mikemag/MonkeyWiki/assets/images/Shaper_Test_1.jpg

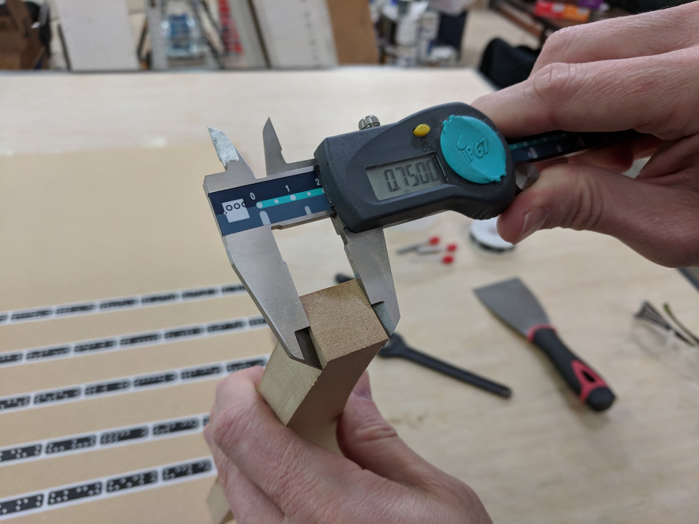
assets/images/Shaper_Test_1.jpg
