mikemag/MonkeyWiki/assets/images/Bandsaw_Setup1.JPG

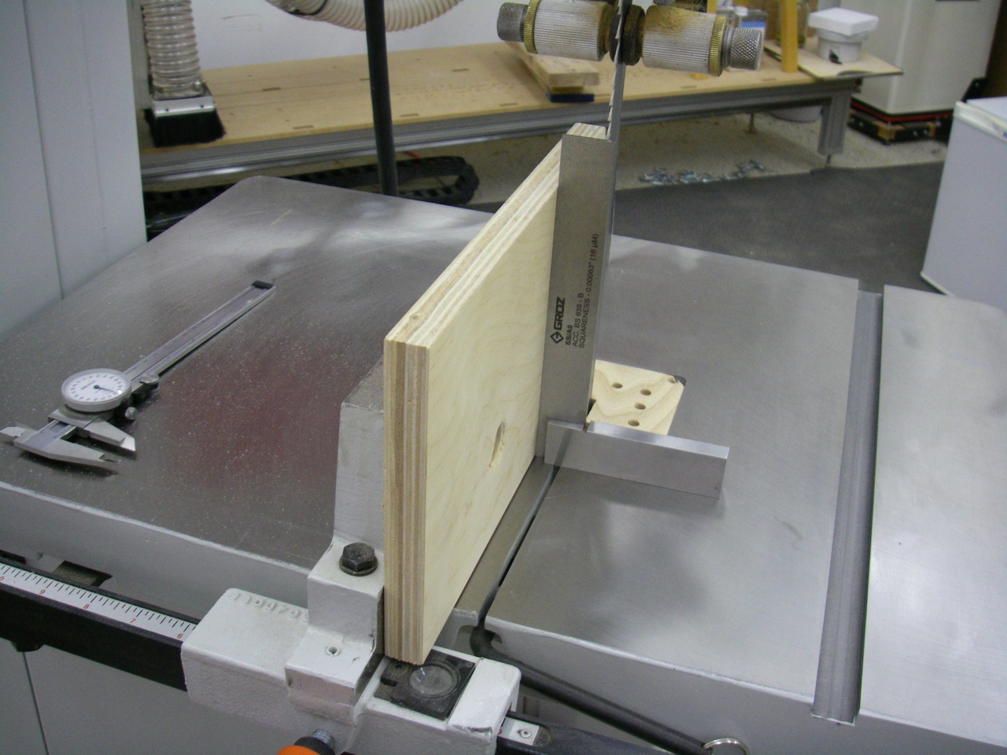
assets/images/Bandsaw_Setup1.JPG
