mikemag/MonkeyWiki/content/zh-cn/MonkeyWiki/Construction/Core_blank_construction/Core_blank_overview.md

---
dateFromWiki: "2019-05-04T15:58:57Z"
title: "芯坯概述"
aliases:
- /MonkeyWiki/Core_blank_overview/zh-cn
translatedDate: "2019-05-04T15:58:57Z"
translator: "X z"
translatorPage: "/zh-cn/MonkeyWiki/X_z"
weight: 1
---
滑雪板芯通常由垂直层压的约2cm宽的木条组成。板芯由“空白板”加工而成，它通常是矩形的，比最终板芯更长，更宽，更厚。

制作空白板是一个相当经典的木工加工，你应该这样做。如果你不熟悉木工，我已经收集了大量的[木工资源]({{< ref "MonkeyWiki/Resources/Woodworking_Resources.md" >}})来帮助你入门。 

## 概述

对于滑雪板板芯，我制造的空白板大约13.5英寸(约34cm)宽，0.4英寸(约1cm)厚，大约6-7英尺(约1.8-2.2m)长。每个空白板有18条长方向的杨木条。空白板用聚氨酯胶粘合在一起。

这个过程开始于杨木板，它长7英尺(213cm)，宽2.5英寸(6.35cm)，厚约3/4英寸(1.9cm)。这些板中的9块被粘合成7英尺长，2.5英寸宽和6.75英寸(约17cm)厚的芯坯。将该芯坯切成4个厚度为7英尺，宽6.75英寸，厚约1/2英寸(1.27cm)的切片。然后将两个切片粘接在一起，制成长7英寸，宽13.5英寸，厚0.4-0.5英寸的空白板。 

所以,9块杨木板 &rArr;1大块芯坯 &rArr; 4块横切片 &rArr; 2块空白板。我将使用术语杨木板，芯坯，切片和空白板来指代下面的各个构造阶段。

我通常尝试一次制作大约十块空白板，所以我从至少需要45块杨木板。（我通常会准备接近50块，因为有时在商店看起来像一块好的板在你的店里看起来不太好！）我发现一次制作许多空白板比一次制作一块更加容易。空白板非常稳定，可以在架子上放置很长时间而不会翘曲或开裂。

## 参阅

- [木材选择，干燥和准备]({{< ref "MonkeyWiki/Materials/Wood_selection__drying__and_prep.md" >}})
- [制作芯坯]({{< ref "MonkeyWiki/Construction/Core_blank_construction/Building_a_stack.md" >}})
- [切割芯坯]({{< ref "MonkeyWiki/Construction/Core_blank_construction/Slicing_a_stack.md" >}})
- [拼接另外一半空白板芯]({{< ref "MonkeyWiki/Construction/Core_blank_construction/Joining_the_halves_of_a_core_blank.md" >}})

## 待办事项

- 绘制从杨木板到空白板的进展。曾经在原有的HMS网站上有一个...可能重新做一下，让它看起来不那么丑。
- 每个阶段的图片，每个阶段只有一张。
