mikemag/MonkeyWiki/content/zh-cn/MonkeyWiki/Construction/Finishing/Overview_of_cleanup_and_finishing.md

---
dateFromWiki: "2019-04-11T05:45:21Z"
title: "清理和精加工概述"
gallery: true
aliases:
- /MonkeyWiki/Overview_of_cleanup_and_finishing/zh-cn
translatedDate: "2019-04-11T05:45:21Z"
translator: "X z"
translatorPage: "/zh-cn/MonkeyWiki/X_z"
weight: 1
---
{{< img src="images/Board_Trimmed.JPG" caption="_滑雪板边缘修剪和清理_" >}}在滑雪板退出压力机之后，我们仍然需要做很多清理工作才能真正看起来像滑雪板。

## 修剪边角料

第一步是修剪边角料，这是滑雪板边缘以外的多余材料。这包括额外的玻璃纤维，固化的环氧树脂，橡胶，顶片，板头/板尾垫片和边墙材料。我首先使用带锯从滑雪板的有效边刃移除边角料。这也可以通过允许带锯刀片压靠金属滑雪板边缘来轻松完成。也可以使用带锯从板头和板尾移除边角料，但我选择使用带有研磨钻头的曲线锯修剪这部分。对我来说，更容易将滑雪板稳定地放在工作台上并小心地围绕更紧密的板头和板尾半径引导曲线锯，而不是将整个滑雪板围绕带锯刀片摆动。 

@TODO: 获取我使用的刀片信息。

{{< gallery  caption="边角料清理" >}}
{{< gallery-item src="images/FlashCleanup1.JPG" caption="Remains of the nose and tail flash." >}}
{{< gallery-item src="images/FlashCleanup2.JPG" caption="Remains of the flash from along the edge of a snowboard." >}}
{{< /gallery >}}

## 清理边刃

现在层压板开始看起来更像滑雪板，但边缘仍然非常粗糙。两种工具都会留有粗糙的边缘，并且在某些地方仍然会有一层薄薄的多余材料，通常是PTEX边墙或板头/板尾垫片。沿着板的整个周边使用具有60目砂磨盘的4英寸角磨机。将多余的材料小心地磨掉，并将边缘全部暴露出来。然后我切换到120目砂磨盘并完全清理板尾和板尾。这将是滑雪板这部分的最终处理。这是一个非常微妙的过程。使用角磨机和60目或120目砂磨盘可以在极短的时间内对板边缘造成大量损坏！

使用角磨机进行打磨时，不要使边缘过热至关重要。我在这部分完成之前，不断移动到另一个区域。我像往常一样用干净的水喷洒，并用手检查边缘的温度。如果你不能把手放在边缘，那就太烫了。

{{< gallery  caption="边刃清理" >}}
{{< gallery-item src="images/EdgeCleanup1.JPG" caption="The table where I cleanup the board. Snowboard vises are used to hold the board up on edge for grinding." >}}
{{< gallery-item src="images/EdgeCleanup2.JPG" caption="Laminate trimmer and angle grinder with various flap sanding discs." >}}
{{< /gallery >}}

## 板底打磨

{{< img src="images/BaseGrinder.JPG" caption="_板底磨床_" >}}接下来，滑雪板获得了第一次打磨。我从一个粗糙的80目砂带开始，快速去除多余的环氧树脂和一层薄薄的基材，然后切换到120目砂带进行最后的打磨。虽然80目砂带仍然存在，但我清理了保持板垂直于板底打磨机的有效边缘。这确保了边缘的整个长度是平滑的，甚至是板的长度。

## 斜切边墙

接下来，将板返回到施加边墙斜面的工作台上。带有倾斜底座的修边机用于沿有效边缘的长度运行齐平修剪router刨机钻头。这使得边墙成为完美的10度斜面，并且是边墙上所需的最后一点清理。如果你没有带倾斜底座的修边机，你可以用木头制作楔子并将其连接到修边机底座上以形成正确的角度。

这里的关键是缓慢移动并确保修边机的底部保持平放在板的底部。在每个端部轻松进出切口，并将可能留下的任何尖锐过渡与砂磨块混合。

{{< gallery  caption="边墙清理" >}}
{{< gallery-item src="images/Trimmer1.jpg" caption="Laminate trimmer with a tilt base." >}}
{{< gallery-item src="images/Trimmer2.jpg" caption="Straight cutter with bearing on top." >}}
{{< gallery-item src="images/Trimmer3.jpg" caption="Example of how to apply the trimmer to cleaning up sidewalls. The edge should be completely exposed and smooth. The bearing rests on the edge, and the cutter starts about a half millimeter past the edge. The board is upside down and the trimmer rests on the base." >}}
{{< /gallery >}}

## 开孔

最后，固定器螺孔会被钻出。我通过使用两个小磁铁找到嵌件，这两个小磁铁将粘在两个3/16英寸钢球轴承上，这些轴承在准备铺设时放入导向嵌件中。导向嵌件沿着板的长度居中，距离第一组嵌件4cm。使用指南我可以快速标记嵌件位于滑雪板表面下方的位置，然后分两步钻出。第一步是使用1/8英寸钻头打开孔位，然后使用45度沉头钻露出整个螺孔并留下一个漂亮的斜面。沉头钻将在螺孔中自动居中。使钻头垂直于板，以确保圆孔均匀。使用M6螺孔清洁螺纹，并通过手动将固定器螺丝向下钻入每个螺孔进行检查。如果螺丝不能轻易地一直钻到底部，则再次使用龙头直到它完成。
 
使用一对小镊子去除在钻孔和反沉没过程中被推下的聚酯薄膜嵌件帽。在攻丝之前和拧紧螺钉之前，用压缩空气清除螺孔。
 
使用M6水龙头轻松一下。你不希望跨越它并破坏插入中的线程。你也不想把它跑得太远并推出插入物的底部，这会在滑雪板的底部留下一个凹坑。大多数水龙头都有一个点。最好将其研磨成平底，如下图所示。

{{< gallery  caption="螺孔清理" >}}
{{< gallery-item src="images/CleanupInserts1.JPG" caption="Insert finding guide, aligned with magnets." >}}
{{< gallery-item src="images/CleanupInserts2.JPG" caption="Insert finding guide, aligned with magnets." >}}
{{< gallery-item src="images/CleanupInserts3.JPG" caption="Insert finding guide, aligned with magnets." >}}
{{< gallery-item src="images/CleanupInserts4.JPG" caption="Inserts drilled with a small drill bit." >}}
{{< gallery-item src="images/CleanupInserts5.JPG" caption="Inserts exposed with the counter sink." >}}
{{< gallery-item src="images/CleanupInserts6.JPG" caption="Here you can see bits of epoxy and glass forced down into the inserts after drilling with the counter sink." >}}
{{< gallery-item src="images/CleanupInserts7.JPG" caption="Cleaning up the threads of the inserts with a M6 tap." >}}
{{< gallery-item src="images/CleanupInserts8.JPG" caption="Testing the insert threads with a binding screw." >}}
{{< /gallery >}}
