mikemag/MonkeyWiki/content/zh-cn/MonkeyWiki/Equipment/Snowboard-specific_tools/Base_grinder.md

---
dateFromWiki: "2019-04-04T08:56:10Z"
title: "板底磨床"
gallery: true
aliases:
- /MonkeyWiki/Base_grinder/zh-cn
translatedDate: "2019-04-04T08:56:10Z"
translator: "X z"
translatorPage: "/zh-cn/MonkeyWiki/X_z"
---
{{< img src="images/Grinder10.JPG" caption="_Fontaine 1404 Base Grinder._" >}}我使用Fontaine 1404板底磨床，由Wintersteiger出售，型号为SNB 55。它使用14“x 59”(35.56cm x 149.86cm)的皮带。电机是一个4马力的Leeson，它有一个带有可调式喷雾器的小型240v水泵。它就像任何普通的带式砂光机一样，带有驱动轮和从动件，以及用于调节跟踪的旋钮。驱动轮是一种坚硬的橡胶，它会变形一点，很适合用不完美的底座完成底板。在中心附近有一个压板（在这台机器上是可选的），这种压板非常平坦，可以使基座真实。在集水盆和皮带之间有一个布料过滤器，用于将金属和基材保持在泵外。

没有自动进给，虽然机器设计为添加了一个。

没有库存边缘指南，但是一个伙伴和我用一些废铝建造了一个快速贫民窟。这很难看，但它允许我在一个可调节的位置垂直于皮带保持板边缘，所以我不会在早期的皮带上磨损一条线。 

## 耗材

我在这里得到了所有的磨床用品[SVST](http://www.svst.com).甚至还有Fontaine更换零件以适合我的机器。 

我通常使用氧化铝或锆石带。我使用80目从底部去除多余的环氧树脂，并快速通过边墙。然后，我用120目完成。我保留了一些旧皮带作为最后的整理通行证，因为它们不那么尖锐，往往会留下更好的表面。

## 冷却液

我在水中使用“研磨冷却剂”，有时称为“切削液”或“乳液”。我使用的品牌是SVST的Kool Kut Ski Grinding Coolant，它不仅可以帮助皮带切割更好，还可以防止机器生锈。这就是让水看起来像防冻剂的原因，但不要搞错：它不是防冻剂。研磨冷却剂几乎无毒，这非常重要，因为无论如何，当你研磨板时，你最终都会被细雾覆盖。我使用的冷却剂似乎对我个人没有任何影响，但是...我只是用一些护目镜将它从我的眼睛中取出，然后洗掉。 它似乎对我的草坪没有影响。 它上面的MSDS是非常无害的，表明有轻微的刺激性和更多。

冷却剂被保持在一个简单的塑料箱中，盖子被切开，以便为电源和泵的供应管路留出空间。这让我可以混合一些冷却剂，并在研磨之间保持几周无尘。 

我确实发现，如果放置冷却剂，如果放置时间超过几个月就会变成霉菌，所以我尽量不在机器中留下冷却液，除非我相信我会在几周内磨一块板。 

## 清理

使用后清理板底研磨机非常重要。你不希望机器在基材绒毛和边缘锉中结块，因为它会促使机器生锈。这就是标准花园软管喷嘴的用途：你可以彻底地将内部软管从内部软管，然后使用一些商店毛巾将其中的大部分干燥。

## 电气

该机器在240V时吸收约21个起动放大器，因此我将它安装在30A断路器上。应该有一个接触器或继电器开关来打开和关闭连接到设备，但它很久以前就爆炸了。我一直把它连接起来，我用断路器作为开关。这就是为什么你在电机顶部看到一个带有磁带而不是开关的小盒子。有一天，当它真的开始烦我时，我会绕过去实际修复它。 

{{< gallery  caption="Fontaine 1404 Base Grinder" >}}
{{< gallery-item src="images/Grinder1.JPG" caption="Electrical plate on the motor of the Fontaine 1404 base grinder." >}}
{{< gallery-item src="images/Grinder2.JPG" caption="Motor on the base grinder." >}}
{{< gallery-item src="images/Grinder3.JPG" caption="Base grinder from the back side. Belts are kept in the base." >}}
{{< gallery-item src="images/Grinder4.JPG" caption="Tracking adjustment on the base grinder, back side." >}}
{{< gallery-item src="images/Grinder5.JPG" caption="Nameplate and serial number on the base grinder." >}}
{{< gallery-item src="images/Grinder6.JPG" caption="Base grinder, front view with doors open." >}}
{{< gallery-item src="images/Grinder7.JPG" caption="Base grinder, front view with doors open, closer look at the mechanism." >}}
{{< gallery-item src="images/Grinder8.JPG" caption="Spray head, inside the grinder on the lower left side (when looking from the front.) Sprays upwards to coat the belt." >}}
{{< gallery-item src="images/Grinder9.JPG" caption="Base grinder, doors open, belt on and tensioned." >}}
{{< gallery-item src="images/Grinder10.JPG" caption="Fontaine 1404 base grinder. Front view, doors closed, belt on and tensioned." >}}
{{< gallery-item src="images/Grinder11.JPG" caption="Ghetto edge guide, retracted position." >}}
{{< gallery-item src="images/Grinder12.JPG" caption="Ghetto edge guide, extended position." >}}
{{< gallery-item src="images/Grinder13.JPG" caption="Coolant tank, empty, showing pump and filter." >}}
{{< gallery-item src="images/BaseGrinder.JPG" caption="Base grinder with various belts." >}}
{{< /gallery >}}
