mikemag/MonkeyWiki/notes.md

# Random Notes

## Update the site:
```
rsync -e "/usr/bin/ssh" --bwlimit=2000 -av public/ uuu@hhh.dreamhost.com:/home/uuu/happymonkeysnowboards.com/
```

## .htaccess

* Pure gold: https://htaccess.madewithlove.com/
* Docs and flags: https://httpd.apache.org/docs/current/mod/mod_rewrite.html

## Hugo

* https://gohugo.io/documentation/
* https://github.com/alex-shpak/hugo-book
