mikemag/MonkeyWiki/content/en/MonkeyWiki/_index.md

---
gallery: true
bookCollapseSection: false
aliases:
- /MonkeyWiki/Main_Page
- /MonkeyWiki/Main_Page/en
description: "How I built snowboards at Happy Monkey Snowboards. Construction techniques, equipment, materials, etc."
title: Monkey Wiki
---
{{< img src="images/Board_2018.jpg" width=300px caption="_Completed board from Winter 2018. Wood veneer topsheet with highly figured Bubinga, English Sycamore, and Ebony. 164cm._" >}} 
This site provides information on exactly how I built snowboards so that others may learn from it. 
The information here is based on my experience building boards as owner of Happy Monkey Snowboards, Inc., from 2003-2010 as well as 
my continued personal building through 2018.

This will not be a comprehensive treatment of all the different ways to do this, but rather just the ways that I have 
personally done it which worked well for me. For alternatives see [SkiBuilders.com](http://www.skibuilders.com), where they have collected 
detailed how-to’s on how they and others build skis and snowboards, and host a great forum with even more information on alternatives.

Enjoy,

[Mike Magruder (a.k.a Head Monkey)]({{< ref "MonkeyWiki/Head_Monkey.md" >}})

## Donate

You can help offset the server costs for running MonkeyWiki with a small donation. 



## Contents 
- [Construction Overview]({{< ref "MonkeyWiki/Construction" >}})
- [Equipment Overview]({{< ref "MonkeyWiki/Equipment" >}})
- [Materials Overview]({{< ref "MonkeyWiki/Materials" >}})
- [Resources Overview]({{< ref "MonkeyWiki/Resources" >}})
- [About]({{< ref "MonkeyWiki/About.md" >}})

## What about skis? 
I've built one pair of skis, and they turned out great. You’ll find that ski and snowboard construction are *amazingly* similar. 
You can use everything here to build either, even though it all refers to snowboards. It’s okay :)

## Status 
There are a few placeholders where I've left just raw notes, but otherwise the articles that are here now are technically 
correct and up-to-date.
