mikemag/MonkeyWiki/content/en/MonkeyWiki/Equipment/_index.md

---
title: "Equipment"
aliases:
- /MonkeyWiki/Equipment_Overview
- /MonkeyWiki/Equipment_Overview/en
weight: 2
bookCollapseSection: true
---
The following articles cover the equipment needed to build a snowboard. Some of these can be bought from your average 
hardware store, and some have to be built by you. Some are absolutely required, while others (like a CNC machine) are 
pretty optional. Which ones you really need will depend on the way you chose to build boards and the raw materials you 
can get. For instance, if you buy core blanks from someone then you might not really need most of the larger woodworking 
tools. If you’re willing to bend the edges completely by hand then you won’t need a specialized edge bender, etc.

*Note: this isn't a complete list of tools, just the ones I've taken some time to write about here.*

- CNC
  - [CNC Router]({{< ref "MonkeyWiki/Equipment/CNC/CNC_Router.md" >}})
  - [Do you need a CNC machine?]({{< ref "MonkeyWiki/Equipment/CNC/Do_you_need_a_CNC_machine_.md" >}})
  - [CNC machines: build or buy?]({{< ref "MonkeyWiki/Equipment/CNC/CNC_machines__build_or_buy_.md" >}})
  - [Shaper Origin]({{< ref "MonkeyWiki/Equipment/CNC/Shaper_Origin.md" >}})
  - CAD/CAM Software
    - [Fusion 360]({{< ref "MonkeyWiki/Equipment/CNC/CAD_CAM_Software/Fusion_360.md" >}})
    - [MonkeyCAM]({{< ref "MonkeyWiki/Equipment/CNC/CAD_CAM_Software/MonkeyCAM.md" >}})
    - [snoCAD-X]({{< ref "MonkeyWiki/Equipment/CNC/CAD_CAM_Software/SnoCAD-X.md" >}})
- Snowboard press
  - [Monkey Press Construction]({{< ref "MonkeyWiki/Equipment/Snowboard_press/Monkey_Press_Construction.md" >}})
  - [Press heat control and thermocouples]({{< ref "MonkeyWiki/Equipment/Snowboard_press/Press_heat_control_and_thermocouples.md" >}})
  - [Molds and cassettes]({{< ref "MonkeyWiki/Equipment/Snowboard_press/Molds_and_cassettes.md" >}})
- Snowboard-specific tools
  - [Deflection Testing Jig]({{< ref "MonkeyWiki/Equipment/Snowboard-specific_tools/Deflection_Testing_Jig.md" >}})
  - [Edge Benders]({{< ref "MonkeyWiki/Equipment/Snowboard-specific_tools/Edge_Benders.md" >}})
  - [Base grinder]({{< ref "MonkeyWiki/Equipment/Snowboard-specific_tools/Base_grinder.md" >}})
- Small tools
  - [Air Shears]({{< ref "MonkeyWiki/Equipment/Small_tools/Air_Shears.md" >}})
  - [Feather Board]({{< ref "MonkeyWiki/Equipment/Small_tools/Feather_Board.md" >}})
  - [Four-way Clamps]({{< ref "MonkeyWiki/Equipment/Small_tools/Four-way_Clamps.md" >}})
  - [Hand Scraper]({{< ref "MonkeyWiki/Equipment/Small_tools/Hand_Scraper.md" >}})
  - [Pipe Clamps]({{< ref "MonkeyWiki/Equipment/Small_tools/Pipe_Clamps.md" >}})
  - [Routers and laminate trimmers]({{< ref "MonkeyWiki/Equipment/Small_tools/Routers_and_laminate_trimmers.md" >}})
  - [Router Bits]({{< ref "MonkeyWiki/Equipment/Small_tools/Router_Bits.md" >}})
- Larger tools
  - [HVLP Sprayer]({{< ref "MonkeyWiki/Equipment/Larger_tools/HVLP_Sprayer.md" >}})
