mikemag/MonkeyWiki/content/en/MonkeyWiki/Equipment/CNC/CNC_Router.md

---
dateFromWiki: "2019-02-03T02:37:15Z"
title: "CNC Router"
gallery: true
aliases:
- /MonkeyWiki/CNC_Router
- /MonkeyWiki/CNC_Router/en
weight: 1
---
In 2003, I built a CNC router to allow me to accurately cut snowboard cores, bases, and mold parts. The cutting area is 2′ x 7’1″, with 5″ of travel in the Z axis (you end up with less due to the length of the cutter, though.) The frame is made of structural aluminum. Each axis moves on steel linear slides, and the plates that make up the mount for the Z axis are 3/4″ aluminum. There are 3 stepper motors powered and controlled by a controller in the grey box above the machine.
 
The controller receives the program, or manual commands, from a small dedicated computer on a shelf nearby. The machine is programmed with industry standard “G-codes." These are generated from either a commercial CAD/CAM system, or from my own snowboard-specific CAM system called MonkeyCAM.
 
I had originally hoped it might be suitable for cutting aluminum as well, but it’s really only good for wood and plastics, which is just fine since I primarily use it for snowboard construction and other random woodworking projects.

{{< gallery  caption="Happy Monkey CNC Machine" >}}
{{< gallery-item src="images/CNC1.JPG" caption="Overview of the CNC machine. The cutting area is 85\" x 24\" x 5\"." >}}
{{< gallery-item src="images/CNC2.JPG" caption="Head and gantry of the CNC machine with snowboard press in the background." >}}
{{< gallery-item src="images/CNC_Head1.jpg" caption="Porter Cable router in a CNC machine." >}}
{{< gallery-item src="images/CNC3.JPG" caption="Head of the CNC machine from behind." >}}
{{< gallery-item src="images/CNC4.JPG" caption="Back of the CNC head showing Y and Z axis mechanisms." >}}
{{< gallery-item src="images/CNC5.JPG" caption="Better shot of the Y axis motor, gears, and rack." >}}
{{< gallery-item src="images/CNC6.JPG" caption="Control box for the CNC machine." >}}
{{< gallery-item src="images/CNC7.JPG" caption="Inside the control box for the CNC machine." >}}
{{< /gallery >}}

## CNC Resources 
- [Machine Tool Camp](http://machinetoolcamp.com/) – I started with plans for a 4’x8’ machine from here and modified them to build my machine.
- [CNC Zone](http://www.cnczone.com/) – The single best forum for home-built CNC machines.
