mikemag/MonkeyWiki/content/zh-cn/MonkeyWiki/Equipment/CNC/CNC_Router.md

---
dateFromWiki: "2019-04-03T13:18:43Z"
title: "CNC 雕刻机"
gallery: true
aliases:
- /MonkeyWiki/CNC_Router/zh-cn
translatedDate: "2019-04-03T13:18:43Z"
translator: "X z"
translatorPage: "/zh-cn/MonkeyWiki/X_z"
weight: 1
---
在2003年，我建造了一台CNC雕刻机，可以准确地切割滑雪板芯，底板和模具零件。切割区域为2英尺x 7英尺1英寸，在Z轴上行程为5英寸（尽管由于切割器的长度，最终会减少。）框架由结构铝制成。每个轴在钢制线性滑块上移动，构成Z轴安装的板为3/4“铝。3个步进电机是由机器上方的灰色控制箱中的控制器供电和控制。

控制器从附近架子上的小型专用计算机接收程序或手动命令。该机器采用行业标准“G-code”编程。这些是从商业CAD/CAM系统或我自己的滑雪板专用CAM系统MonkeyCAM生成的。
 
我原本希望它也适合切割铝，但它实际上只适用于木材和塑料，这很好，因为我主要用它来滑雪板制造和其他随机木工项目。

{{< gallery  caption="Happy Monkey CNC机器" >}}
{{< gallery-item src="images/CNC1.JPG" caption="Overview of the CNC machine. The cutting area is 85\" x 24\" x 5\"." >}}
{{< gallery-item src="images/CNC2.JPG" caption="Head and gantry of the CNC machine with snowboard press in the background." >}}
{{< gallery-item src="images/CNC_Head1.jpg" caption="Porter Cable router in a CNC machine." >}}
{{< gallery-item src="images/CNC3.JPG" caption="Head of the CNC machine from behind." >}}
{{< gallery-item src="images/CNC4.JPG" caption="Back of the CNC head showing Y and Z axis mechanisms." >}}
{{< gallery-item src="images/CNC5.JPG" caption="Better shot of the Y axis motor, gears, and rack." >}}
{{< gallery-item src="images/CNC6.JPG" caption="Control box for the CNC machine." >}}
{{< gallery-item src="images/CNC7.JPG" caption="Inside the control box for the CNC machine." >}}
{{< /gallery >}}

## CNC 资源

- [Machine Tool Camp](http://machinetoolcamp.com/) – 我从这里开始计划4英尺x8英尺机器并修改它们以构建我的机器。
- [CNC Zone](http://www.cnczone.com/) – 自制数控机床的最佳论坛。
