mikemag/MonkeyWiki/content/zh-cn/MonkeyWiki/Equipment/Small_tools/Feather_Board.md

---
dateFromWiki: "2019-04-04T01:54:05Z"
title: "羽毛板"
gallery: true
aliases:
- /MonkeyWiki/Feather_Board/zh-cn
translatedDate: "2019-04-04T01:54:05Z"
translator: "X z"
translatorPage: "/zh-cn/MonkeyWiki/X_z"
---
{{< img src="images/Fingers.JPG" caption="_在带锯上的羽毛板_" >}}羽毛板是一种用于帮助抵抗带锯或台锯导轨的工具。它们可以进行调整，以便在通过锯片时，板必须将挡板的两端推开，从而对挡板施加一点压力。

使用购买的硬件（旋钮和插槽插件）可以将羽毛板制作成你需要的任何尺寸或形状，或者你可以在当地的木工车间预先制作羽毛板。
