mikemag/MonkeyWiki/content/zh-cn/MonkeyWiki/Equipment/Small_tools/Four-way_Clamps.md

---
dateFromWiki: "2019-04-02T15:20:16Z"
title: "四向夹具"
gallery: true
aliases:
- /MonkeyWiki/Four-way_Clamps/zh-cn
translatedDate: "2019-04-02T15:20:16Z"
translator: "X z"
translatorPage: "/zh-cn/MonkeyWiki/X_z"
---
通过使用像这里图中所示的简单“四向”夹具，可以更容易地夹紧一半的芯坯或类似物。我使用[WoodRiver夹紧系统](http://www.woodcraft.com/Product/2000321/1858/WoodRiver-Clamping-System.aspx)，可以从亚马逊或[WoodCraft](http://www.woodcraft.com/)等地方购买。你需要六到七个来夹住一个板芯，所以寻找他们的销售。

由于你提供了夹具的木材部分，因此可以使这些夹具适合你想要粘合的任何尺寸的面板。然而，夹子不会完全闭合，并且它们通常不会闭合得足够远以接触相当薄的普通芯坯的表面。你可能需要使用垫片来弥补额外的厚度。我用几块四分之一英寸的硬纸板和打包带来防止胶水粘在它们上面。

这些最大开口宽度为27英寸，最小开口宽度为8 3/4英寸。 当然，这可以用不同长度的卡尔改变。
{{< gallery  caption="4-Way Clamps" >}}
{{< gallery-item src="images/FourWayClamp1.JPG" caption="" >}}
{{< gallery-item src="images/FourWayClamp2.JPG" caption="" >}}
{{< gallery-item src="images/FourWayClamp3.JPG" caption="" >}}
{{< gallery-item src="images/FourWayClamp4.JPG" caption="" >}}
{{< gallery-item src="images/FourWayClamp5.JPG" caption="" >}}
{{< gallery-item src="images/FourWayClamp6.JPG" caption="" >}}
{{< gallery-item src="images/FourWayClamp7.JPG" caption="" >}}
{{< gallery-item src="images/CoreBlank_SliceJoin1.JPG" caption="Halves of a core blank coming together." >}}
{{< gallery-item src="images/CoreBlank_SliceJoin2.JPG" caption="Joining halves of a core blank. You can clearly see the glue squeezeout and the spacers for the clamps." >}}
{{< gallery-item src="images/CoreBlank_Sidewall4.JPG" caption="The blank, with ash and PTEX in place, back in the clamps for the night." >}}
{{< /gallery >}}

==另见==

- [拼接另外一半空白板芯]({{< ref "MonkeyWiki/Construction/Core_blank_construction/Joining_the_halves_of_a_core_blank.md" >}})
- [白蜡木桁条和边墙]({{< ref "MonkeyWiki/Construction/Core_construction/Ash_edge_stringer_and_sidewalls.md" >}})
