mikemag/MonkeyWiki/content/zh-cn/MonkeyWiki/Equipment/Small_tools/Pipe_Clamps.md

---
dateFromWiki: "2020-04-28T09:20:45Z"
title: "水管夹"
gallery: true
aliases:
- /MonkeyWiki/Pipe_Clamps/zh-cn
translatedDate: "2020-04-28T09:20:45Z"
translator: "X z"
translatorPage: "/zh-cn/MonkeyWiki/X_z"
---
管夹可用于制造芯坯。它们在长距离上施加合理的力，并且可以通过使用不同的管道将它们制成任何长度。根据同一管道上的不同夹紧宽度，可轻松调节端部。我在夹子的两侧增加了2” x 2” x 12” 橡木套管，以便在更大的区域内分配夹紧力。

我使用的夹子来自Woodcraft，但你几乎可以在任何地方找到它们。在Home Depot或Lowes购买管夹：[Pipe Clamps](http://www.woodcraft.com/Product/2005440/16062/Jorgensen-Pony-Pipe-Clamp-34.aspx)

{{< gallery  caption="管夹" >}}
{{< gallery-item src="images/PipeClamp1.JPG" caption="Pipe clamps." >}}
{{< gallery-item src="images/PipeClamp2.JPG" caption="Pipe clamps." >}}
{{< gallery-item src="images/PipeClamp3.JPG" caption="Pipe clamps." >}}
{{< /gallery >}}
