mikemag/MonkeyWiki/content/zh-cn/MonkeyWiki/Equipment/Small_tools/Router_Bits.md

---
dateFromWiki: "2020-01-30T13:19:27Z"
title: "雕刻机刀具"
gallery: true
aliases:
- /MonkeyWiki/Router_Bits/zh-cn
translatedDate: "2020-01-30T13:19:27Z"
translator: "X z"
translatorPage: "/zh-cn/MonkeyWiki/X_z"
---
{{< img src="images/RouterBits1.JPG" caption="_雕刻机刀具._" >}}{{< img src="images/RouterBits2.JPG" >}}我非常喜欢来自[Amana Tool](http://amanatool.com/)的刀具。一个高质量的刀具确实有很大的不同。这些都很好地平衡了，使工具更安静，并产生了更平滑的切割。

对于切削中密度纤维板模具和大多数切削要求1/4英寸钻头的切削的板芯，我们使用双刃螺旋上切硬质合金钻头，**＃46102**，运行速度为23,000rpm。

对于板芯轮廓，我使用1.5英寸双刃直刀，**＃45452**，运行速度为18,000rpm。

为了放置对准标记，我使用1/4英寸V型刀，**＃45704**，运行速度为23,000rpm。

对于切割底板和板头/板尾垫片，我使用1/4英寸双刃直刀，**＃45208**，运行速度为23,000rpm。

对于边墙轮廓，我使用1/4英寸双槽直头，顶部轴承在修边机中以30,000rpm运行。这不是一个Amana刀具......它是一个质量差的Home Depot刀具，当它磨损时将被一个好的Amana刀具取代（从它的外观看，它随时都会是）
