mikemag/MonkeyWiki/content/zh-cn/MonkeyWiki/Equipment/Small_tools/Routers_and_laminate_trimmers.md

---
dateFromWiki: "2019-04-04T07:06:25Z"
title: "雕刻机主轴和修边机"
gallery: true
aliases:
- /MonkeyWiki/Routers_and_laminate_trimmers/zh-cn
translatedDate: "2019-04-04T07:06:25Z"
translator: "X z"
translatorPage: "/zh-cn/MonkeyWiki/X_z"
---
{{< img src="images/CNC_Head1.jpg" caption="_Porter Cable router as head of CNC machine._" >}}
{{< img src="images/Trimmer1.jpg" caption="_带倾斜底座的修边机_" >}}
板芯构建的大部分涉及可靠的雕刻机。我在CNC机器上使用的主轴是[Porter Cable](http://www.portercable.com/)型号890 2 1/4hp雕刻机主轴。零件号是8902.它是一个坚固的雕刻机主轴，也非常适用。

对于修剪边墙，我使用Porter Cable Model 7301修边机和7318型瓷砖修边机底座。倾斜底座非常适合修剪边墙。我更喜欢修边机用于边墙工作，或者我需要修剪某些东西以匹配模板，因为它适合手掌并且比较大的雕刻机主轴更容易控制。
