mikemag/MonkeyWiki/content/en/MonkeyWiki/Equipment/Larger_tools/HVLP_Sprayer.md

---
dateFromWiki: "2019-03-31T17:57:01Z"
title: "HVLP Sprayer"
gallery: true
aliases:
- /MonkeyWiki/HVLP_Sprayer
- /MonkeyWiki/HVLP_Sprayer/en
---
A HVLP (High Volume Low Pressure) spray system is great for spraying a variety of finishes. For snowboards, I use a Fuji Q3 Pro HVLP sprayer, shooting System Three WR-LPU Polyurethane Topcoat, in clear satin, cut 20-25% w/ water. This applies a smooth, even coat of finish to the board with minimal mess and cleanup. The gun is easy to use and get familiar with, and the spray pattern is easily adjustable. 

See [Finishing a wood veneer top sheet]({{< ref "MonkeyWiki/Construction/Finishing/Finishing_a_wood_veneer_top_sheet.md" >}}) for more details about the veneer finishing process.

{{< gallery  caption="HVLP Sprayer" >}}
{{< gallery-item src="images/Veneer_Finishing_2_5.jpg" caption="HVLP unit" >}}
{{< gallery-item src="images/Veneer_Finishing_2_6.jpg" caption="HVLP spray gun" >}}
{{< gallery-item src="images/Veneer_Finishing_2_7.jpg" caption="HVLP spray gun tip" >}}
{{< gallery-item src="images/Veneer_Finishing11.JPG" caption="The finish and spray gun." >}}
{{< /gallery >}}
