mikemag/MonkeyWiki/content/en/MonkeyWiki/Equipment/Small_tools/Air_Shears.md

---
dateFromWiki: "2019-03-31T18:50:28Z"
title: "Air Shears"
gallery: true
aliases:
- /MonkeyWiki/Air_Shears
- /MonkeyWiki/Air_Shears/en
---
Inline Air Shears are great for cutting aluminum mold skins. I use a cheap one I got from from Harbor Freight that works well enough. They're loud, and finicky, but with a little practice you can cut sheet metal easily.

{{< gallery  caption="Air Shears" >}}
{{< gallery-item src="images/Air_Shears_1.jpg" caption="" >}}
{{< gallery-item src="images/Air_Shears_2.jpg" caption="" >}}
{{< gallery-item src="images/Air_Shears_3.jpg" caption="" >}}
{{< /gallery >}}
