mikemag/MonkeyWiki/content/en/MonkeyWiki/Equipment/Small_tools/Four-way_Clamps.md

---
dateFromWiki: "2019-02-03T02:39:16Z"
title: "Four-way Clamps"
gallery: true
aliases:
- /MonkeyWiki/Four-way_Clamps
- /MonkeyWiki/Four-way_Clamps/en
---
Clamping halves of a core blank, or anything similar, is made much easier by using a simple “4-way” clamp like the ones pictured here. I use the [WoodRiver Clamping System](http://www.woodcraft.com/Product/2000321/1858/WoodRiver-Clamping-System.aspx) which can be bought from Amazon or places like [WoodCraft](http://www.woodcraft.com/). You’ll need six or seven of them to clamp up a core, so look for them to go on sale.

These clamps can be made to fit any size panel you wish to glue up since you provide the wood portion of the clamp. The clamps won’t close all the way, though, and they often wont close far enough to make contact with the face of a normal core blank, which is fairly thin. You likely need to use spacers to make up the extra thickness. I use a few pieces of one-quarter inch hardboard with packing tape to prevent the glue from sticking to them.

The maximum opening width on these is 27", and the minimum is 8 3/4". This can be changed, of course, with different length cauls.
{{< gallery  caption="4-Way Clamps" >}}
{{< gallery-item src="images/FourWayClamp1.JPG" caption="" >}}
{{< gallery-item src="images/FourWayClamp2.JPG" caption="" >}}
{{< gallery-item src="images/FourWayClamp3.JPG" caption="" >}}
{{< gallery-item src="images/FourWayClamp4.JPG" caption="" >}}
{{< gallery-item src="images/FourWayClamp5.JPG" caption="" >}}
{{< gallery-item src="images/FourWayClamp6.JPG" caption="" >}}
{{< gallery-item src="images/FourWayClamp7.JPG" caption="" >}}
{{< gallery-item src="images/CoreBlank_SliceJoin1.JPG" caption="Halves of a core blank coming together." >}}
{{< gallery-item src="images/CoreBlank_SliceJoin2.JPG" caption="Joining halves of a core blank. You can clearly see the glue squeezeout and the spacers for the clamps." >}}
{{< gallery-item src="images/CoreBlank_Sidewall4.JPG" caption="The blank, with ash and PTEX in place, back in the clamps for the night." >}}
{{< /gallery >}}

## See Also 
- [Joining the halves of a core blank]({{< ref "MonkeyWiki/Construction/Core_blank_construction/Joining_the_halves_of_a_core_blank.md" >}})
- [Ash edge stringer and sidewalls]({{< ref "MonkeyWiki/Construction/Core_construction/Ash_edge_stringer_and_sidewalls.md" >}})
