mikemag/MonkeyWiki/content/en/MonkeyWiki/Equipment/Small_tools/Hand_Scraper.md

---
dateFromWiki: "2019-02-03T02:39:24Z"
title: "Hand Scraper"
gallery: true
aliases:
- /MonkeyWiki/Hand_Scraper
- /MonkeyWiki/Hand_Scraper/en
---
A simple hand scraper is amazingly useful any time glue needs to be removed from something. I use this one during core blank construction to cleanup glue squeeze-out, cleaning up excess glue after insetting sidewalls, and even removing fuzz after certain stages of machining a core. You should be able to find one at any hardware store. It’s just a simple handle holding a hardened steel scraper. The blades can be rotated as they wear down.

{{< gallery  caption="Hand Scraper" >}}
{{< gallery-item src="images/Hand_Scraper1.JPG" caption="Hand scraper." >}}
{{< gallery-item src="images/Hand_Scraper2.JPG" caption="Hand scraper." >}}
{{< gallery-item src="images/Hand_Scraper3.JPG" caption="Hand scraper." >}}
{{< /gallery >}}
