mikemag/MonkeyWiki/content/en/MonkeyWiki/Equipment/Small_tools/Pipe_Clamps.md

---
dateFromWiki: "2019-02-03T02:40:42Z"
title: "Pipe Clamps"
gallery: true
aliases:
- /MonkeyWiki/Pipe_Clamps
- /MonkeyWiki/Pipe_Clamps/en
---
Pipe clamps are useful for building core blanks. They apply reasonable force over a wide distance, and they can be made any length you want by using different pipes. The ends are easily adjusted for different clamping widths on the same pipe. I’ve added 2” x 2” x 12” oak cauls on each side of the clamps to distribute clamping force over a wider area.

The clamps I use came from Woodcraft, but you can find them almost anywhere. Buy pipe at something like Home Depot or Lowes: [Pipe Clamps](http://www.woodcraft.com/Product/2005440/16062/Jorgensen-Pony-Pipe-Clamp-34.aspx)

{{< gallery  caption="Pipe Clamps" >}}
{{< gallery-item src="images/PipeClamp1.JPG" caption="Pipe clamps." >}}
{{< gallery-item src="images/PipeClamp2.JPG" caption="Pipe clamps." >}}
{{< gallery-item src="images/PipeClamp3.JPG" caption="Pipe clamps." >}}
{{< /gallery >}}
