mikemag/MonkeyWiki/content/en/MonkeyWiki/Equipment/CNC/CAD_CAM_Software/_index.md

---
title: "CAD/CAM Software"
weight: 10
bookCollapseSection: true
---
