mikemag/MonkeyWiki/content/zh-cn/MonkeyWiki/Equipment/CNC/CAD_CAM_Software/_index.md

---
title: "CAD/CAM软件"
weight: 10
bookCollapseSection: true
---
