mikemag/MonkeyWiki/content/en/MonkeyWiki/Equipment/CNC/CAD_CAM_Software/Fusion_360.md

---
dateFromWiki: "2019-03-24T20:14:48Z"
title: "Fusion 360"
aliases:
- /MonkeyWiki/Fusion_360
- /MonkeyWiki/Fusion_360/en
---
[Fusion 360](https://www.autodesk.com/products/fusion-360) is a very good CAD/CAM system which is free for "hobbyists and startups". I've used it a bit to make some mold designs, and it's quite good. It's currently the best recommendation for free CAD/CAM software.

It is offered free for "For startups generating <$100k/year in total revenue or wholly non-commercial users." Here's the details on getting your free license: https://knowledge.autodesk.com/support/fusion-360/troubleshooting/caas/sfdcarticles/sfdcarticles/How-to-activate-start-up-or-educational-licensing-for-Fusion-360.htm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

See [Molds and cassettes]({{< ref "MonkeyWiki/Equipment/Snowboard_press/Molds_and_cassettes.md" >}}) for some examples of Fusion 360 in action.
