mikemag/MonkeyWiki/content/zh-cn/MonkeyWiki/Equipment/CNC/CAD_CAM_Software/Fusion_360.md

---
dateFromWiki: "2019-03-25T04:46:56Z"
title: "Fusion 360"
aliases:
- /MonkeyWiki/Fusion_360/zh-cn
translatedDate: "2019-03-25T04:46:56Z"
translator: "X z"
translatorPage: "/zh-cn/MonkeyWiki/X_z"
---
[Fusion 360](https://www.autodesk.com/products/fusion-360)是一个非常好的CAD/CAM系统，对于“业余爱好者和初创公司”是免费的。我用它做了一些模具设计，而且非常好。它是目前免费CAD/CAM软件的最佳推荐。

它是免费提供的“对于初创公司每年产生<10万美元的总收入或完全非商业用户。以下是获取免费许可证的详细信息：https://knowledge.autodesk.com/support/fusion-360/troubleshooting/caas/sfdcarticles/sfdcarticles/How-to-activate-start-up-or-educational-licensing-for-Fusion-360.htm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

See [Molds and cassettes]({{< ref path="MonkeyWiki/Equipment/Snowboard_press/Molds_and_cassettes.md" lang="en" >}}) for some examples of Fusion 360 in action.
