mikemag/MonkeyWiki/content/zh-cn/MonkeyWiki/Equipment/CNC/CAD_CAM_Software/MonkeyCAM.md

---
dateFromWiki: "2020-04-28T09:18:37Z"
title: "MonkeyCAM"
aliases:
- /MonkeyWiki/MonkeyCAM/zh-cn
translatedDate: "2020-04-28T09:18:37Z"
translator: "X z"
translatorPage: "/zh-cn/MonkeyWiki/X_z"
---
MonkeyCAM v4.0是一个开源的CAD/CAM程序，用于设计滑雪板，并生成G-code程序，然后用CNC机器切割滑雪板部件。 

以下是MonkeyCAM生成的概述：https://rawgit.com/mikemag/MonkeyCAM/master/Sample-output/Sample-snowboard-overview.html

MonkeyCAM在Github上发布，网址为 
https://github.com/mikemag/MonkeyCAM ，你可以在其中找到文档，示例以及下载适用于Mac和Windows的程序。Skibuilders还有一个帖子http://www.skibuilders.com/phpBB2/viewtopic.php?t=4450

MonkeyCAM相对于通用CAD/CAM程序的价值在于它可以快速精确生成构建滑雪板所需的G-Code程序，无需人工干预。但是，这就是所有MonkeyCAM所做的。它不会为其他任何东西生成程序，所以拥有并知道如何使用通用CAD/CAM系统仍然很有用。
