mikemag/MonkeyWiki/content/zh-cn/MonkeyWiki/Resources/Woodworking_Resources.md

---
title: "木工资源"
aliases:
- /MonkeyWiki/Woodworking_Resources/zh-cn
translatedDate: "2020-04-28T09:26:47Z"
translator: "X z"
translatorPage: "/zh-cn/MonkeyWiki/X_z"
---
许多滑雪板制造涉及使用木材。如果你想建立自己的芯坯，甚至完成一个成型的板芯，那么你应该更熟悉一般的木工。有一些令人眼花缭乱的木工资源，所以这个页面收集了我最喜欢的一些，特别适用于滑雪板制造。

其中许多参考文献来自[Fine Woodworking](http://www.finewoodworking.com)的文章。这是一本优秀的杂志，虽然它专注于精美的家具制造，但有许多关于机械，基本技术和材料的文章对于滑雪板制造商来说是非常宝贵的。我强烈推荐他们的在线网站的会员资格，价格非常合理。你可以在线找到所有这些PDF格式的文章，你甚至可以下载并保存这些文章以供将来参考。或者我确信你可以在本地库中找到这些问题。

## 木材和木材科学

关于木材科学的权威性工作。没有木工应该没有这本书。它包括识别，木材强度，含水量和干燥，加工和弯曲木材，连接，弯曲，木材和木皮。 

- [Hoadley, R. B. (2000). Understanding Wood. Taunton Press, ISBN 978-1561583584](http://www.amazon.com/Understanding-Wood-Craftsmans-Guide-Technology/dp/1561583588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)

关于从真正的木材厂购买木材的优秀文章，而不是家得宝。包括测量（“4/4”表示），分级，不同类型的切割等。 

- [Scott, S. (2011, September). “The Language of the Lumberyard” Fine Woodworking, #221, 22-24.](https://www.finewoodworking.com/2011/07/28/the-language-of-the-lumberyard)

木材运动的入门书：

- [Becksvoort, C. (2006, November). “Stop Guessing at Wood Movement” Fine Woodworking, #187, 78-83.](http://www.finewoodworking.com/SkillsAndTechniques/SkillsAndTechniquesPDF.aspx?id=27129)

这是一个非常好的视频，是一个小型木材厂的参观。它将为你提供树木如何变成木材的视角：

- [Rodriguez, M. and Spacht, D., "Tour a Boutique Lumbermill", Fine Woodworking](http://www.finewoodworking.com/Materials/MaterialsArticle.aspx?id=29459)

这是关于如何干燥木材，木材干燥窑看起来像什么，适当粘木干燥等的非常好的视频：

- [Rodriguez, M. and Spacht, D., "How To Dry Lumber", Fine Woodworking](http://www.finewoodworking.com/Materials/MaterialsArticle.aspx?id=29500)

## 带锯和往复锯

在带锯上重新调整较大的库存是高效的核心坯料构造的核心。这里的文章涉及建造核心空白和切割自己的顶片木皮。这些包括有关如何为此目的设置带锯，导轨，刀片漂移，刀片选择等的信息。

- [Bird, L. (2007, January). “Resawing on the Bandsaw” Fine Woodworking, #189, 39-42.](http://www.finewoodworking.com/SkillsAndTechniques/SkillsAndTechniquesPDF.aspx?id=27779)
- [Volbrecht, R. (1997, January). “Resawing on the Bandsaw” Fine Woodworking, #122, 74-79.](https://www.finewoodworking.com/1997/02/01/resawing-on-the-bandsaw)
- [Coleman, T. (2000, July). “Bandsaw Your Own Veneer” Fine Woodworking, #143, 44-49.](http://www.finewoodworking.com/SkillsAndTechniques/SkillsAndTechniquesPDF.aspx?id=2653)

一篇关于为什么提高带锯尺寸（即大于平均14“型号）的好文章是一个好主意。

- [Johnson, R. (2011). “Step Up to a Serious Bandsaw” Fine Woodworking, #216, 37-41.](https://www.finewoodworking.com/2010/10/28/tool-test-step-up-to-a-serious-bandsaw)

Matthias Wandel在[Woodgears.ca](http://woodgears.ca/)上[胶水和夹紧 ==

关于各种胶水强度的好文章。包括他们的测试技术，这是我们经常使用滑雪板构造技术进行的其他测试的思考。

- [http://www.finewoodworking.com/Materials/MaterialsPDF.aspx?id=28897 Schofield, M. (2007, July). “How Strong Is Your Glue?” Fine Woodworking, #192, 36-40.](http://woodgears.ca/bandsaw/resaw.html带锯的物理学]的精彩插图。这是我见过的最好的示范，说明刀片在重新锯切时必须做的工作以及刀片宽度，张力和牙齿每公司的影响

==)

夹紧技术。非常适用于各种板芯构造技术。包括有关夹具类型，如何正确应用，均匀压力和关节失效的信息。 

- [Hendrik, V. (2010). “The Secret to Great Glue-Ups” Fine Woodworking, #218, 22-28.](http://www.finewoodworking.com/SkillsAndTechniques/SkillsAndTechniquesPDF.aspx?id=33887)
- [Rabiej, R. (2007, November). “Get Serious About Clamping” Fine Woodworking, #194, 37-41.](http://www.finewoodworking.com/SkillsAndTechniques/SkillsAndTechniquesPDF.aspx?id=29561)

## 压刨和平刨

使用压刨和平刨。包括使用压刨作为平刨使用刨床，这与许多用于将厚度轮廓应用于板芯的刨床非常相似。

- [Rust, K. (2005, January). “Flatten Boards Without a Jointer” Fine Woodworking, #175, 58-61.](http://www.finewoodworking.com/SkillsAndTechniques/SkillsAndTechniquesPDF.aspx?id=24118)
- [Rogowski, G. (2002). “The Jointer and Planer Are a Team” Fine Woodworking, #160, 64-67.](http://www.finewoodworking.com/ToolGuide/ToolGuideArticle.aspx?id=29511)

## 待办事项

需要为以下主题添加链接： 

- 小工作室收集灰尘
- More on the planer and jointer, including how to setup, avoiding snipe in both, forming square stock from rough lumber, etc.
- Tablesaw, in particular safety.
- Finishes, stains, HVLP sprayers for finishing, rubbing on standard finishes instead of spraying, etc.
- Vacuum bagging as it applies to applying veneer only.
