mikemag/MonkeyWiki/content/zh-cn/MonkeyWiki/Equipment/Snowboard-specific_tools/_index.md

---
title: "滑雪板专用工具"
weight: 3
bookCollapseSection: true
---
