mikemag/MonkeyWiki/content/zh-cn/MonkeyWiki/Equipment/Snowboard-specific_tools/Edge_Benders.md

---
dateFromWiki: "2019-04-03T13:42:01Z"
title: "弯边机"
gallery: true
aliases:
- /MonkeyWiki/Edge_Benders/zh-cn
translatedDate: "2019-04-03T13:42:01Z"
translator: "X z"
translatorPage: "/zh-cn/MonkeyWiki/X_z"
---
边刃完全可以用手进行弯曲，但一些简单的工具可以帮助你保护手指。 

## 改装环辊

我使用[Harbor Freight](http://harborfreight.com)（部件号36790）的改进环辊在边刃进行初始弯曲，然后用手完成。在车床上对中心辊进行了改进，使边缘的大部分形成了一个微小的凹口，并在外侧添加了一个额外的圆盘以支撑叉齿。通过几个薄垫圈将盘保持远离主缸。 

当调整滚子以实现紧密弯曲时，在滚轮中开始边缘是很困难的。我在调节旋钮上放置一个标记，这样我可以将它转回一定数量的转动以使边缘刚刚开始，然后将其重置为更紧的半径以开始弯曲。 

[Skibuilders.com](http://skibuilders.com)上有很多人建造了这样的弯边机，但是滚轮是垂直而不是水平的。这使得边刃在弯曲时可以保持在桌子上，而在我弯曲时，我必须将边刃保持在相当远的距离，因为我将其从弯边机中滚出。垂直滚轮看起来好多了，有一天我会脱下我的配件并建造一个。  

{{< gallery  caption="改良环辊" >}}
{{< gallery-item src="images/RingRoller5.JPG" caption="" >}}
{{< gallery-item src="images/RingRoller1.JPG" caption="" >}}
{{< gallery-item src="images/RingRoller2.JPG" caption="" >}}
{{< gallery-item src="images/RingRoller3.JPG" caption="" >}}
{{< gallery-item src="images/RingRoller4.JPG" caption="" >}}
{{< /gallery >}}

==修改后的钳 ==

当需要非常紧的弯曲时，一些改装过的钳子提供的杠杆是完美的。通过一些练习，你将能够在你需要的地方添加平滑弯曲，或轻松撤消意外扭结。使用台式砂轮机和/或Dremel工具非常容易制作。“钳子”被称为不同的东西; 你可能会看到“concreter's nippers”，“wire nippers”等。我改装过的那对来自Lowes，售价不到20美元。修改钳子花了大约15分钟。  

研磨一侧，在中心留下一个狭窄的“手指”，并在另一侧研磨一个凹口，使手指适应充足的空间。钳子的原始边缘是锋利和硬化的，这很好，因为它有助于抓住边刃而不会滑动，因此尽可能地保留原始边缘。练习一些备用边缘，你会很快学会非常准确地进行非常精细的调整。  

{{< gallery  caption="改装过的钳子" >}}
{{< gallery-item src="images/Nippers1.JPG" caption="" >}}
{{< gallery-item src="images/Nippers2.JPG" caption="" >}}
{{< gallery-item src="images/Nippers3.JPG" caption="" >}}
{{< gallery-item src="images/Nippers4.JPG" caption="" >}}
{{< gallery-item src="images/Nippers5.JPG" caption="" >}}
{{< gallery-item src="images/Nippers6.JPG" caption="" >}}
{{< gallery-item src="images/Nippers7.JPG" caption="" >}}
{{< gallery-item src="images/Nippers8.JPG" caption="" >}}
{{< gallery-item src="images/Nippers9.JPG" caption="" >}}
{{< gallery-item src="images/Nippers10.JPG" caption="" >}}
{{< /gallery >}}

## See Also

- [板底, 边刃, 板头和板尾垫片]({{< ref "MonkeyWiki/Construction/Laminate_preparation/Bases__edges__and_nose_tail_spacers.md" >}})
