mikemag/MonkeyWiki/content/en/MonkeyWiki/Equipment/Snowboard-specific_tools/Edge_Benders.md

---
dateFromWiki: "2019-02-03T02:38:25Z"
title: "Edge Benders"
gallery: true
aliases:
- /MonkeyWiki/Edge_Benders
- /MonkeyWiki/Edge_Benders/en
---
Edges can be bent completely by hand, but a few simple tools help save your fingers. For snowboards I just use the modified ring roller below to get started and do the rest by hand, but for skis I find that the hand tool is required to get such tight bends done well. 

## Modified Ring Roller 
I use a modified ring roller from [Harbor Freight](http://harborfreight.com) (part #36790) to put an initial bend in edges and then finish them up by hand. The center roller was modified on a lathe to make a slight notch for the bulk of the edge, and an extra disc is added on the outside to support the tines. The disc is held away from the main cylinder by a few thin washers. 

Getting the edge started in the roller is hard when the rollers are adjusted for a tight bend. I place a marker on the adjustment knob so I can turn it back some number of turns to get the edge just started, and then reset it to the tighter radius to start bending. 

There are a bunch of guys on [Skibuilders.com](http://skibuilders.com) who have built benders like this but with the rollers oriented vertically instead of horizontally. This allows the edge to stay flat on a table while you’re bending it, whereas with mine I have to hold the edge up quite far as I roll it back out of the bender. The vertical roller way looks much better, and one day I’ll get off my butt and build one.  

{{< gallery  caption="Modified Ring Roller" >}}
{{< gallery-item src="images/RingRoller5.JPG" caption="" >}}
{{< gallery-item src="images/RingRoller1.JPG" caption="" >}}
{{< gallery-item src="images/RingRoller2.JPG" caption="" >}}
{{< gallery-item src="images/RingRoller3.JPG" caption="" >}}
{{< gallery-item src="images/RingRoller4.JPG" caption="" >}}
{{< /gallery >}}

## Modified Nippers 
When a really tight bend is required the leverage provided by some modified nippers is perfect. With a little practice you’ll be able to add a smooth bend exactly where you need it, or undo an accidental kink with ease. These are very easy to make with a bench grinder and/or a Dremel tool. The “nippers” are called different things; you might see “concreter’s nippers”, “wire nippers”, etc. The pair I modified were from Lowes and cost less than $20. It took about 15min to modify the nippers.  

Grind one side to leave a narrow “finger” in the center, and grind a notch in the other side for the finger to fit into with plenty of room to spare. The original edge of the nippers is sharp and hardened, which is good because it will help grip the steel edge without slipping, so leave the original edge as much as possible. Practice on some spare pieces of edge and you’ll quickly learn to make very fine adjustments very accurately.  

{{< gallery  caption="Modified Nippers" >}}
{{< gallery-item src="images/Nippers1.JPG" caption="" >}}
{{< gallery-item src="images/Nippers2.JPG" caption="" >}}
{{< gallery-item src="images/Nippers3.JPG" caption="" >}}
{{< gallery-item src="images/Nippers4.JPG" caption="" >}}
{{< gallery-item src="images/Nippers5.JPG" caption="" >}}
{{< gallery-item src="images/Nippers6.JPG" caption="" >}}
{{< gallery-item src="images/Nippers7.JPG" caption="" >}}
{{< gallery-item src="images/Nippers8.JPG" caption="" >}}
{{< gallery-item src="images/Nippers9.JPG" caption="" >}}
{{< gallery-item src="images/Nippers10.JPG" caption="" >}}
{{< /gallery >}}

## See Also 
- [Bases, edges, and nose/tail spacers]({{< ref "MonkeyWiki/Construction/Laminate_preparation/Bases__edges__and_nose_tail_spacers.md" >}})
