mikemag/MonkeyWiki/content/zh-cn/MonkeyWiki/_index.md

---
title: "首页"
gallery: true
aliases:
- /MonkeyWiki/Main_Page/zh-cn
translatedDate: "2019-04-08T14:17:26Z"
translator: "X z"
translatorPage: "/zh-cn/MonkeyWiki/X_z"
---
{{< img src="images/Board_2018.jpg" width=300px caption="_2018年冬季完成的滑雪板。木饰面板采用华丽的古夷苏木，英国梧桐和乌木。长164厘米_" >}}

这不是对完成这些任务的所有不同方式的综合处理，而是我亲自完成的对我有用的方法。有关替代品请参考[SkiBuilders.com](http://www.skibuilders.com),在那里，他们收集了关于他们和其他人如何制造滑雪板的详细说明，并创办了一个很棒的论坛，以提供有关替代品的更多信息。

享受它吧

[迈克 · 马格鲁德 (又叫做 Head Monkey)]({{< ref "MonkeyWiki/Head_Monkey.md" >}})

## 捐

您可以通过少量捐款来帮助抵消运行 MonkeyWiki 的服务器成本。



## 目录

- [建造概况]({{< ref "MonkeyWiki/Construction" >}})
- [设备概述]({{< ref "MonkeyWiki/Equipment" >}})
- [材料概述]({{< ref "MonkeyWiki/Materials" >}})
- [参考资料概述]({{< ref "MonkeyWiki/Resources" >}})
- [关于]({{< ref "MonkeyWiki/About.md" >}})

## 适合制造滑雪双板吗?

我已经制作了一对滑雪双板，结果很棒。你会发现滑雪双板和滑雪单板结构惊人地相似。你可以使用此处的所有信息进行制造，即使它们都指向滑雪单板。这也没关系。

## 状态

有一些占位符我将尝试使用Real Soon Now，但是现在这里的文章在技术上是正确的并且是最新的。
