mikemag/MonkeyWiki/content/en/MonkeyWiki/X_z.md

---
dateFromWiki: "2019-03-28T06:14:12Z"
title: "X z"
bookHidden: true
aliases:
- /MonkeyWiki/User:X_z
- /MonkeyWiki/User:X_z/en
- /MonkeyWiki/User:X_z/zh-cn
---
我是该网站中文译者，你在阅读过程遇到任何问题或者有什么好的建议，可以与我的QQ:168726413取得联系
