mikemag/MonkeyWiki/content/zh-cn/MonkeyWiki/Head_Monkey.md

---
title: "Head Monkey"
bookHidden: true
translatedDate: "2019-11-19T03:54:49Z"
translator: "X z"
translatorPage: "/zh-cn/MonkeyWiki/X_z"
---
我是Happy Monkey Snowboards，Inc。的创始人迈克 · 马格鲁德，它从2003年到2010年是一个非常小的企业，我手工制作定制滑雪板。
虽然我已经关闭了Happy Monkey，但我继续为自己和我的亲密朋友制作滑雪板。
我一般都沉迷于滑雪板的构造，我总是在努力学习改进流程，设备和最终结果的新方法。 

你可以通过电子邮件直接联系我们'''monkeywiki1 at this domain'''，或者通过私人信息联系Head Monkey在[Skibuilders.com](http://www.skibuilders.com)论坛。
我也可以在[Facebook](https://www.facebook.com/mike.magruder)和[LinkedIn](https://www.linkedin.com/in/mikemag/)上找到。

## 背景

我没有任何有助于制造滑雪板或运营滑雪板业务的正式背景。
我所知道的关于滑雪板结构，木工，CNC或机加工的一切，是我通过反复试验，与其他制造商交谈，以及在当地技术学院加工的技术课程所获得。 

我的正规教育是计算机科学。
是我在乔治梅森大学获得了CS的硕士学位。
我自1989年以来[在各种不同的软件公司工作过。](https://www.linkedin.com/in/mikemag/)
