mikemag/MonkeyWiki/content/zh-cn/MonkeyWiki/术语表.md

---
dateFromWiki: "2019-04-17T08:48:50Z"
title: "术语表"
aliases:
- /MonkeyWiki/术语表
- /MonkeyWiki/术语表/en
translatedDate: "2019-04-17T08:48:50Z"
translator: "X z"
translatorPage: "/zh-cn/MonkeyWiki/X_z"
weight: 5
---
- ash:  白蜡木
- fence: 靠山 导轨
- topsheet: 顶片 顶层 板顶
- layout 铺层
- sidewall:  侧壁 边墙
- 无序列表项
