mikemag/MonkeyWiki/content/zh-cn/MonkeyWiki/Equipment/_index.md

---
title: "设备概述"
aliases:
- /MonkeyWiki/Equipment_Overview/zh-cn
translatedDate: "2019-04-08T14:55:01Z"
translator: "X z"
translatorPage: "/zh-cn/MonkeyWiki/X_z"
weight: 2
bookCollapseSection: true
---
以下文章涵盖了制造滑雪板所需的设备。其中一些可以从普通五金店购买，有些必须由你建造。有些是绝对必需的，而其他（如CNC机器）是可选的。你真正需要哪些将取决于你选择制造滑雪板的方式以及你可以获得的原材料。例如，如果你从某人那里购买板芯，那么你可能并不需要大多数较大的木工工具。如果你愿意用手完全弯曲边刃，那么你就不需要专门的弯边机等。

*Note: this isn't a complete list of tools, just the ones I've taken some time to write about here.*

- 数控设备
  - [CNC 雕刻机]({{< ref "MonkeyWiki/Equipment/CNC/CNC_Router.md" >}})
  - [你需要一台数控机器吗？]({{< ref "MonkeyWiki/Equipment/CNC/Do_you_need_a_CNC_machine_.md" >}})
  - [数控雕刻机: 自己造还是买?]({{< ref "MonkeyWiki/Equipment/CNC/CNC_machines__build_or_buy_.md" >}})
  - [Shaper Origin]({{< ref "MonkeyWiki/Equipment/CNC/Shaper_Origin.md" >}})
  - CAD/CAM软件
    - [Fusion 360]({{< ref "MonkeyWiki/Equipment/CNC/CAD_CAM_Software/Fusion_360.md" >}})
    - [MonkeyCAM]({{< ref "MonkeyWiki/Equipment/CNC/CAD_CAM_Software/MonkeyCAM.md" >}})
    - [snoCAD-X]({{< ref "MonkeyWiki/Equipment/CNC/CAD_CAM_Software/SnoCAD-X.md" >}})
- 滑雪板压制
  - [Monkey 压力机制造]({{< ref "MonkeyWiki/Equipment/Snowboard_press/Monkey_Press_Construction.md" >}})
  - [压机温控箱和加热设备]({{< ref "MonkeyWiki/Equipment/Snowboard_press/Press_heat_control_and_thermocouples.md" >}})
  - [模具和cassettes]({{< ref path="MonkeyWiki/Equipment/Snowboard_press/Molds_and_cassettes.md" lang="en" >}})
- 滑雪板专用工具
  - [挠度测试夹具]({{< ref "MonkeyWiki/Equipment/Snowboard-specific_tools/Deflection_Testing_Jig.md" >}})
  - [弯边机]({{< ref "MonkeyWiki/Equipment/Snowboard-specific_tools/Edge_Benders.md" >}})
  - [板底磨床]({{< ref "MonkeyWiki/Equipment/Snowboard-specific_tools/Base_grinder.md" >}})
- 小工具
  - [气动剪刀]({{< ref "MonkeyWiki/Equipment/Small_tools/Air_Shears.md" >}})
  - [羽毛板]({{< ref "MonkeyWiki/Equipment/Small_tools/Feather_Board.md" >}})
  - [四向夹具]({{< ref "MonkeyWiki/Equipment/Small_tools/Four-way_Clamps.md" >}})
  - [手刮板]({{< ref "MonkeyWiki/Equipment/Small_tools/Hand_Scraper.md" >}})
  - [水管夹]({{< ref "MonkeyWiki/Equipment/Small_tools/Pipe_Clamps.md" >}})
  - [雕刻机主轴和修边机]({{< ref "MonkeyWiki/Equipment/Small_tools/Routers_and_laminate_trimmers.md" >}})
  - [雕刻机刀具]({{< ref "MonkeyWiki/Equipment/Small_tools/Router_Bits.md" >}})
- 大型工具
  - [HVLP喷雾器]({{< ref "MonkeyWiki/Equipment/Larger_tools/HVLP_Sprayer.md" >}})
