mikemag/MonkeyWiki/content/en/MonkeyWiki/leftovers/术语表.md

---
dateFromWiki: "2019-04-17T08:48:50Z"
title: "术语表"
aliases:
- /MonkeyWiki/术语表
- /MonkeyWiki/术语表/en
---
- ash:  白蜡木
- fence: 靠山 导轨
- topsheet: 顶片 顶层 板顶
- layout 铺层
- sidewall:  侧壁 边墙
- 无序列表项
