mikemag/MonkeyWiki/content/zh-cn/MonkeyWiki/Equipment/CNC/Shaper_Origin.md

---
dateFromWiki: "2020-04-28T09:14:51Z"
title: "Shaper Origin"
gallery: true
aliases:
- /MonkeyWiki/Shaper_Origin/zh-cn
translatedDate: "2020-04-28T09:14:51Z"
translator: "X z"
translatorPage: "/zh-cn/MonkeyWiki/X_z"
weight: 4
---
[Shaper Origin](https://www.shapertools.com/)是一款手持式CNC雕刻机，可用于切割各种2D形状。对于CNC模具和模板而言，它是一个可靠的选择，具有最小的空间要求和非常好的精度。 

我简单地使用其中一个来测试模块的一部分，并且它工作得非常好。我的一个好朋友有一个，并用它做了一些令人印象深刻的事情。我在Fusion 360中创建了一个我的板头模块的模型，你可以在这里找到它：https://a360.co/2pCwsLA 我与他分享了它并使用了Shaper Origin的Fusion 360插件来生成文件 该工具将它们扔在USB存储棒上。

这基本上是一个带有CNC控制的层压修剪器，手持设备比普通的全尺寸路由器略大。刀具在X/Y轴上的移动大约为+/- 1"。你可以沿刀具路径引导刀具，将路径保持在屏幕上的圆圈中，然后机器进行调整以使刀具与刀具保持一致。通过计算机视觉和工作台上的“多米诺骨牌”磁带保持其位置。这很容易做到，虽然需要一些练习才能比机器不能更快地移动，并且更多 稳定你的结果越好。

这对于与滑雪板和滑雪板相关的2D工作的大型龙门路由器来说是一个完美的替代品：模具，底座和核心模板，甚至直接切割基础材料和直接/尾部填充。 唯一缺乏的是你不能用它来描述，虽然你当然可以为刨床/砂光机设置配置文件。

{{< gallery  caption="测试Shaper Origin，切割模具零件" >}}
{{< gallery-item src="images/Shaper_Test_1.jpg" caption="Test of Shaper Origin accuracy." >}}
{{< gallery-item src="images/Shaper_Test_2.jpg" caption="Test of Shaper Origin accuracy." >}}
{{< gallery-item src="images/Shaper_Test_3.jpg" caption="Shaper Origin test cutting part of an end block for a mold." >}}
{{< gallery-item src="images/Shaper_Test_4.jpg" caption="Testing accuracy of a Shaper Origin." >}}
{{< /gallery >}}
