mikemag/MonkeyWiki/content/zh-cn/MonkeyWiki/Equipment/Larger_tools/_index.md

---
title: "大型工具"
weight: 5
bookCollapseSection: true
---
