mikemag/MonkeyWiki/content/zh-cn/MonkeyWiki/Equipment/Small_tools/_index.md

---
title: "小工具"
weight: 4
bookCollapseSection: true
---
