mikemag/MonkeyWiki/content/zh-cn/MonkeyWiki/Equipment/Snowboard_press/_index.md

---
title: "滑雪板压制"
weight: 2
bookCollapseSection: true
---
