mikemag/MonkeyWiki/content/zh-cn/MonkeyWiki/Equipment/Larger_tools/HVLP_Sprayer.md

---
dateFromWiki: "2019-04-23T03:03:34Z"
title: "HVLP喷雾器"
gallery: true
aliases:
- /MonkeyWiki/HVLP_Sprayer/zh-cn
translatedDate: "2019-04-23T03:03:34Z"
translator: "X z"
translatorPage: "/zh-cn/MonkeyWiki/X_z"
---
HVLP（高容量低压）喷涂系统非常适合喷涂各种表面处理。对于滑雪板，我使用Fuji Q3 Pro HVLP喷雾器，拍摄系统三WR-LPU聚氨酯面漆，在透明缎面，切割20-25％w /水。这样可以在板上涂上光滑，均匀的涂层，最大限度地减少混乱和清理。该喷枪易于使用且熟悉，喷涂模式易于调节。 

查看[精加工木饰面板]({{< ref "MonkeyWiki/Construction/Finishing/Finishing_a_wood_veneer_top_sheet.md" >}})有关胶合板整理过程的更多详细信息。

{{< gallery  caption="HVLP喷雾器" >}}
{{< gallery-item src="images/Veneer_Finishing_2_5.jpg" caption="HVLP unit" >}}
{{< gallery-item src="images/Veneer_Finishing_2_6.jpg" caption="HVLP spray gun" >}}
{{< gallery-item src="images/Veneer_Finishing_2_7.jpg" caption="HVLP spray gun tip" >}}
{{< gallery-item src="images/Veneer_Finishing11.JPG" caption="The finish and spray gun." >}}
{{< /gallery >}}
