mikemag/MonkeyWiki/content/zh-cn/MonkeyWiki/Equipment/Small_tools/Air_Shears.md

---
dateFromWiki: "2019-04-01T05:45:30Z"
title: "气动剪刀"
gallery: true
aliases:
- /MonkeyWiki/Air_Shears/zh-cn
translatedDate: "2019-04-01T05:45:30Z"
translator: "X z"
translatorPage: "/zh-cn/MonkeyWiki/X_z"
---
内联气动剪刀非常适合切割铝模皮。我使用的是从Harbor Freight那里得到的便宜货。它们很响，很挑剔，但通过一些练习，你可以轻松地切割金属板。

{{< gallery  caption="气动剪刀" >}}
{{< gallery-item src="images/Air_Shears_1.jpg" caption="" >}}
{{< gallery-item src="images/Air_Shears_2.jpg" caption="" >}}
{{< gallery-item src="images/Air_Shears_3.jpg" caption="" >}}
{{< /gallery >}}
