mikemag/MonkeyWiki/content/zh-cn/MonkeyWiki/Equipment/Small_tools/Hand_Scraper.md

---
dateFromWiki: "2019-04-02T15:12:53Z"
title: "手刮板"
gallery: true
aliases:
- /MonkeyWiki/Hand_Scraper/zh-cn
translatedDate: "2019-04-02T15:12:53Z"
translator: "X z"
translatorPage: "/zh-cn/MonkeyWiki/X_z"
---
只要需要从某些东西中移除胶水，简单的手动刮刀就非常有用。我在空白板结构中使用这个来清理胶水挤出，在嵌入边墙后清理多余的胶水，甚至在加工板芯的某些阶段后去除绒毛。你应该能够在任何五金店找到。它只是一个握有硬化钢刮刀的简单手柄。刀片磨损时可以旋转。

{{< gallery  caption="Hand Scraper" >}}
{{< gallery-item src="images/Hand_Scraper1.JPG" caption="Hand scraper." >}}
{{< gallery-item src="images/Hand_Scraper2.JPG" caption="Hand scraper." >}}
{{< gallery-item src="images/Hand_Scraper3.JPG" caption="Hand scraper." >}}
{{< /gallery >}}
