mikemag/MonkeyWiki/content/zh-cn/MonkeyWiki/Equipment/CNC/CAD_CAM_Software/SnoCAD-X.md

---
dateFromWiki: "2019-04-10T02:38:57Z"
title: "SnoCAD-X"
aliases:
- /MonkeyWiki/SnoCAD-X/zh-cn
translatedDate: "2019-04-10T02:38:57Z"
translator: "X z"
translatorPage: "/zh-cn/MonkeyWiki/X_z"
---
snoCAD-X是一个用于设计滑雪板的开源CAD程序。它由格拉夫滑雪板的Dan Graf于2007年编写，并从那时起被广泛使用。2014年，它在GitHub上开源，以便让更大的滑雪板制造社区继续前进。

snoCAD-X发布于Github，网址为https://github.com/mikemag/snoCAD-X。有关如何使用和配置snoCAD-X的概述，请参见“snoCAD-X用户指南”。

请参阅当前版本的[Releases](https://github.com/mikemag/snoCAD-X/releases)页面，其中包括发行说明和下载二进制文件的链接。只需下载zip并双击snoCAD-x.jar即可在安装了Java的任何平台上启动应用程序。有关详细信息，请参阅发行说明。

snoCAD-X没有CAM(计算机辅助加工)功能，因此你需要将设计导出为DXF并将其导入CAM包中以使用CNC切割零件。你还可以全面打印你的设计，并使用它们手工切割，这是一个很好的入门方式。
