mikemag/MonkeyWiki/content/zh-cn/MonkeyWiki/Resources/_index.md

---
title: "参考资料概述"
aliases:
- /MonkeyWiki/Resources_Overview/zh-cn
translatedDate: "2019-02-13T07:11:19Z"
translator: "X z"
translatorPage: "/zh-cn/MonkeyWiki/X_z"
weight: 4
bookCollapseSection: true
---
以下文章提供了与滑雪板制造相关的许多基本技能，工具和技术的链接和参考。这些资源我已经发现非常有用，因为我已经了解了木工，复合材料，金属加工等。 

- [木工资源]({{< ref "MonkeyWiki/Resources/Woodworking_Resources.md" >}})
- [金属加工和机械加工资源]({{< ref "MonkeyWiki/Resources/Metalworking_and_Machining_Resources.md" >}})
