mikemag/MonkeyWiki/content/zh-cn/MonkeyWiki/Resources/Metalworking_and_Machining_Resources.md

---
dateFromWiki: "2019-04-17T09:21:31Z"
title: "金属加工和机械加工资源"
aliases:
- /MonkeyWiki/Metalworking_and_Machining_Resources/zh-cn
translatedDate: "2019-04-17T09:21:31Z"
translator: "X z"
translatorPage: "/zh-cn/MonkeyWiki/X_z"
---
滑雪板制造所需的大多数专用工具和设备必须由你自己制造。这往往涉及一些金属加工和机械加工。 

此页面将随着时间的推移而扩展，以包含更多金属加工资源，特别适用于压力机制造等。

## 使用铜管

我发现如何焊接铜管的最佳指南是[焊接和钎焊铜管和配件](http://www.copper.org/publications/pub_list/pdf/soldering_brazing_ads.pdf)，直接来自the Copper Development Association, Inc. 

## 待办事项

需要为以下主题添加链接： 

- 钻孔和攻丝，包括磁力钻
- 切割模具外皮铝板
- 去毛刺
- 挤压铝梁
- 精密加工的基础知识
- 切割边刃材料
