mikemag/MonkeyWiki/assets/images/Air_Shears_1.jpg

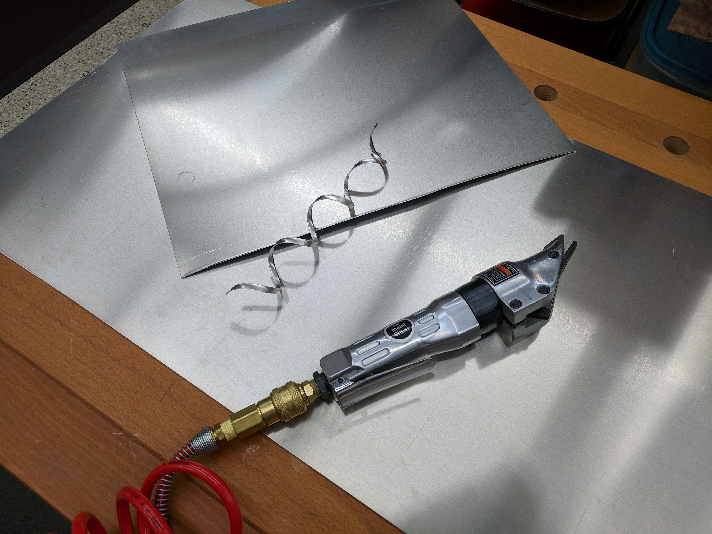
assets/images/Air_Shears_1.jpg
