mikemag/MonkeyWiki/assets/images/Air_Shears_2.jpg

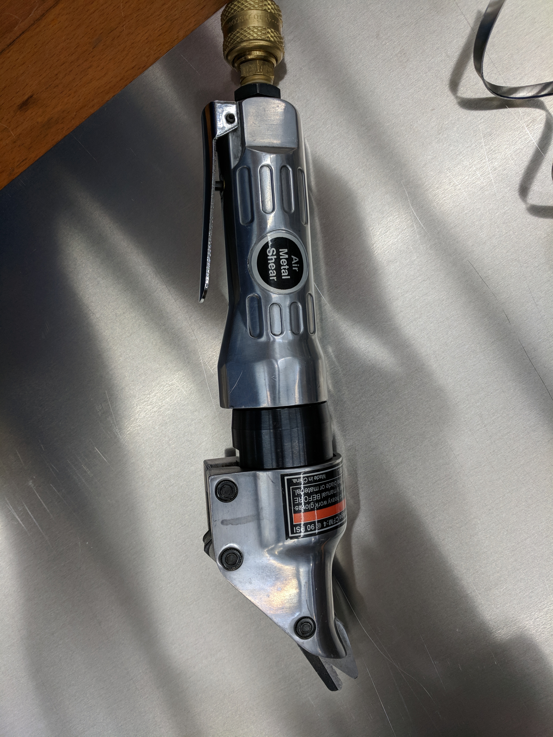
assets/images/Air_Shears_2.jpg
