mikemag/MonkeyWiki/assets/images/Air_Shears_3.jpg

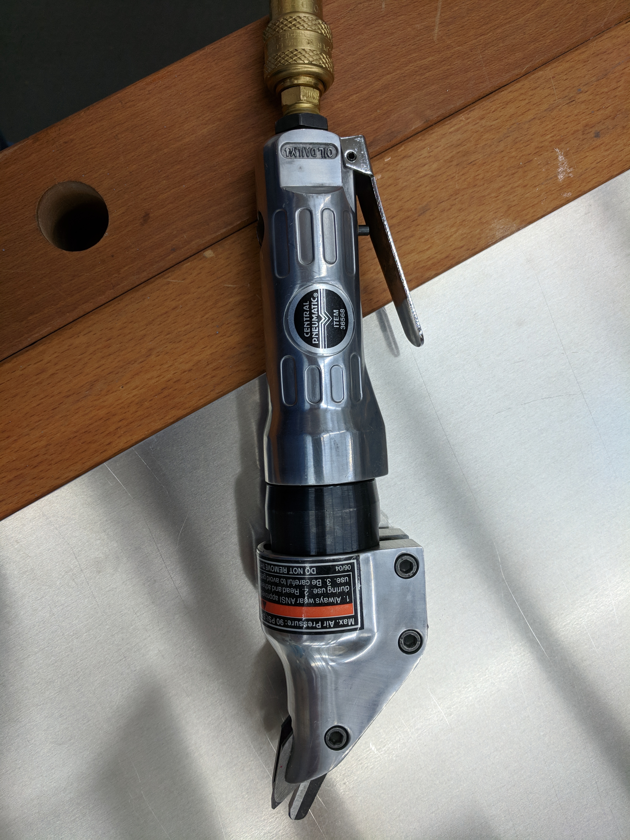
assets/images/Air_Shears_3.jpg
