mikemag/MonkeyWiki/assets/images/BaseGrinder.JPG

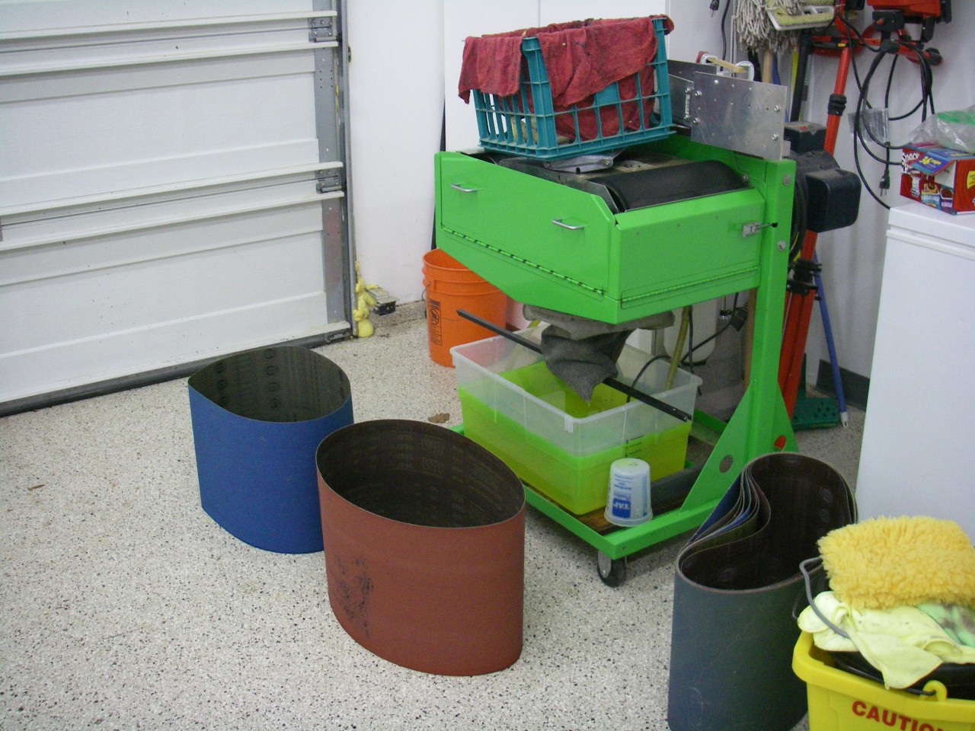
assets/images/BaseGrinder.JPG
