mikemag/MonkeyWiki/assets/images/Board_2018.jpg

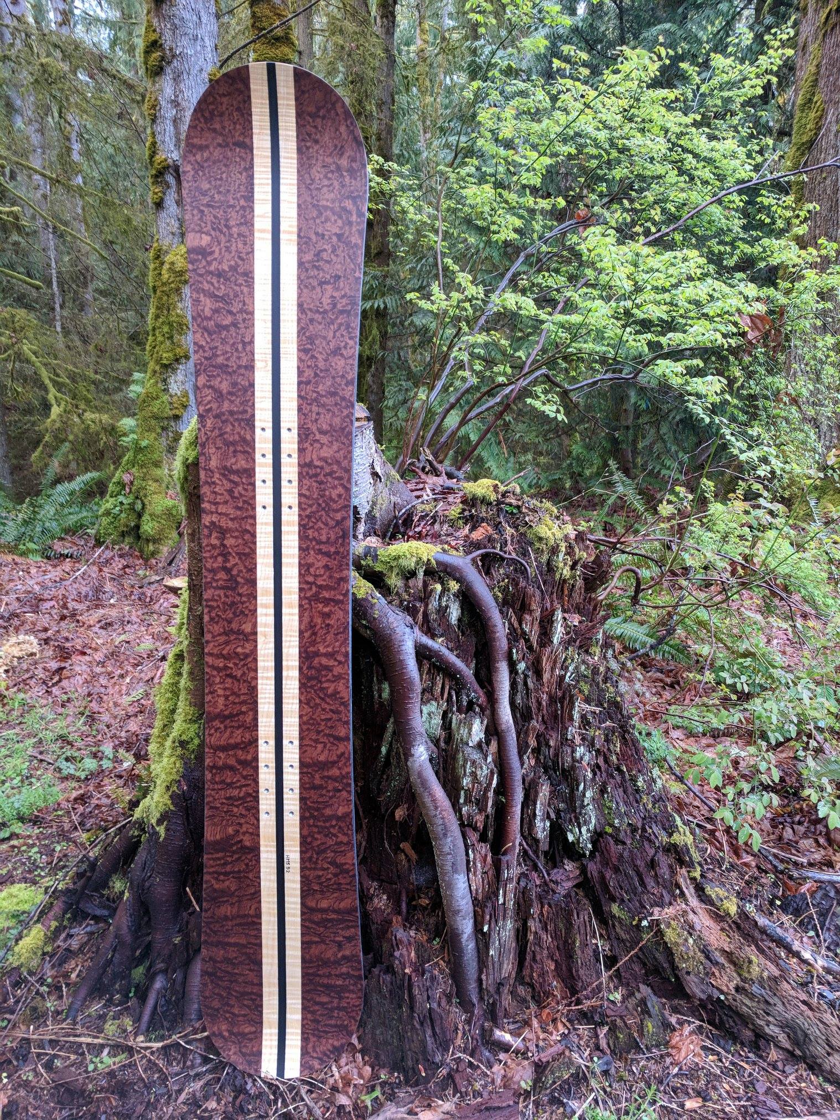
assets/images/Board_2018.jpg
