mikemag/MonkeyWiki/assets/images/Board_Trimmed.JPG

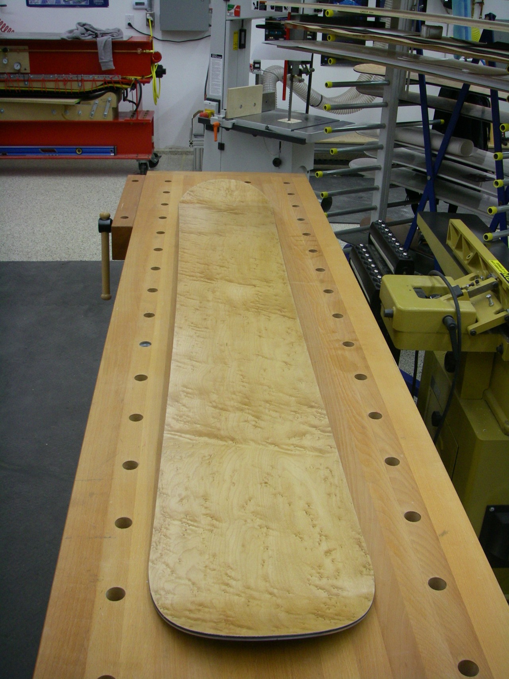
assets/images/Board_Trimmed.JPG
