mikemag/MonkeyWiki/assets/images/Checklist.jpg

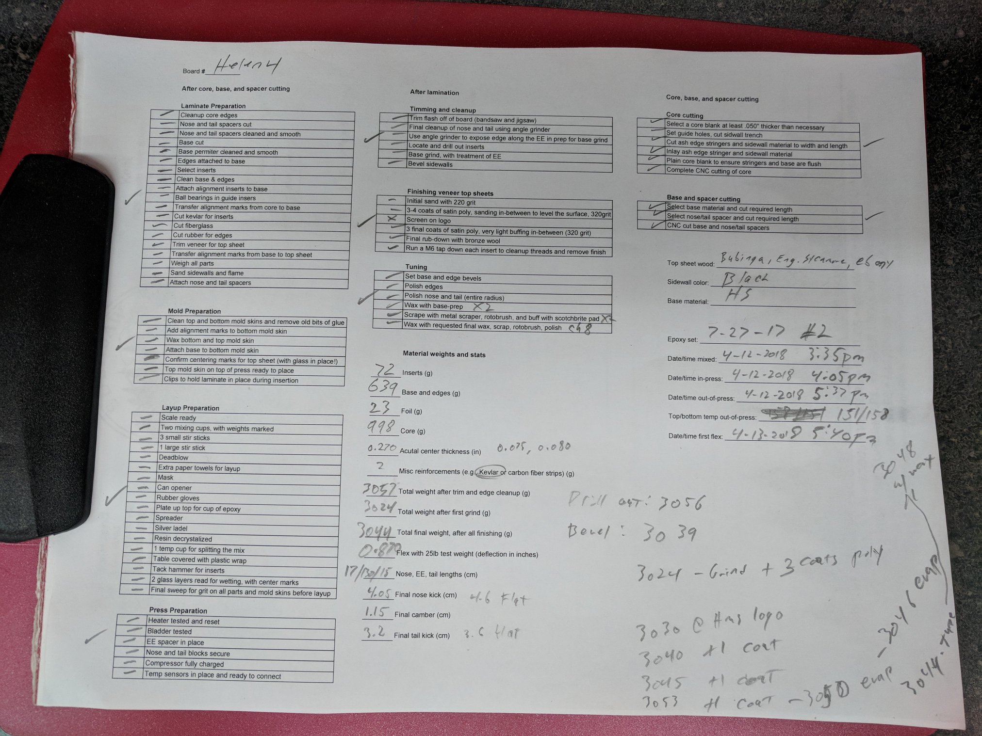
assets/images/Checklist.jpg
