mikemag/MonkeyWiki/assets/images/CleanupInserts1.JPG

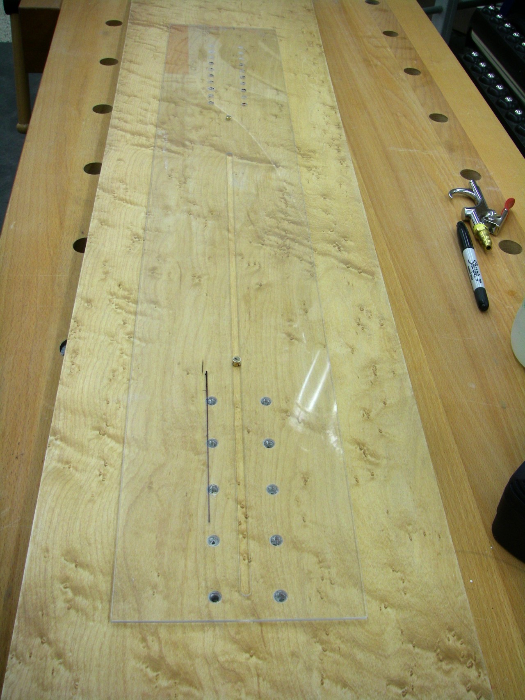
assets/images/CleanupInserts1.JPG
