mikemag/MonkeyWiki/assets/images/CleanupInserts2.JPG

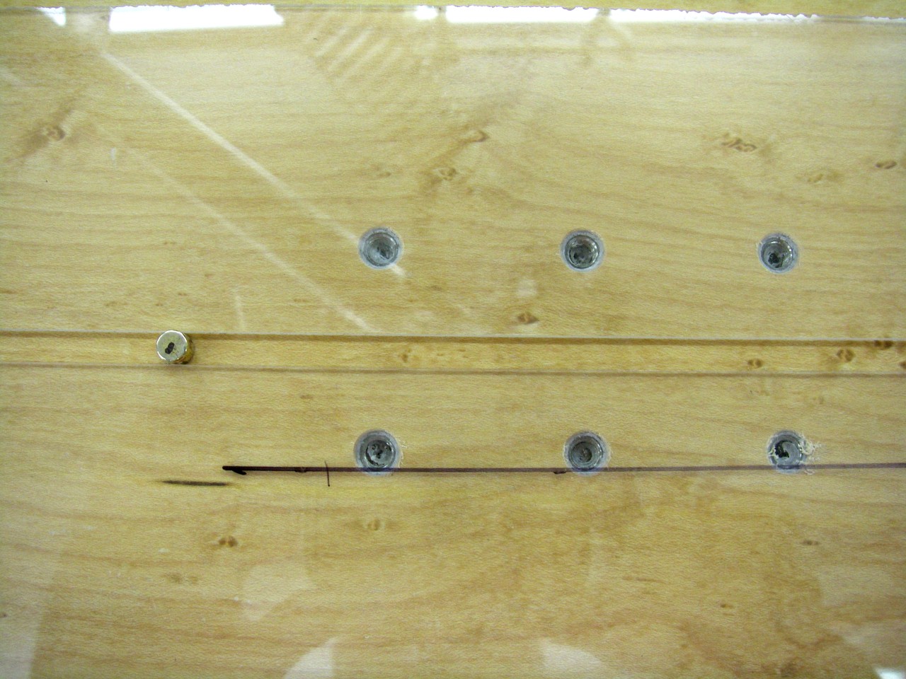
assets/images/CleanupInserts2.JPG
