mikemag/MonkeyWiki/assets/images/CleanupInserts3.JPG

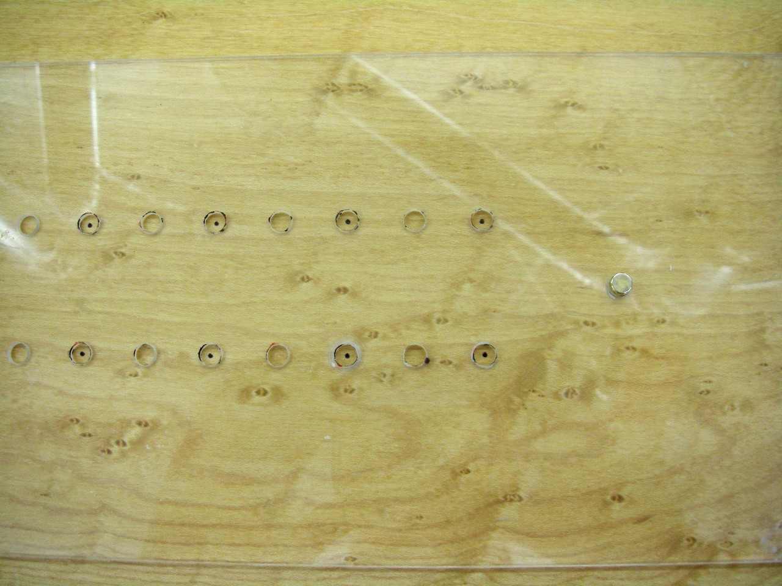
assets/images/CleanupInserts3.JPG
