mikemag/MonkeyWiki/assets/images/CleanupInserts4.JPG

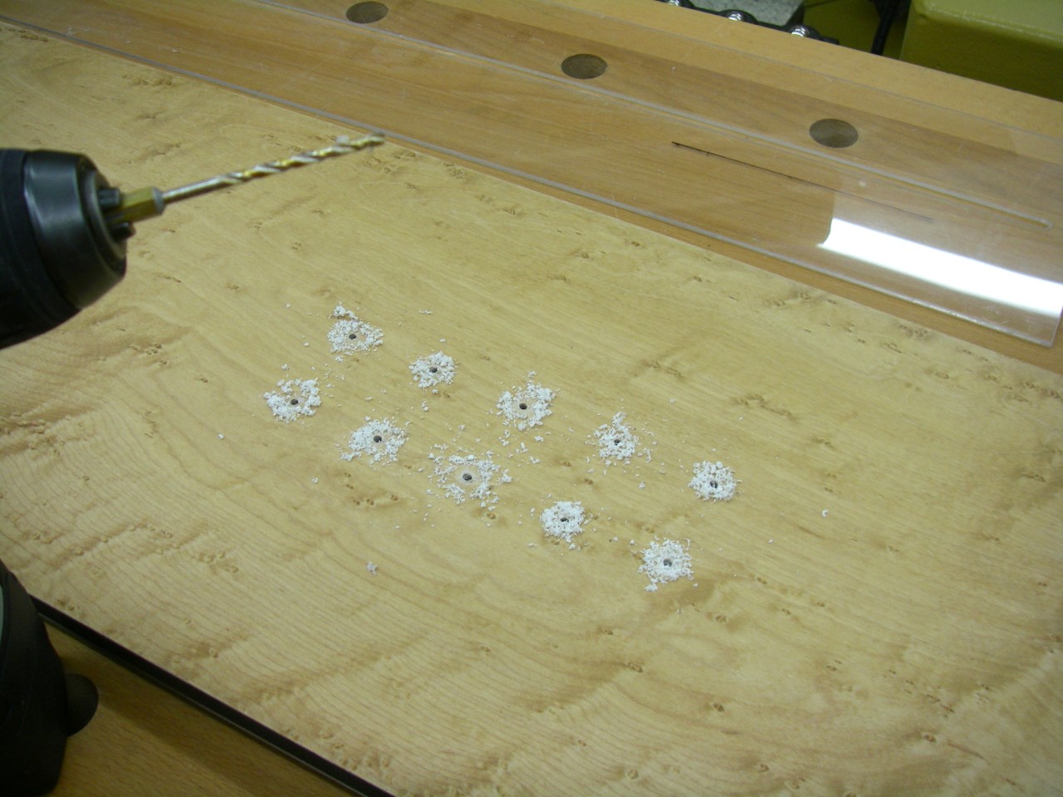
assets/images/CleanupInserts4.JPG
