mikemag/MonkeyWiki/assets/images/CleanupInserts5.JPG

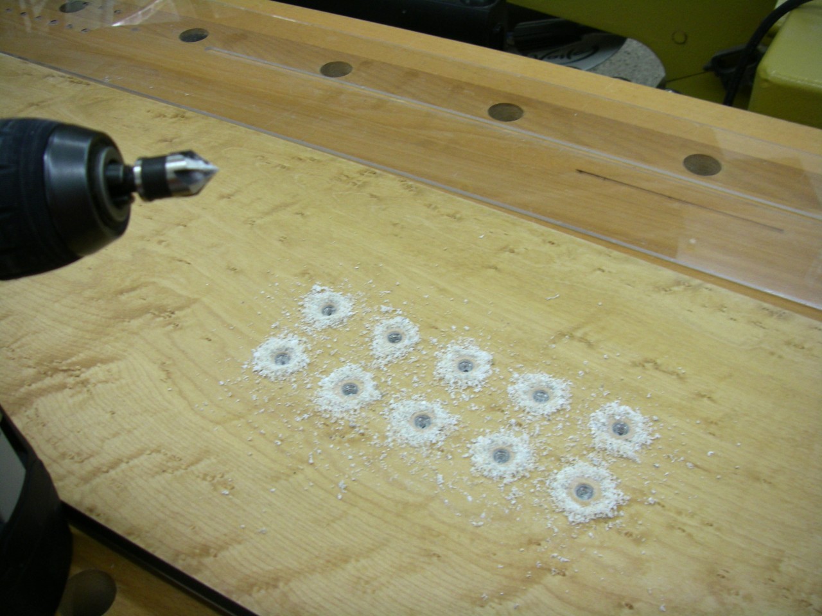
assets/images/CleanupInserts5.JPG
