mikemag/MonkeyWiki/assets/images/CleanupInserts6.JPG

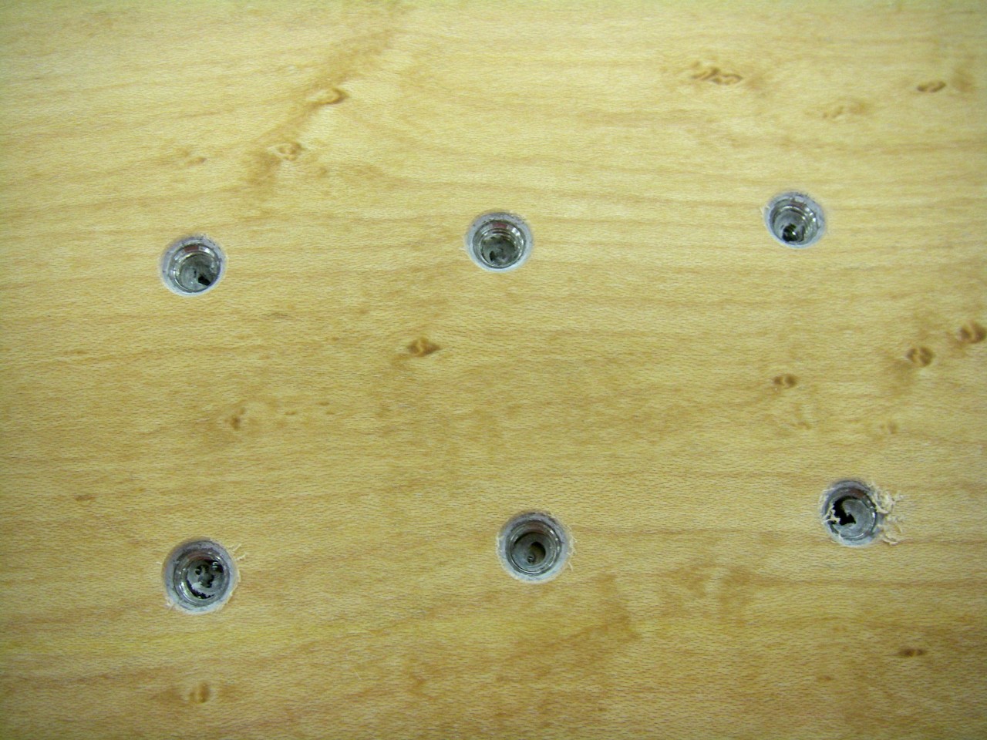
assets/images/CleanupInserts6.JPG
