mikemag/MonkeyWiki/assets/images/CleanupInserts7.JPG

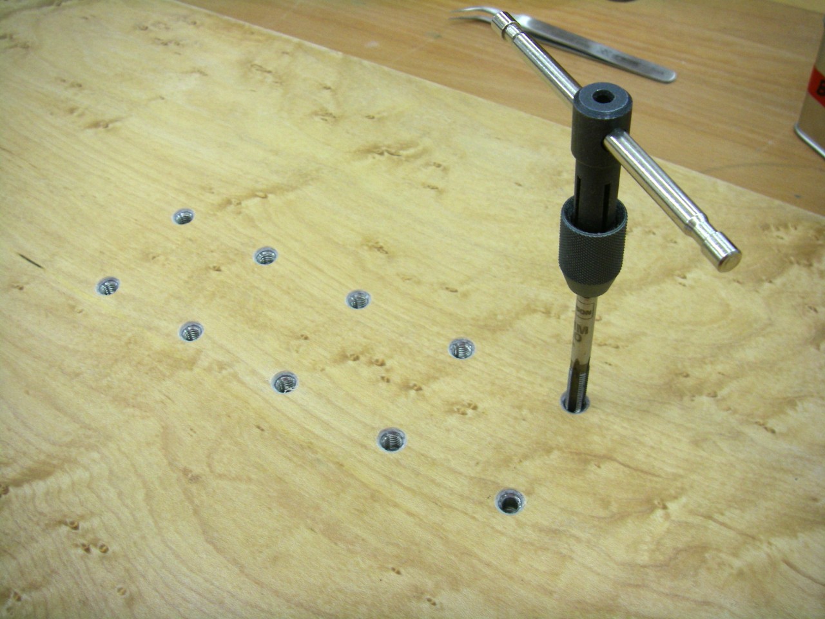
assets/images/CleanupInserts7.JPG
