mikemag/MonkeyWiki/assets/images/CleanupInserts8.JPG

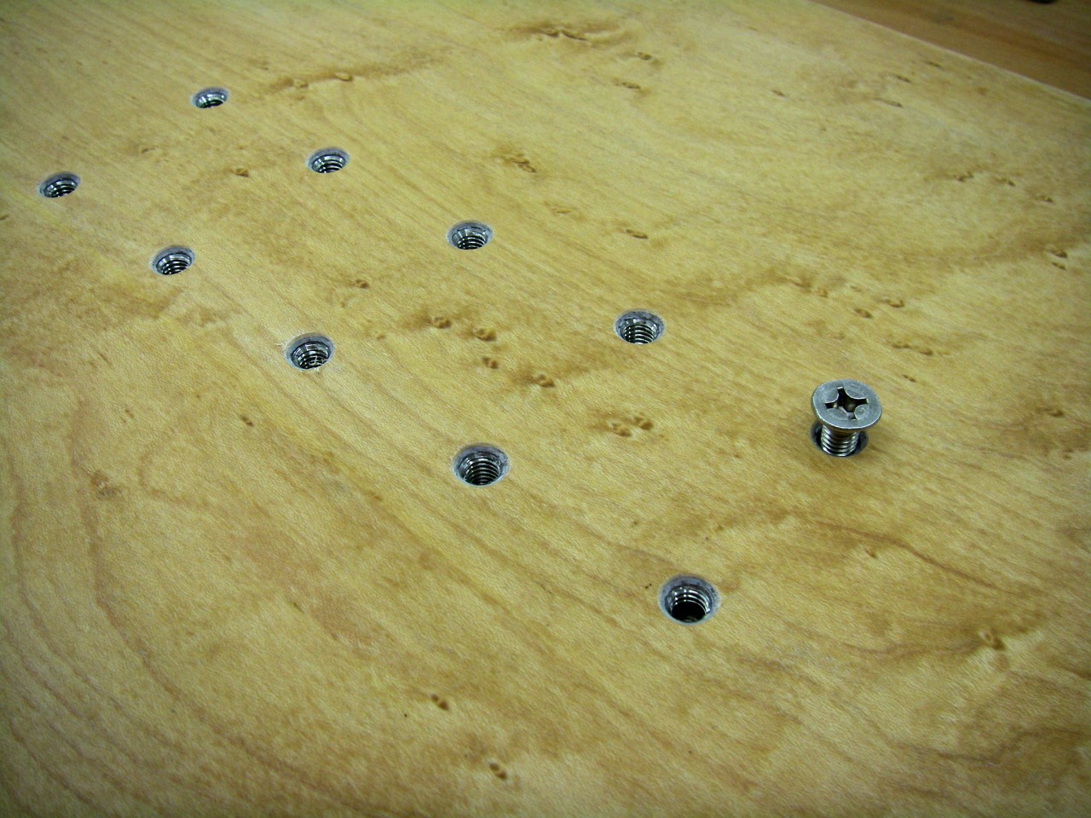
assets/images/CleanupInserts8.JPG
