mikemag/MonkeyWiki/assets/images/CNC1.JPG

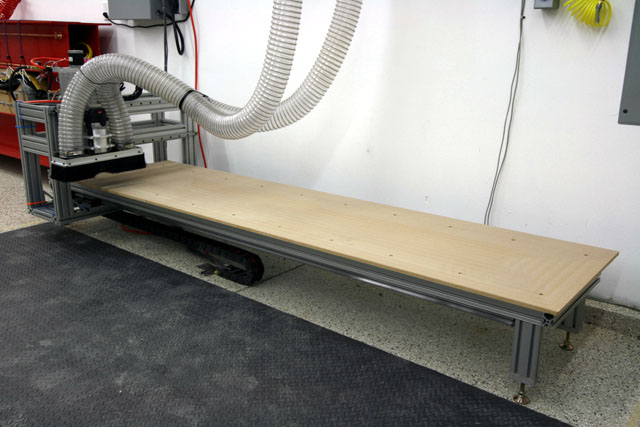
assets/images/CNC1.JPG
