mikemag/MonkeyWiki/assets/images/CNC2.JPG

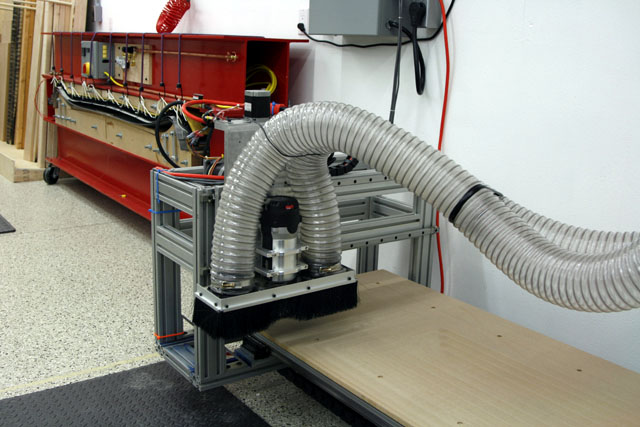
assets/images/CNC2.JPG
