mikemag/MonkeyWiki/assets/images/CNC3.JPG

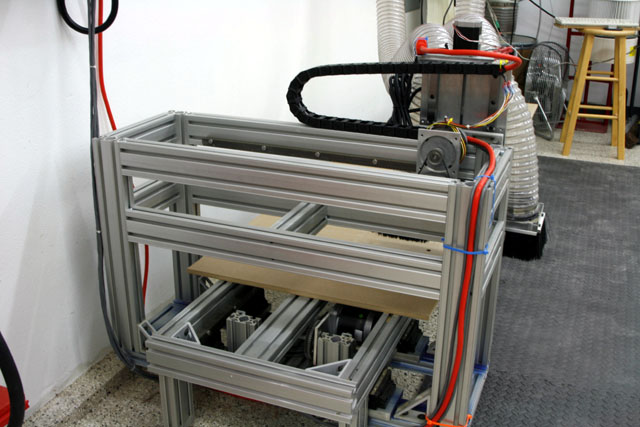
assets/images/CNC3.JPG
