mikemag/MonkeyWiki/assets/images/CNC4.JPG

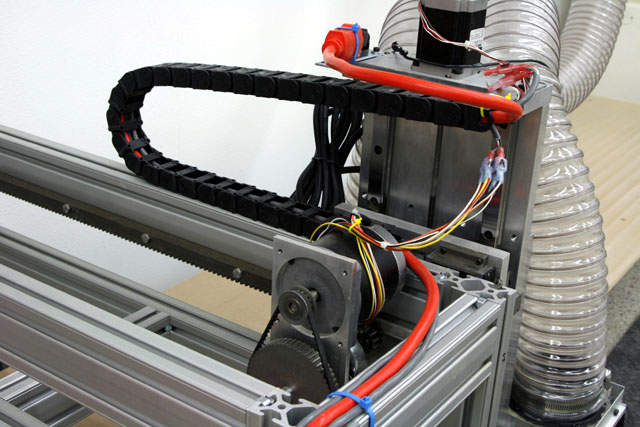
assets/images/CNC4.JPG
