mikemag/MonkeyWiki/assets/images/CNC5.JPG

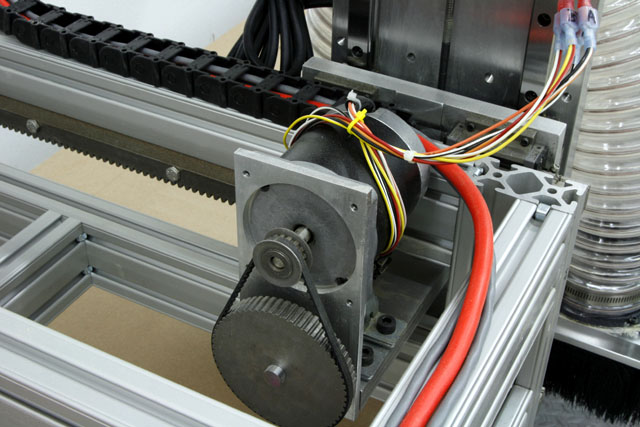
assets/images/CNC5.JPG
