mikemag/MonkeyWiki/assets/images/CNC6.JPG

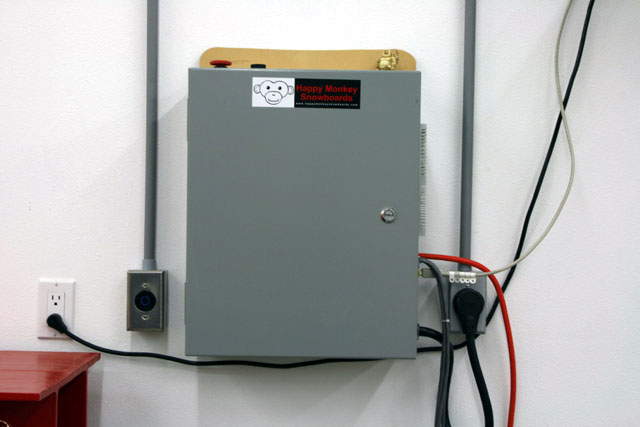
assets/images/CNC6.JPG
