mikemag/MonkeyWiki/assets/images/CNC7.JPG

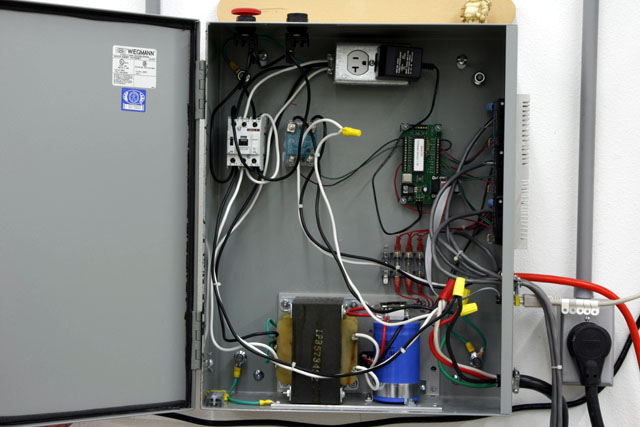
assets/images/CNC7.JPG
