mikemag/MonkeyWiki/assets/images/CNC_Head1.jpg

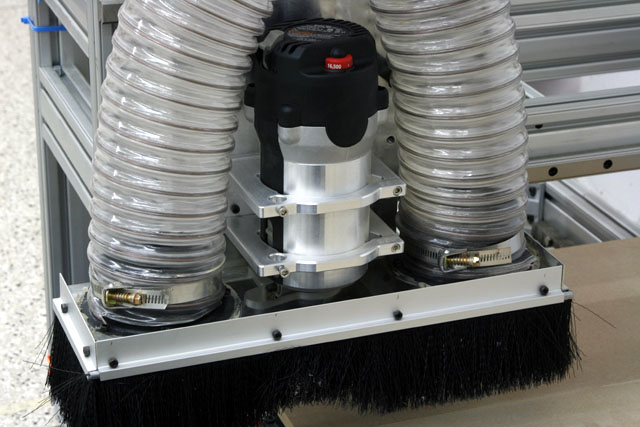
assets/images/CNC_Head1.jpg
