mikemag/MonkeyWiki/assets/images/Core_Wood.JPG

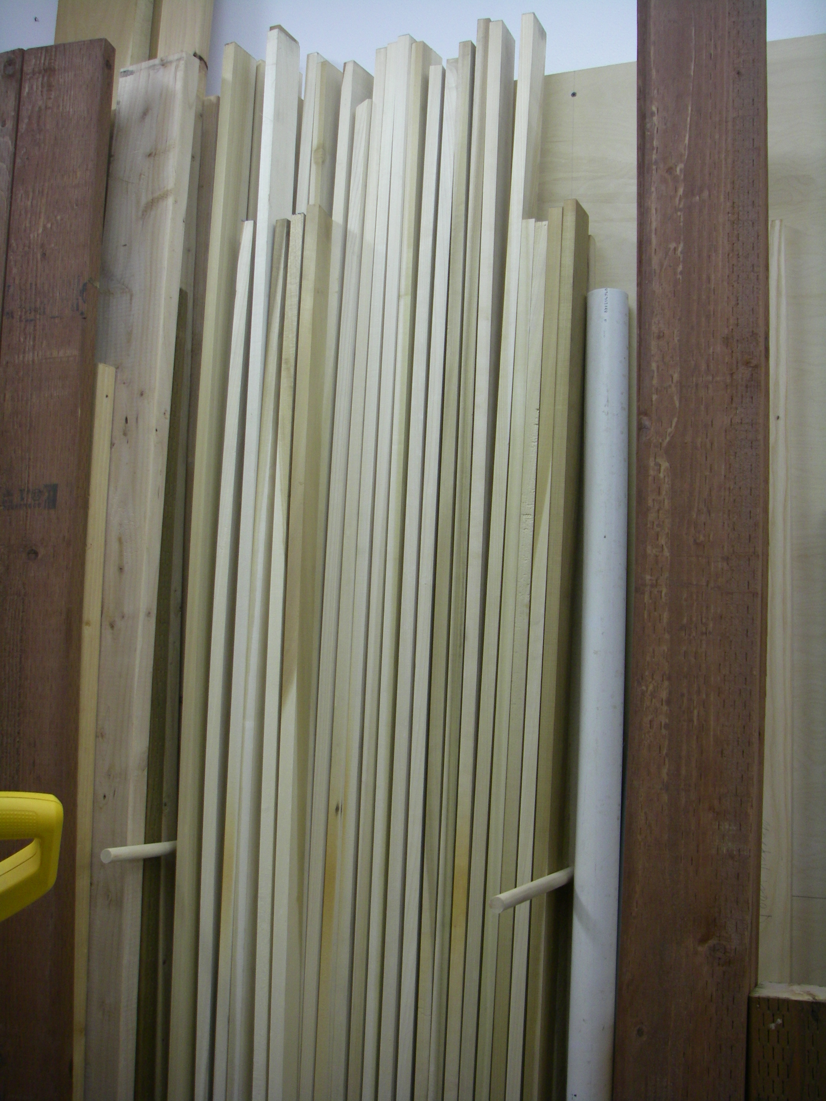
assets/images/Core_Wood.JPG
