mikemag/MonkeyWiki/assets/images/Core_Wood_Blemish1.JPG

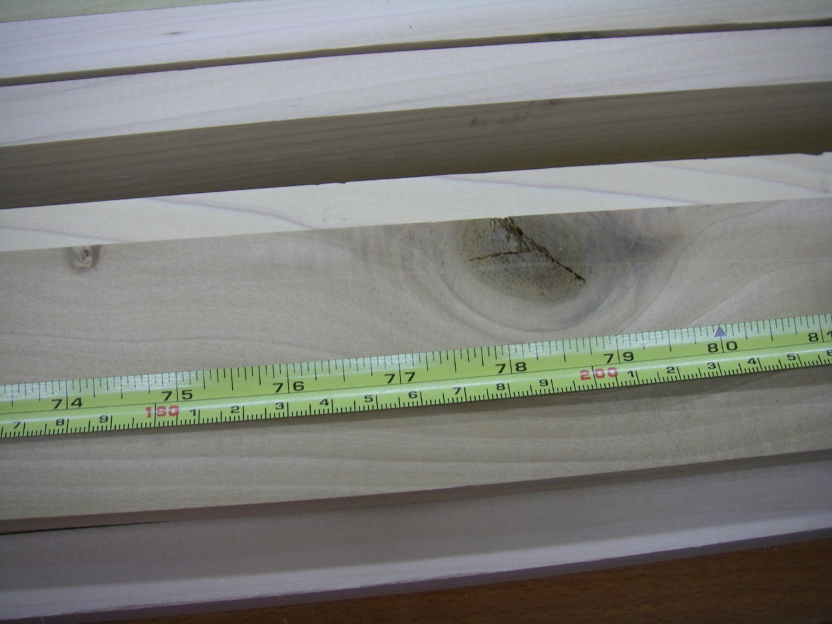
assets/images/Core_Wood_Blemish1.JPG
