mikemag/MonkeyWiki/assets/images/Core_Wood_Clear.JPG

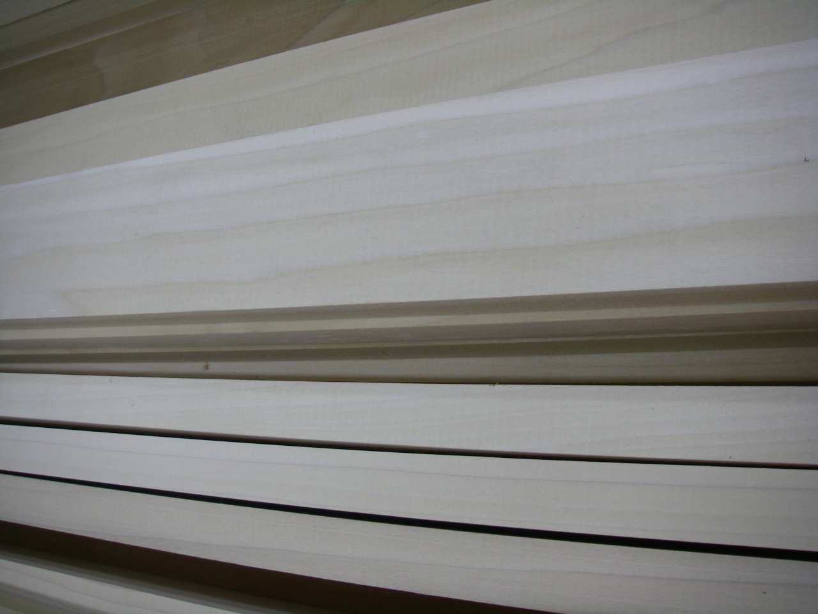
assets/images/Core_Wood_Clear.JPG
