mikemag/MonkeyWiki/assets/images/Core_Wood_Drying1.JPG

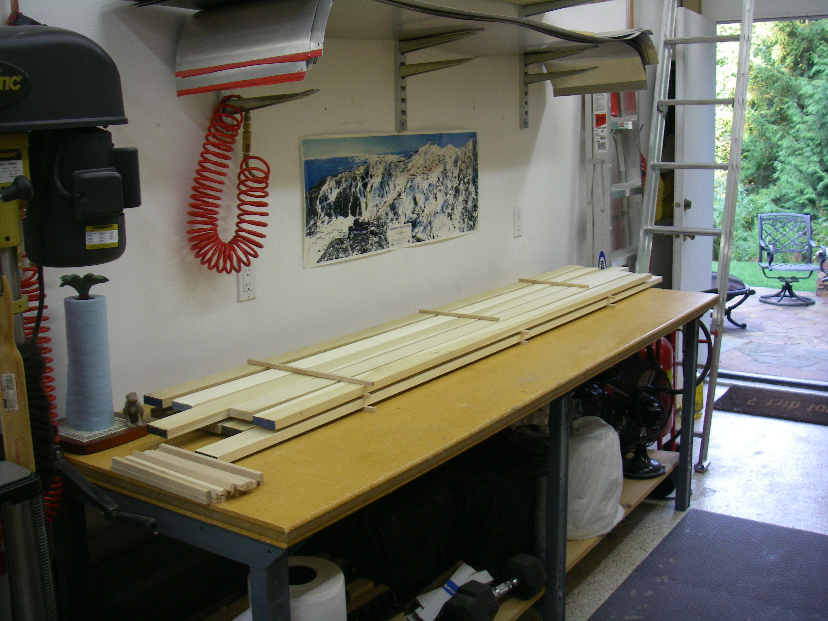
assets/images/Core_Wood_Drying1.JPG
