mikemag/MonkeyWiki/assets/images/Core_Wood_Drying2.JPG

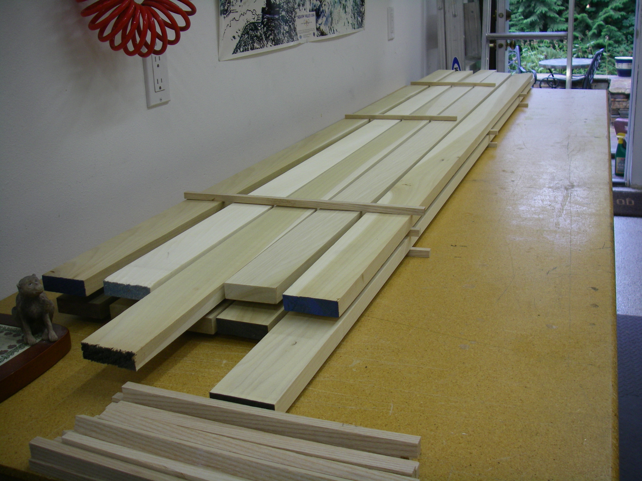
assets/images/Core_Wood_Drying2.JPG
