mikemag/MonkeyWiki/assets/images/Core_Wood_Drying3.JPG

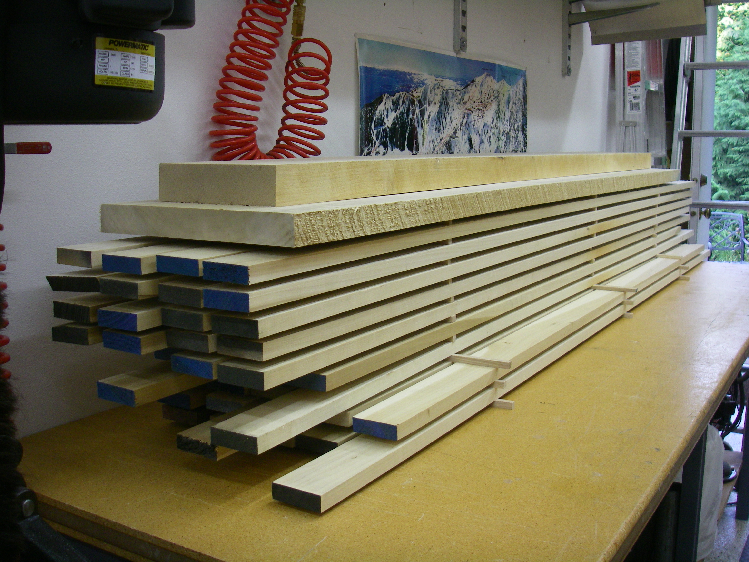
assets/images/Core_Wood_Drying3.JPG
