mikemag/MonkeyWiki/assets/images/CoreBlank_InlayCleanup1.JPG

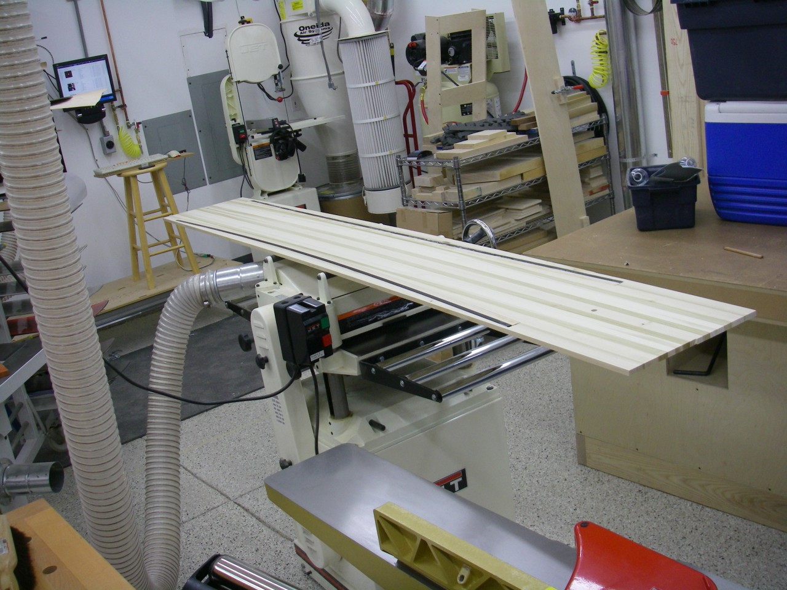
assets/images/CoreBlank_InlayCleanup1.JPG
