mikemag/MonkeyWiki/assets/images/CoreBlank_InlayCleanup2.JPG

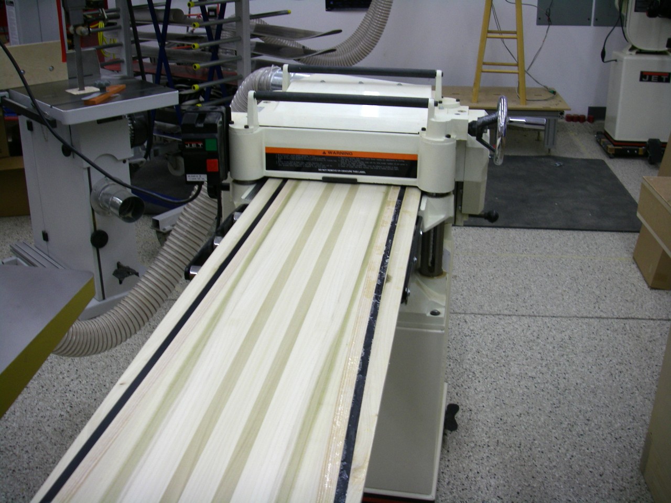
assets/images/CoreBlank_InlayCleanup2.JPG
