mikemag/MonkeyWiki/assets/images/CoreBlank_InlayCleanup3.JPG

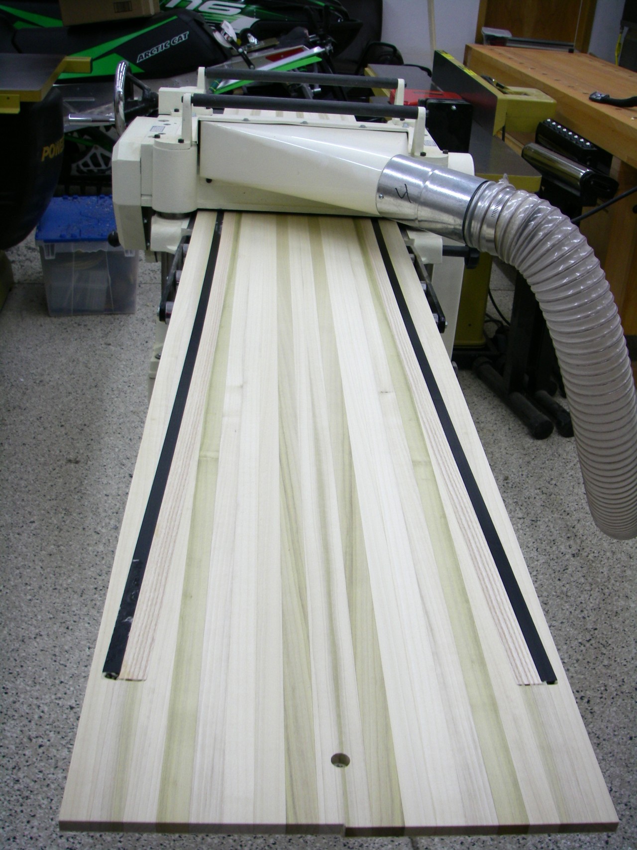
assets/images/CoreBlank_InlayCleanup3.JPG
