mikemag/MonkeyWiki/assets/images/CoreBlank_InlayCleanup4.JPG

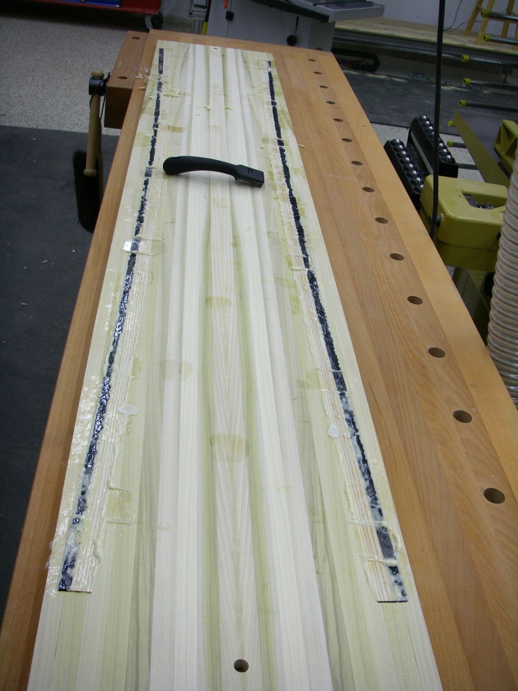
assets/images/CoreBlank_InlayCleanup4.JPG
