mikemag/MonkeyWiki/assets/images/CoreBlank_InlayCleanup5.JPG

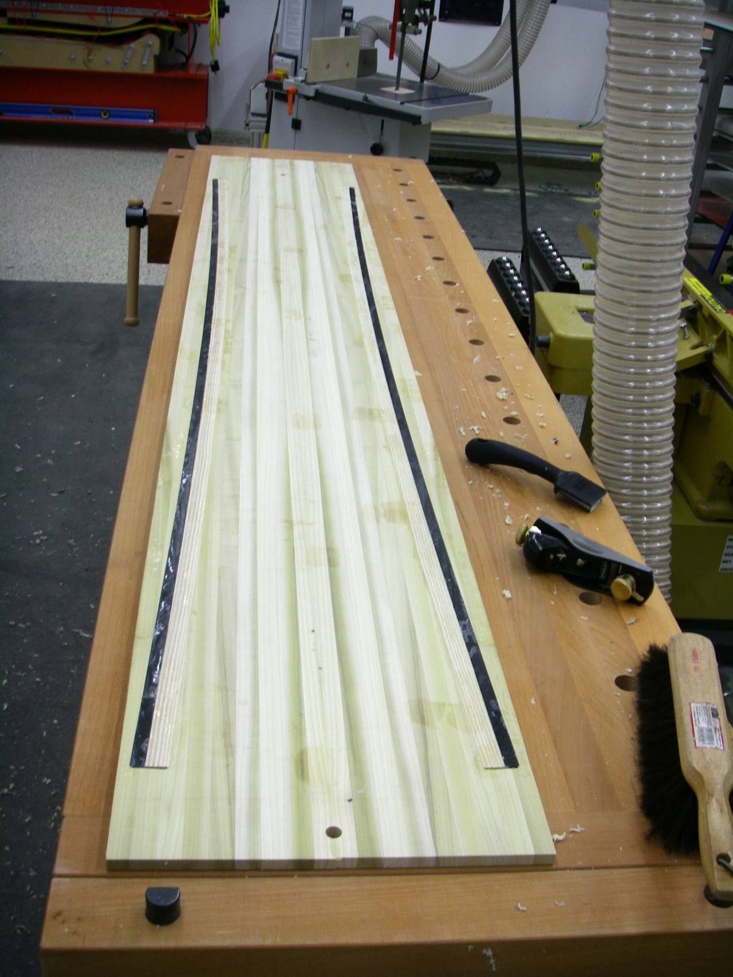
assets/images/CoreBlank_InlayCleanup5.JPG
