mikemag/MonkeyWiki/assets/images/CoreBlank_InlayCleanup6.JPG

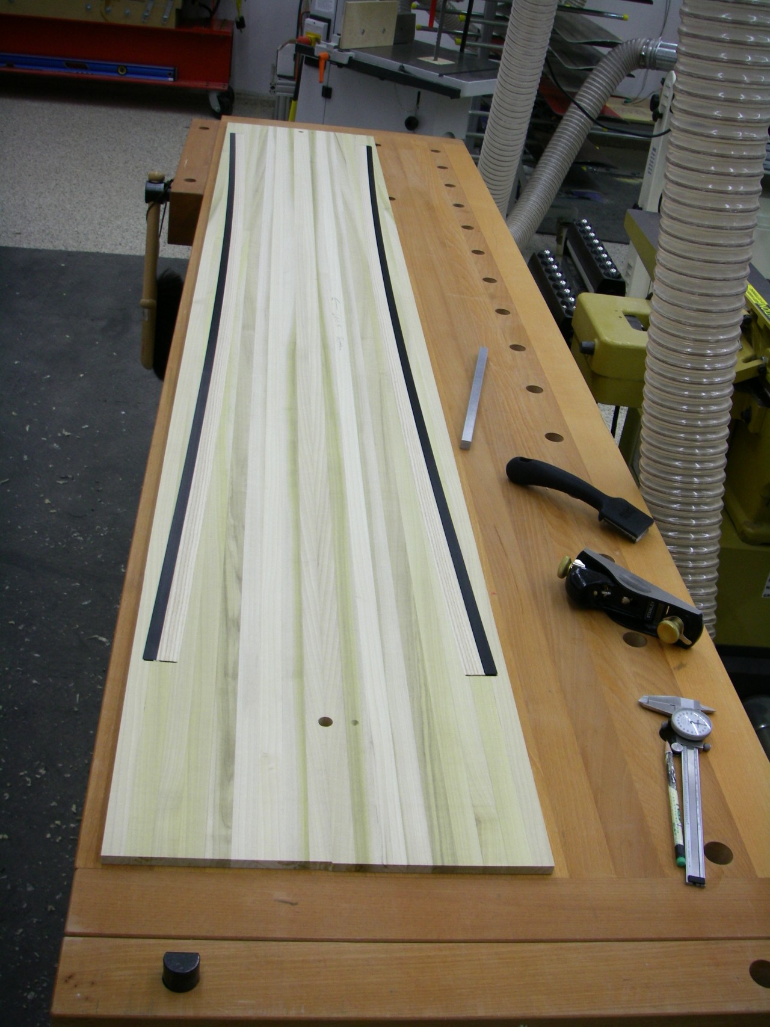
assets/images/CoreBlank_InlayCleanup6.JPG
