mikemag/MonkeyWiki/assets/images/CoreBlank_InlayCleanup7.JPG

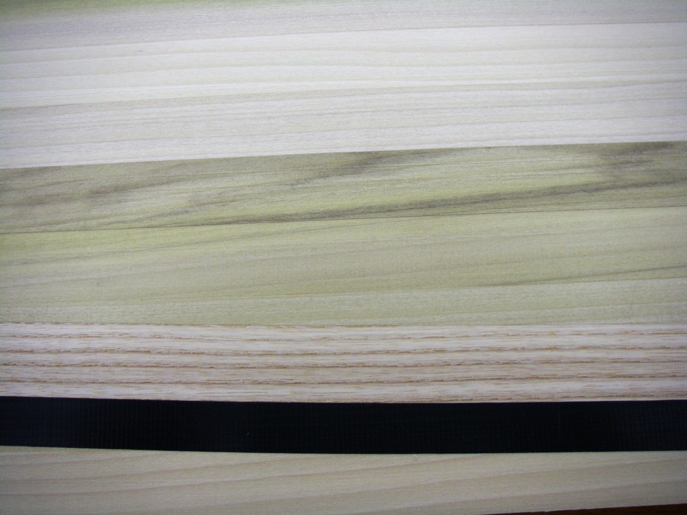
assets/images/CoreBlank_InlayCleanup7.JPG
