mikemag/MonkeyWiki/assets/images/CoreBlank_InlayCleanup8.JPG

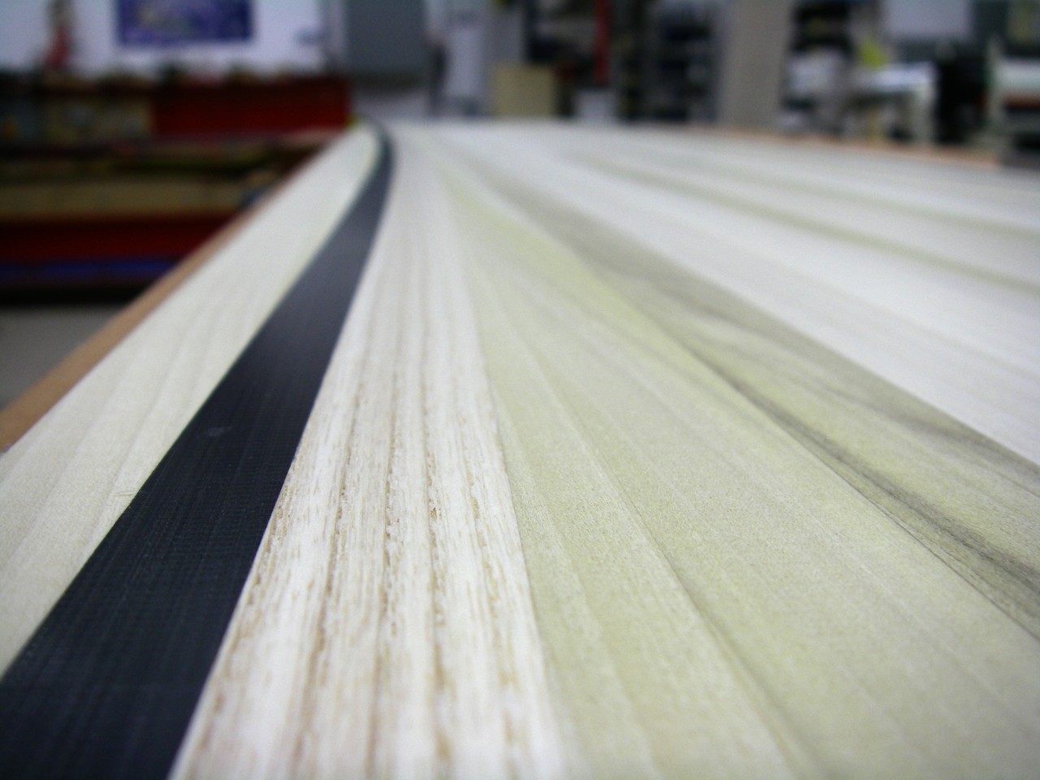
assets/images/CoreBlank_InlayCleanup8.JPG
