mikemag/MonkeyWiki/assets/images/CoreBlank_Sidewall1.JPG

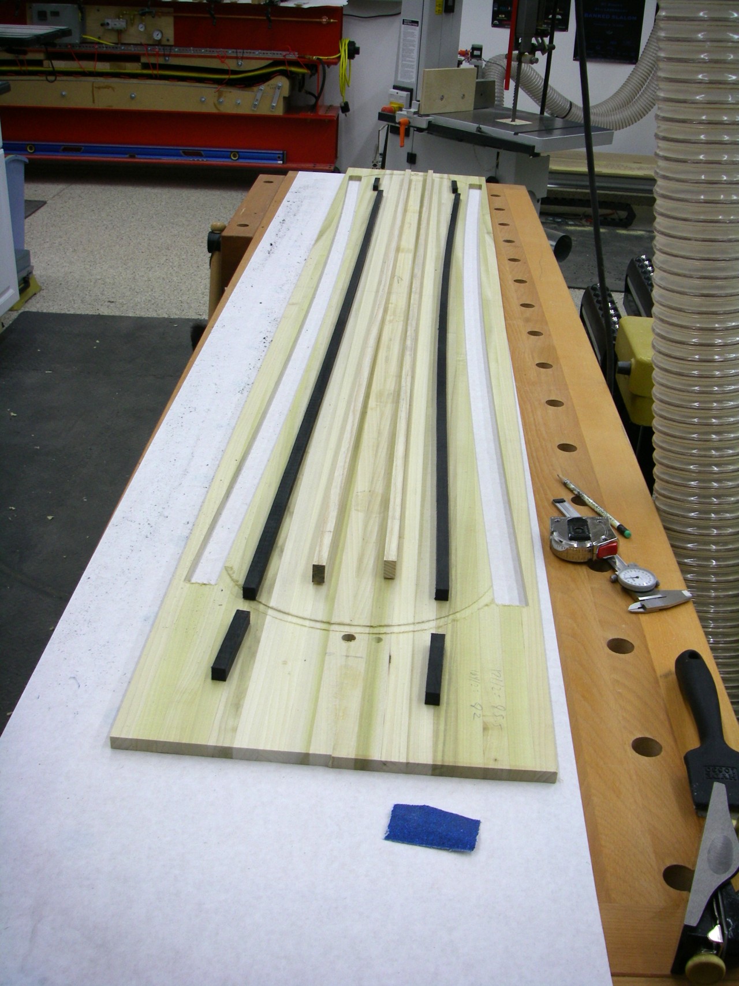
assets/images/CoreBlank_Sidewall1.JPG
