mikemag/MonkeyWiki/assets/images/CoreBlank_Sidewall2.JPG

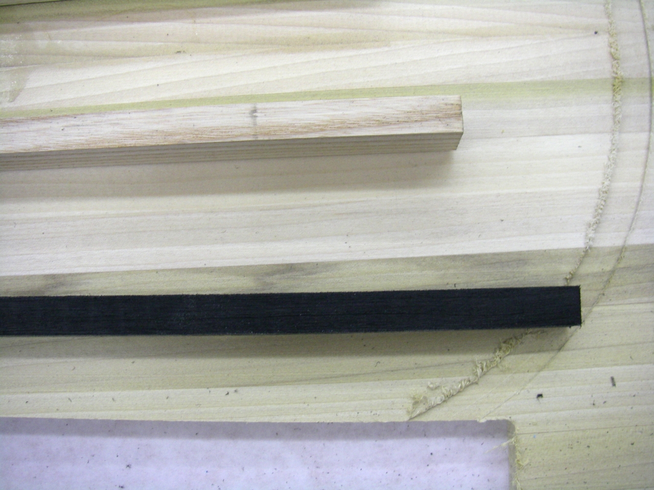
assets/images/CoreBlank_Sidewall2.JPG
