mikemag/MonkeyWiki/assets/images/CoreBlank_Sidewall3.JPG

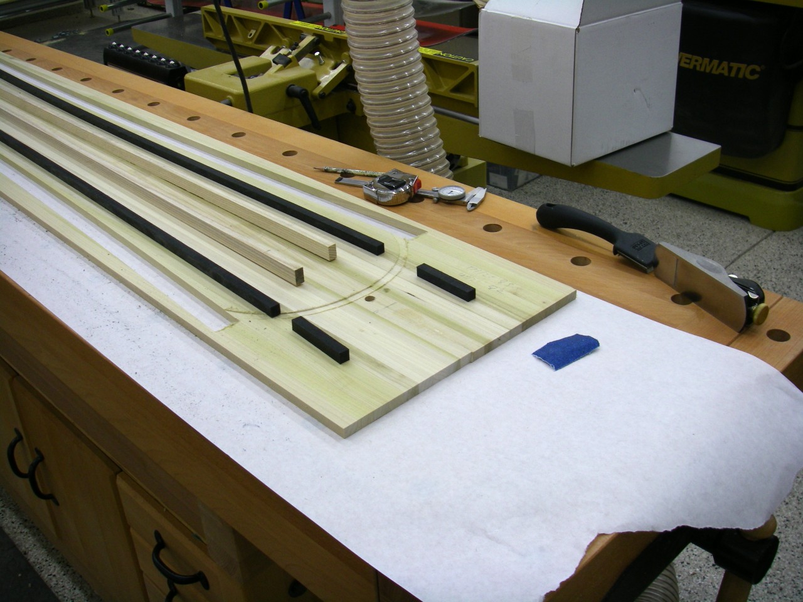
assets/images/CoreBlank_Sidewall3.JPG
