mikemag/MonkeyWiki/assets/images/CoreBlank_Sidewall4.JPG

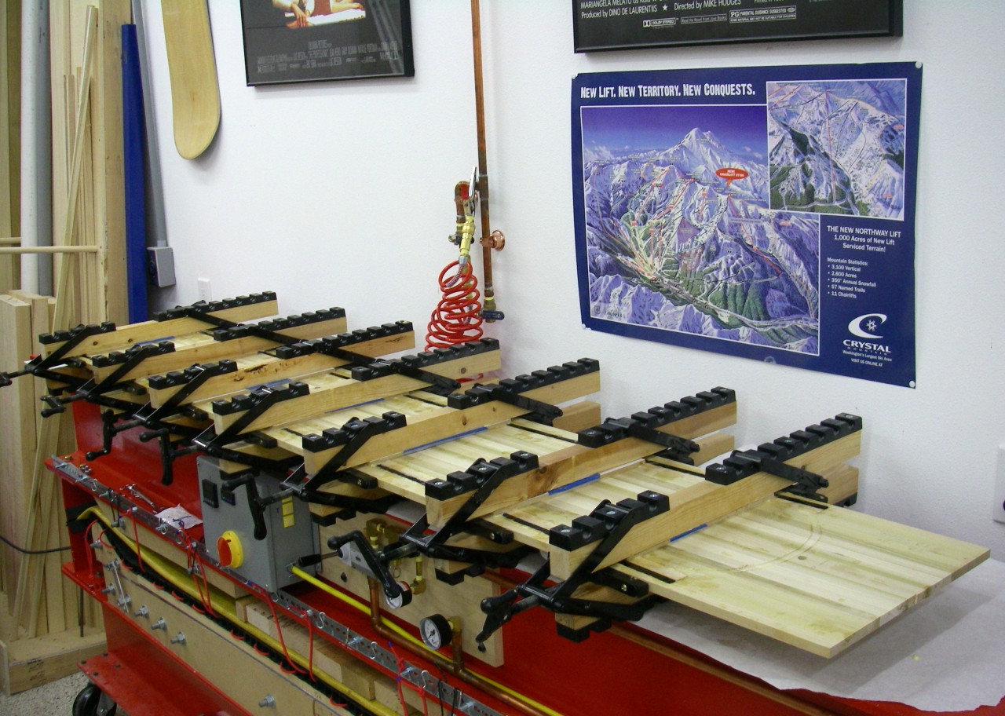
assets/images/CoreBlank_Sidewall4.JPG
