mikemag/MonkeyWiki/assets/images/CoreBlank_Sidewall5.JPG

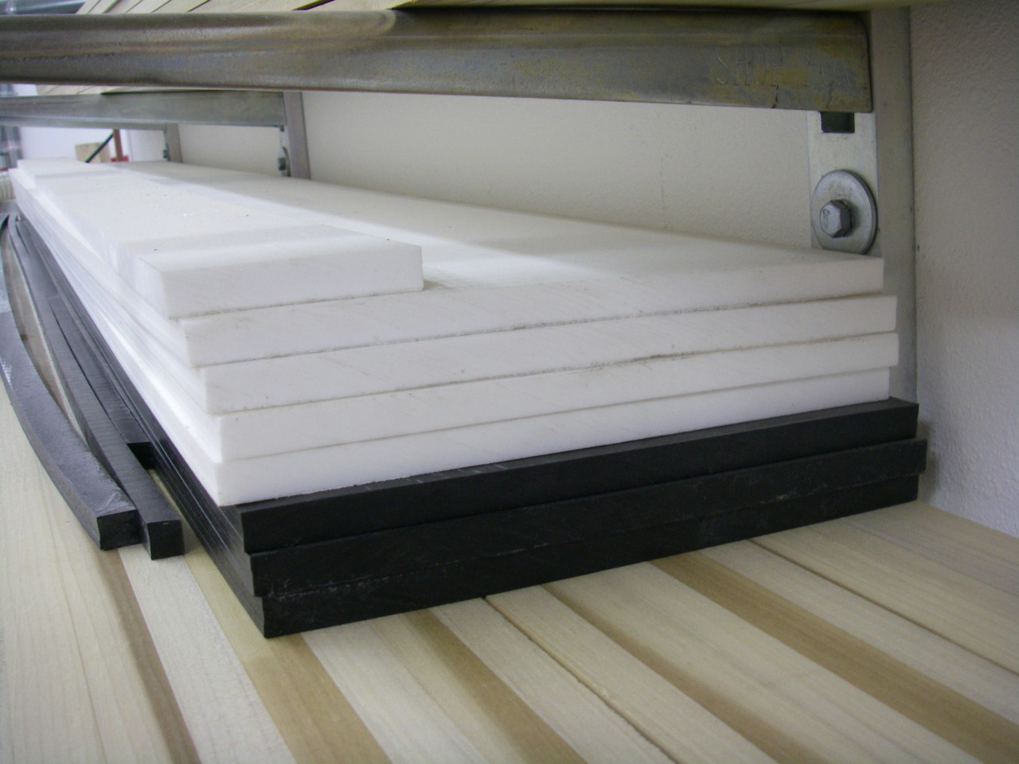
assets/images/CoreBlank_Sidewall5.JPG
