mikemag/MonkeyWiki/assets/images/CoreBlank_SliceJoin2.JPG

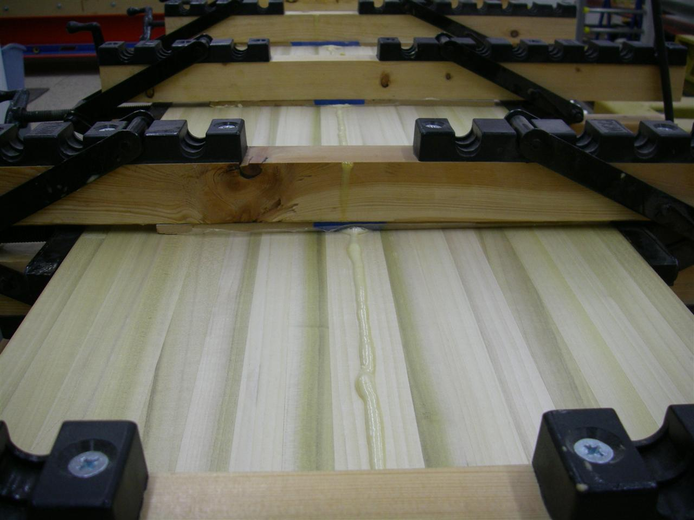
assets/images/CoreBlank_SliceJoin2.JPG
