mikemag/MonkeyWiki/assets/images/CoreBlank_SliceJoin3.JPG

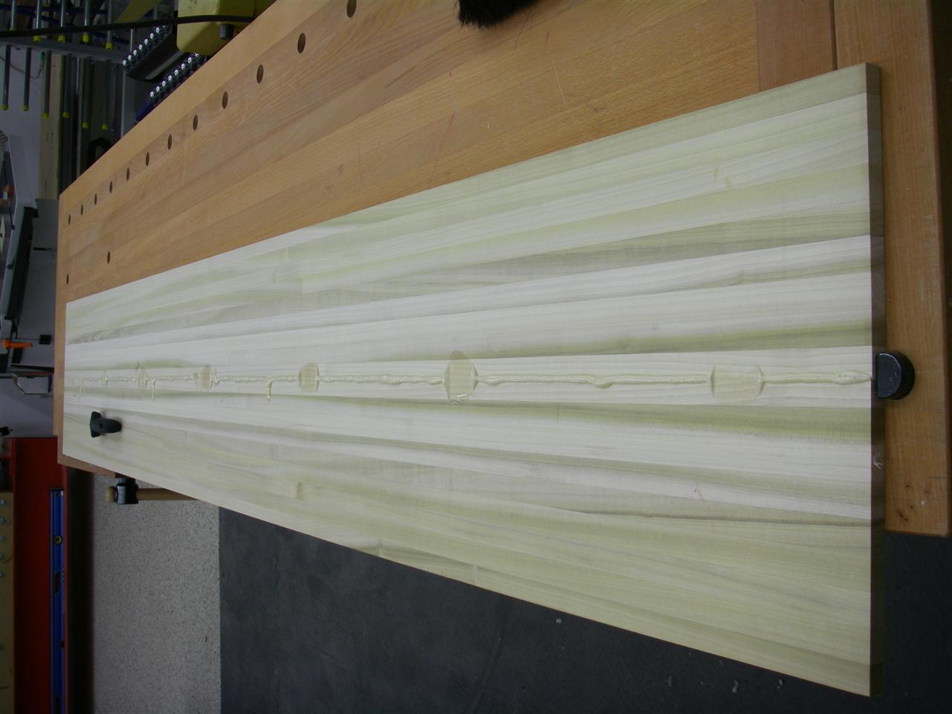
assets/images/CoreBlank_SliceJoin3.JPG
