mikemag/MonkeyWiki/assets/images/CoreShaping_BaseCleanup1.JPG

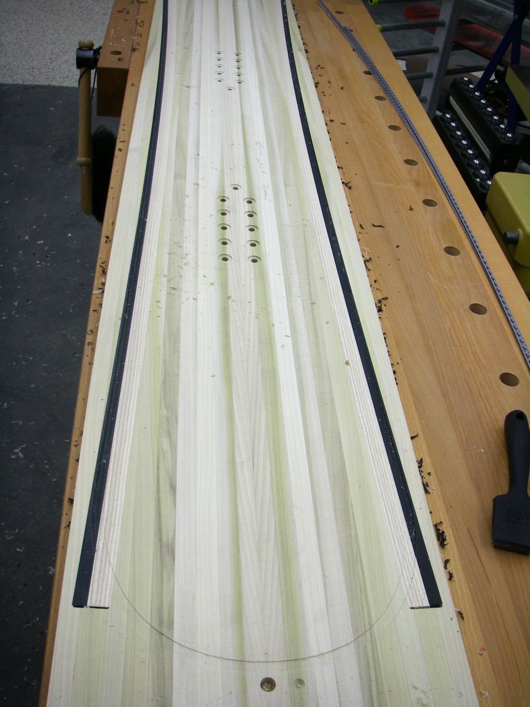
assets/images/CoreShaping_BaseCleanup1.JPG
