mikemag/MonkeyWiki/assets/images/CoreShaping_BaseCleanup2.JPG

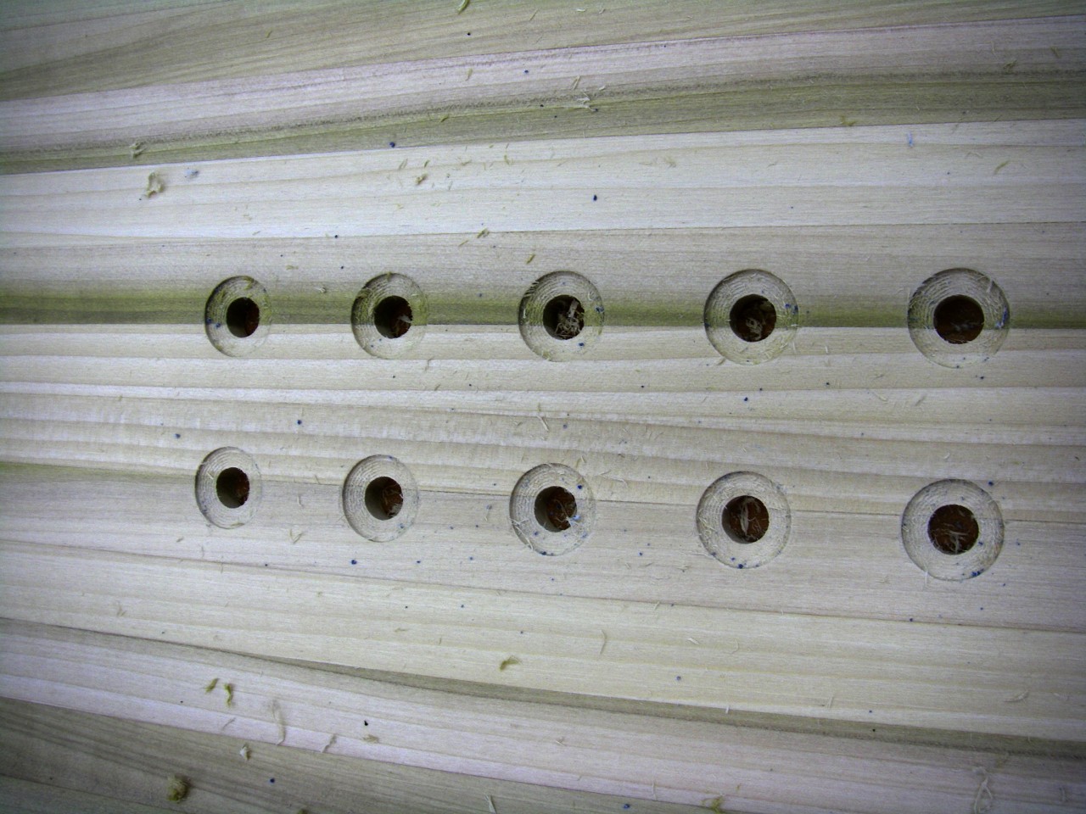
assets/images/CoreShaping_BaseCleanup2.JPG
