mikemag/MonkeyWiki/assets/images/CoreShaping_BaseCleanup3.JPG

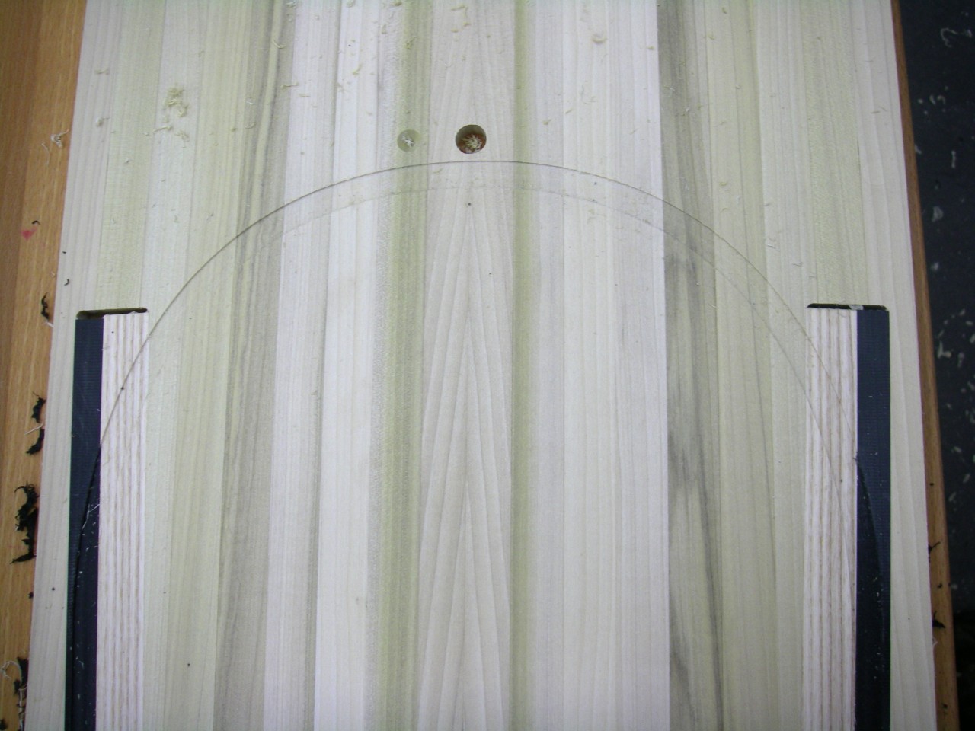
assets/images/CoreShaping_BaseCleanup3.JPG
