mikemag/MonkeyWiki/assets/images/CoreShaping_Cutout1.JPG

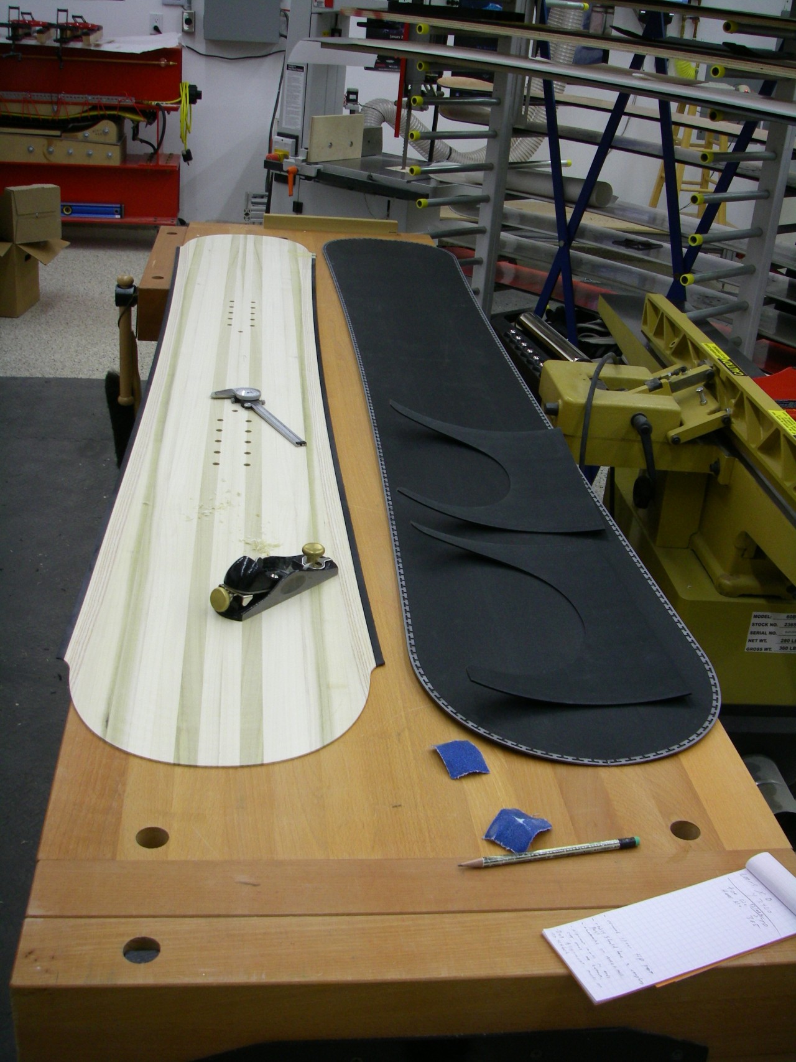
assets/images/CoreShaping_Cutout1.JPG
