mikemag/MonkeyWiki/assets/images/CoreShaping_Cutout2.JPG

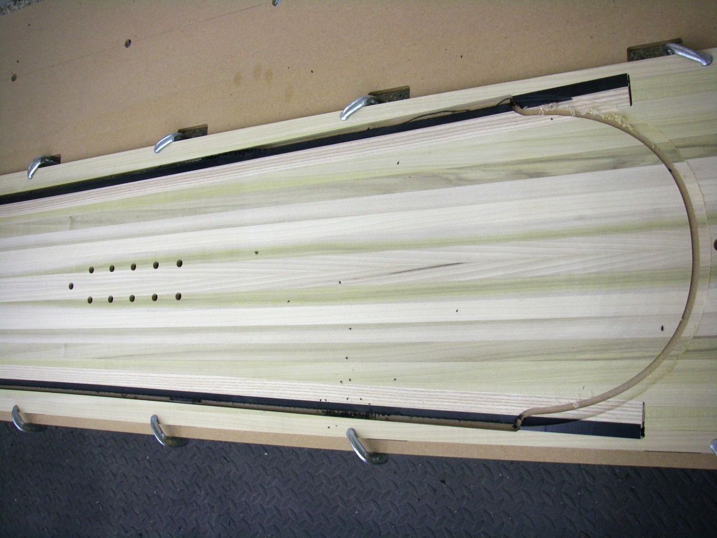
assets/images/CoreShaping_Cutout2.JPG
