mikemag/MonkeyWiki/assets/images/CoreShaping_Cutout3.JPG

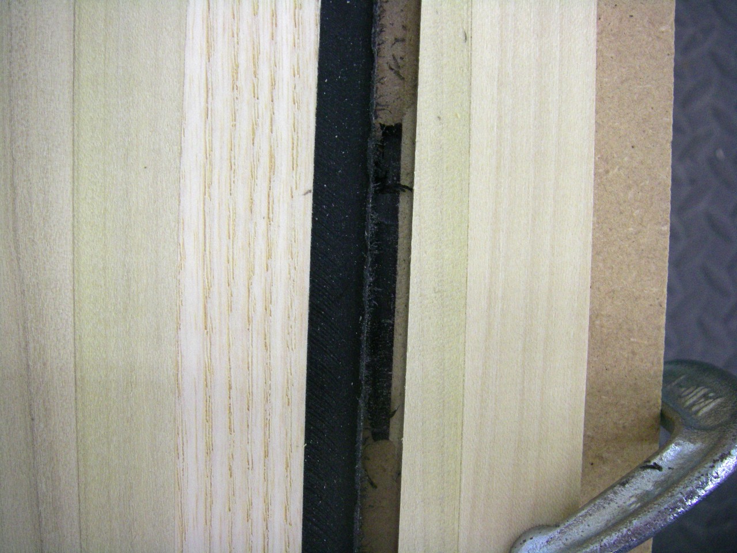
assets/images/CoreShaping_Cutout3.JPG
