mikemag/MonkeyWiki/assets/images/CoreShaping_Cutout4.JPG

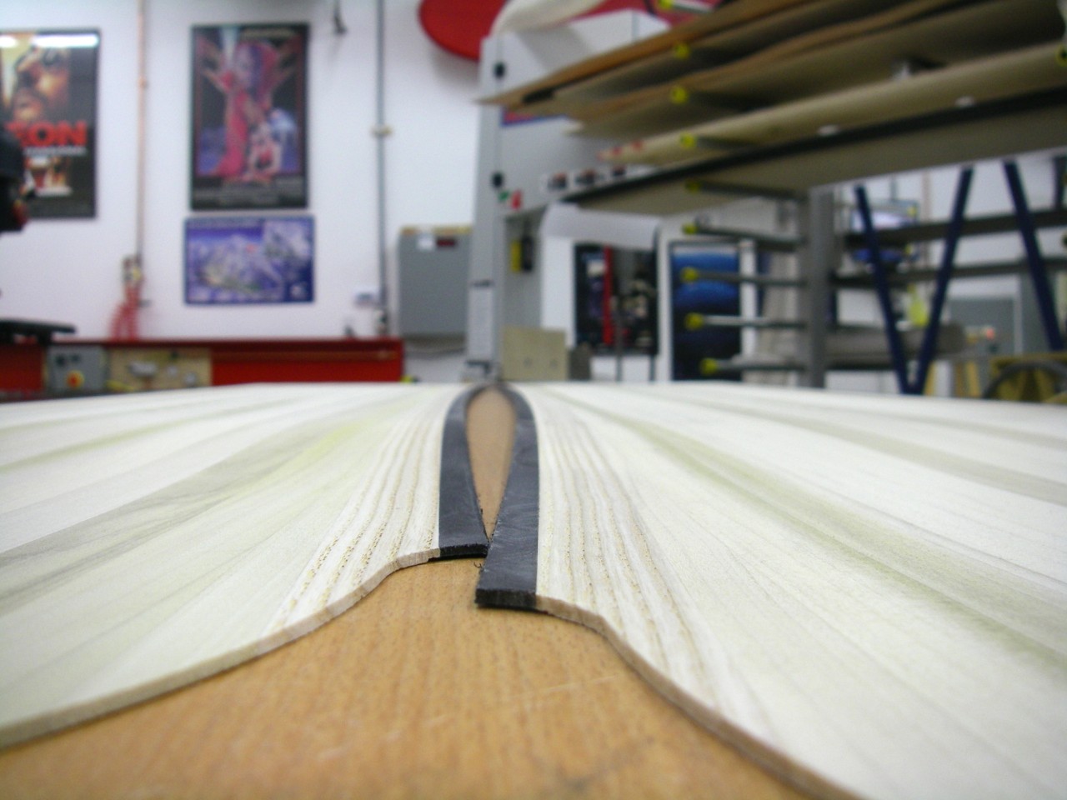
assets/images/CoreShaping_Cutout4.JPG
