mikemag/MonkeyWiki/assets/images/CoreShaping_Edge1.JPG

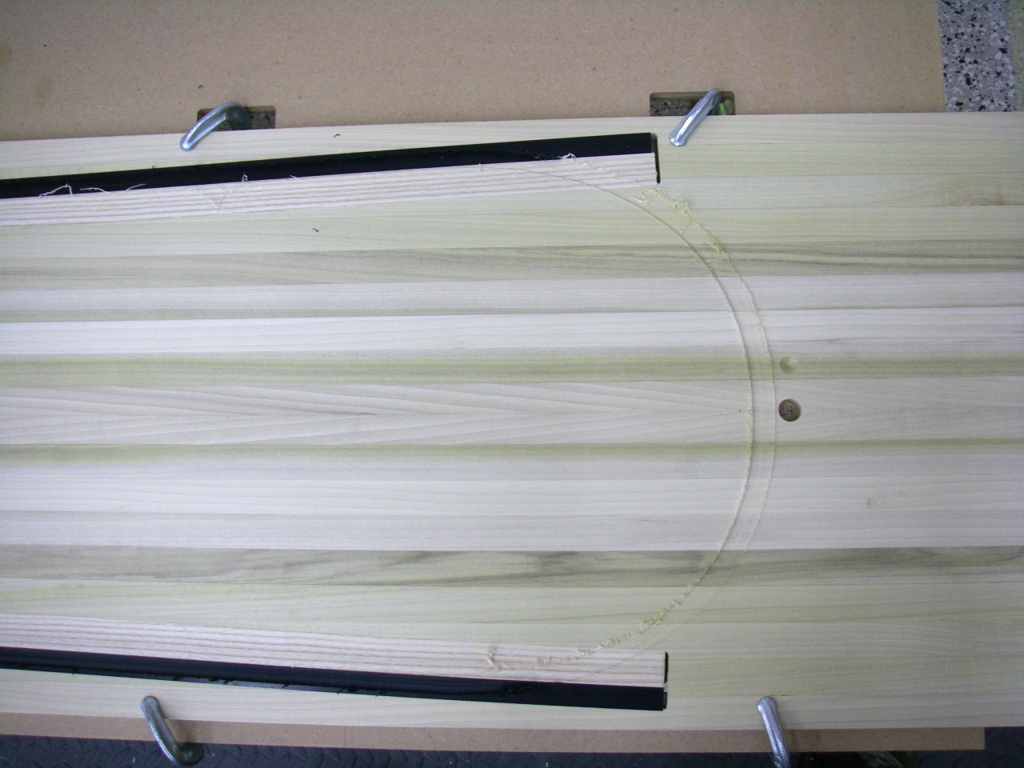
assets/images/CoreShaping_Edge1.JPG
