mikemag/MonkeyWiki/assets/images/CoreShaping_Edge2.JPG

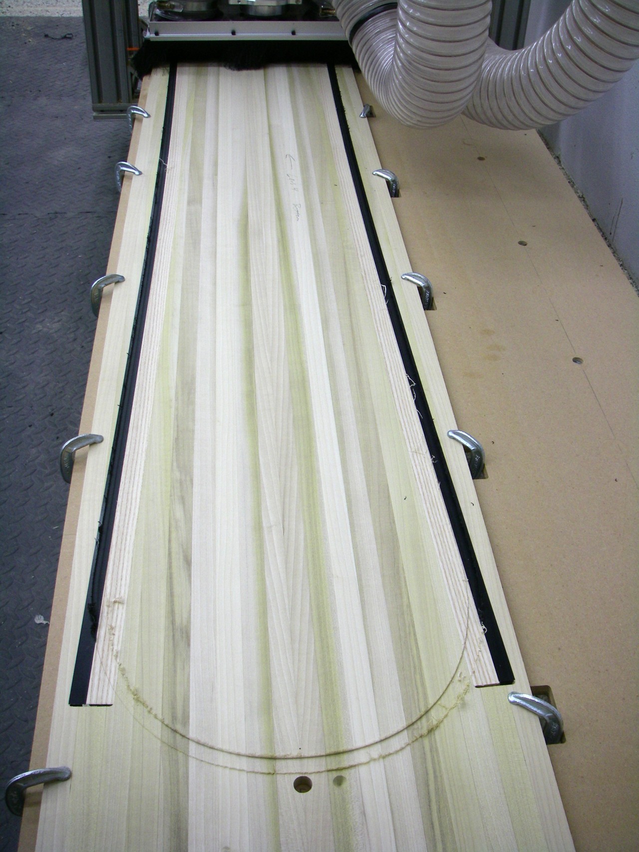
assets/images/CoreShaping_Edge2.JPG
