mikemag/MonkeyWiki/assets/images/CoreShaping_Edge3.JPG

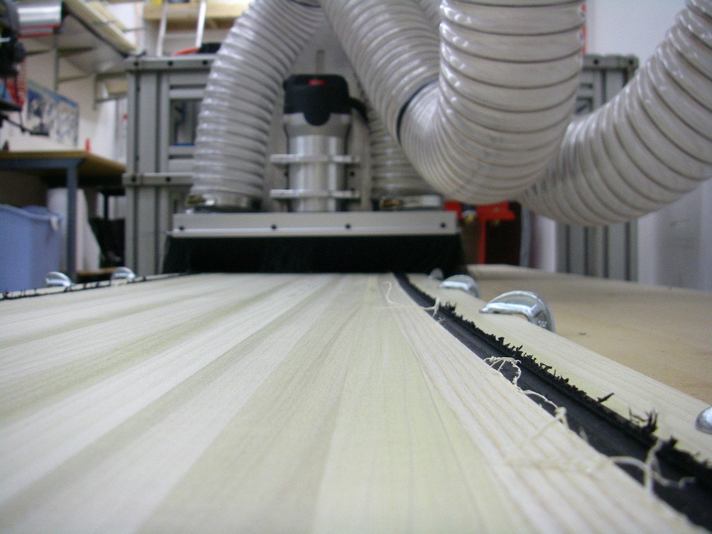
assets/images/CoreShaping_Edge3.JPG
