mikemag/MonkeyWiki/assets/images/CoreShaping_Inserts1.JPG

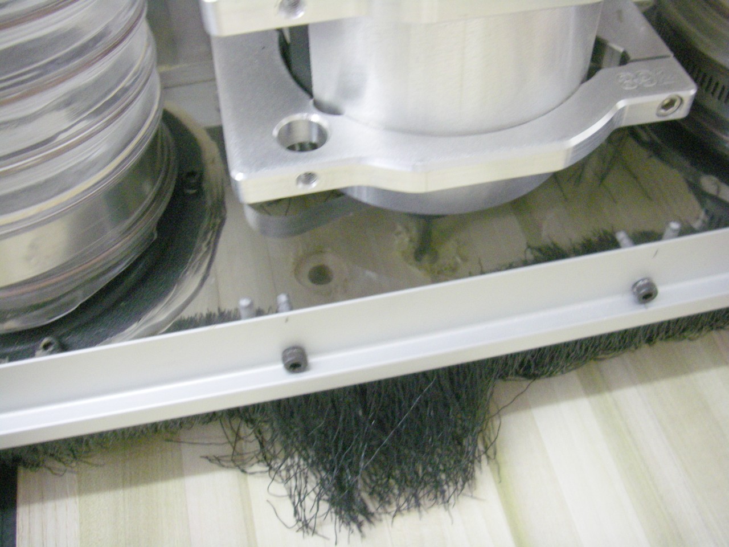
assets/images/CoreShaping_Inserts1.JPG
