mikemag/MonkeyWiki/assets/images/CoreShaping_Inserts2.JPG

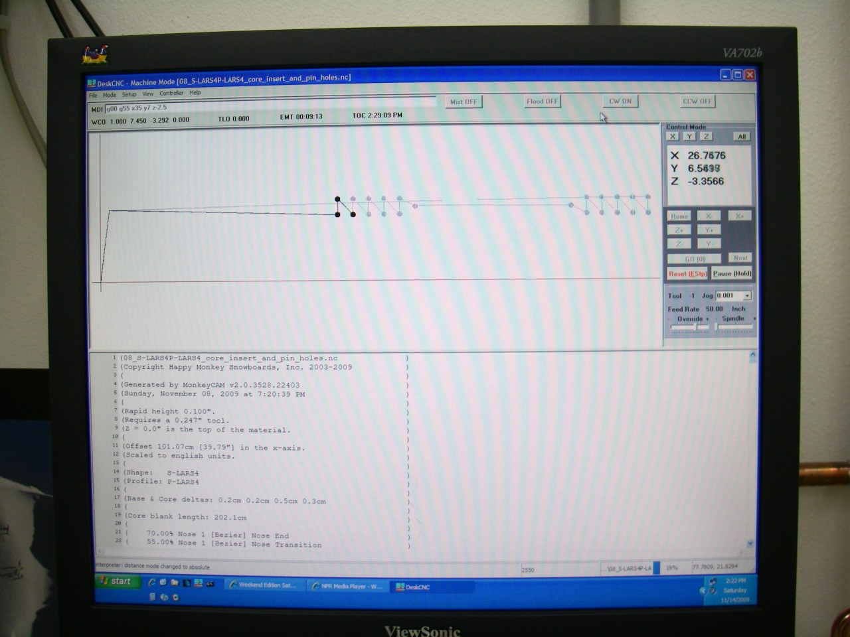
assets/images/CoreShaping_Inserts2.JPG
