mikemag/MonkeyWiki/assets/images/CoreShaping_Inserts3.JPG

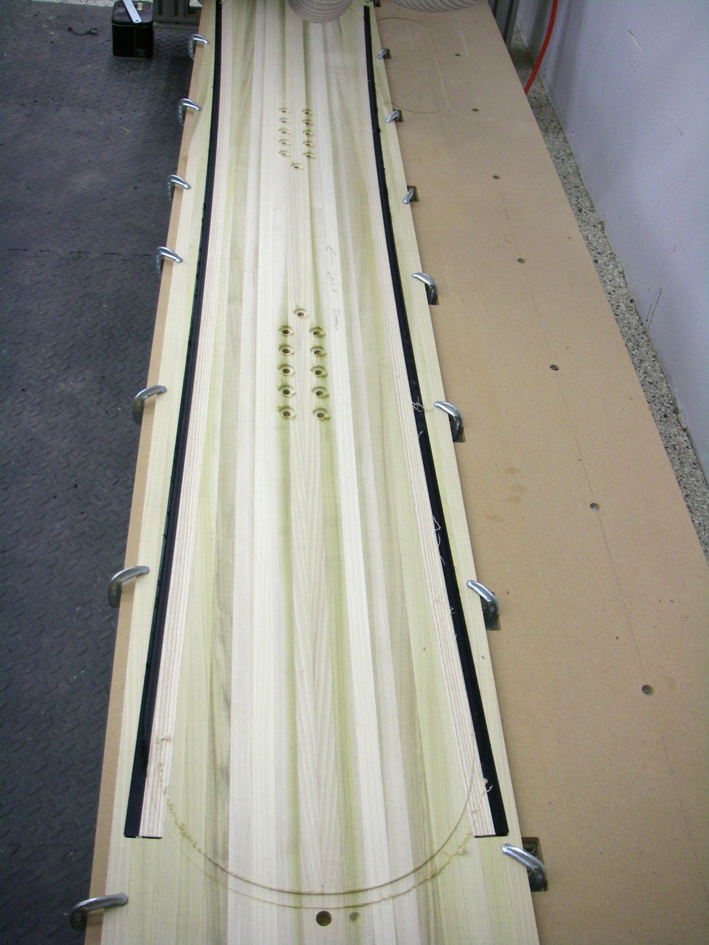
assets/images/CoreShaping_Inserts3.JPG
