mikemag/MonkeyWiki/assets/images/CoreShaping_Inserts4.JPG

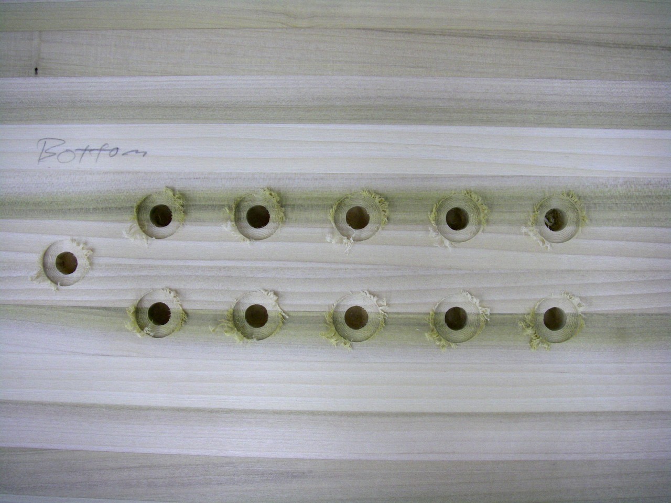
assets/images/CoreShaping_Inserts4.JPG
