mikemag/MonkeyWiki/assets/images/CoreShaping_Inserts5.JPG

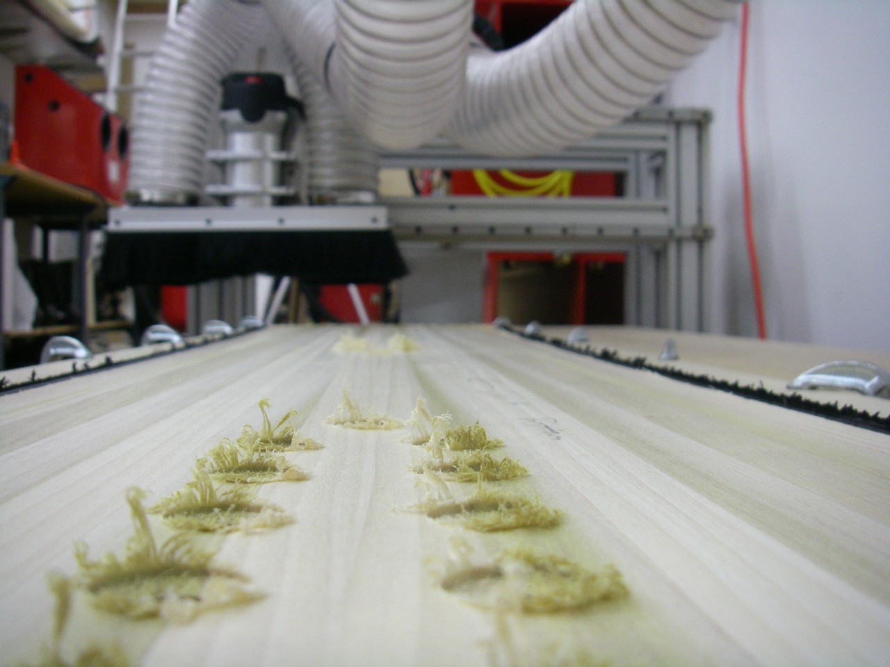
assets/images/CoreShaping_Inserts5.JPG
