mikemag/MonkeyWiki/assets/images/CoreShaping_ThicknessProfile1.JPG

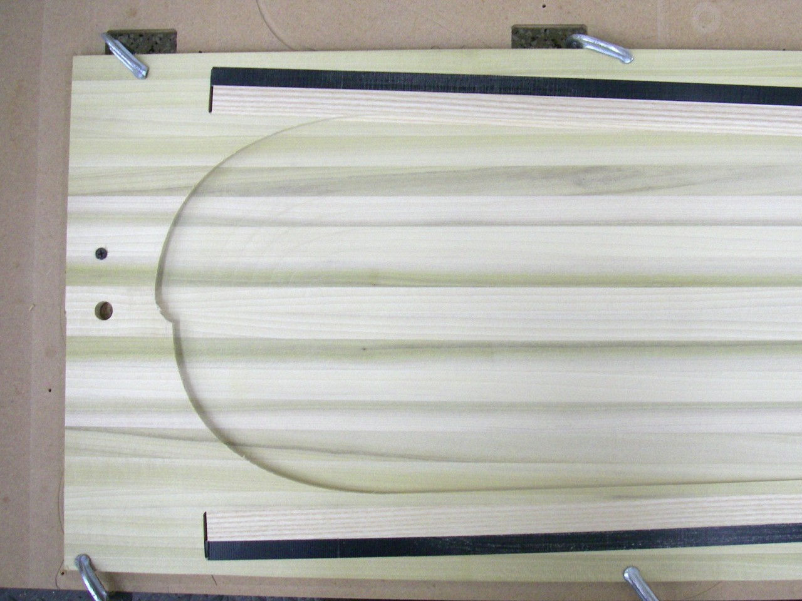
assets/images/CoreShaping_ThicknessProfile1.JPG
