mikemag/MonkeyWiki/assets/images/CoreShaping_ThicknessProfile2.JPG

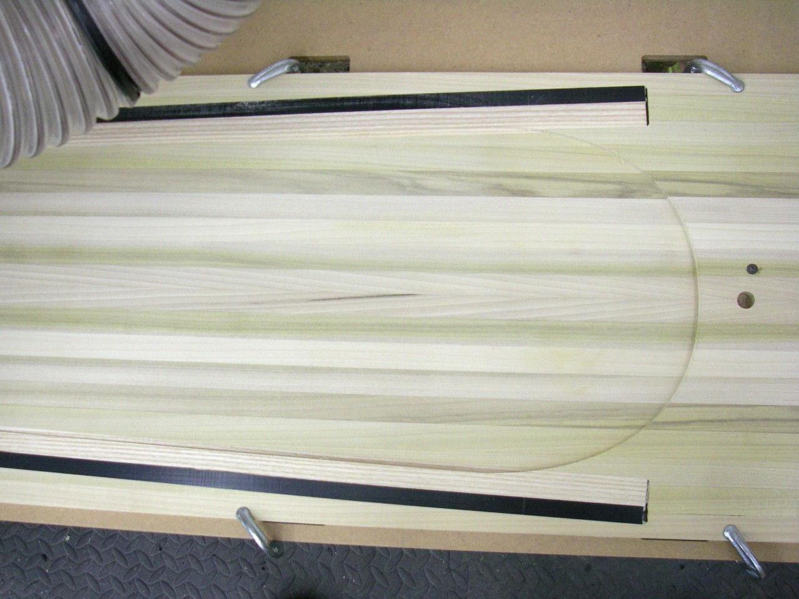
assets/images/CoreShaping_ThicknessProfile2.JPG
