mikemag/MonkeyWiki/assets/images/CoreShaping_ThicknessProfile3.JPG

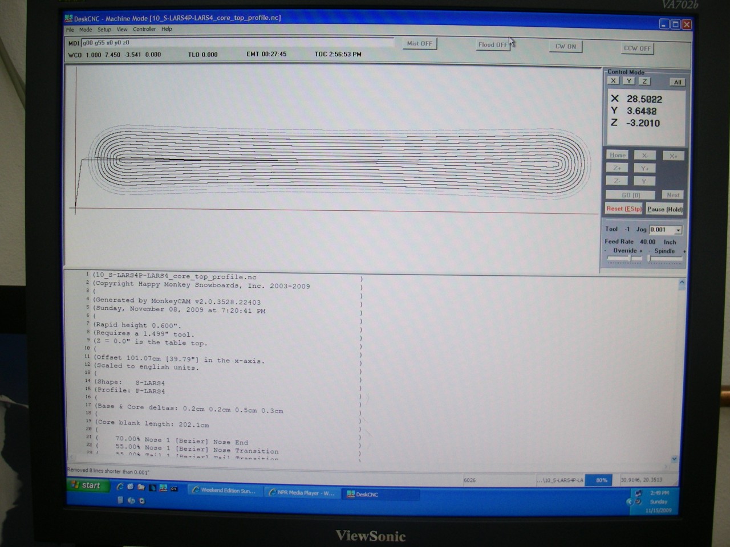
assets/images/CoreShaping_ThicknessProfile3.JPG
