mikemag/MonkeyWiki/assets/images/Deflection_Jig_1.jpg

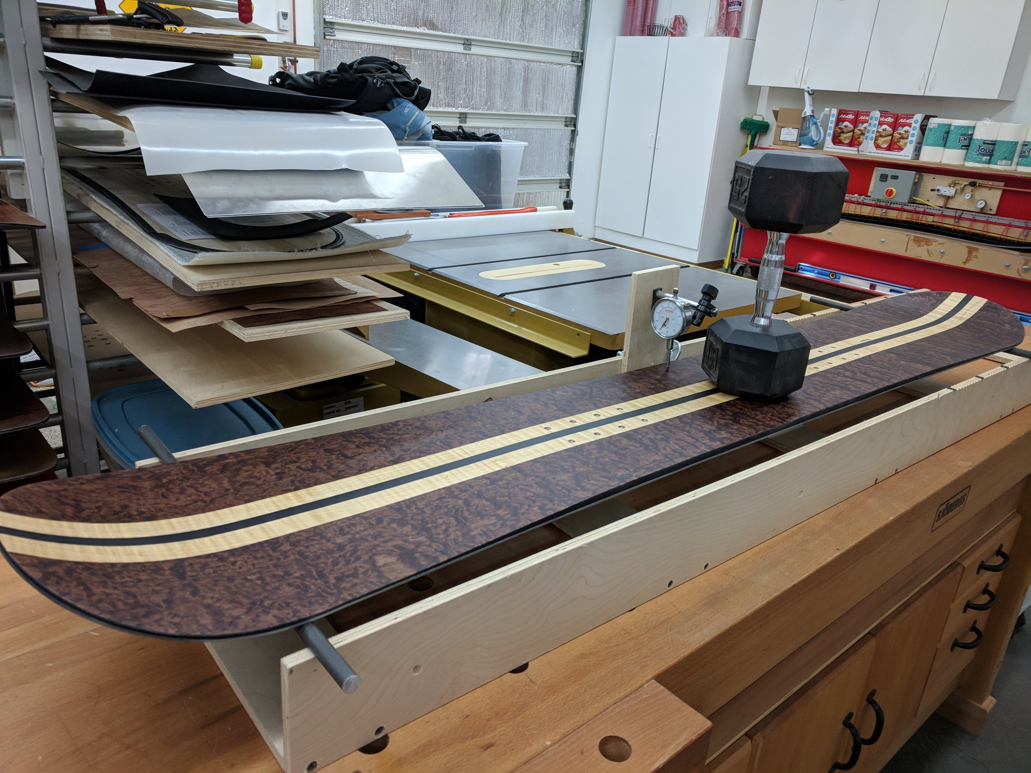
assets/images/Deflection_Jig_1.jpg
