mikemag/MonkeyWiki/assets/images/Deflection_Jig_2.jpg

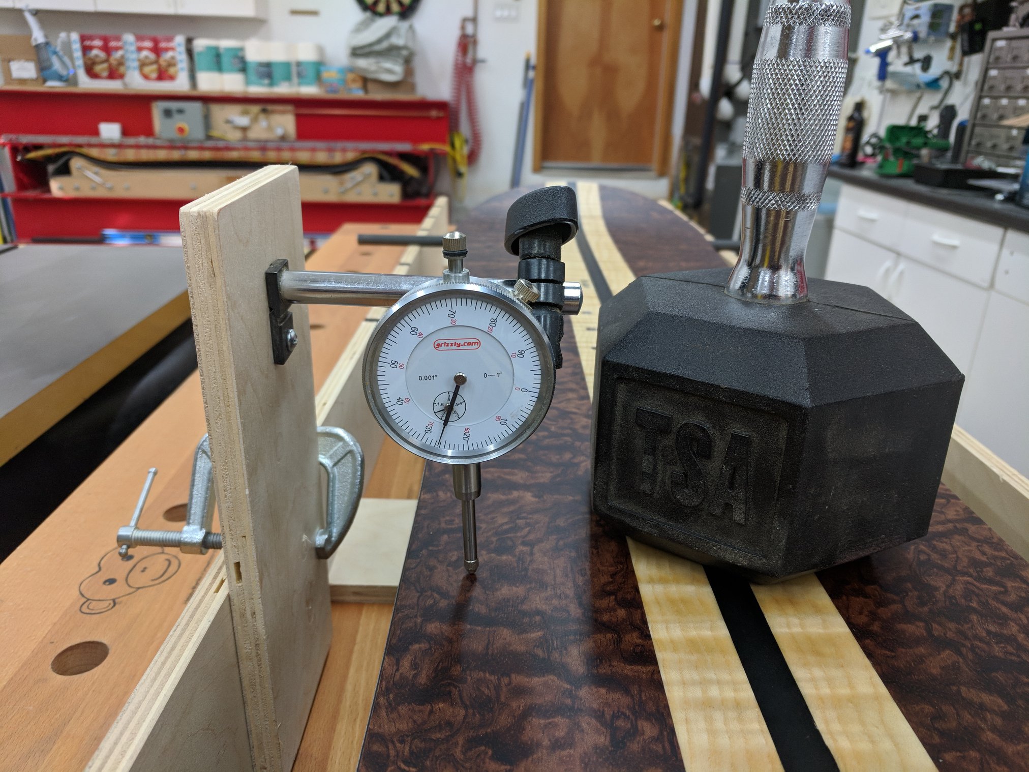
assets/images/Deflection_Jig_2.jpg
