mikemag/MonkeyWiki/assets/images/Deflection_Jig_3.jpg

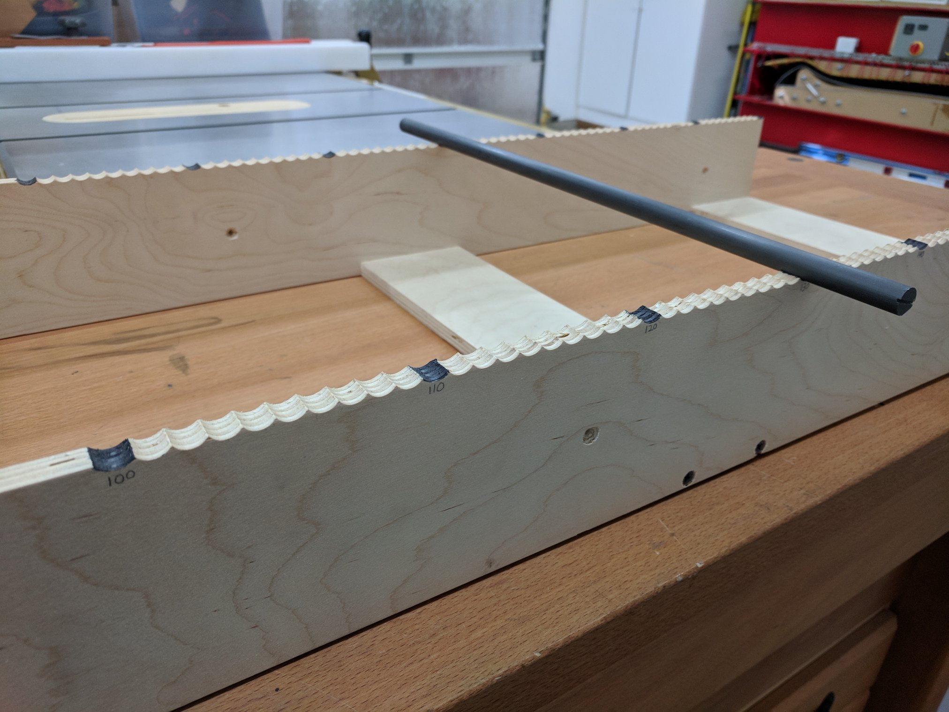
assets/images/Deflection_Jig_3.jpg
