mikemag/MonkeyWiki/assets/images/Deflection_Jig_4.jpg

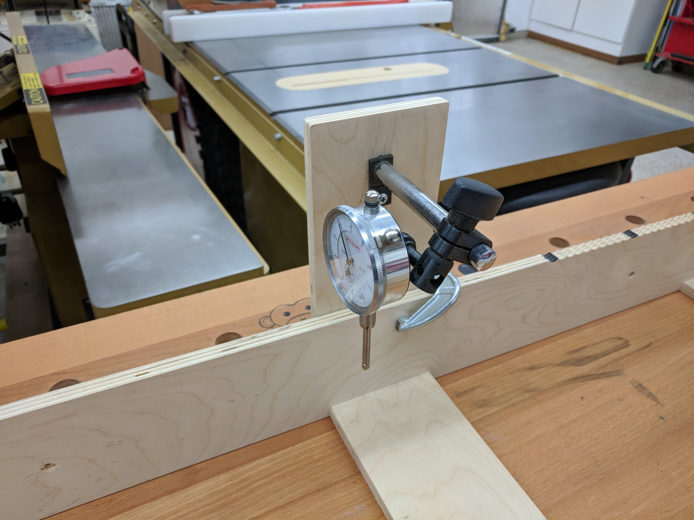
assets/images/Deflection_Jig_4.jpg
