mikemag/MonkeyWiki/assets/images/Deflection_Jig_5.jpg

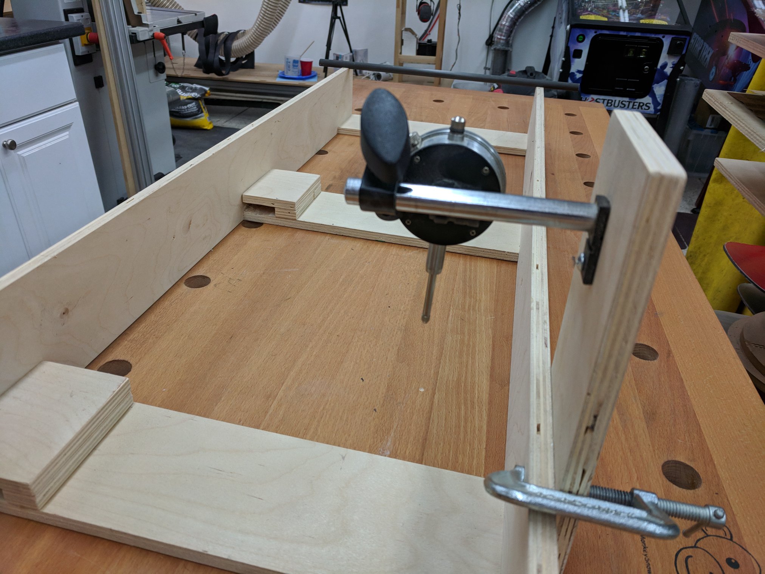
assets/images/Deflection_Jig_5.jpg
