mikemag/MonkeyWiki/assets/images/Deflection_Jig_6.jpg

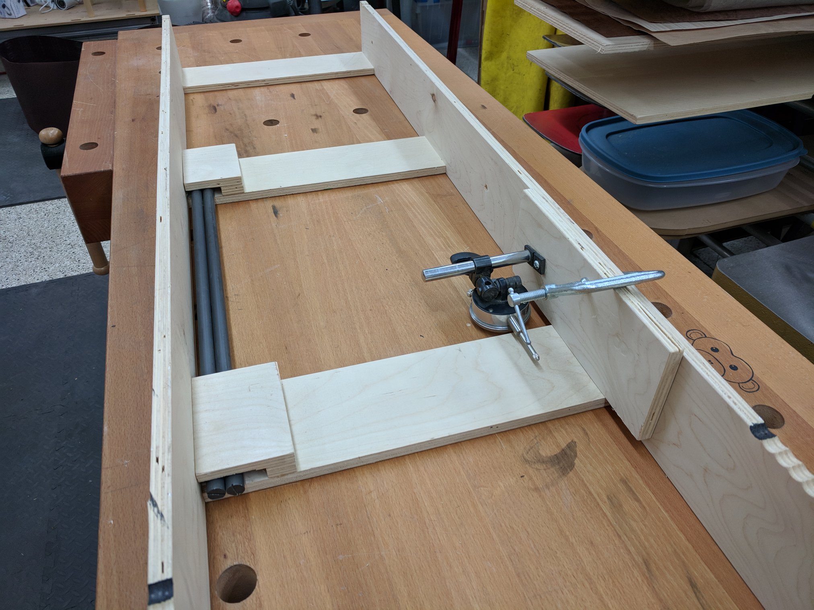
assets/images/Deflection_Jig_6.jpg
