mikemag/MonkeyWiki/assets/images/EdgeCleanup1.JPG

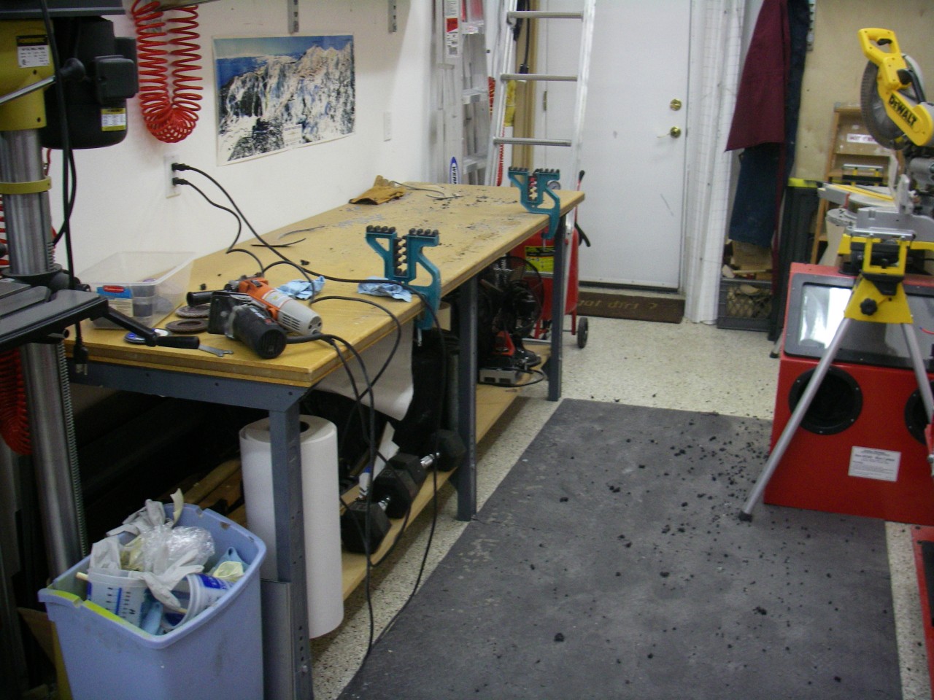
assets/images/EdgeCleanup1.JPG
