mikemag/MonkeyWiki/assets/images/EdgeCleanup2.JPG

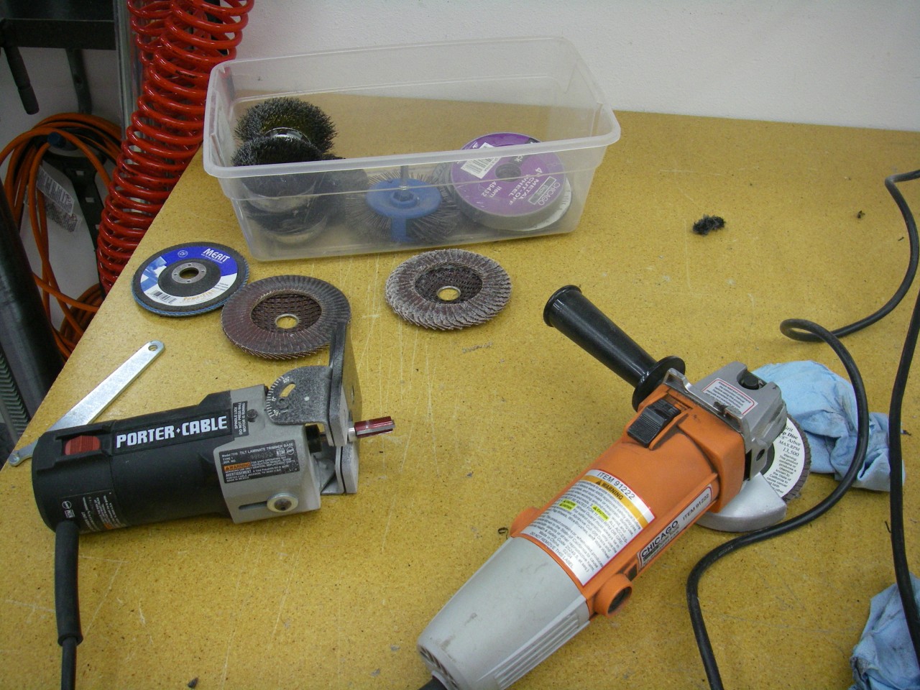
assets/images/EdgeCleanup2.JPG
