mikemag/MonkeyWiki/assets/images/Edges_Bending1.JPG

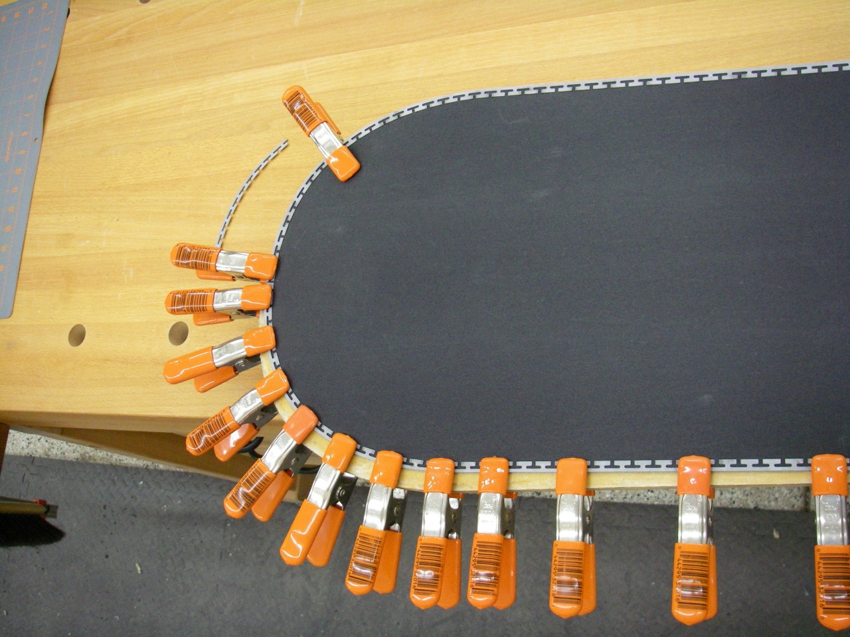
assets/images/Edges_Bending1.JPG
