mikemag/MonkeyWiki/assets/images/Edges_Bending2.JPG

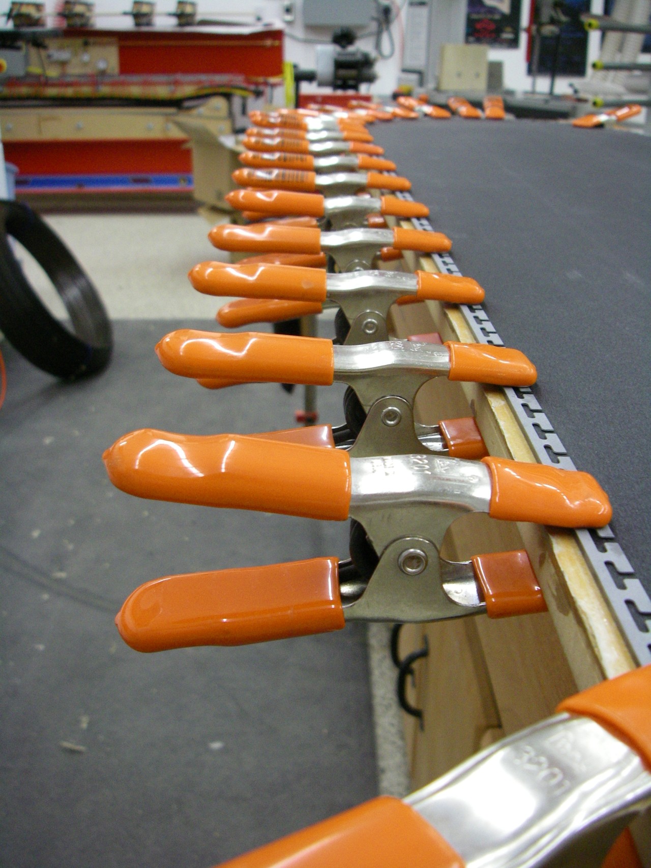
assets/images/Edges_Bending2.JPG
