mikemag/MonkeyWiki/assets/images/Edges_Bending3.JPG

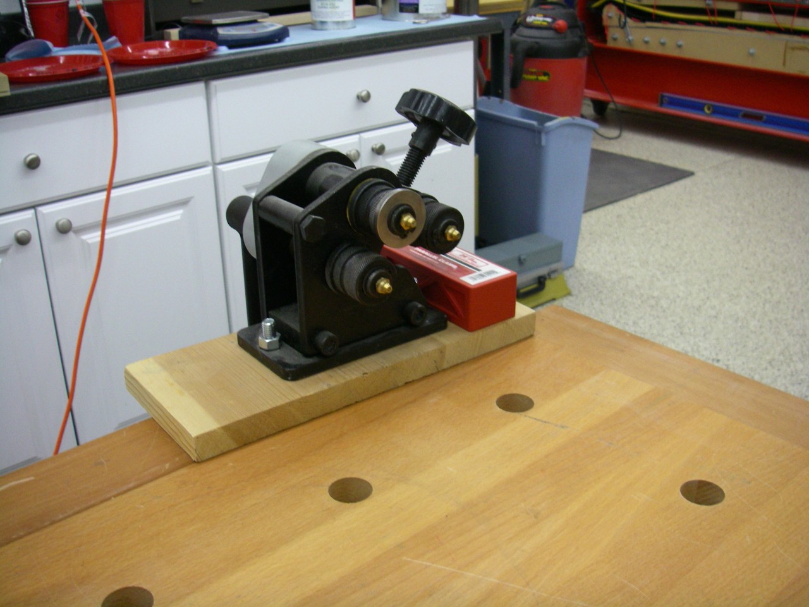
assets/images/Edges_Bending3.JPG
