mikemag/MonkeyWiki/assets/images/Edges_Bending4.JPG

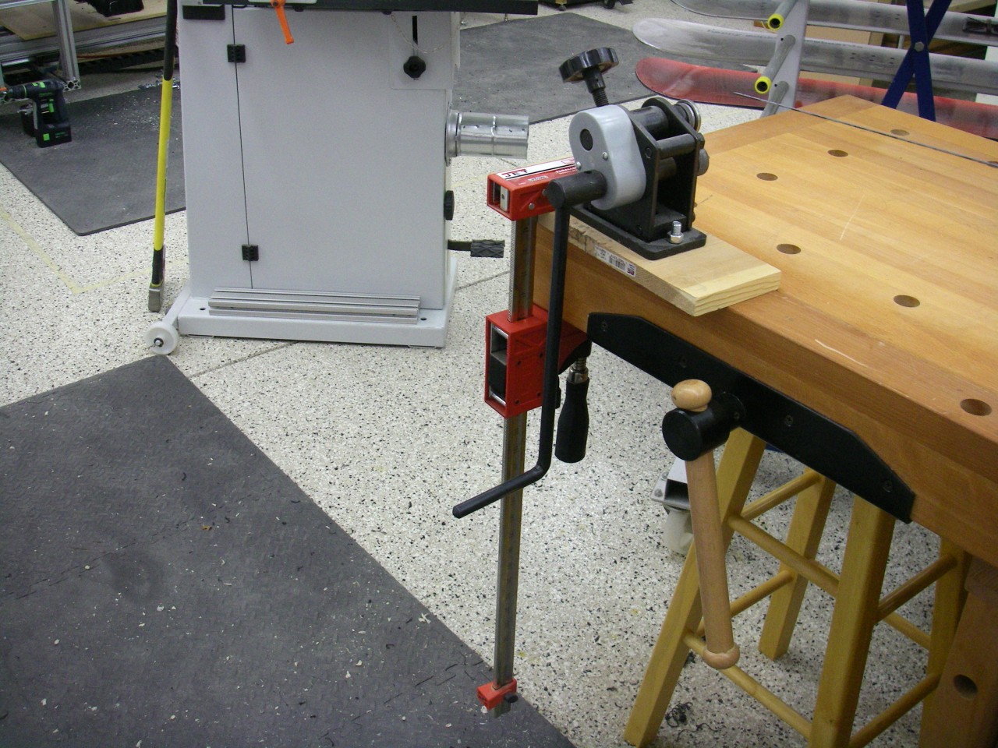
assets/images/Edges_Bending4.JPG
