mikemag/MonkeyWiki/assets/images/Edges_Bending5.JPG

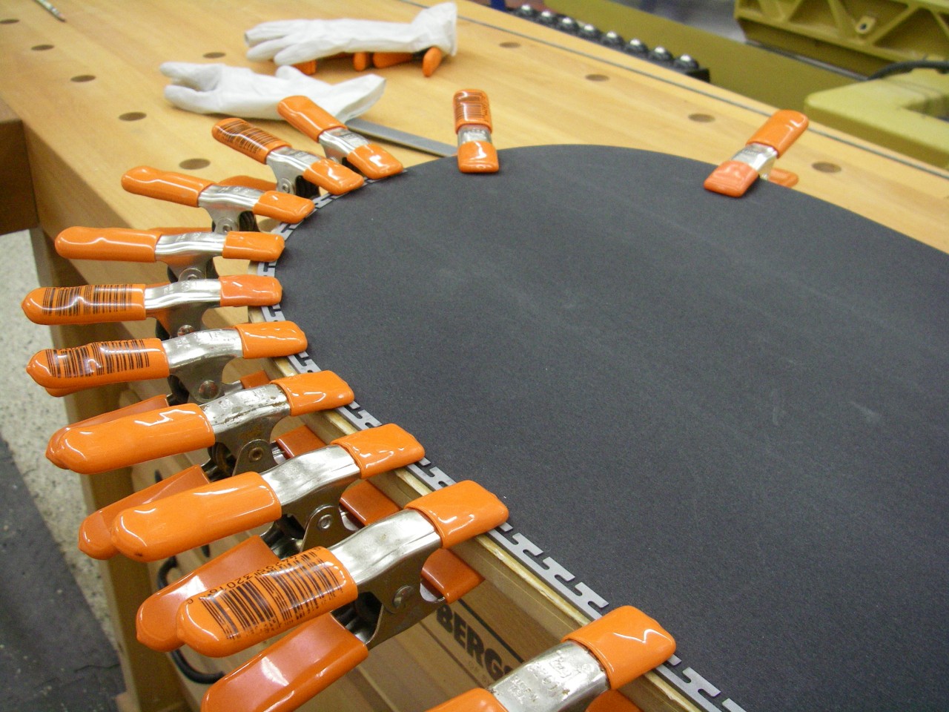
assets/images/Edges_Bending5.JPG
