mikemag/MonkeyWiki/assets/images/Edges_Blasting1.JPG

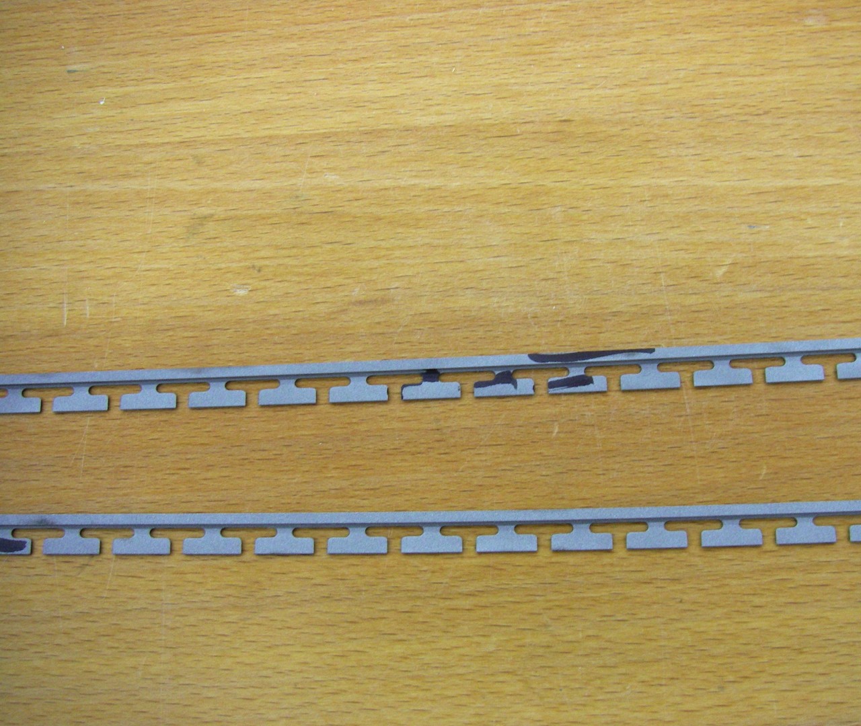
assets/images/Edges_Blasting1.JPG
