mikemag/MonkeyWiki/assets/images/Edges_Blasting2.JPG

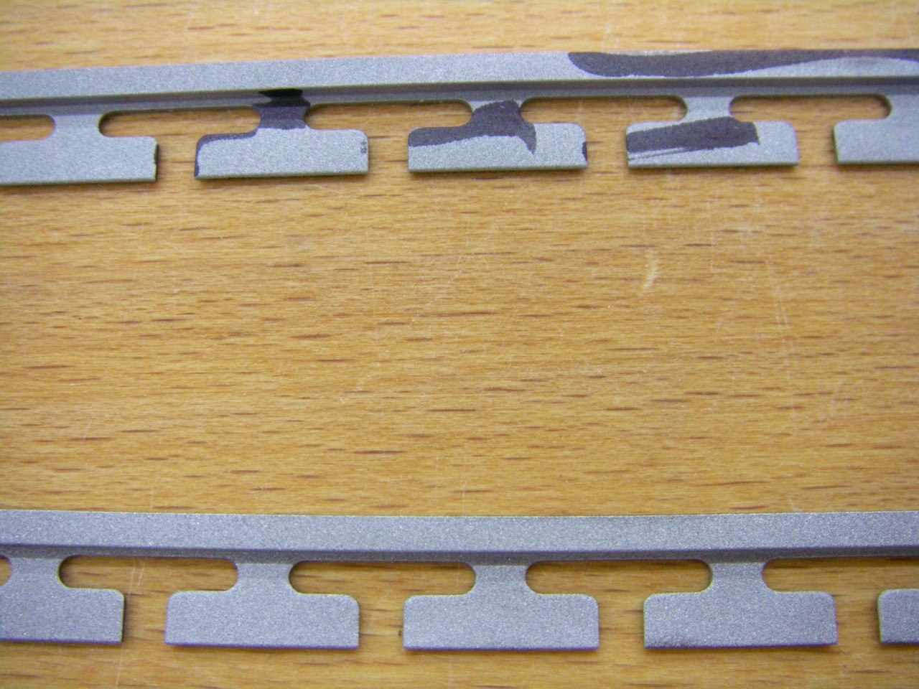
assets/images/Edges_Blasting2.JPG
