mikemag/MonkeyWiki/assets/images/Edges_Blasting3.JPG

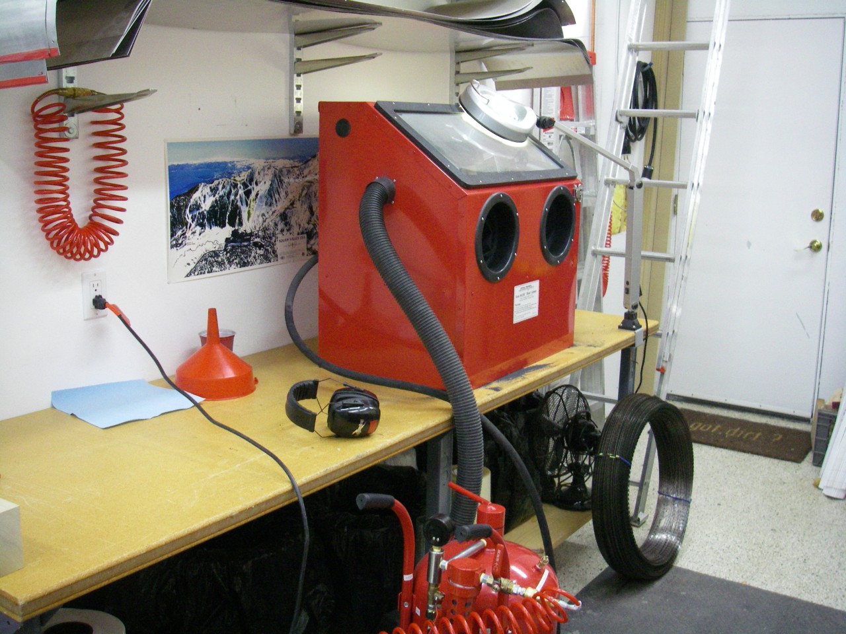
assets/images/Edges_Blasting3.JPG
