mikemag/MonkeyWiki/assets/images/Edges_Blasting4.JPG

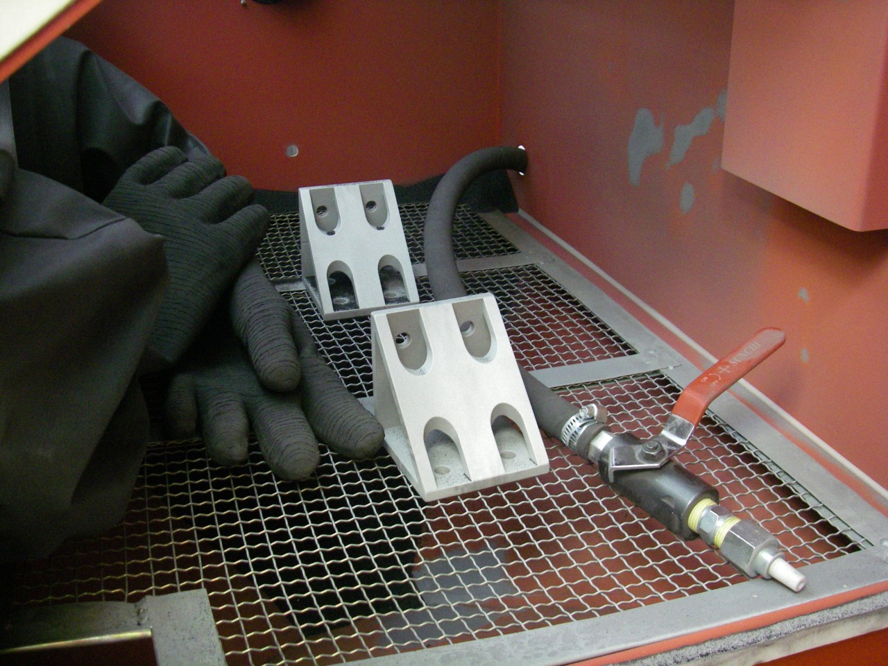
assets/images/Edges_Blasting4.JPG
