mikemag/MonkeyWiki/assets/images/Edges_Blasting5.JPG

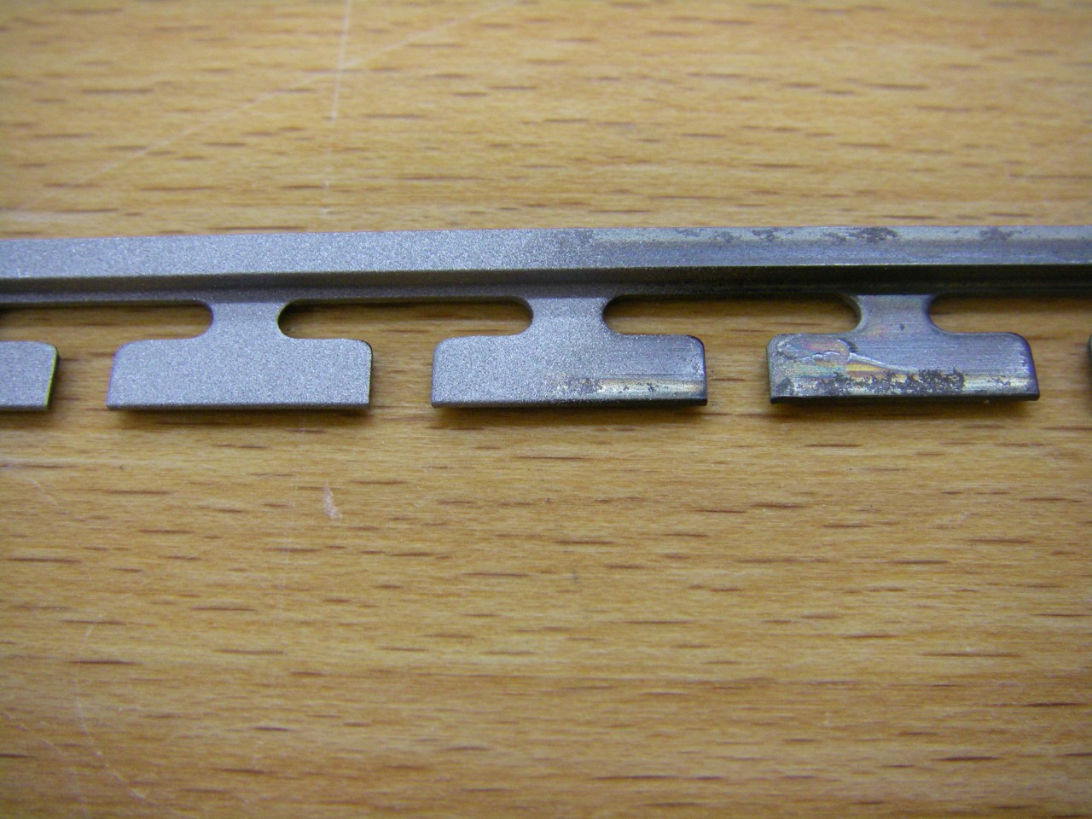
assets/images/Edges_Blasting5.JPG
