mikemag/MonkeyWiki/assets/images/Epoxy1.JPG

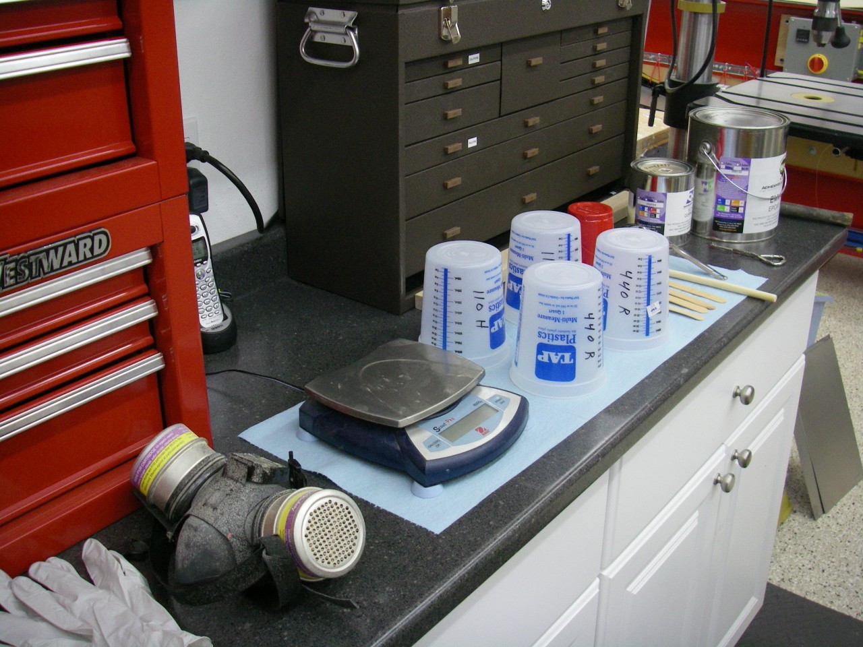
assets/images/Epoxy1.JPG
