mikemag/MonkeyWiki/assets/images/Epoxy2.JPG

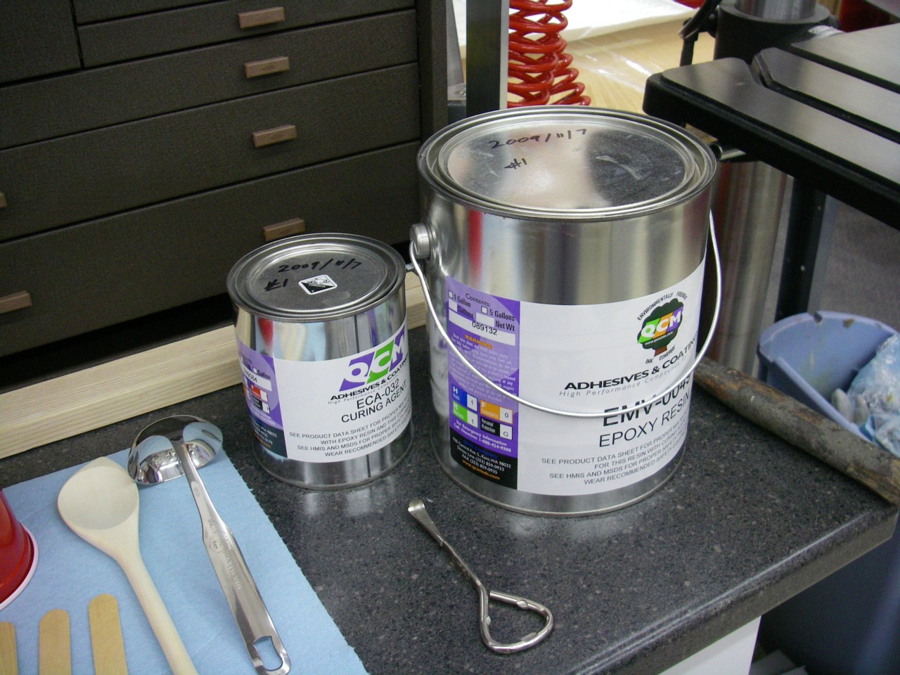
assets/images/Epoxy2.JPG
