mikemag/MonkeyWiki/assets/images/Fibers1.JPG

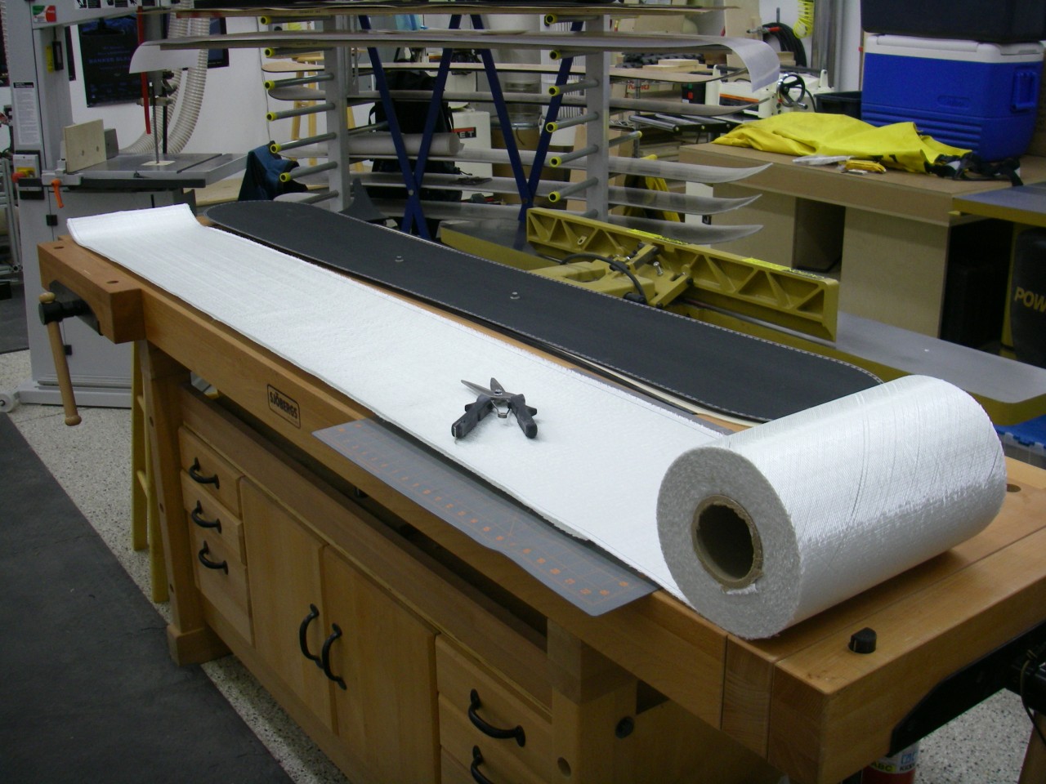
assets/images/Fibers1.JPG
