mikemag/MonkeyWiki/assets/images/Fibers2.JPG

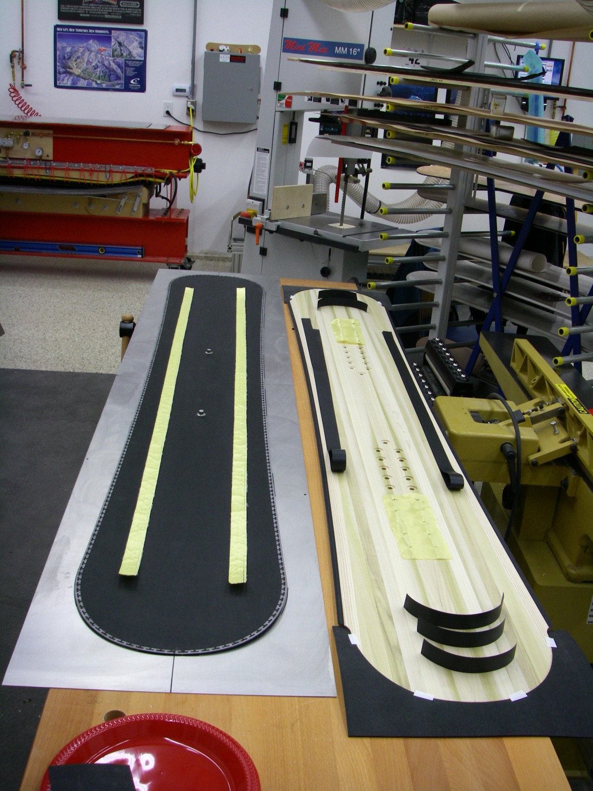
assets/images/Fibers2.JPG
