mikemag/MonkeyWiki/assets/images/Fibers3.JPG

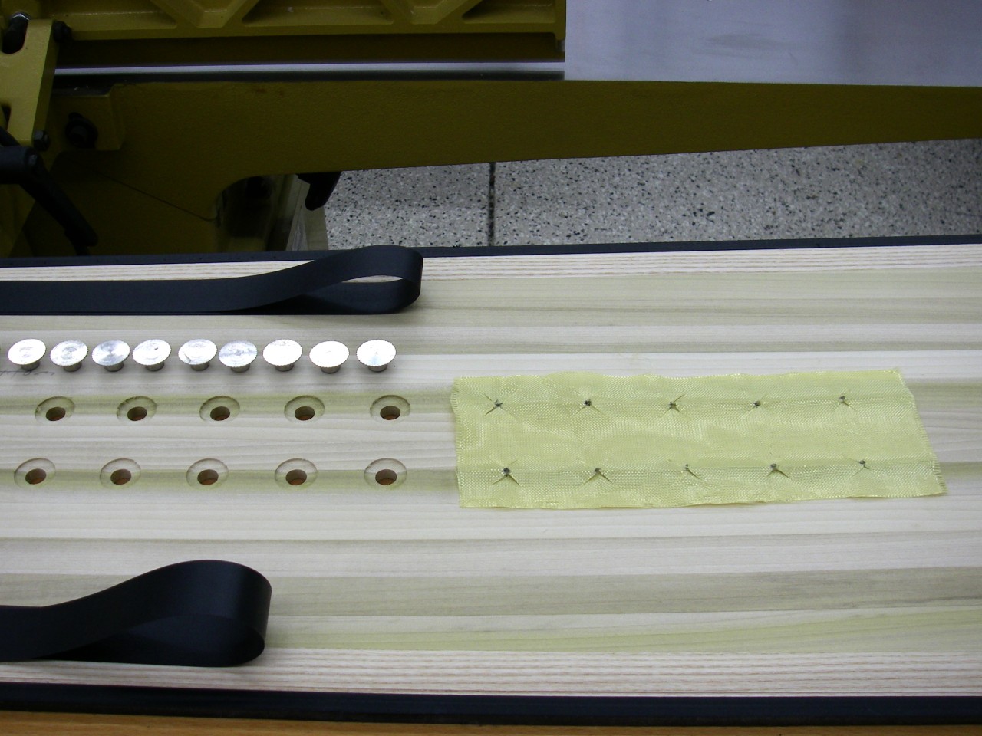
assets/images/Fibers3.JPG
