mikemag/MonkeyWiki/assets/images/Fibers4.JPG

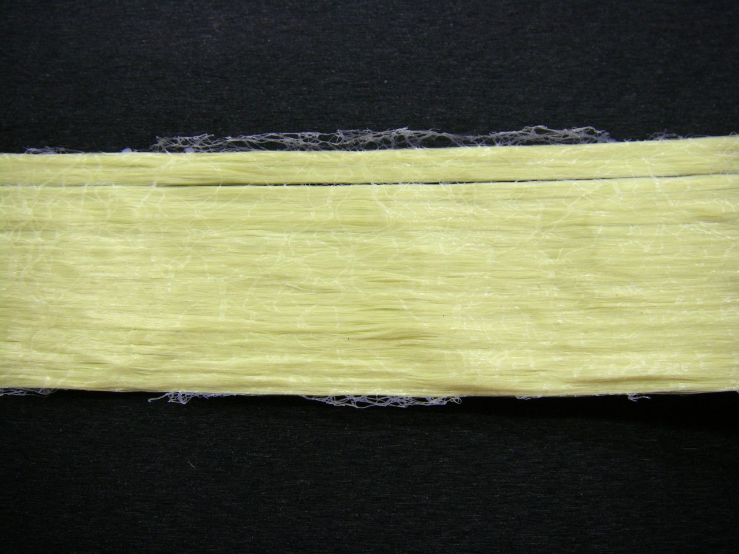
assets/images/Fibers4.JPG
