mikemag/MonkeyWiki/assets/images/Fibers5.JPG

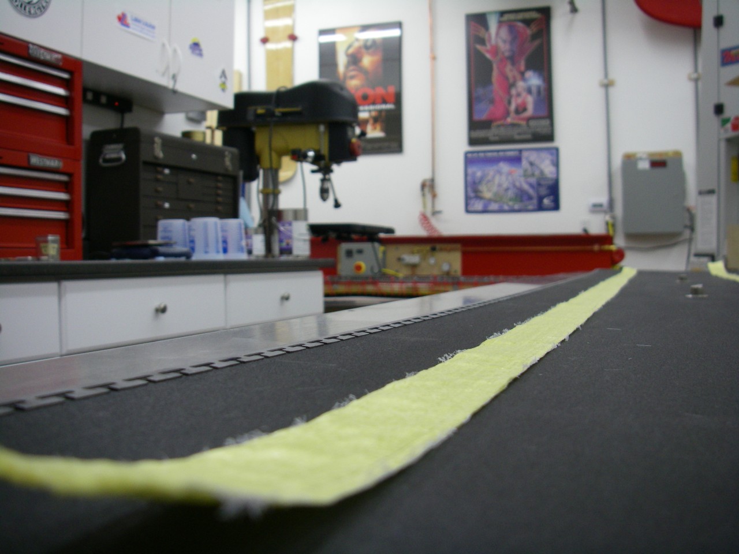
assets/images/Fibers5.JPG
