mikemag/MonkeyWiki/assets/images/Fibers6.JPG

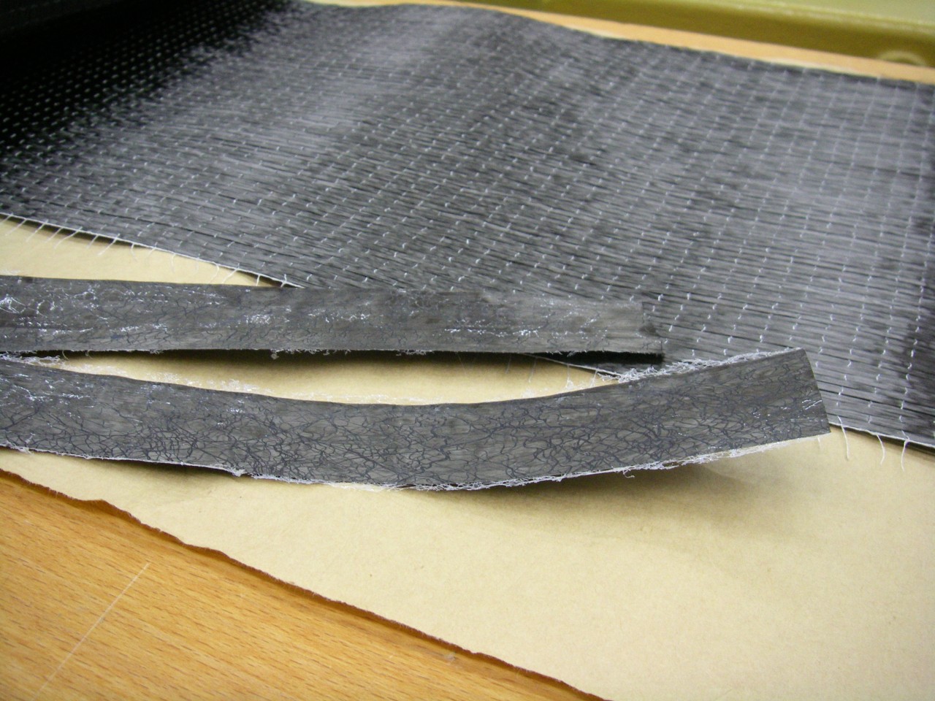
assets/images/Fibers6.JPG
