mikemag/MonkeyWiki/assets/images/Fibers7.JPG

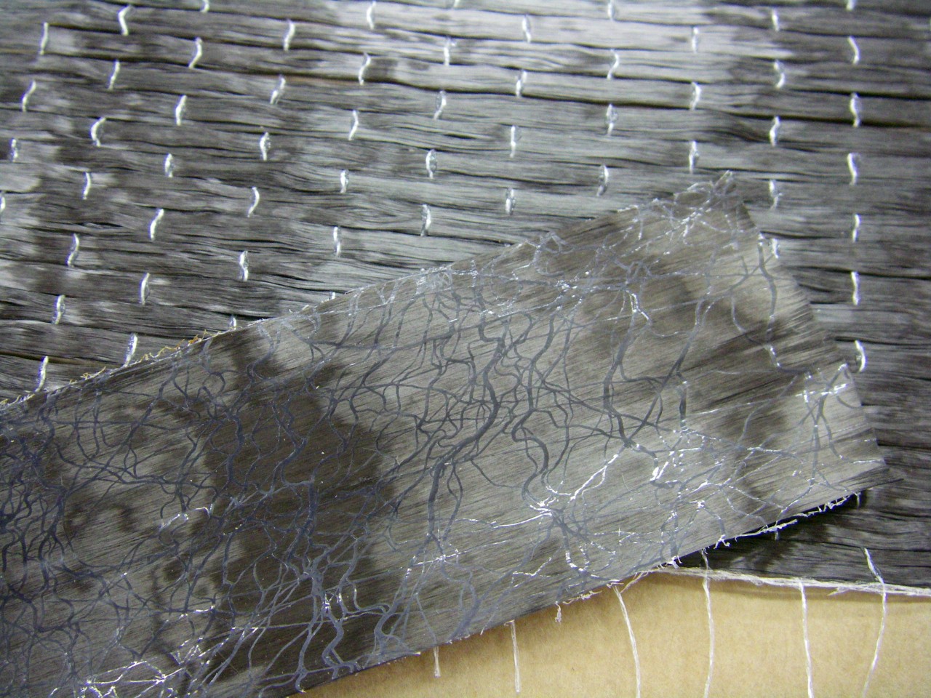
assets/images/Fibers7.JPG
