mikemag/MonkeyWiki/assets/images/Fibers8.JPG

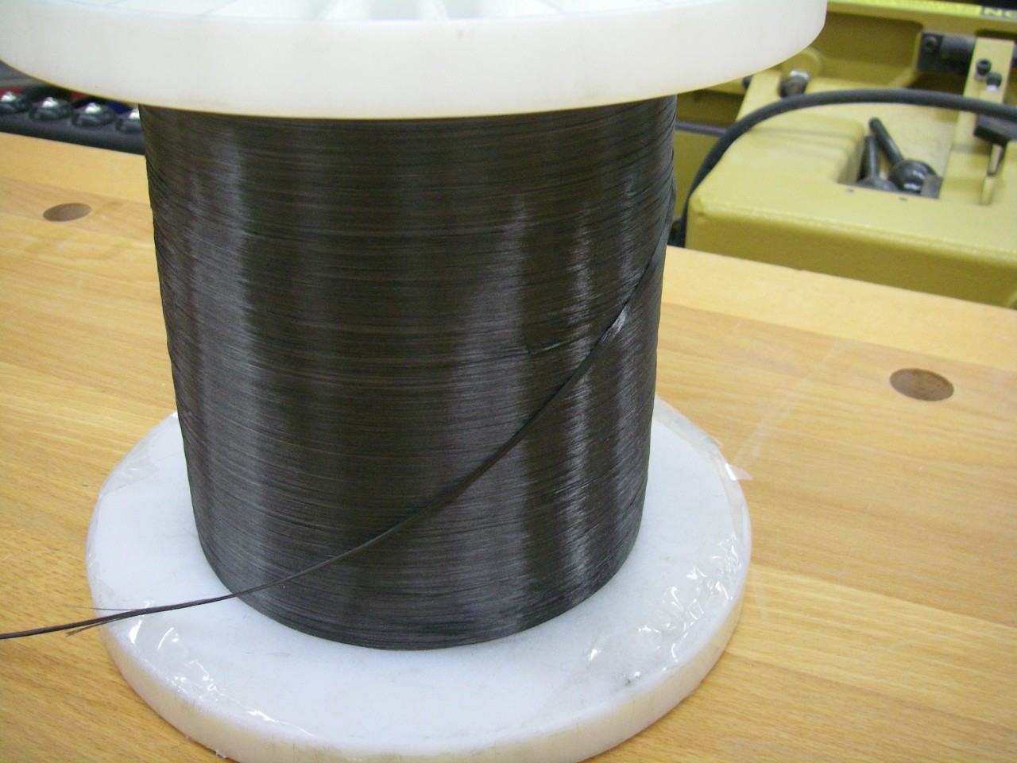
assets/images/Fibers8.JPG
