mikemag/MonkeyWiki/assets/images/Fibers9.JPG

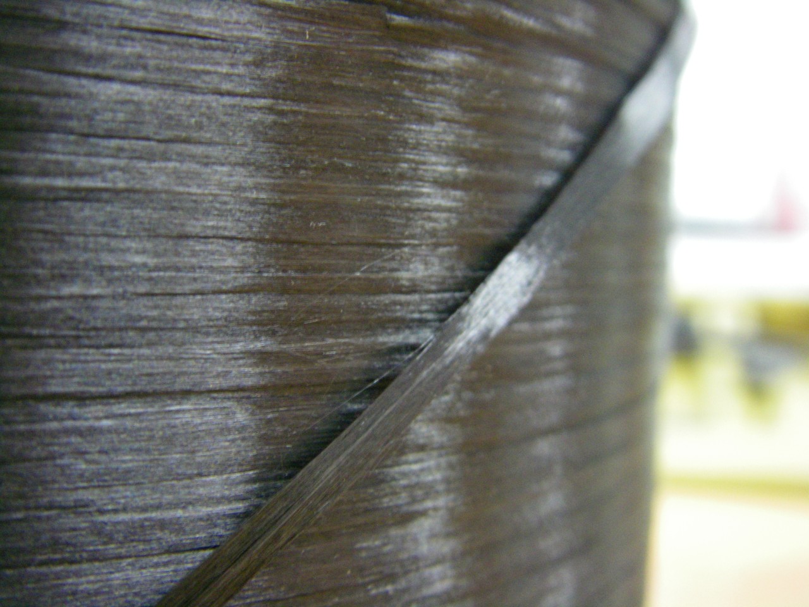
assets/images/Fibers9.JPG
