mikemag/MonkeyWiki/assets/images/Fingers.JPG

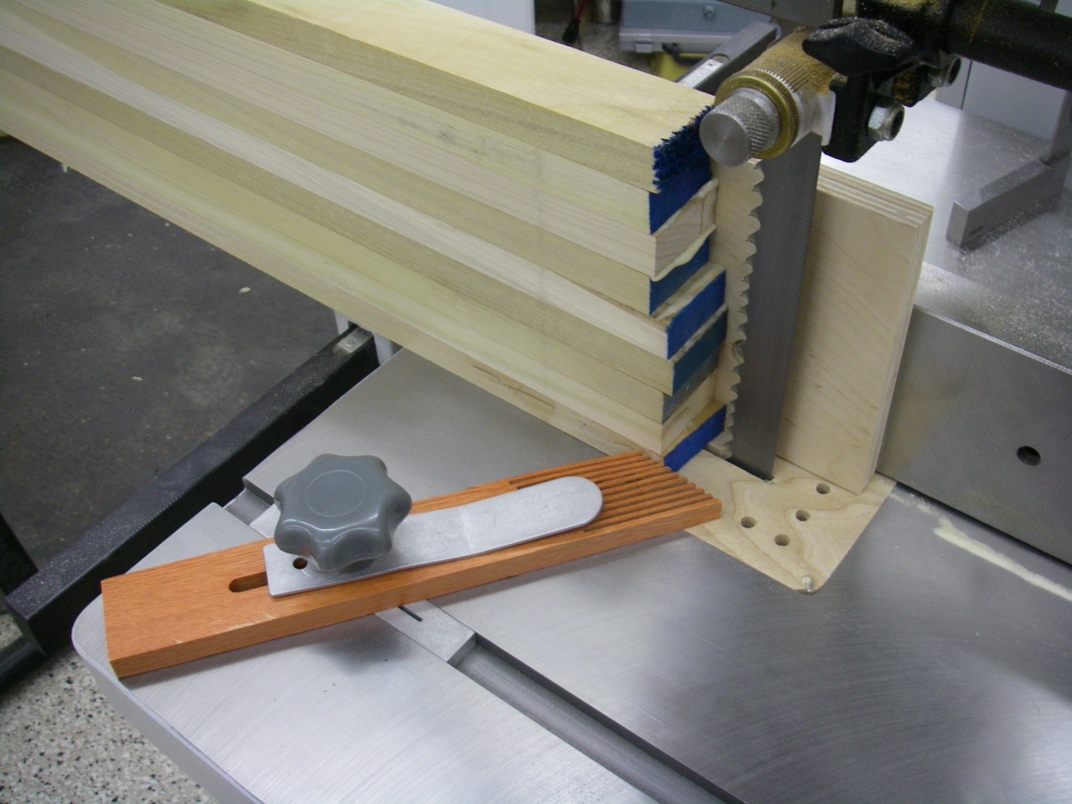
assets/images/Fingers.JPG
