mikemag/MonkeyWiki/assets/images/FlashCleanup1.JPG

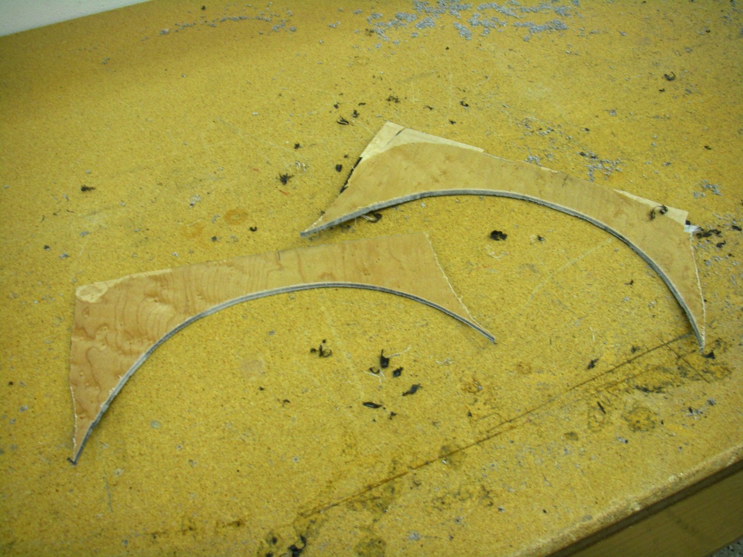
assets/images/FlashCleanup1.JPG
