mikemag/MonkeyWiki/assets/images/FlashCleanup2.JPG

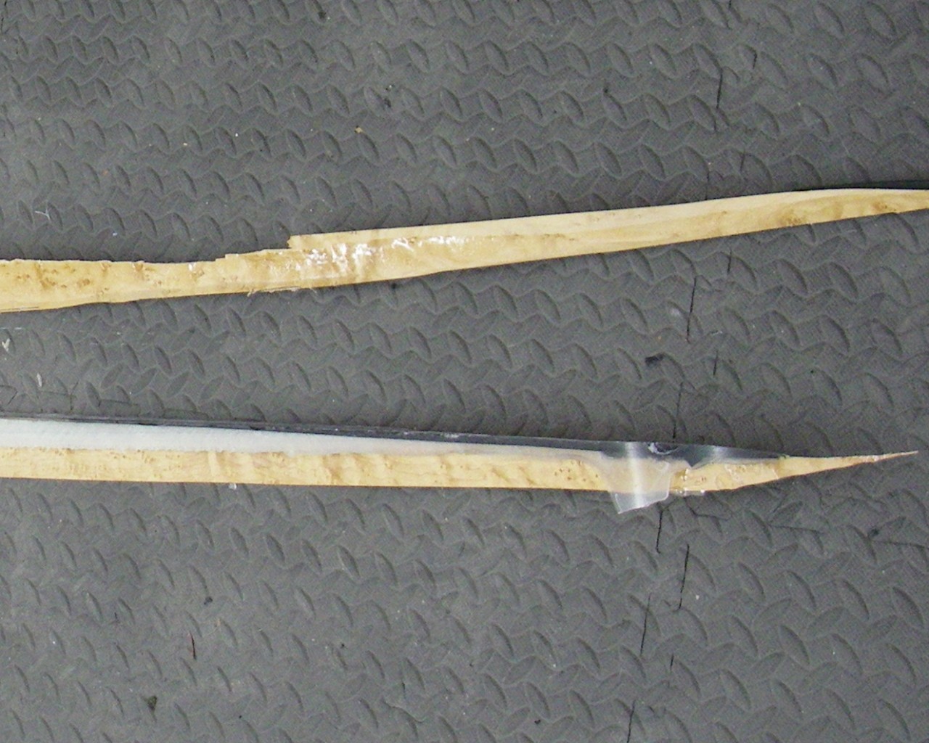
assets/images/FlashCleanup2.JPG
