mikemag/MonkeyWiki/assets/images/FourWayClamp1.JPG

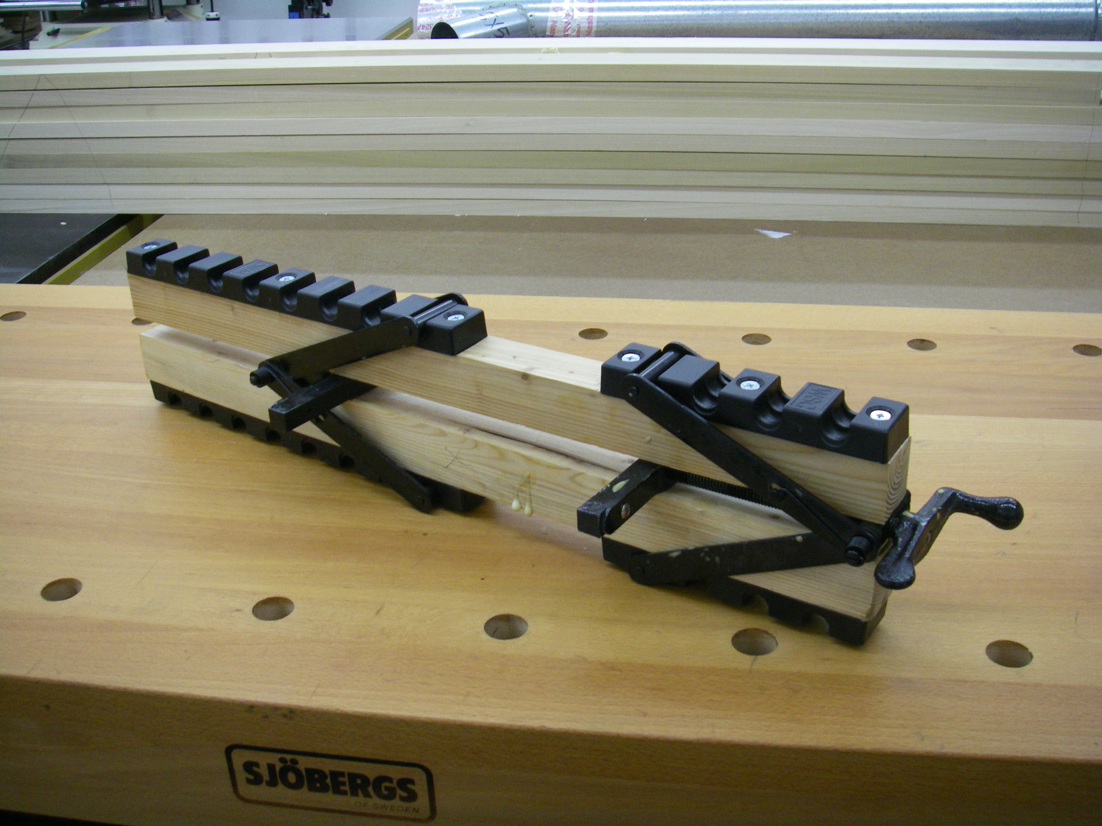
assets/images/FourWayClamp1.JPG
