mikemag/MonkeyWiki/assets/images/FourWayClamp2.JPG

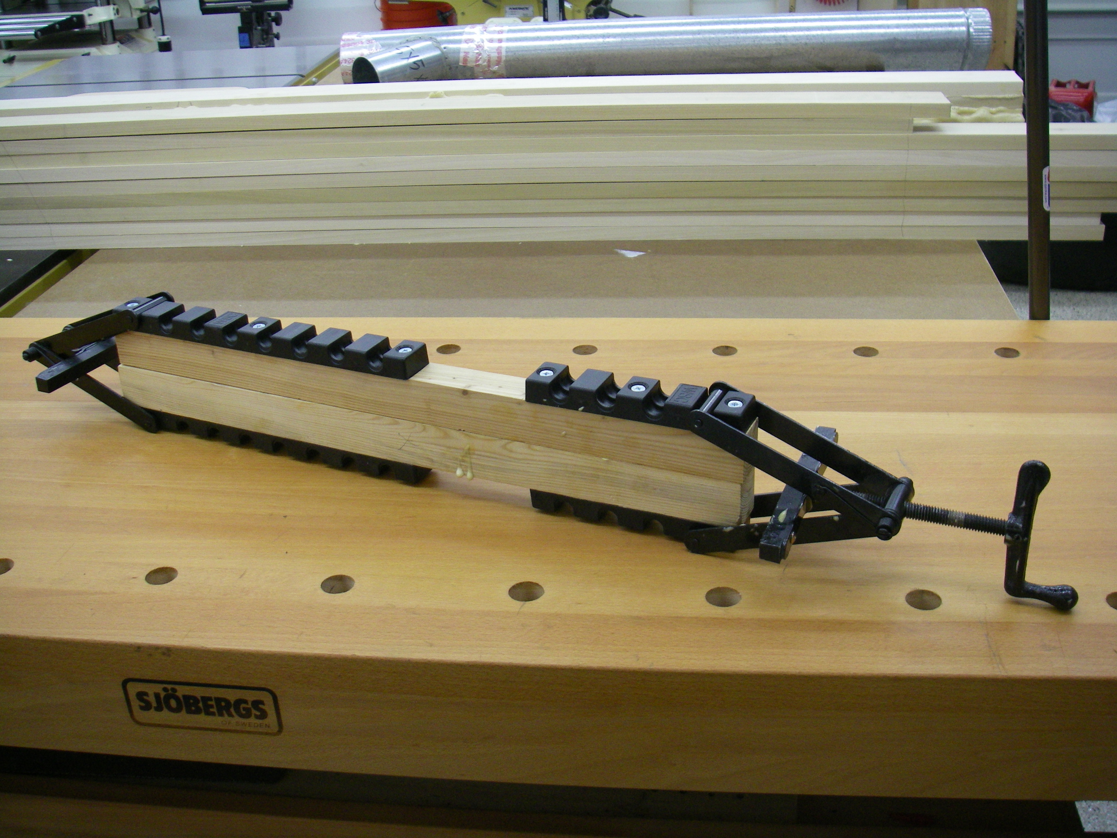
assets/images/FourWayClamp2.JPG
