mikemag/MonkeyWiki/assets/images/FourWayClamp3.JPG

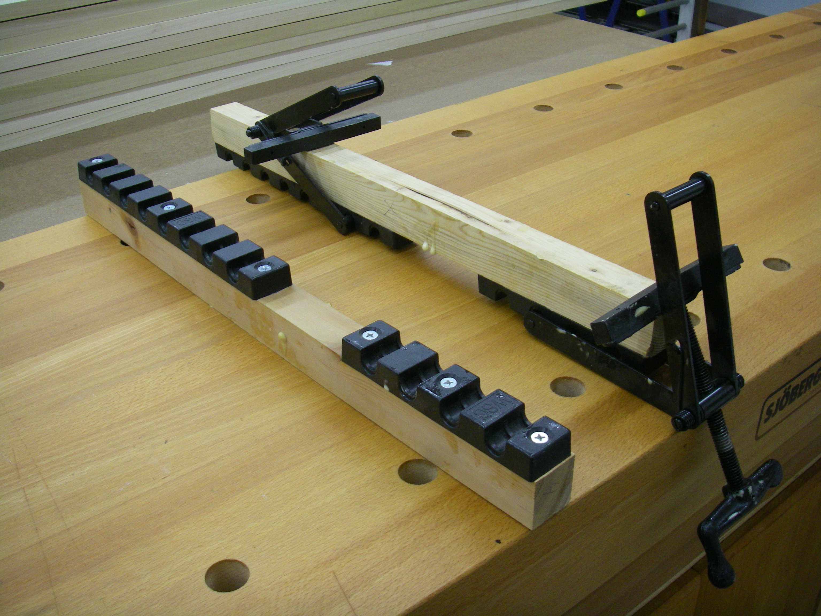
assets/images/FourWayClamp3.JPG
