mikemag/MonkeyWiki/assets/images/FourWayClamp4.JPG

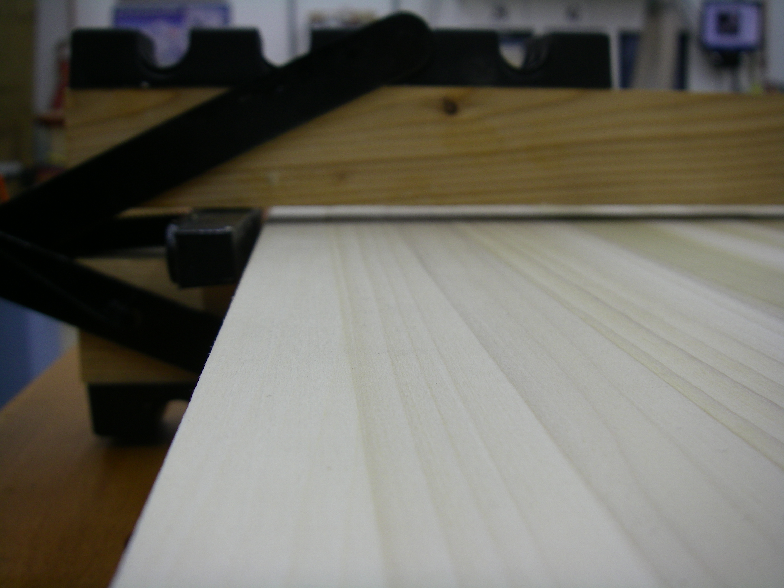
assets/images/FourWayClamp4.JPG
