mikemag/MonkeyWiki/assets/images/FourWayClamp5.JPG

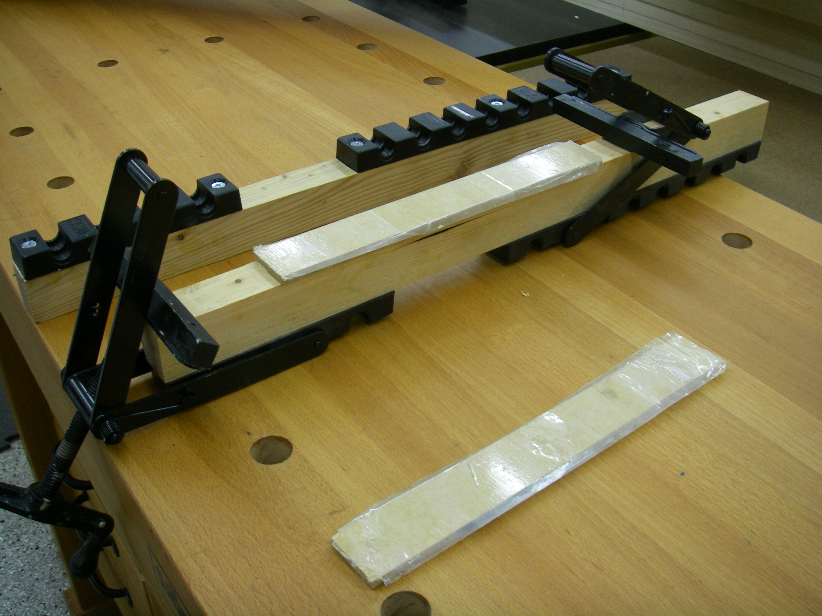
assets/images/FourWayClamp5.JPG
