mikemag/MonkeyWiki/assets/images/FourWayClamp6.JPG

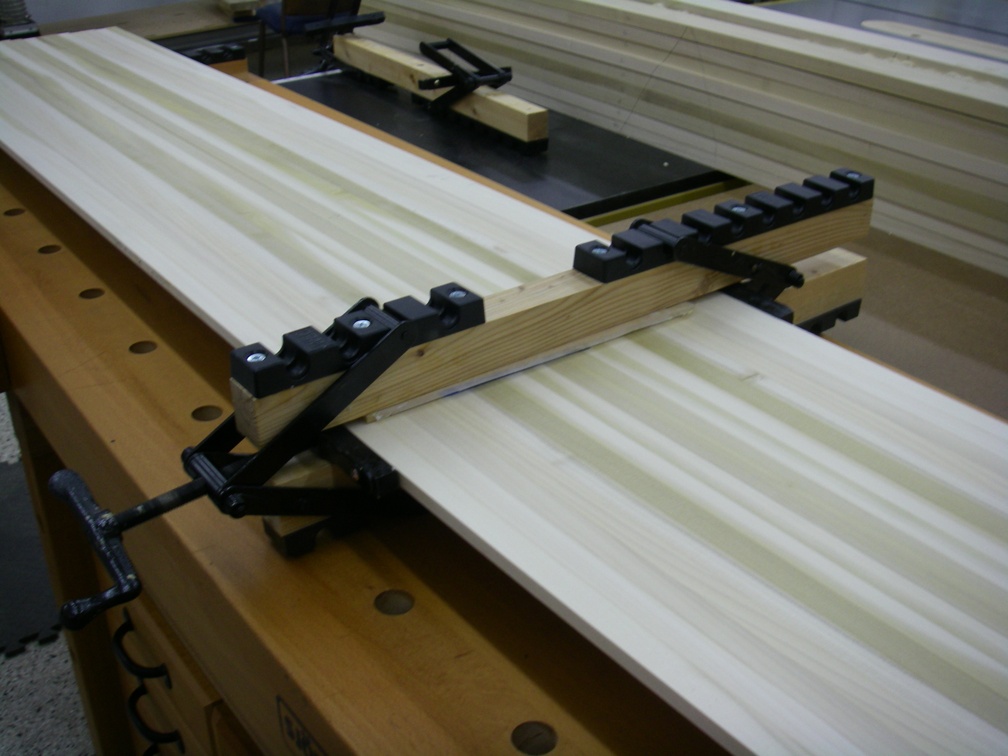
assets/images/FourWayClamp6.JPG
