mikemag/MonkeyWiki/assets/images/FourWayClamp7.JPG

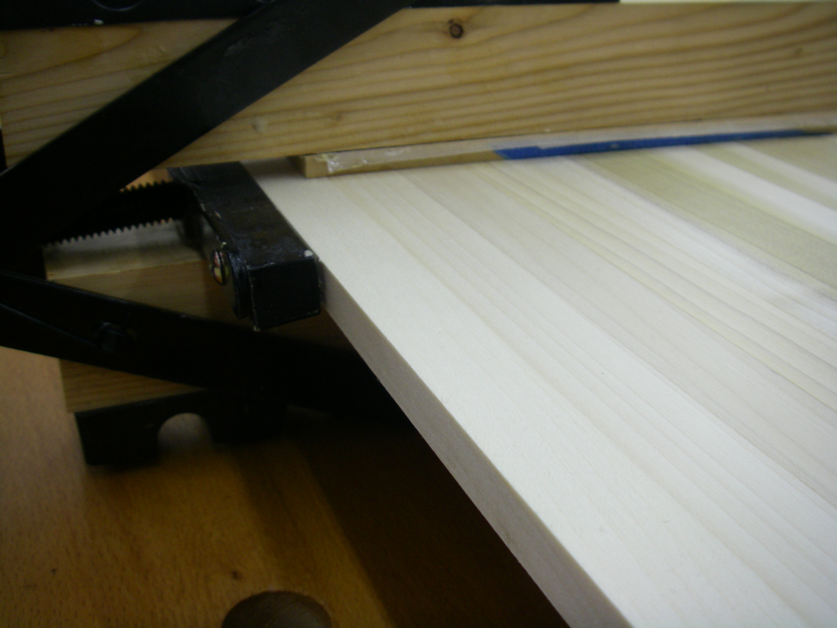
assets/images/FourWayClamp7.JPG
