mikemag/MonkeyWiki/assets/images/Grinder1.JPG

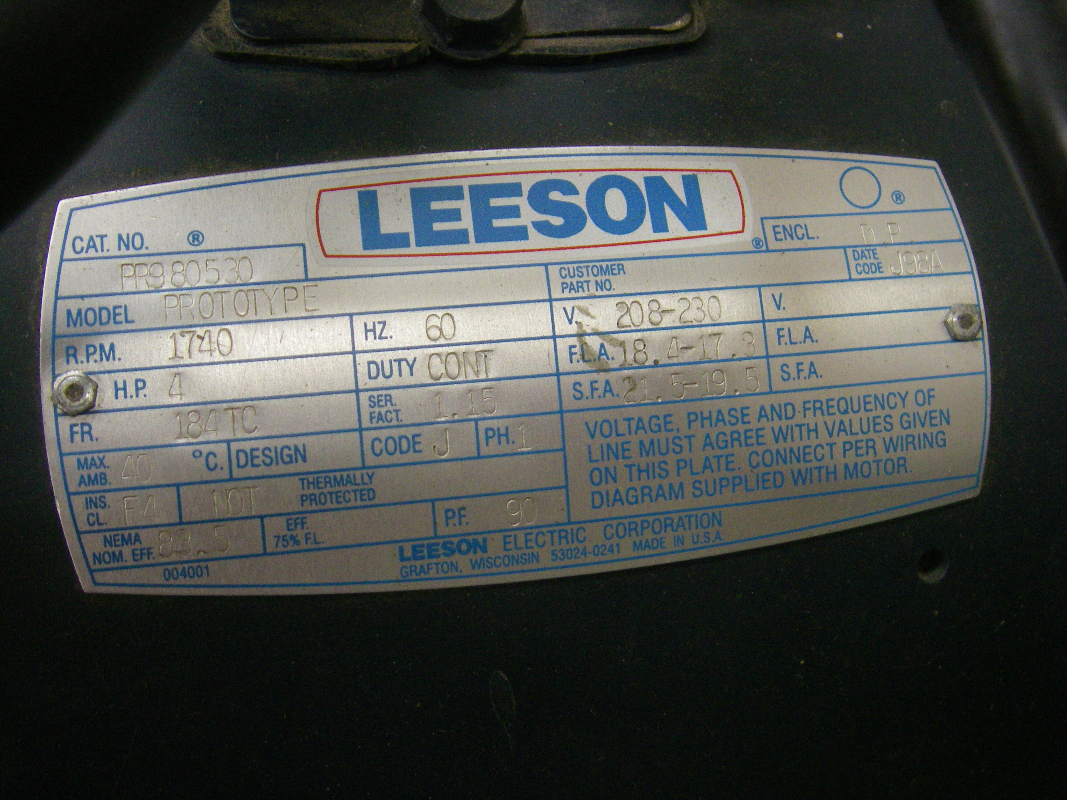
assets/images/Grinder1.JPG
