mikemag/MonkeyWiki/assets/images/Grinder2.JPG

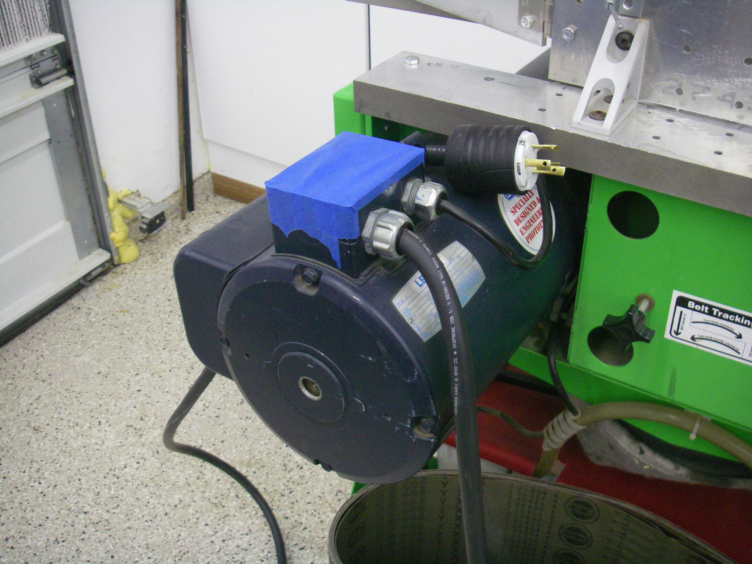
assets/images/Grinder2.JPG
