mikemag/MonkeyWiki/assets/images/Grinder3.JPG

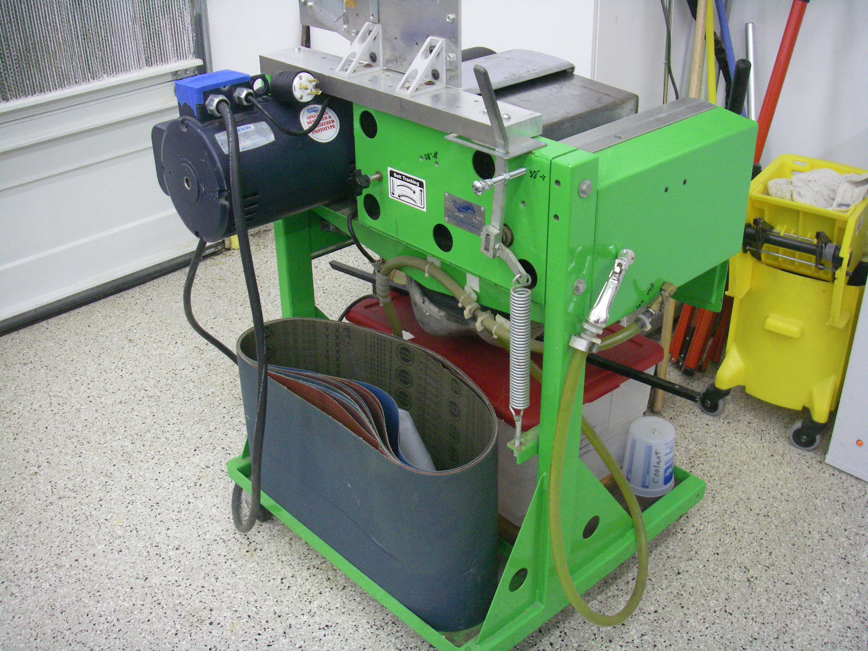
assets/images/Grinder3.JPG
