mikemag/MonkeyWiki/assets/images/Grinder4.JPG

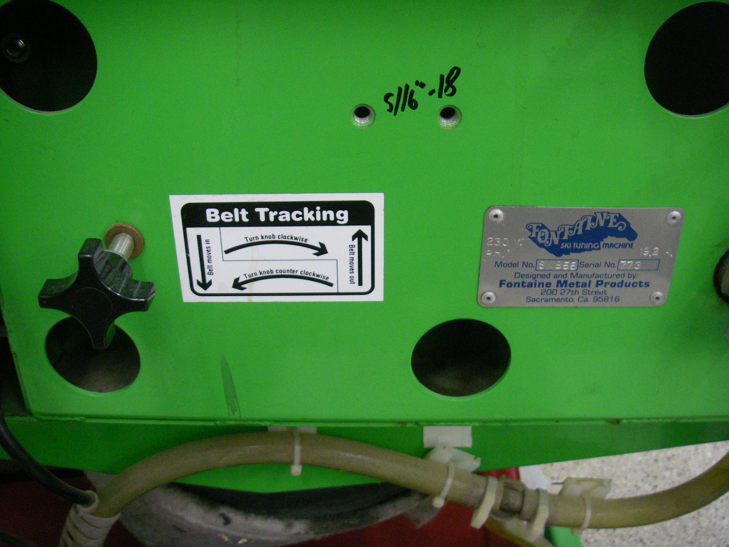
assets/images/Grinder4.JPG
