mikemag/MonkeyWiki/assets/images/Grinder5.JPG

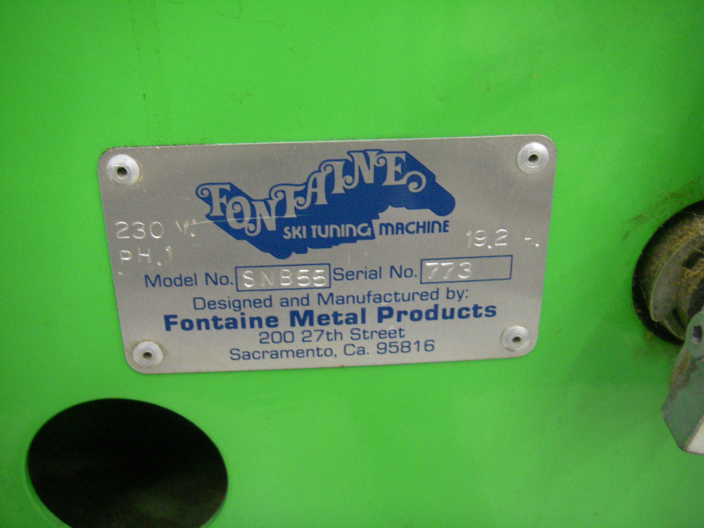
assets/images/Grinder5.JPG
