mikemag/MonkeyWiki/assets/images/Grinder6.JPG

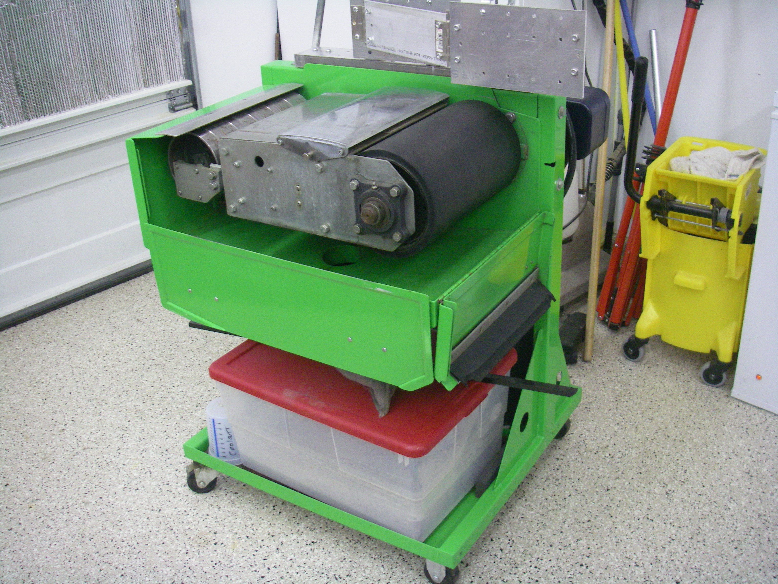
assets/images/Grinder6.JPG
