mikemag/MonkeyWiki/assets/images/Grinder7.JPG

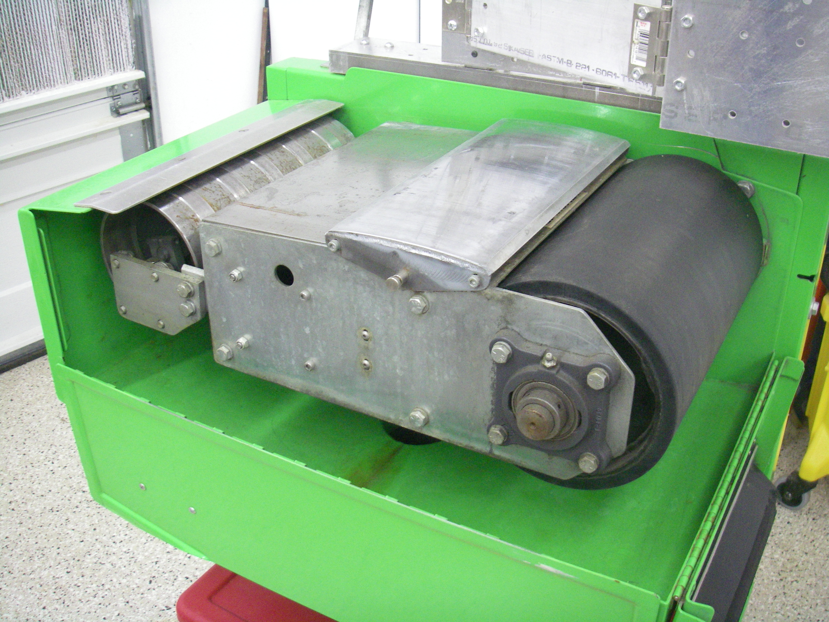
assets/images/Grinder7.JPG
