mikemag/MonkeyWiki/assets/images/Grinder8.JPG

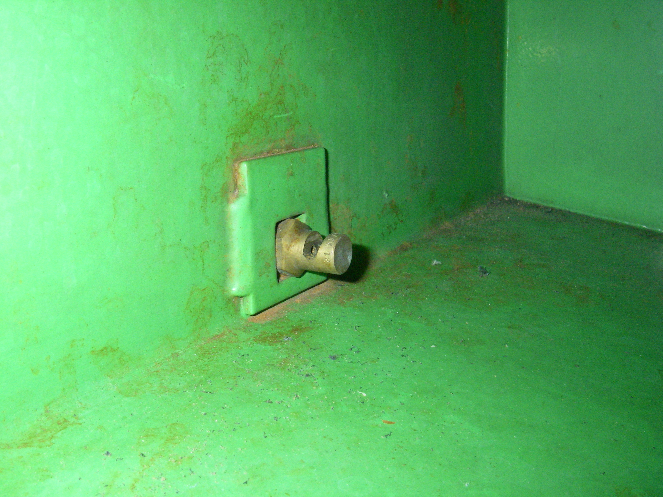
assets/images/Grinder8.JPG
