mikemag/MonkeyWiki/assets/images/Grinder9.JPG

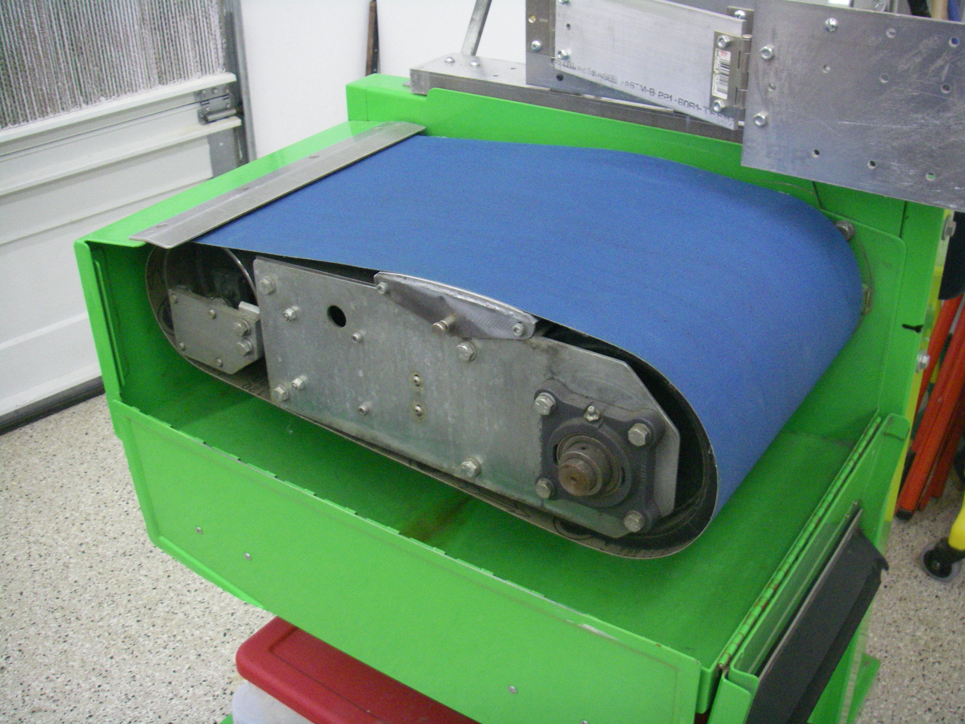
assets/images/Grinder9.JPG
