mikemag/MonkeyWiki/assets/images/Grinder10.JPG

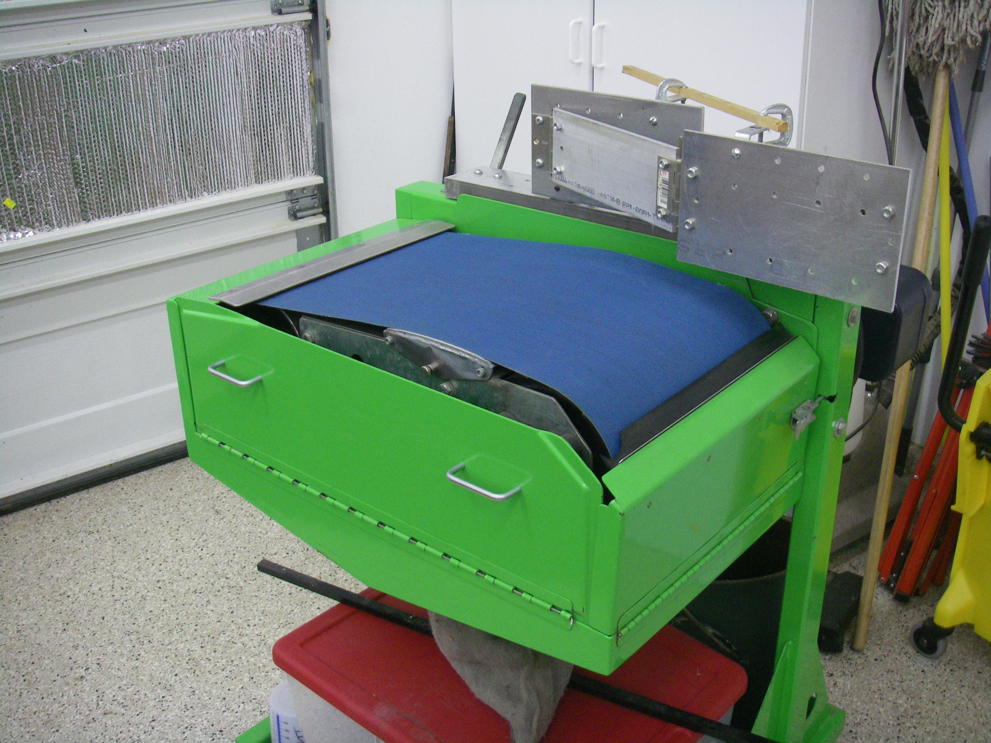
assets/images/Grinder10.JPG
