mikemag/MonkeyWiki/assets/images/Grinder11.JPG

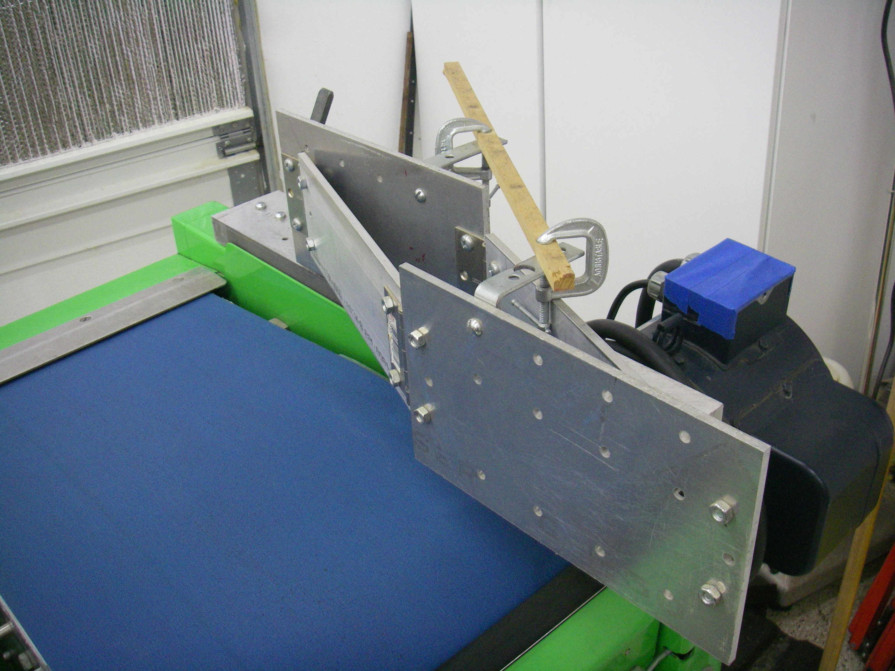
assets/images/Grinder11.JPG
