mikemag/MonkeyWiki/assets/images/Grinder12.JPG

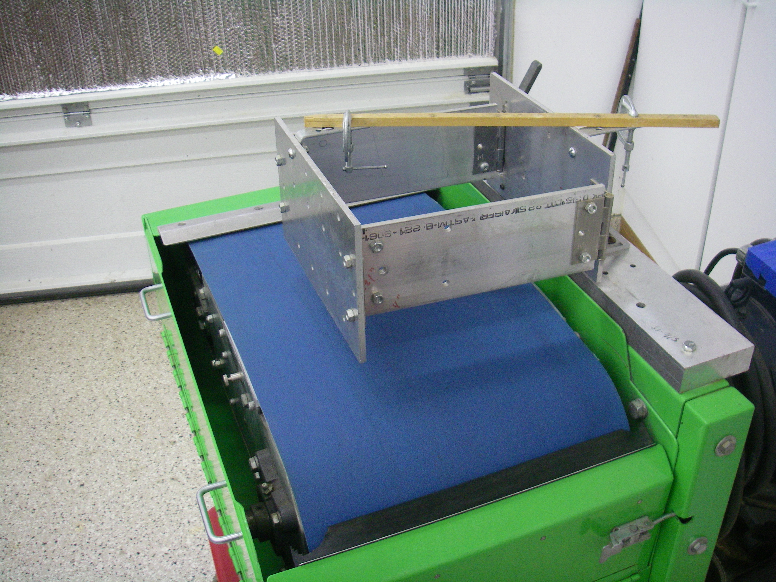
assets/images/Grinder12.JPG
