mikemag/MonkeyWiki/assets/images/Grinder13.JPG

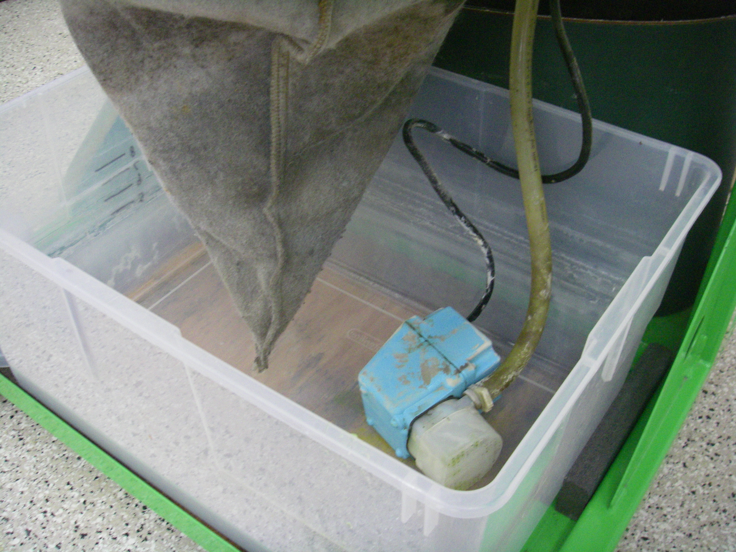
assets/images/Grinder13.JPG
