mikemag/MonkeyWiki/assets/images/Hand_Scraper1.JPG

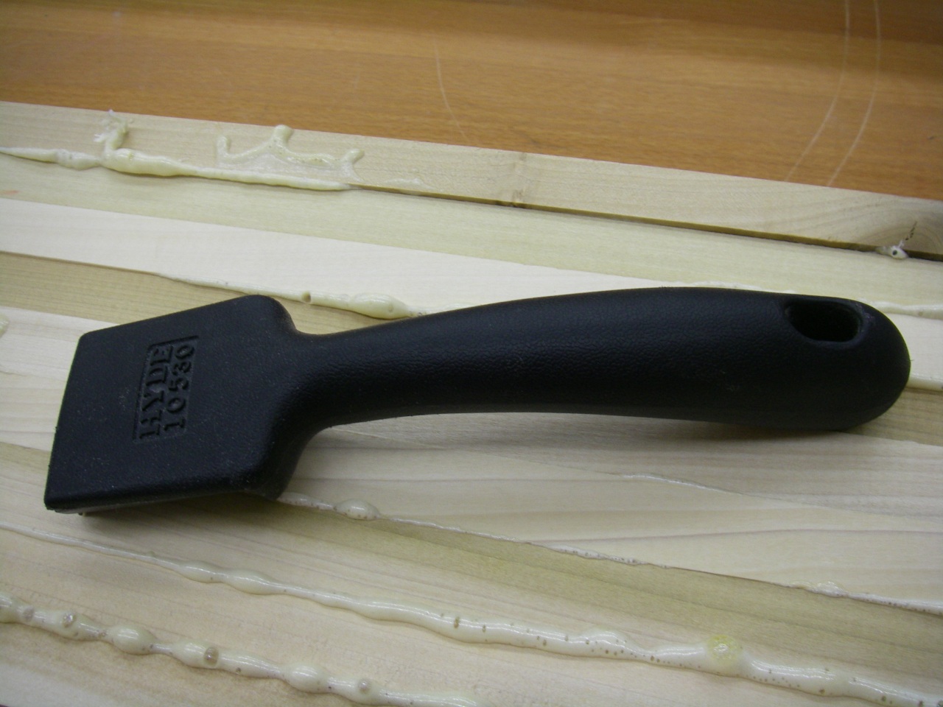
assets/images/Hand_Scraper1.JPG
