mikemag/MonkeyWiki/assets/images/Hand_Scraper2.JPG

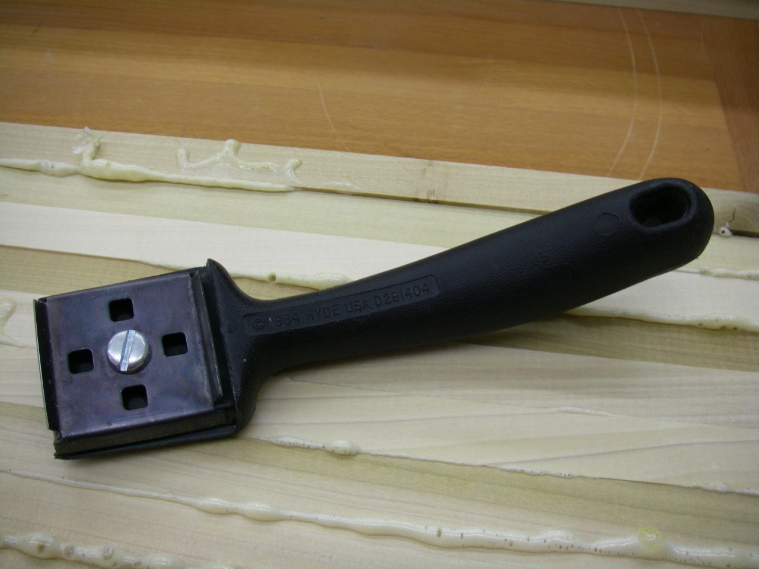
assets/images/Hand_Scraper2.JPG
