mikemag/MonkeyWiki/assets/images/Hand_Scraper3.JPG

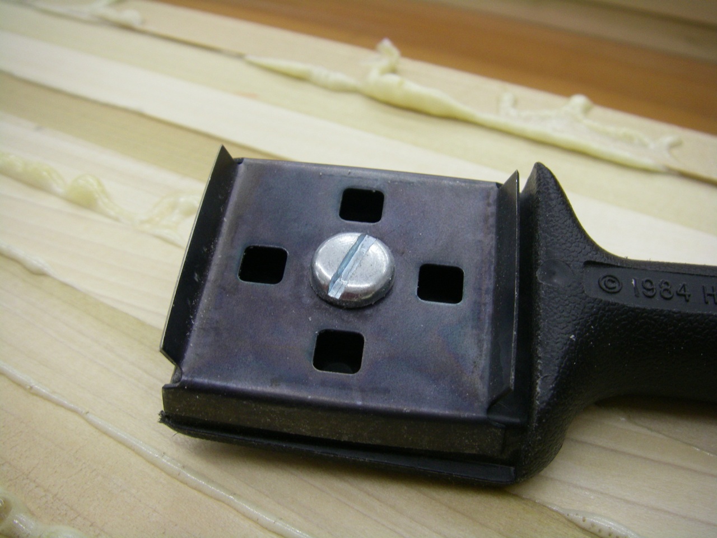
assets/images/Hand_Scraper3.JPG
