mikemag/MonkeyWiki/assets/images/Hotbox_heat.JPG

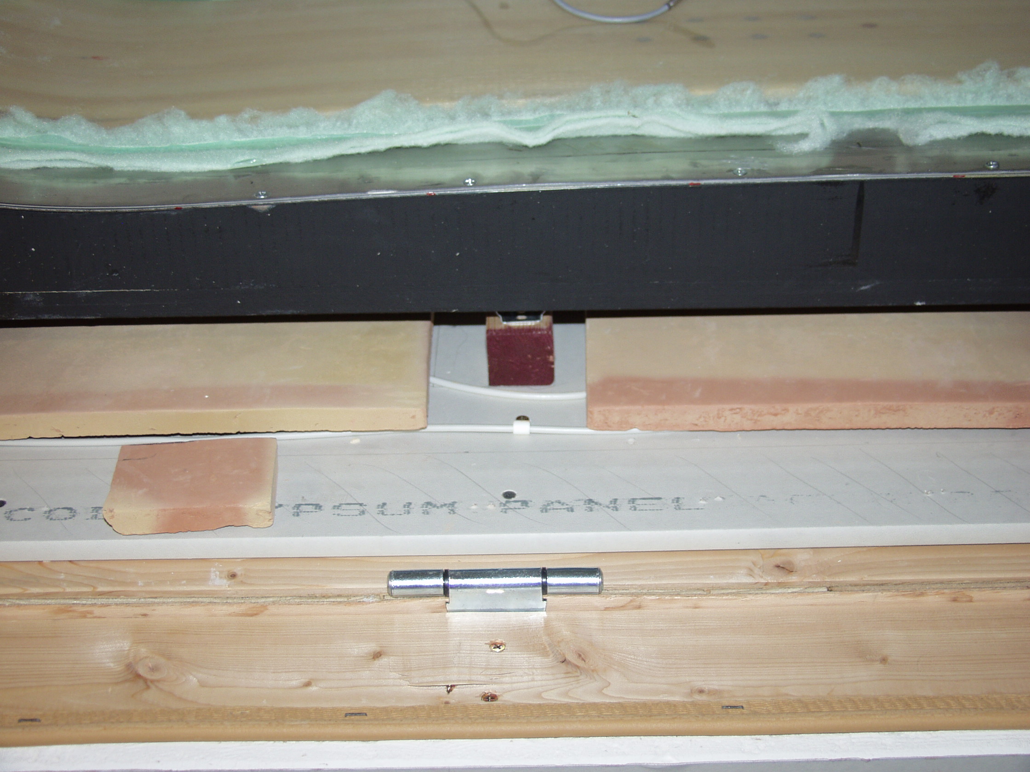
assets/images/Hotbox_heat.JPG
