mikemag/MonkeyWiki/assets/images/Hotbox_interior.JPG

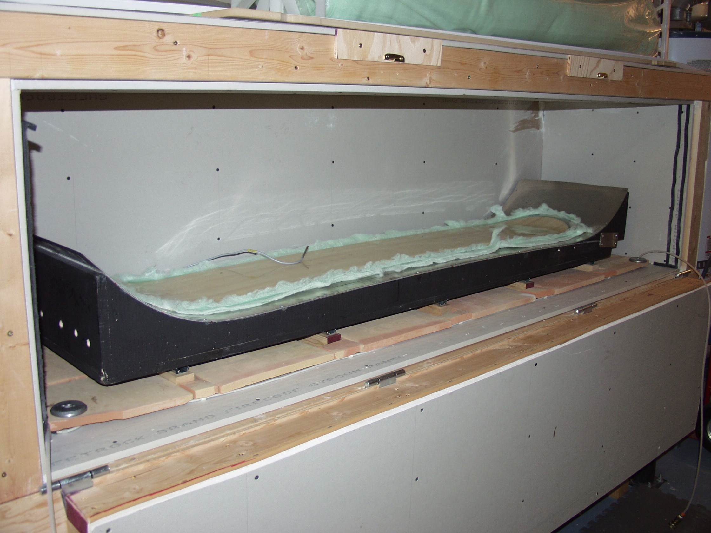
assets/images/Hotbox_interior.JPG
