mikemag/MonkeyWiki/assets/images/Hotbox_open.JPG

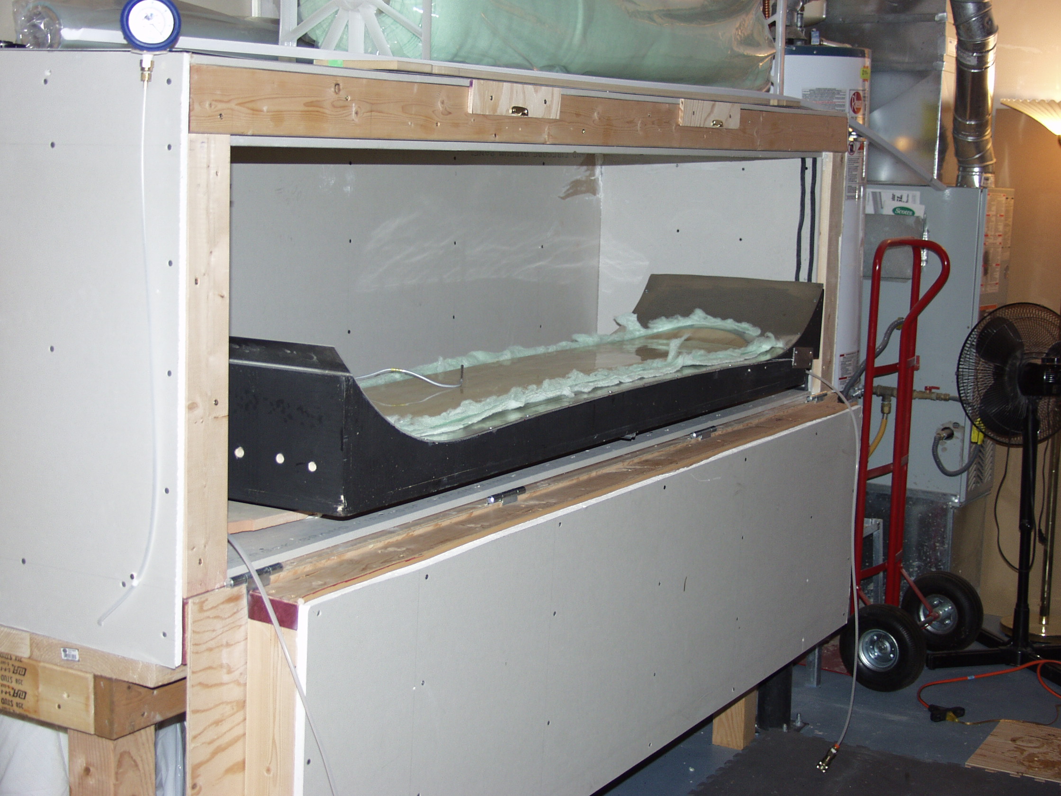
assets/images/Hotbox_open.JPG
