mikemag/MonkeyWiki/assets/images/Hotbox_overview.JPG

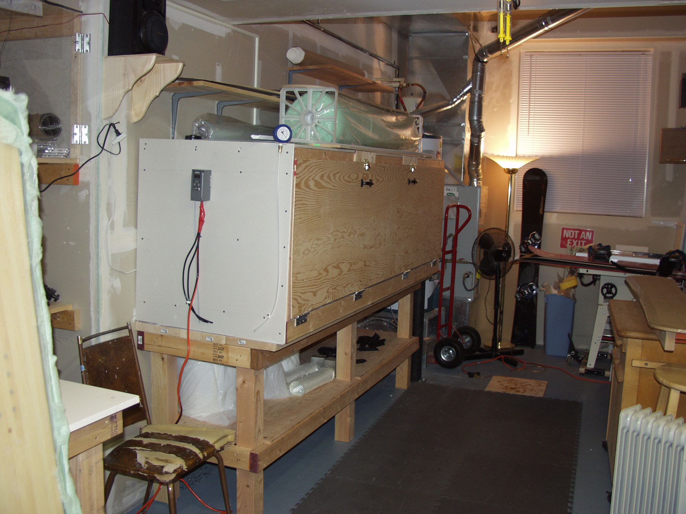
assets/images/Hotbox_overview.JPG
