mikemag/MonkeyWiki/assets/images/Mold_Model_Camber_Section.jpg

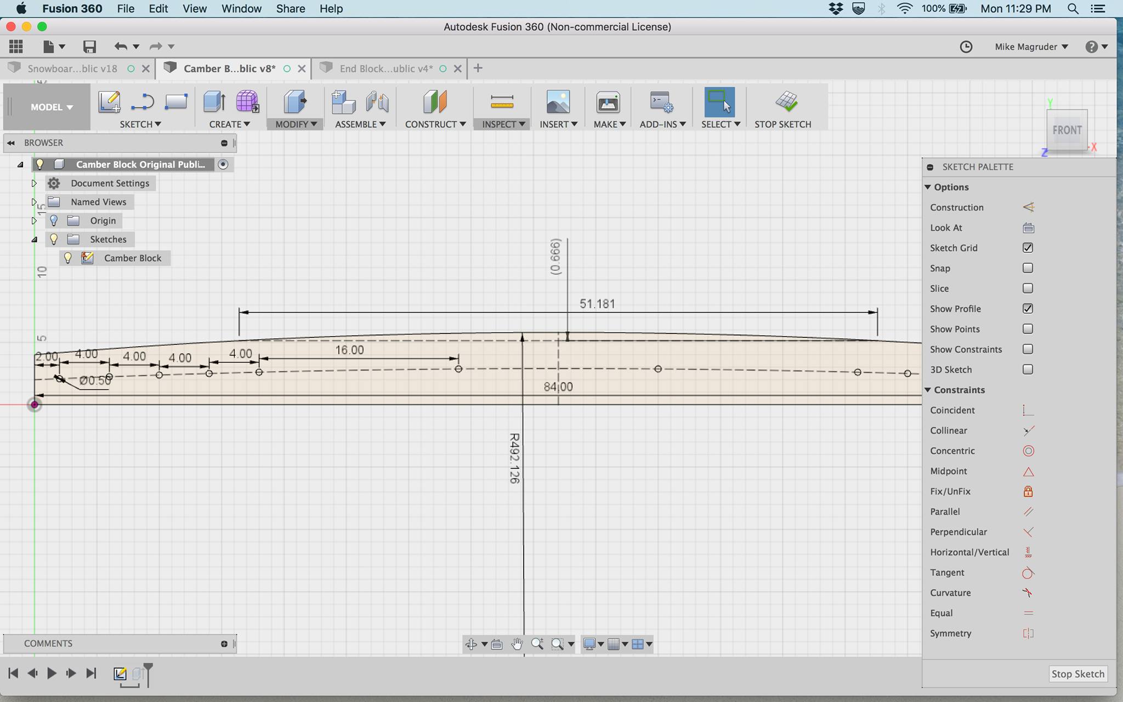
assets/images/Mold_Model_Camber_Section.jpg
