mikemag/MonkeyWiki/assets/images/Mold_Model_Full.jpg

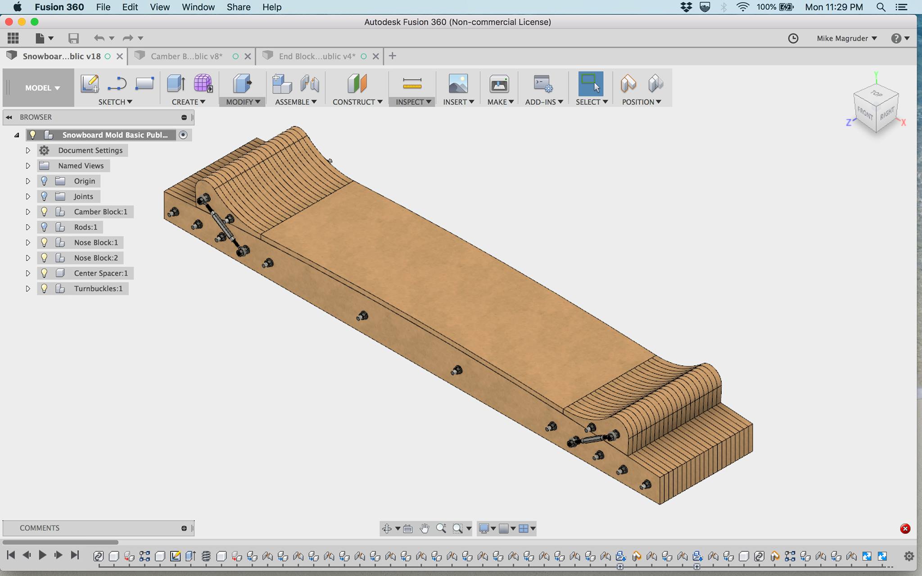
assets/images/Mold_Model_Full.jpg
