mikemag/MonkeyWiki/assets/images/Mold_Model_Full_Exploded.jpg

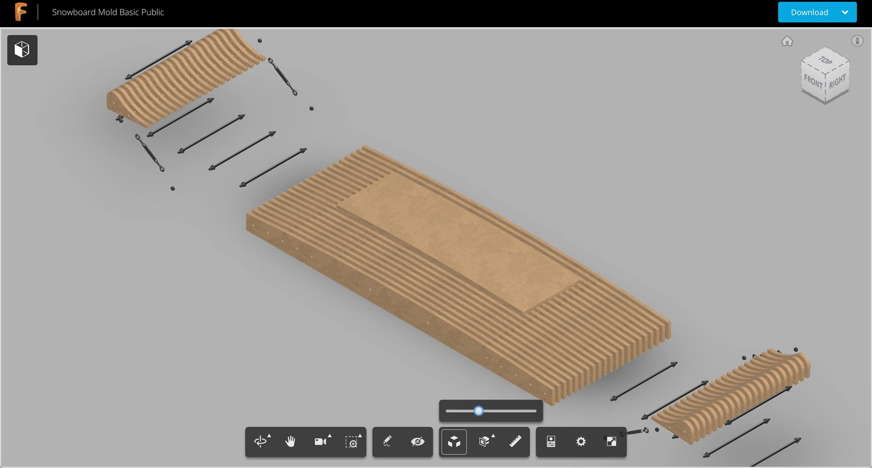
assets/images/Mold_Model_Full_Exploded.jpg
