mikemag/MonkeyWiki/assets/images/Mold_Model_Nose_Block.jpg

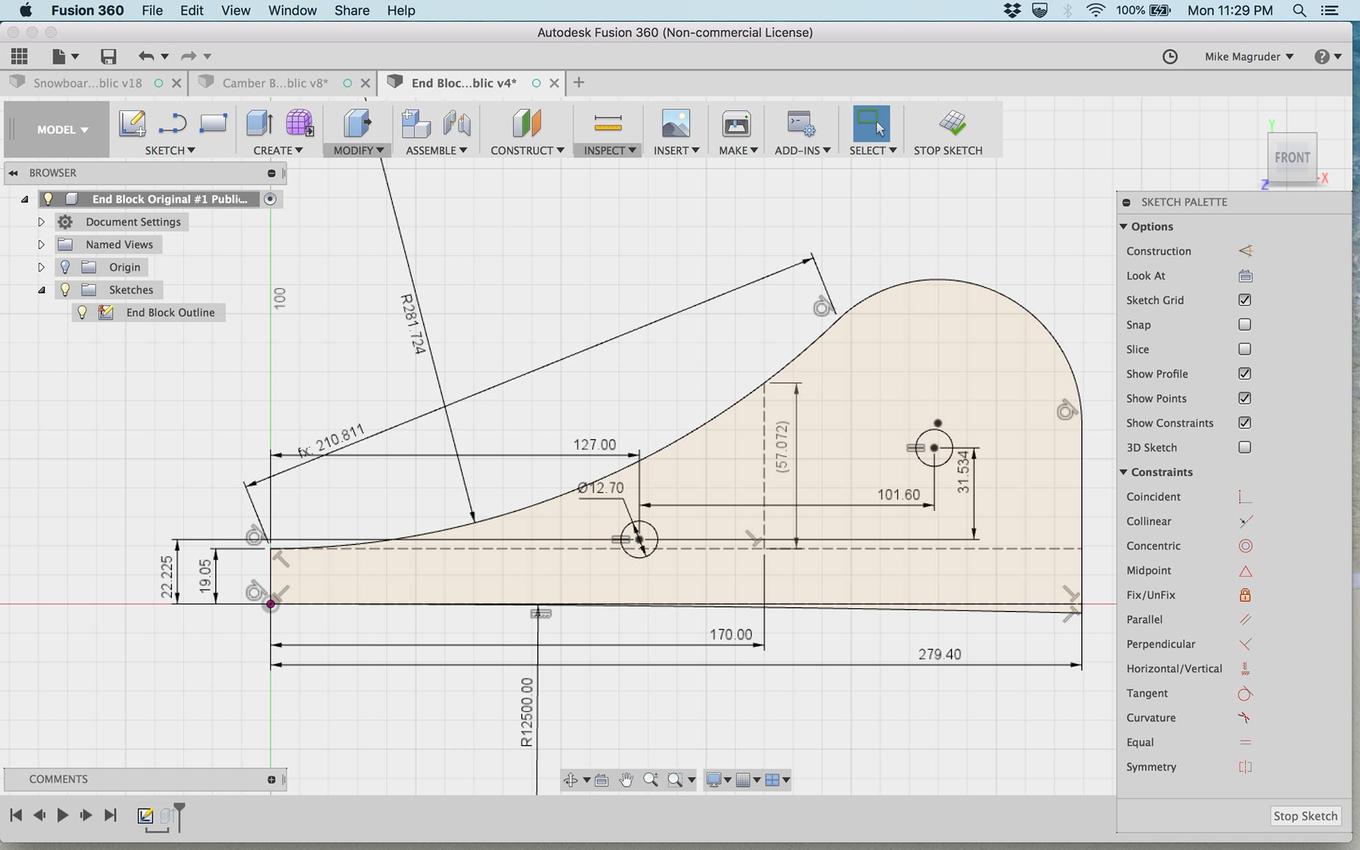
assets/images/Mold_Model_Nose_Block.jpg
