mikemag/MonkeyWiki/assets/images/Monkey_Press_Mold.jpg

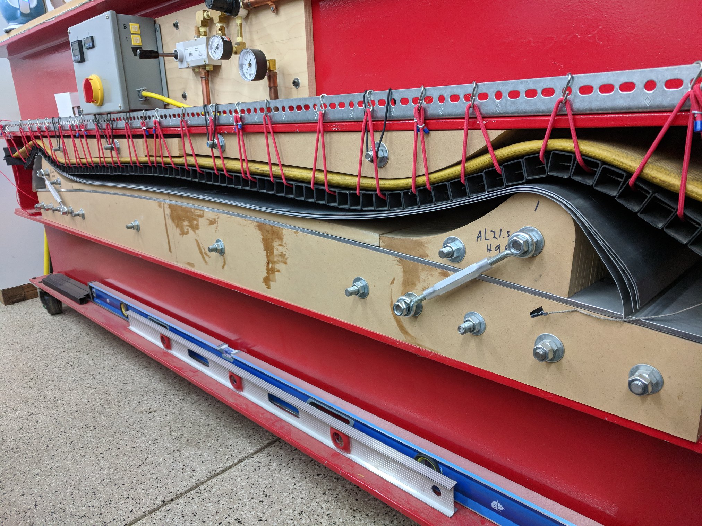
assets/images/Monkey_Press_Mold.jpg
