mikemag/MonkeyWiki/assets/images/Nippers1.JPG

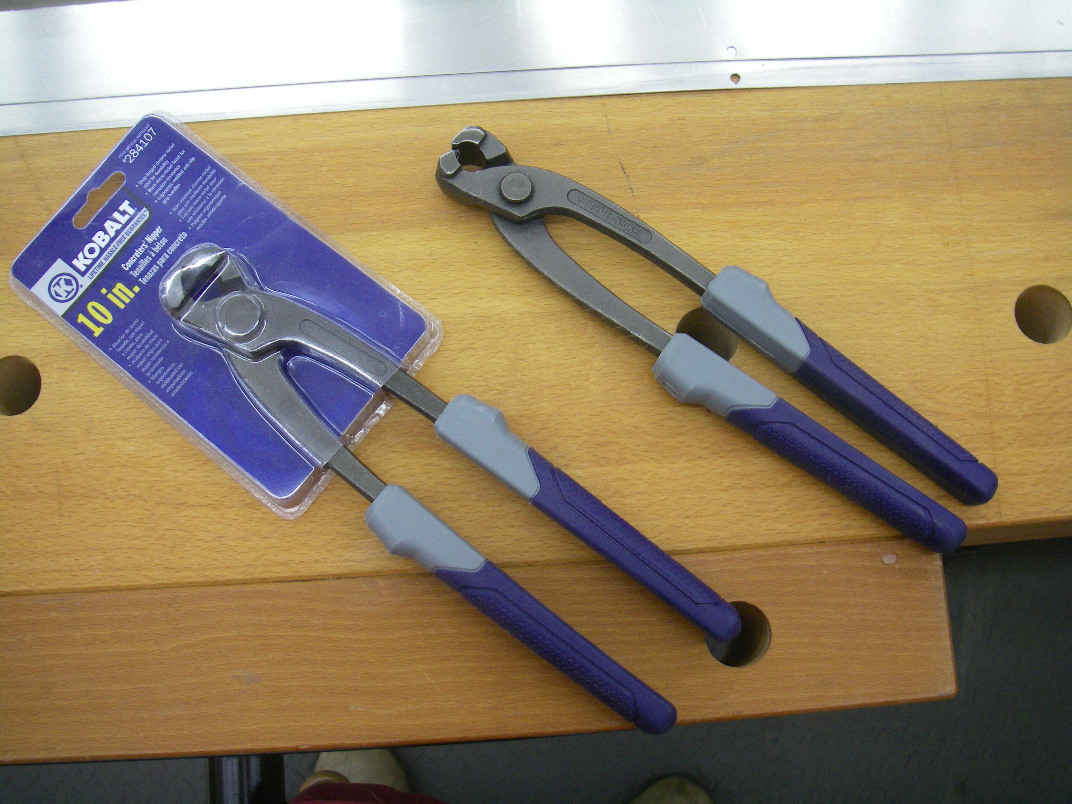
assets/images/Nippers1.JPG
