mikemag/MonkeyWiki/assets/images/Nippers2.JPG

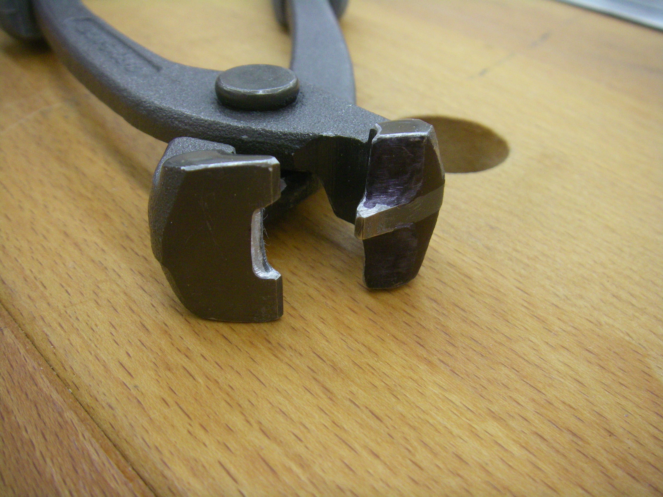
assets/images/Nippers2.JPG
