mikemag/MonkeyWiki/assets/images/Nippers3.JPG

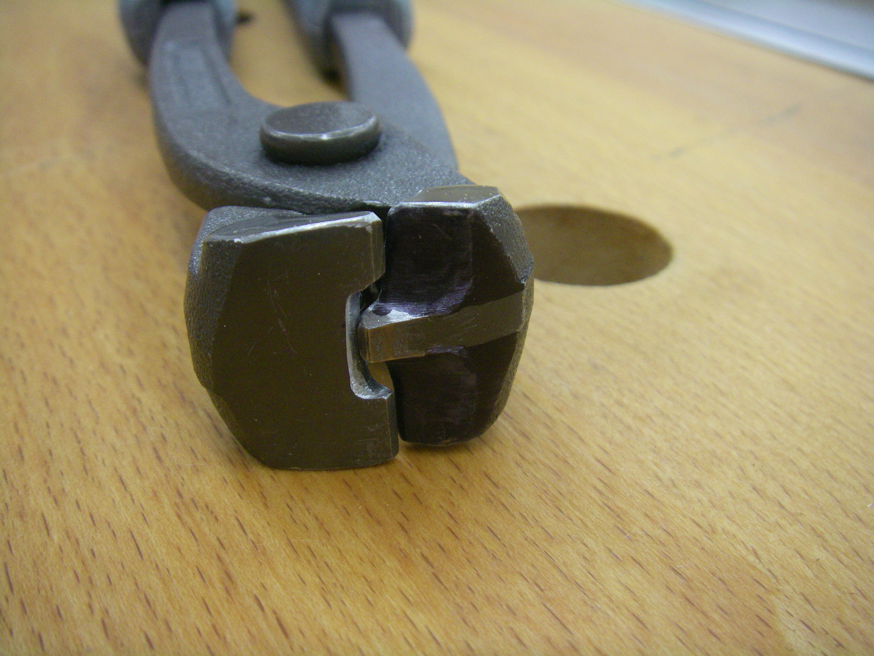
assets/images/Nippers3.JPG
