mikemag/MonkeyWiki/assets/images/Nippers4.JPG

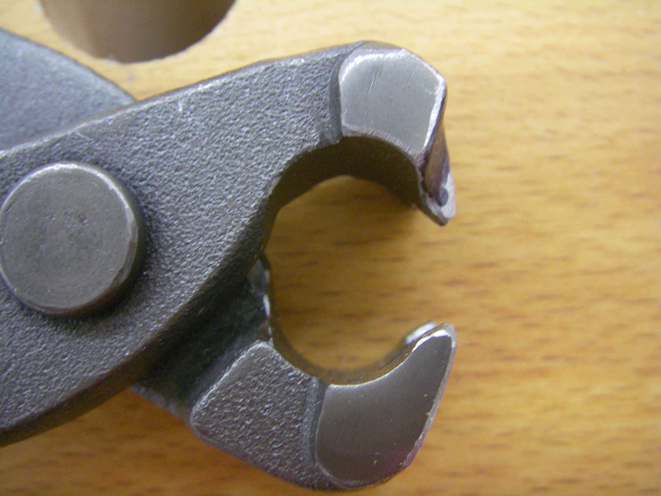
assets/images/Nippers4.JPG
