mikemag/MonkeyWiki/assets/images/Nippers5.JPG

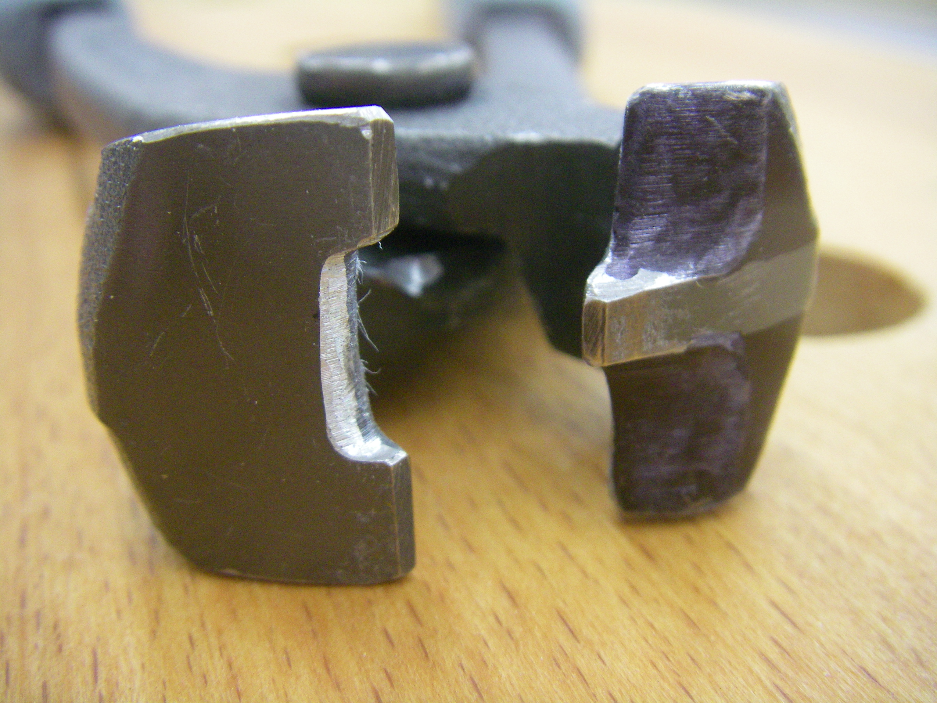
assets/images/Nippers5.JPG
