mikemag/MonkeyWiki/assets/images/Nippers6.JPG

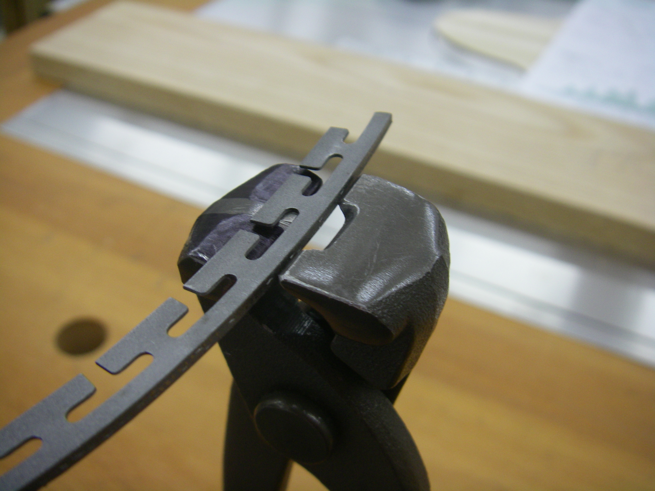
assets/images/Nippers6.JPG
