mikemag/MonkeyWiki/assets/images/Nippers7.JPG

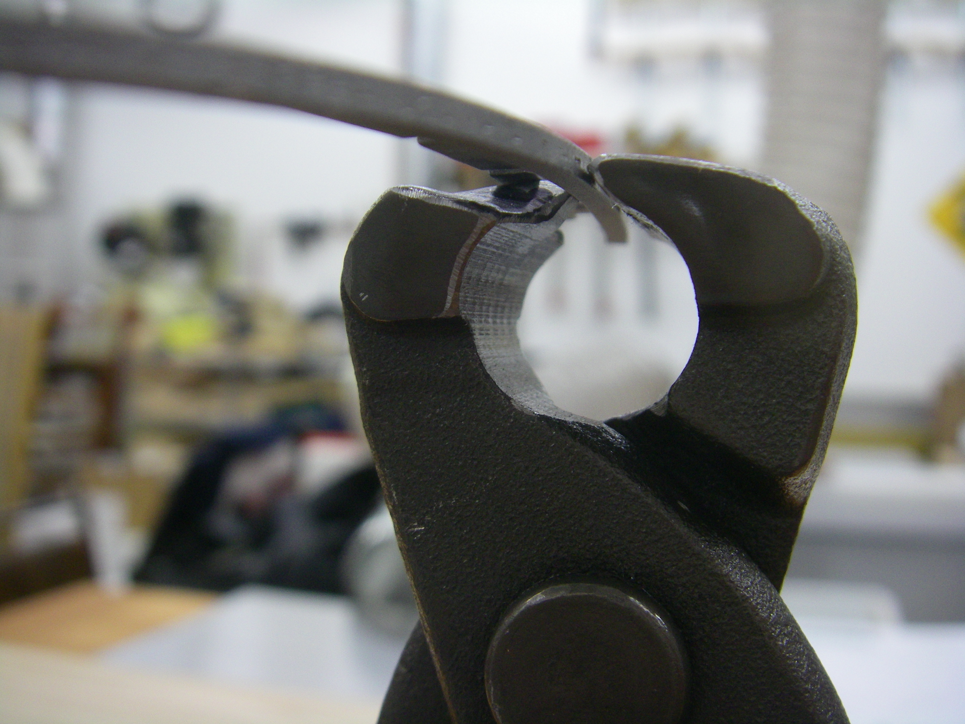
assets/images/Nippers7.JPG
