mikemag/MonkeyWiki/assets/images/Nippers8.JPG

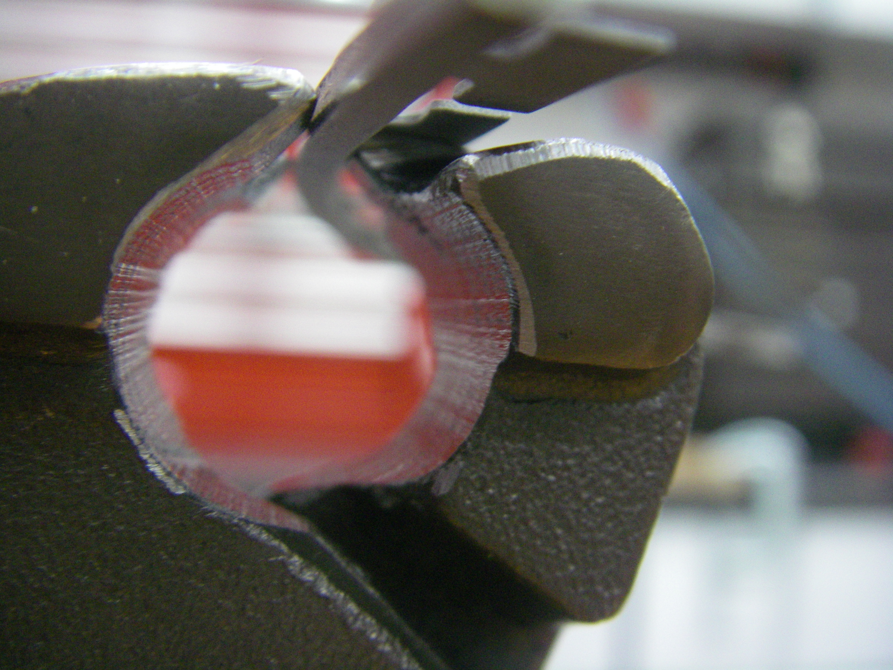
assets/images/Nippers8.JPG
