mikemag/MonkeyWiki/assets/images/Nippers9.JPG

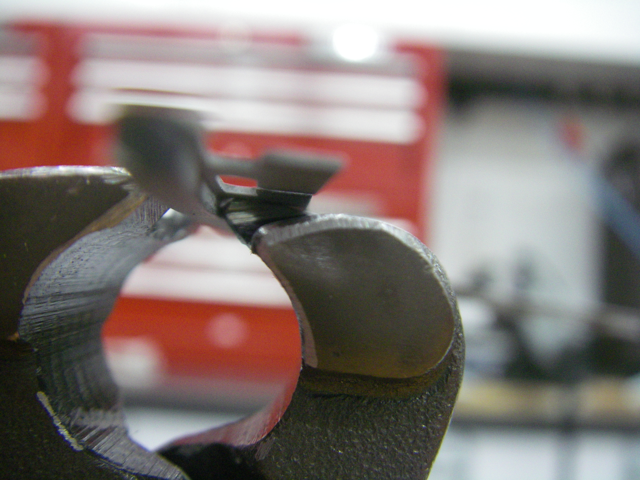
assets/images/Nippers9.JPG
