mikemag/MonkeyWiki/assets/images/Nippers10.JPG

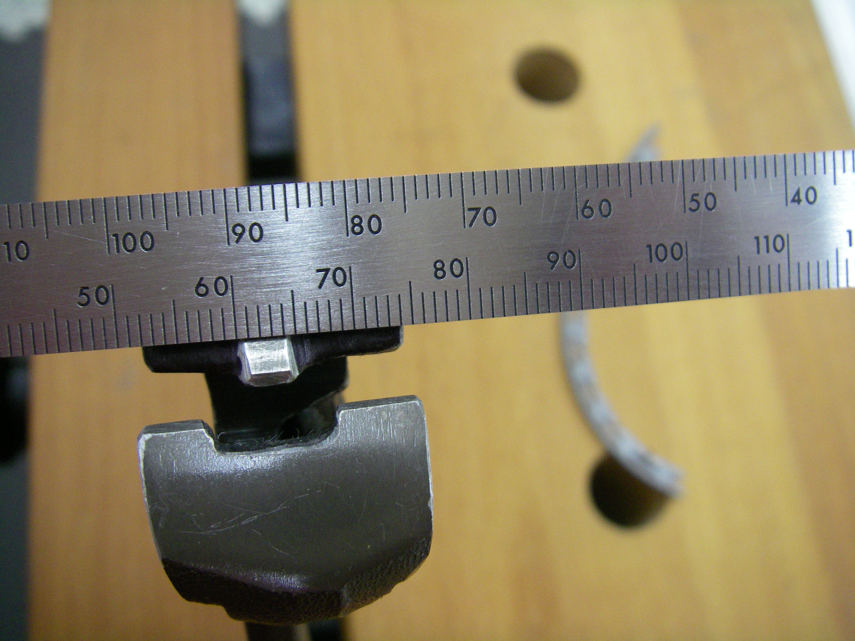
assets/images/Nippers10.JPG
