mikemag/MonkeyWiki/assets/images/NoseTailSpacers1.JPG

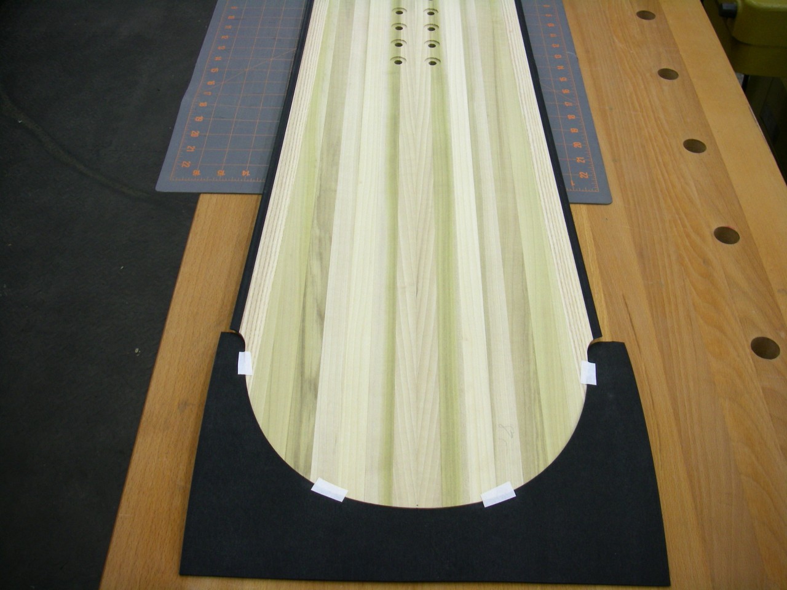
assets/images/NoseTailSpacers1.JPG
