mikemag/MonkeyWiki/assets/images/NoseTailSpacers2.JPG

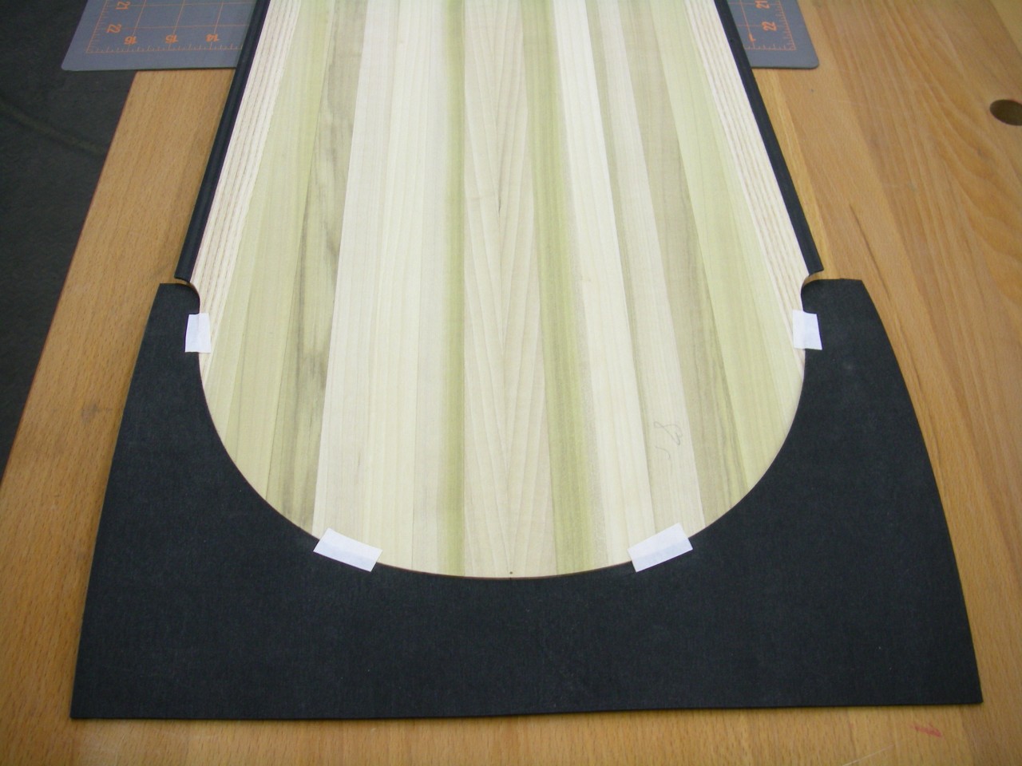
assets/images/NoseTailSpacers2.JPG
