mikemag/MonkeyWiki/assets/images/PC296816.JPG

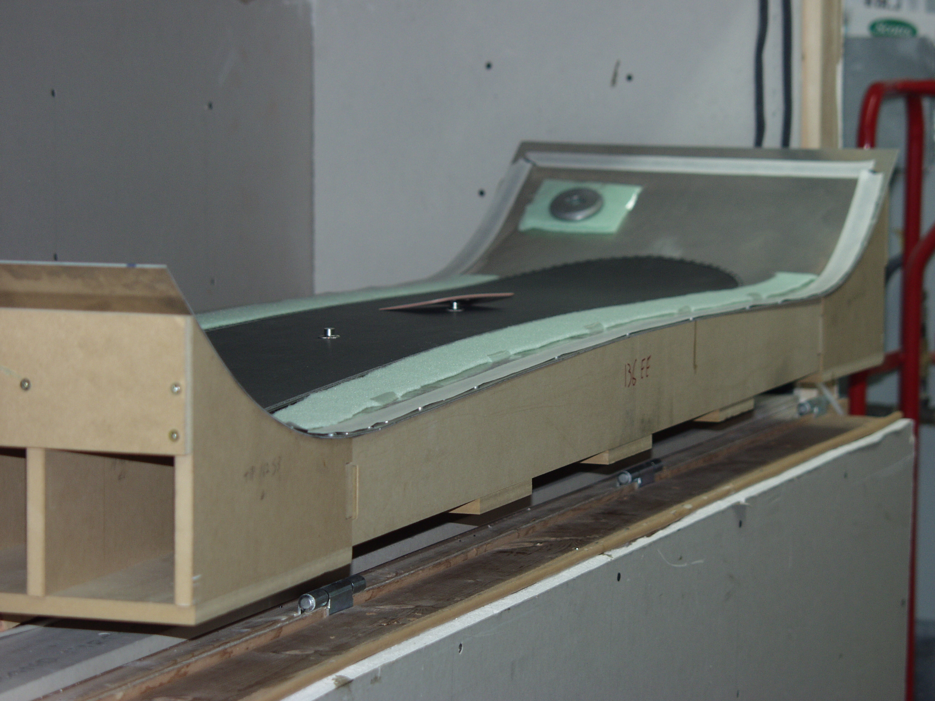
assets/images/PC296816.JPG
