mikemag/MonkeyWiki/assets/images/PC296822.JPG

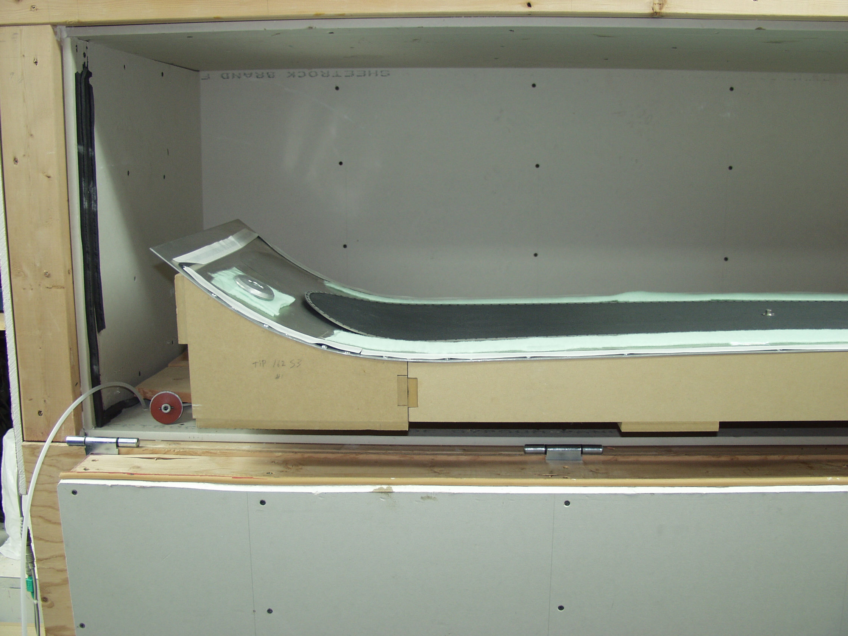
assets/images/PC296822.JPG
