mikemag/MonkeyWiki/assets/images/PC296823.JPG

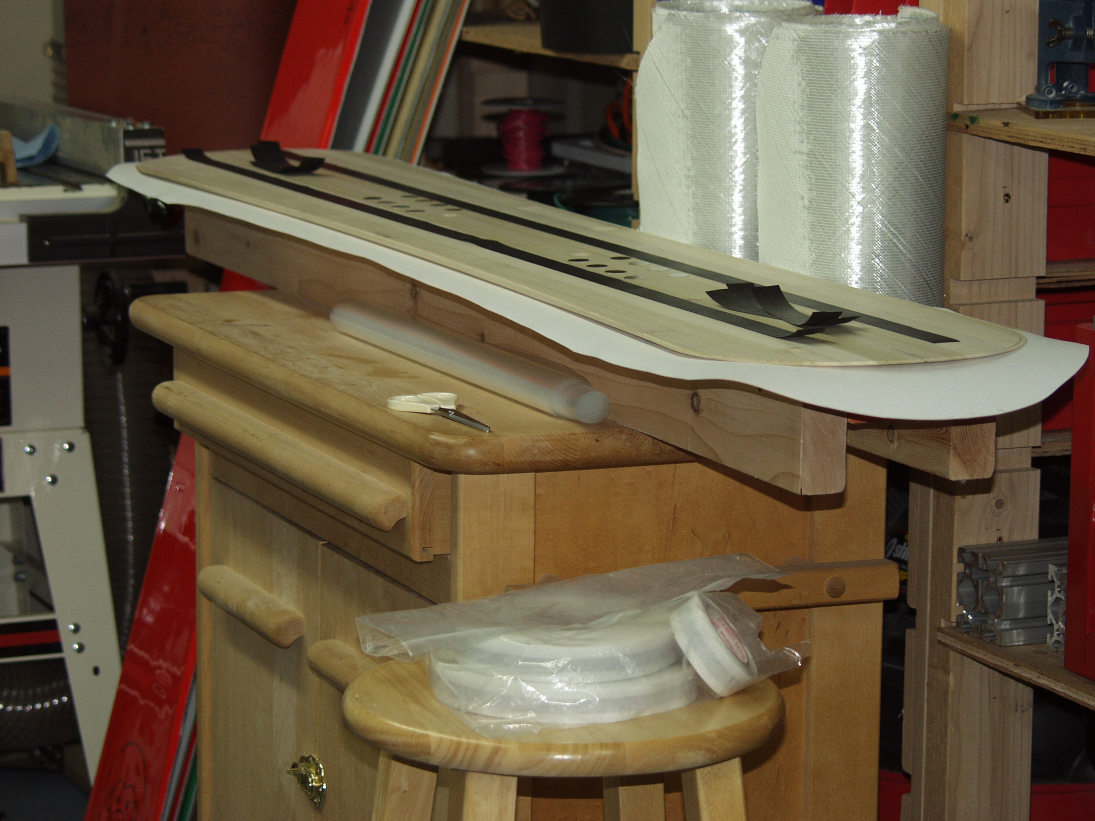
assets/images/PC296823.JPG
