mikemag/MonkeyWiki/assets/images/PC296825.JPG

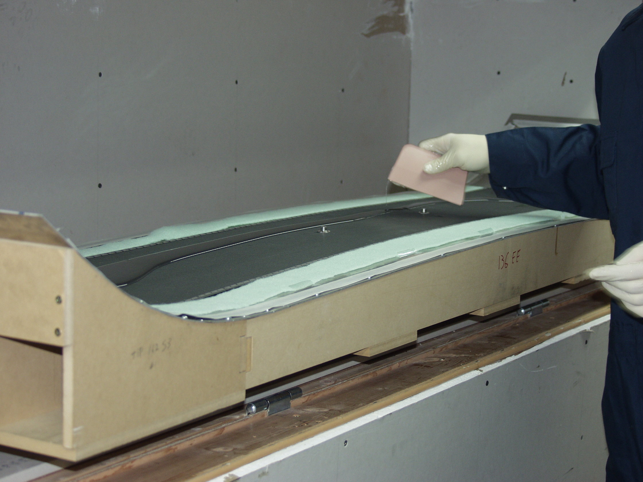
assets/images/PC296825.JPG
