mikemag/MonkeyWiki/assets/images/PC296826.JPG

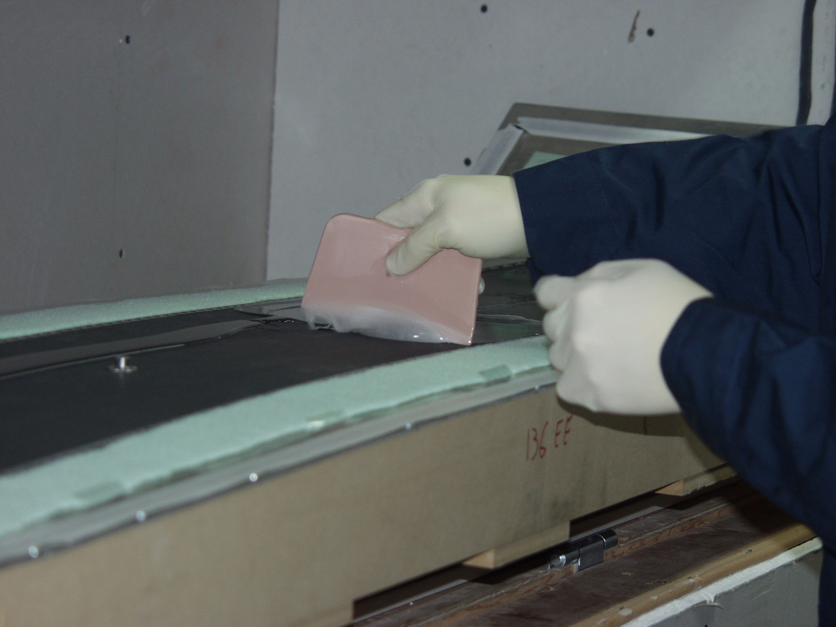
assets/images/PC296826.JPG
