mikemag/MonkeyWiki/assets/images/PC296827.JPG

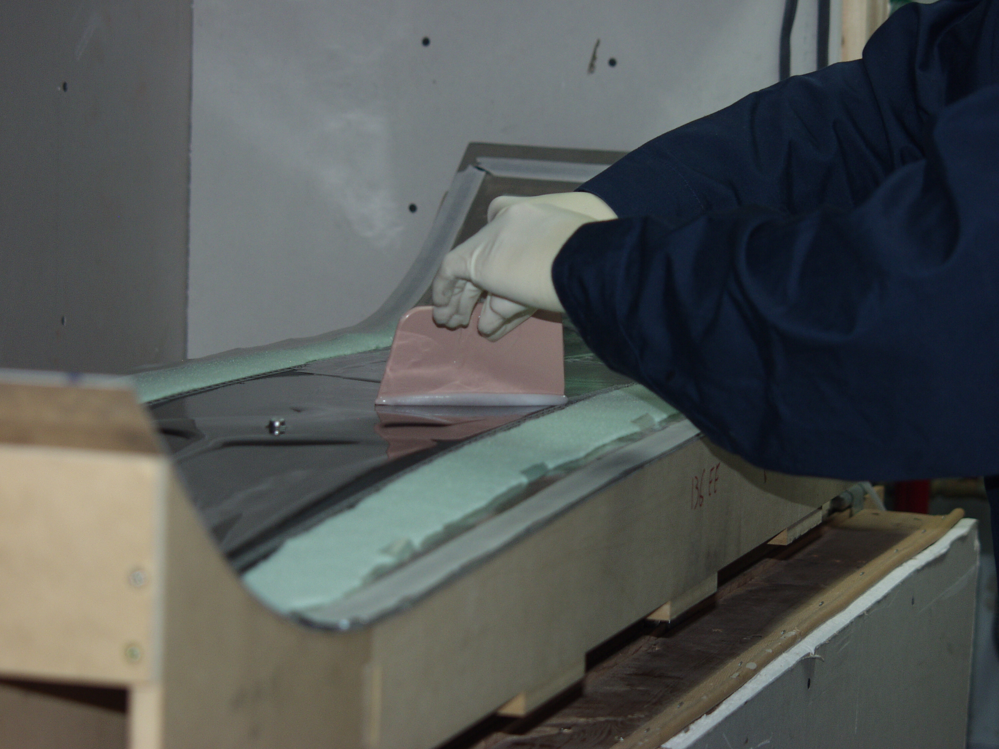
assets/images/PC296827.JPG
