mikemag/MonkeyWiki/assets/images/PC296830.JPG

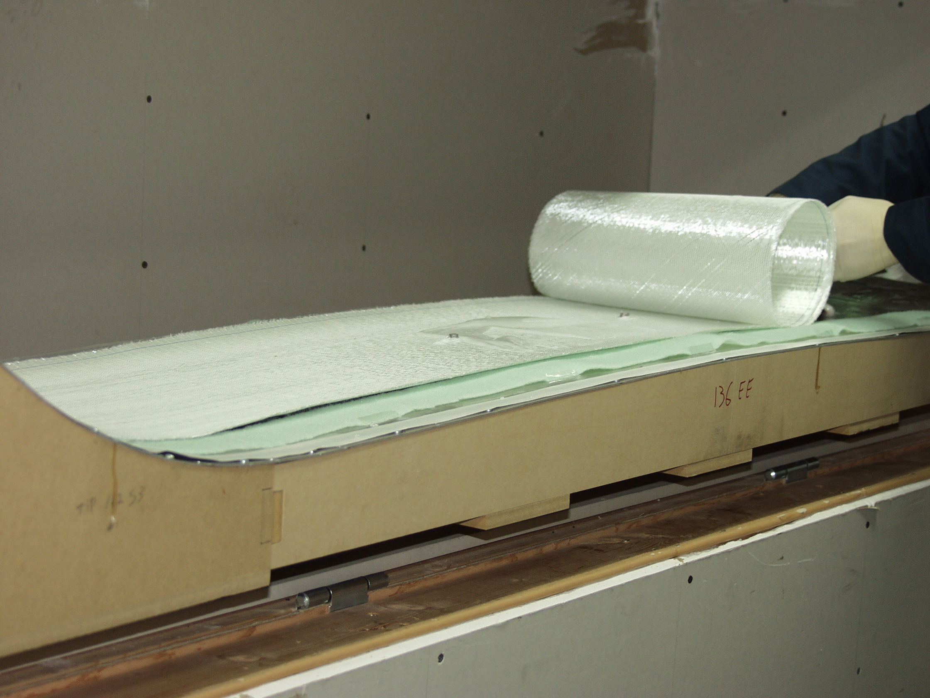
assets/images/PC296830.JPG
