mikemag/MonkeyWiki/assets/images/PC296832.JPG

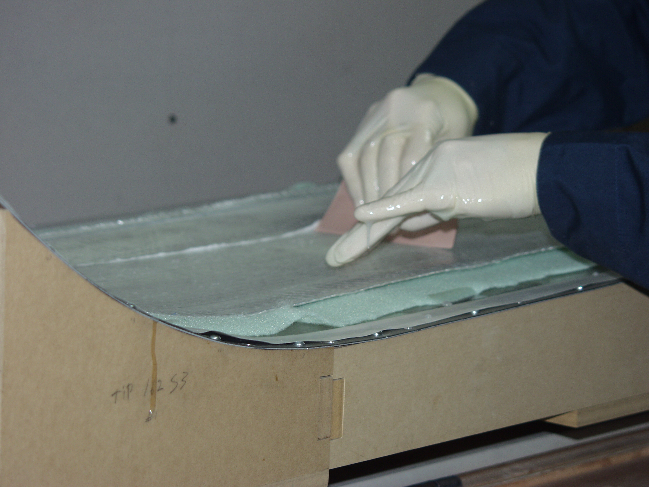
assets/images/PC296832.JPG
