mikemag/MonkeyWiki/assets/images/PC296836.JPG

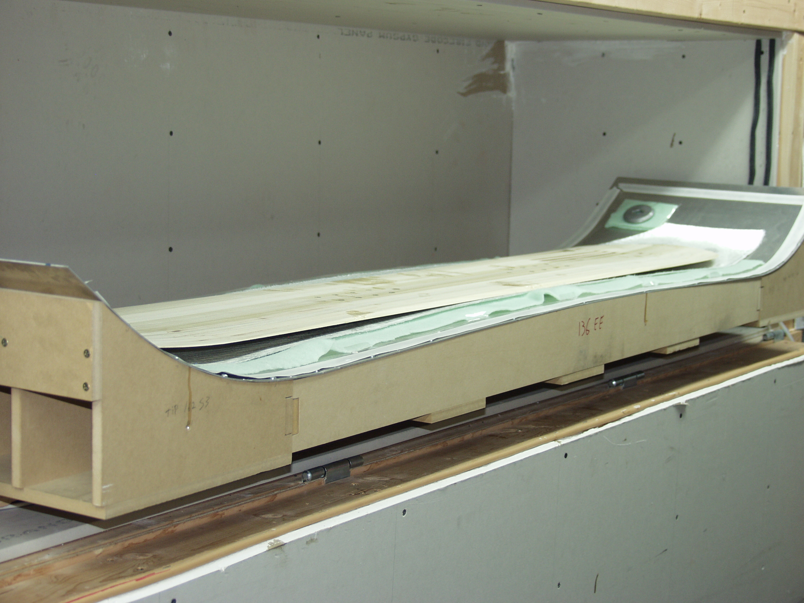
assets/images/PC296836.JPG
