mikemag/MonkeyWiki/assets/images/PC296838.JPG

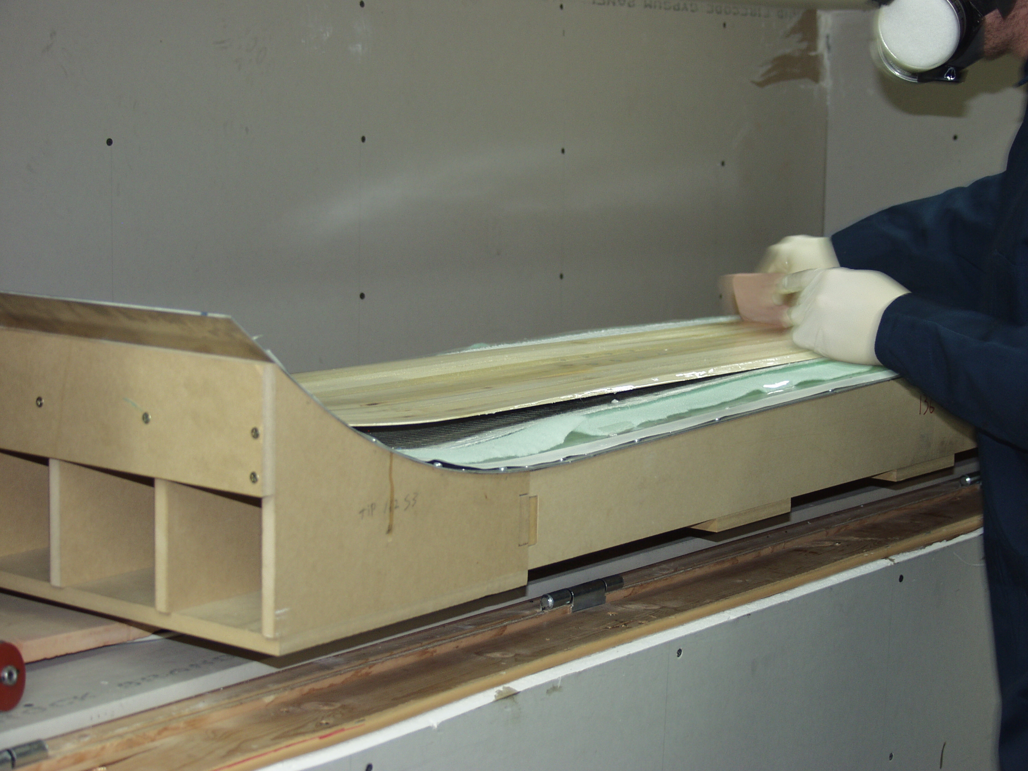
assets/images/PC296838.JPG
