mikemag/MonkeyWiki/assets/images/PC296839.JPG

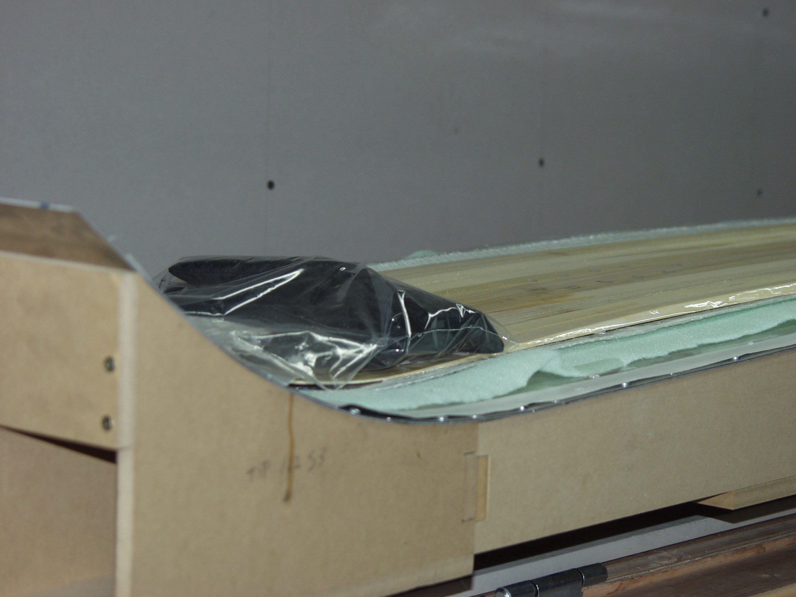
assets/images/PC296839.JPG
