mikemag/MonkeyWiki/assets/images/PC296840.JPG

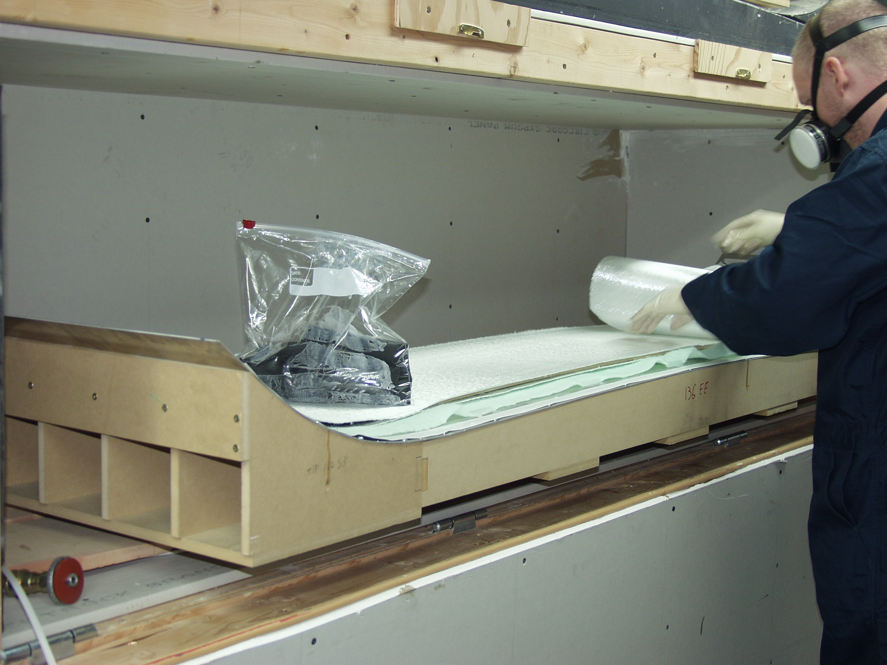
assets/images/PC296840.JPG
