mikemag/MonkeyWiki/assets/images/PC296842.JPG

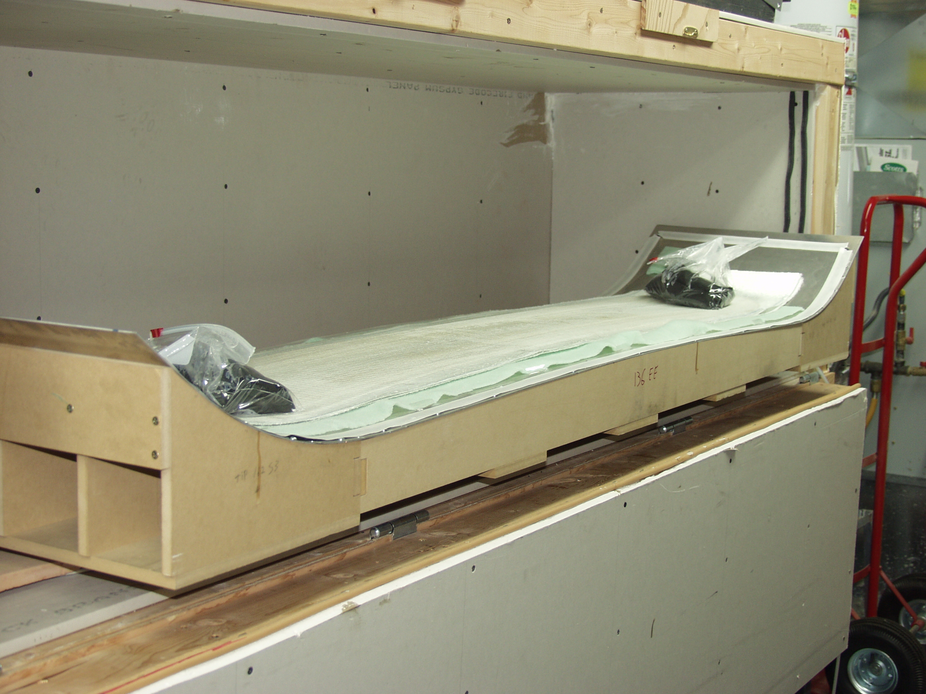
assets/images/PC296842.JPG
