mikemag/MonkeyWiki/assets/images/PC296847.JPG

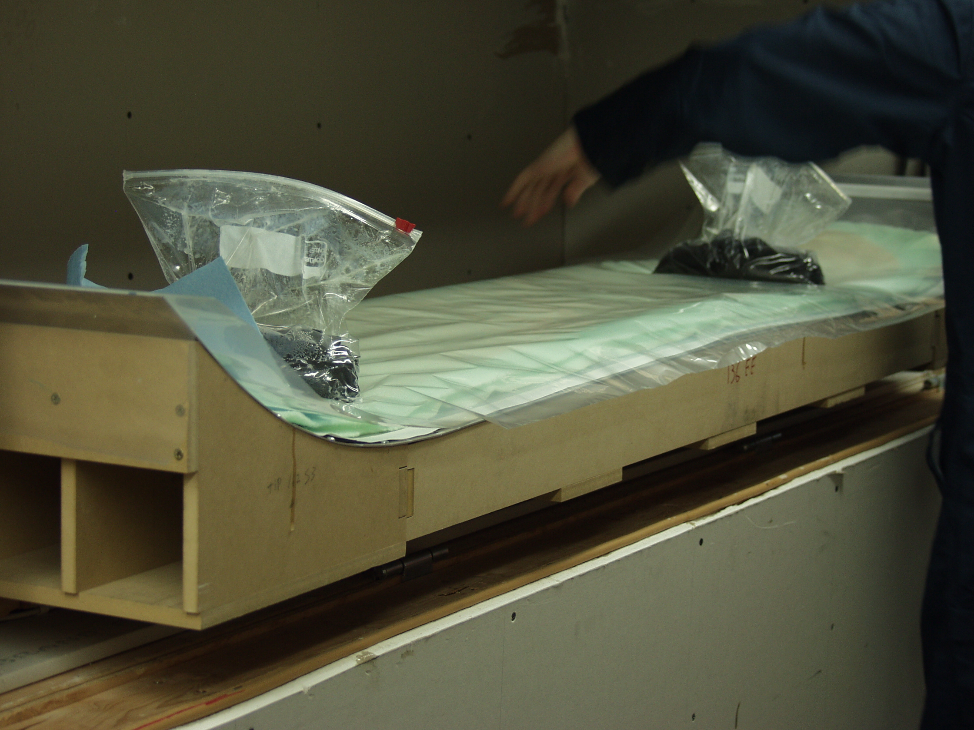
assets/images/PC296847.JPG
