mikemag/MonkeyWiki/assets/images/PC296848.JPG

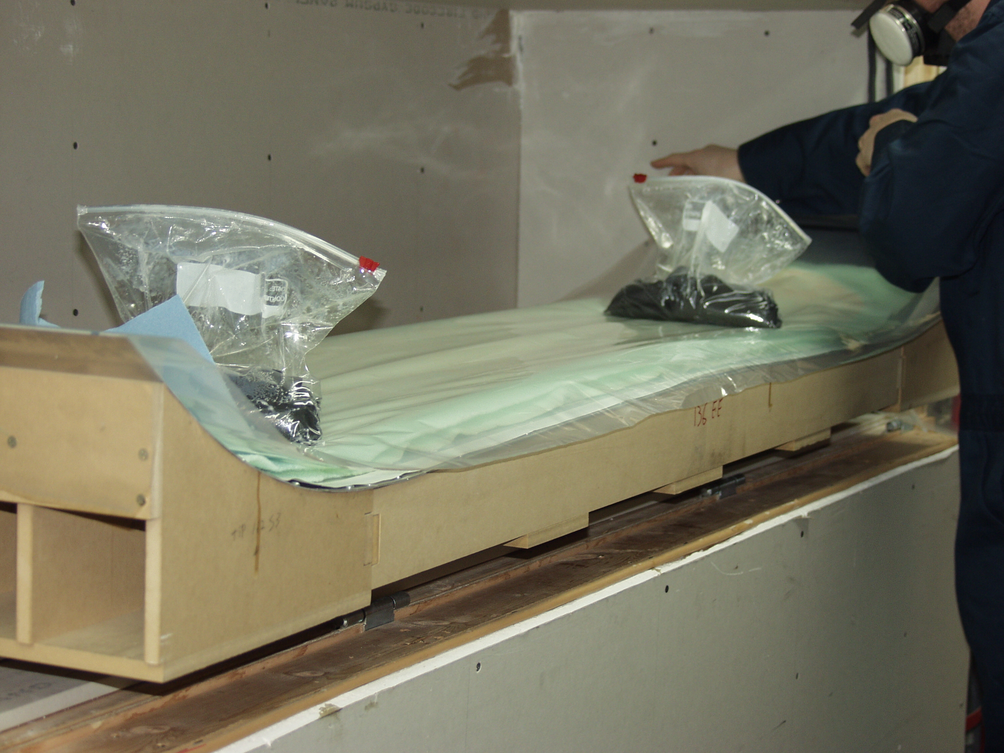
assets/images/PC296848.JPG
