mikemag/MonkeyWiki/assets/images/PC296851.JPG

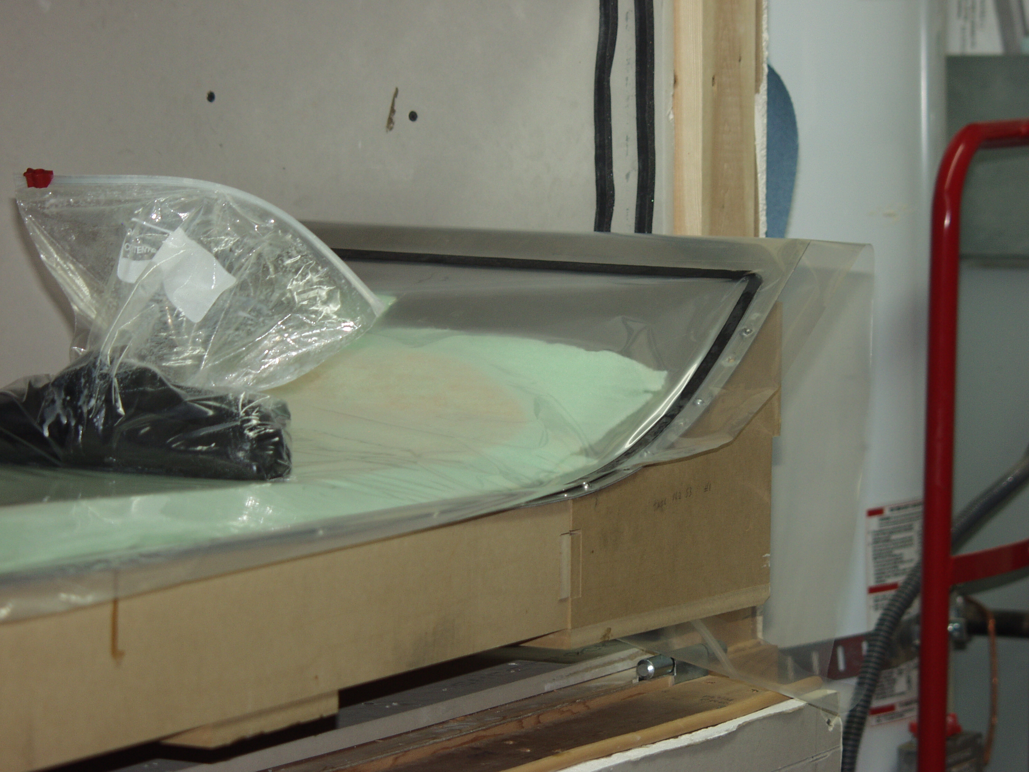
assets/images/PC296851.JPG
