mikemag/MonkeyWiki/assets/images/PC296852.JPG

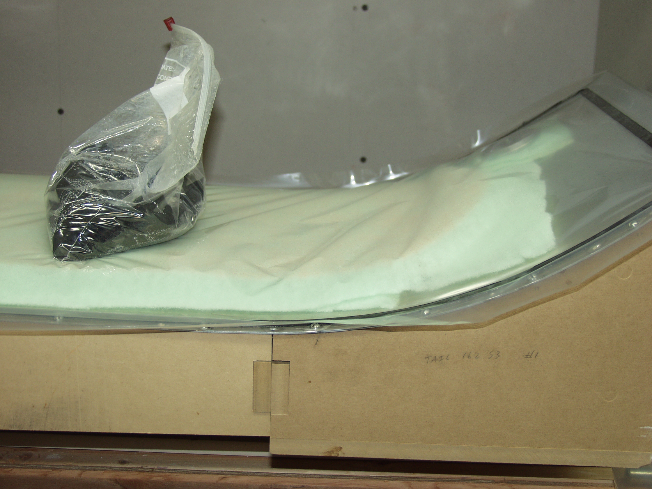
assets/images/PC296852.JPG
