mikemag/MonkeyWiki/assets/images/PC296853.JPG

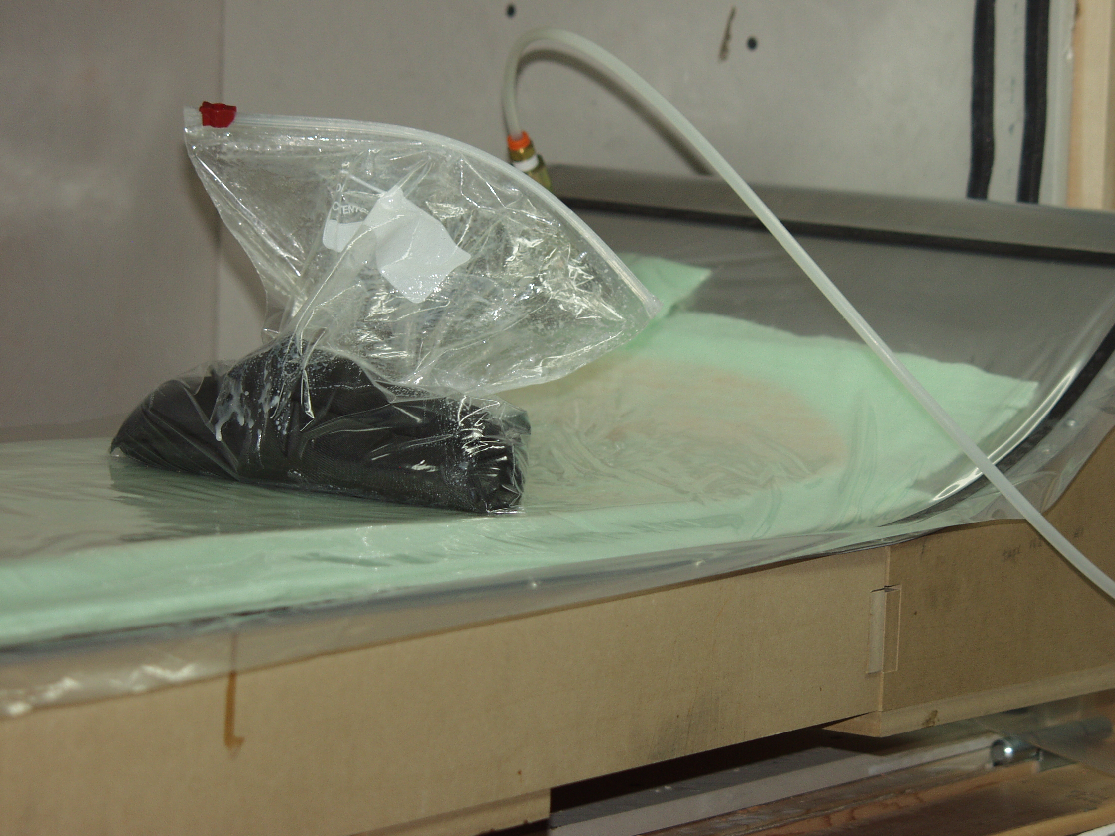
assets/images/PC296853.JPG
