mikemag/MonkeyWiki/assets/images/PC296854.JPG

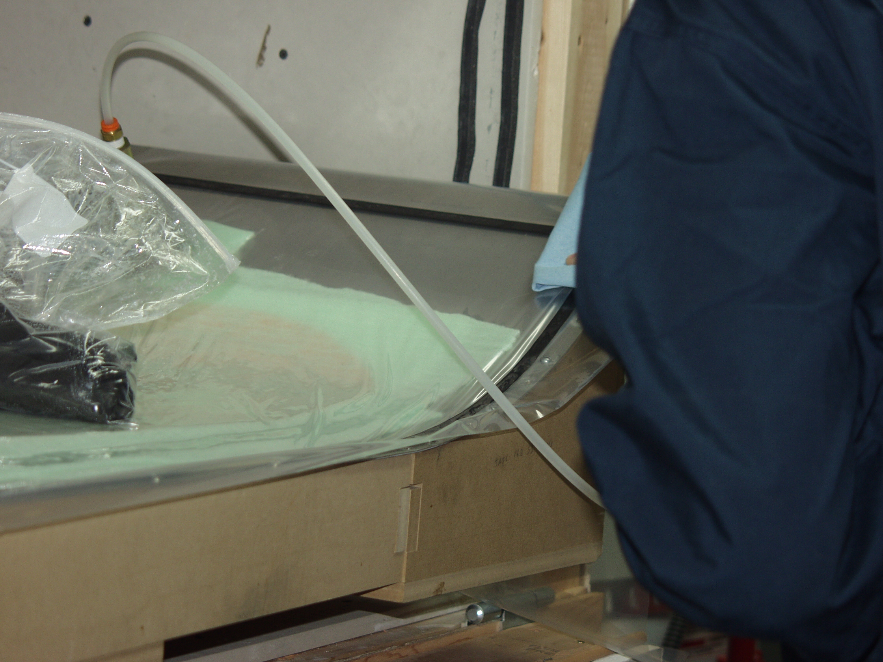
assets/images/PC296854.JPG
