mikemag/MonkeyWiki/assets/images/PC296855.JPG

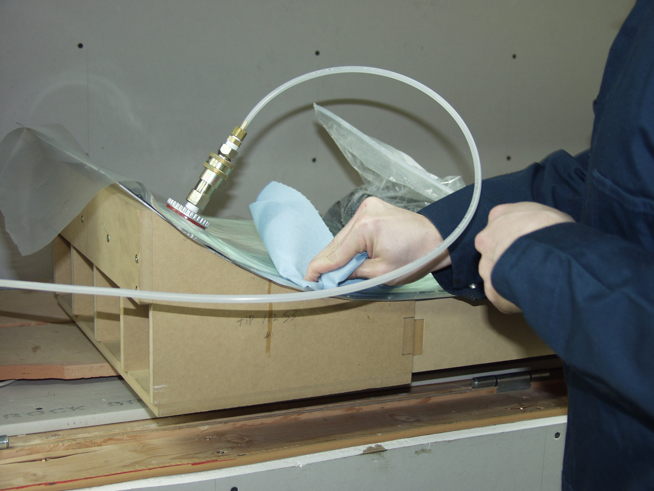
assets/images/PC296855.JPG
