mikemag/MonkeyWiki/assets/images/PC296856.JPG

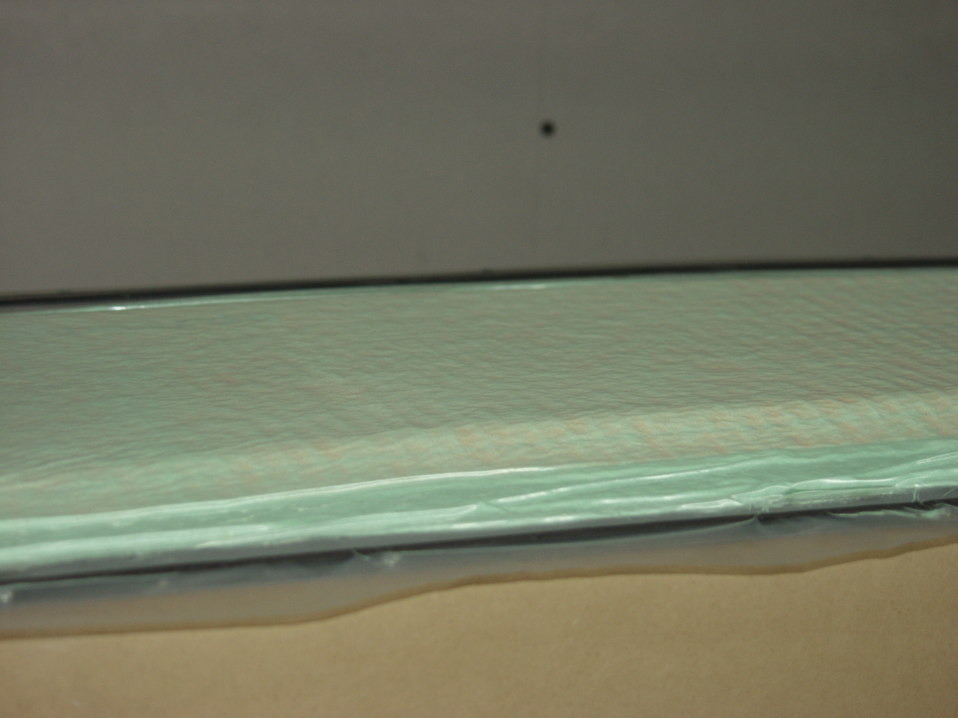
assets/images/PC296856.JPG
