mikemag/MonkeyWiki/assets/images/PC296857.JPG

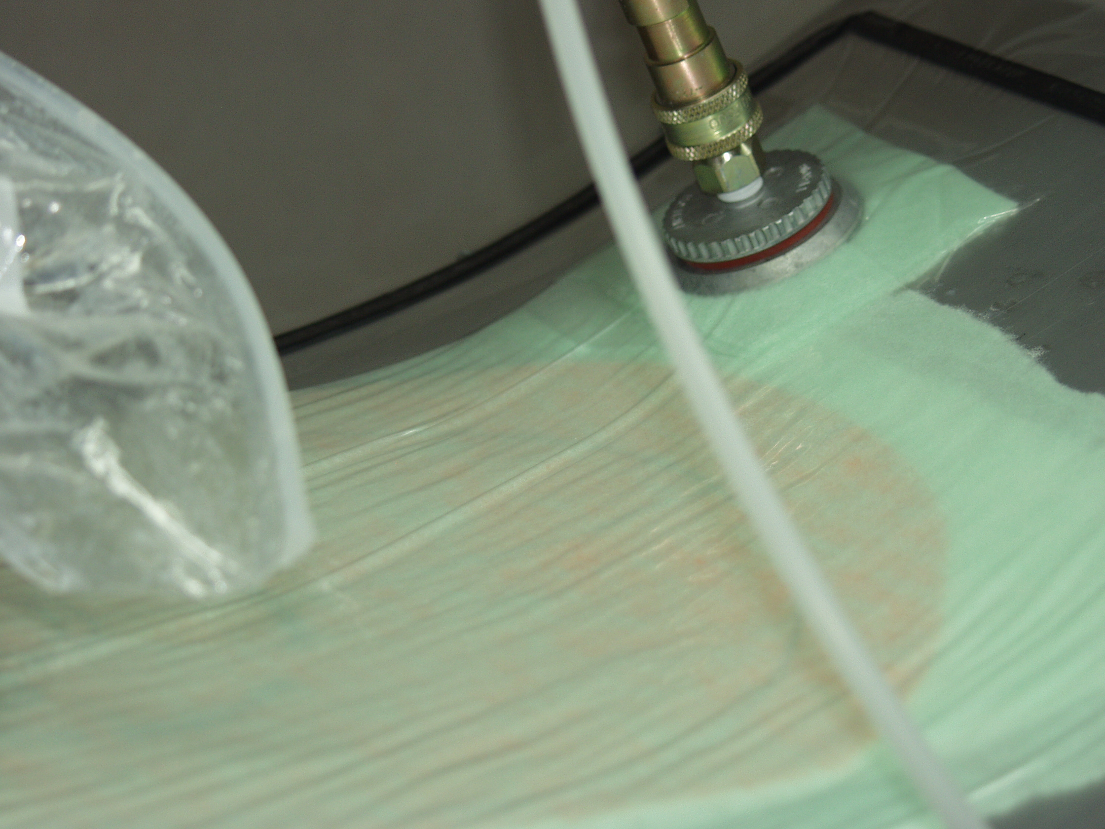
assets/images/PC296857.JPG
