mikemag/MonkeyWiki/assets/images/PC296858.JPG

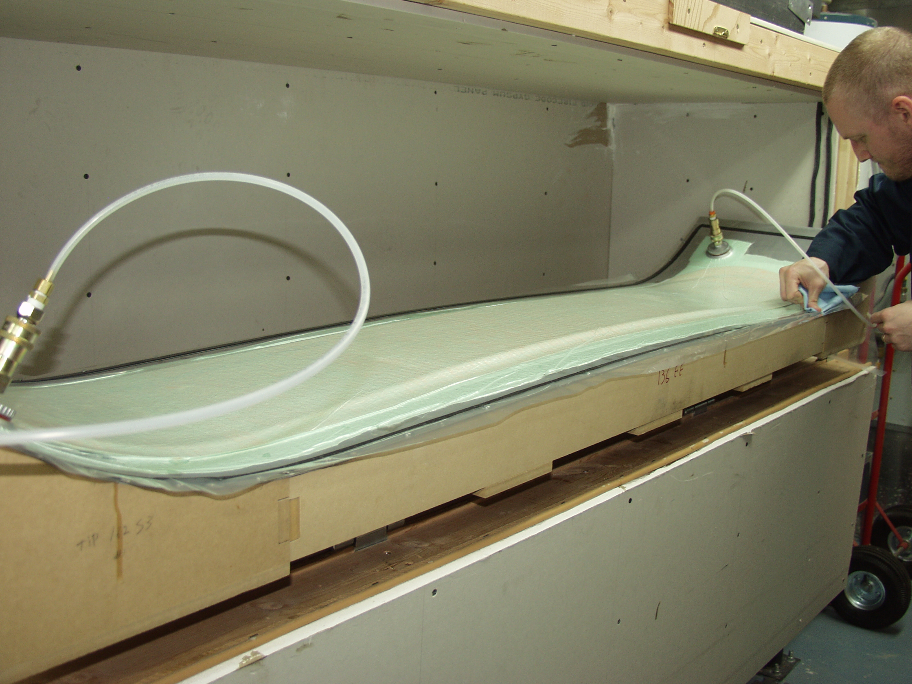
assets/images/PC296858.JPG
