mikemag/MonkeyWiki/assets/images/PC296859.JPG

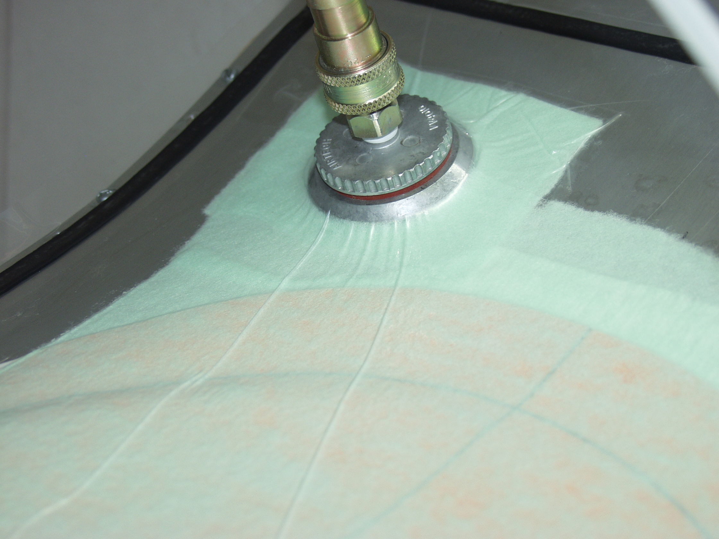
assets/images/PC296859.JPG
