mikemag/MonkeyWiki/assets/images/PipeClamp1.JPG

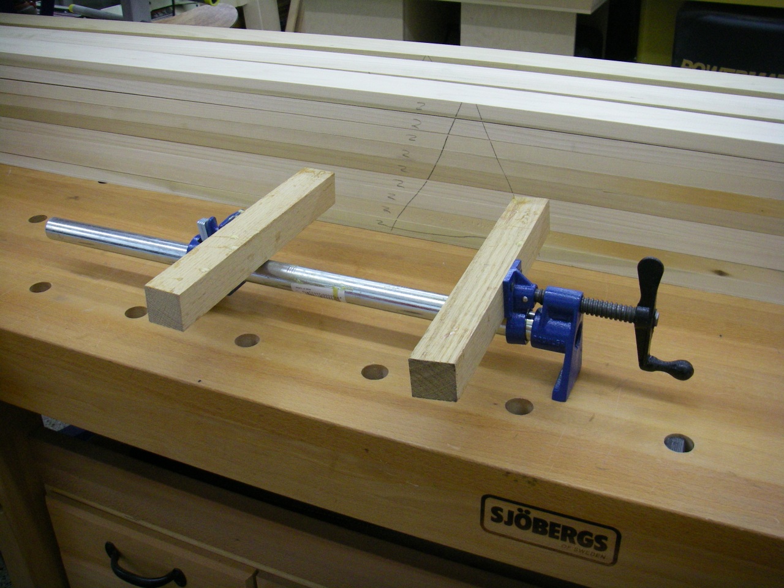
assets/images/PipeClamp1.JPG
