mikemag/MonkeyWiki/assets/images/PipeClamp2.JPG

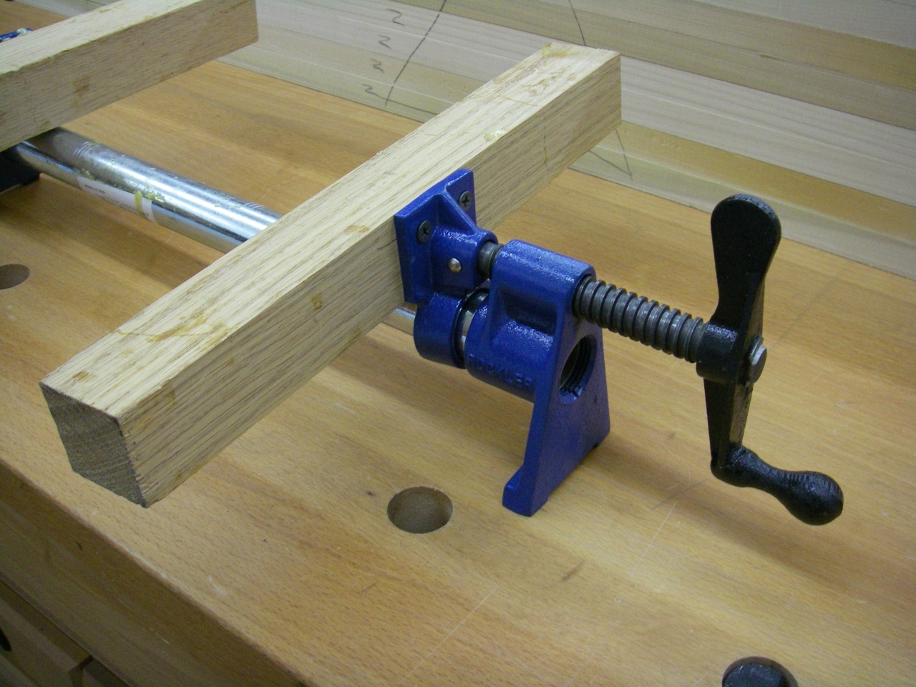
assets/images/PipeClamp2.JPG
