mikemag/MonkeyWiki/assets/images/PipeClamp3.JPG

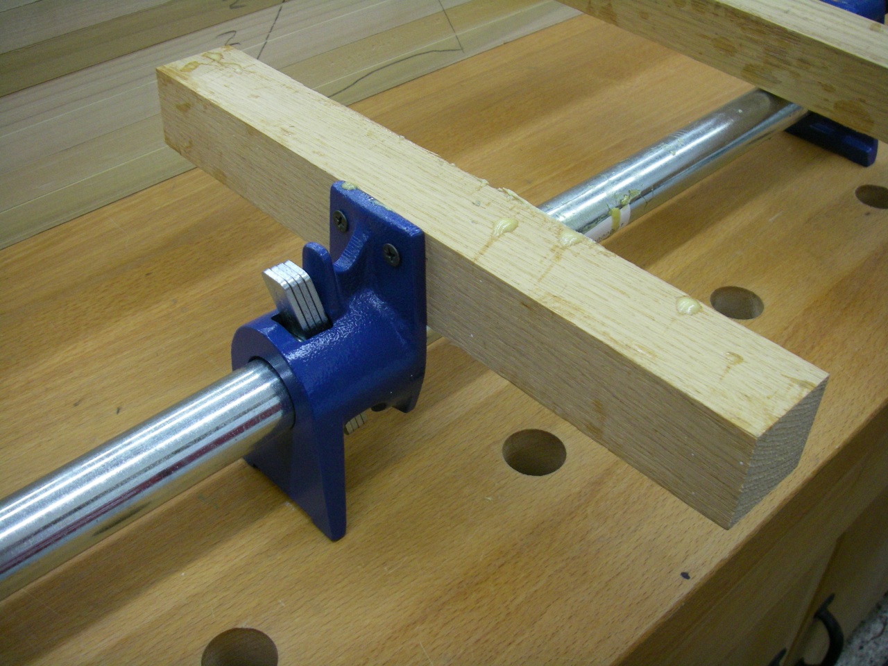
assets/images/PipeClamp3.JPG
