mikemag/MonkeyWiki/assets/images/Press_AirControl.JPG

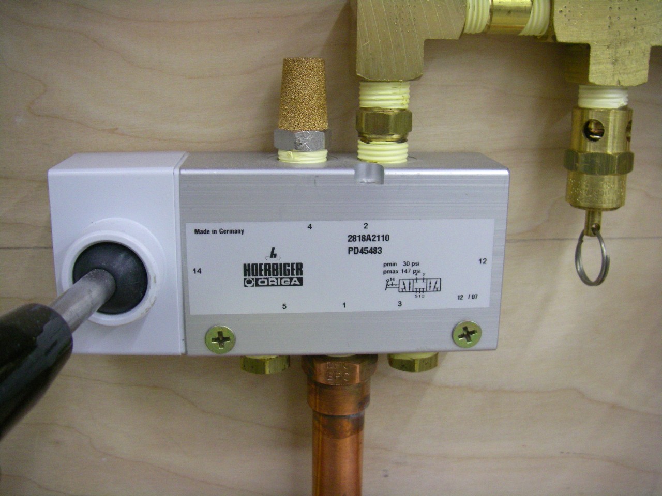
assets/images/Press_AirControl.JPG
