mikemag/MonkeyWiki/assets/images/Press_BladderConnectionDetail.JPG

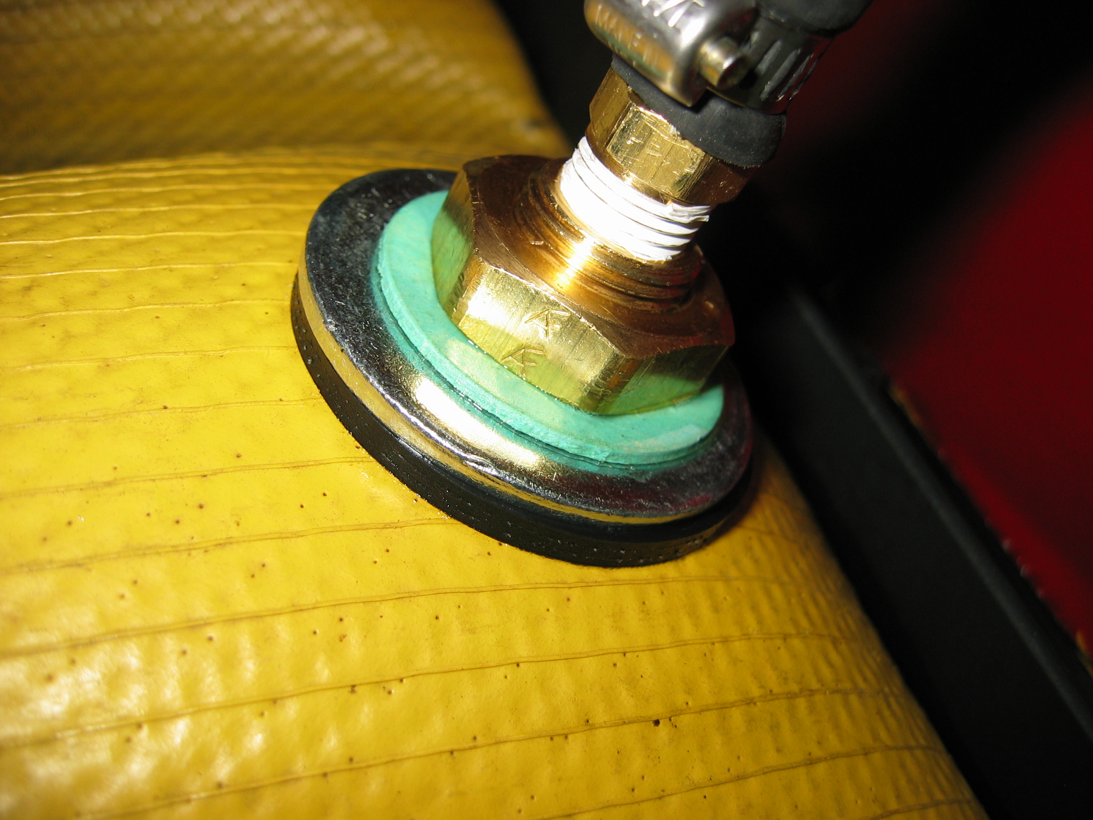
assets/images/Press_BladderConnectionDetail.JPG
