mikemag/MonkeyWiki/assets/images/Press_BladderConnections.JPG

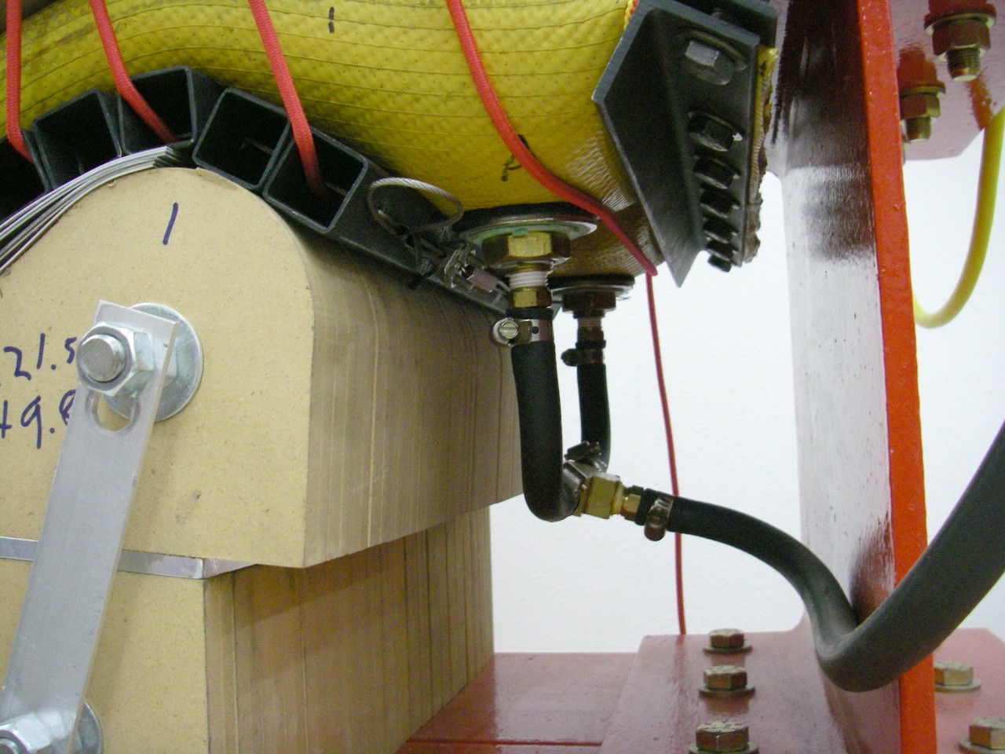
assets/images/Press_BladderConnections.JPG
