mikemag/MonkeyWiki/assets/images/Press_BladderInputConnector.JPG

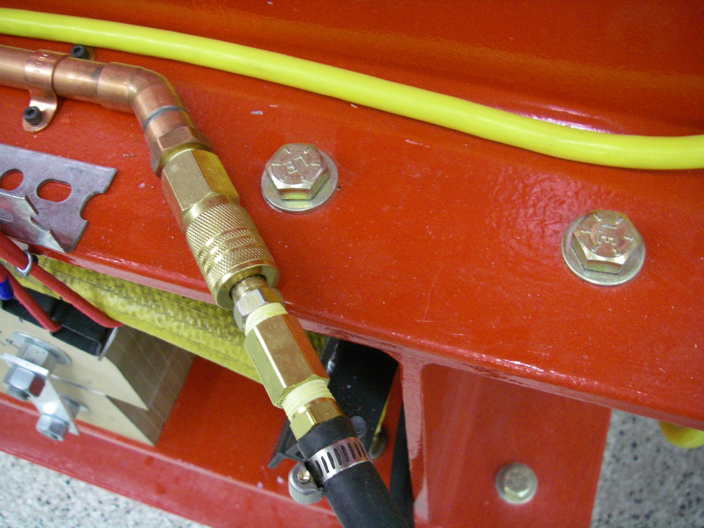
assets/images/Press_BladderInputConnector.JPG
