mikemag/MonkeyWiki/assets/images/Press_Blanket.JPG

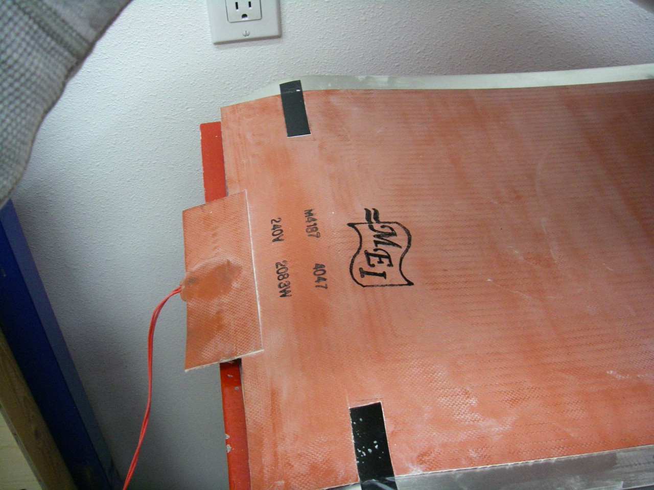
assets/images/Press_Blanket.JPG
