mikemag/MonkeyWiki/assets/images/Press_BlanketPlugs.JPG

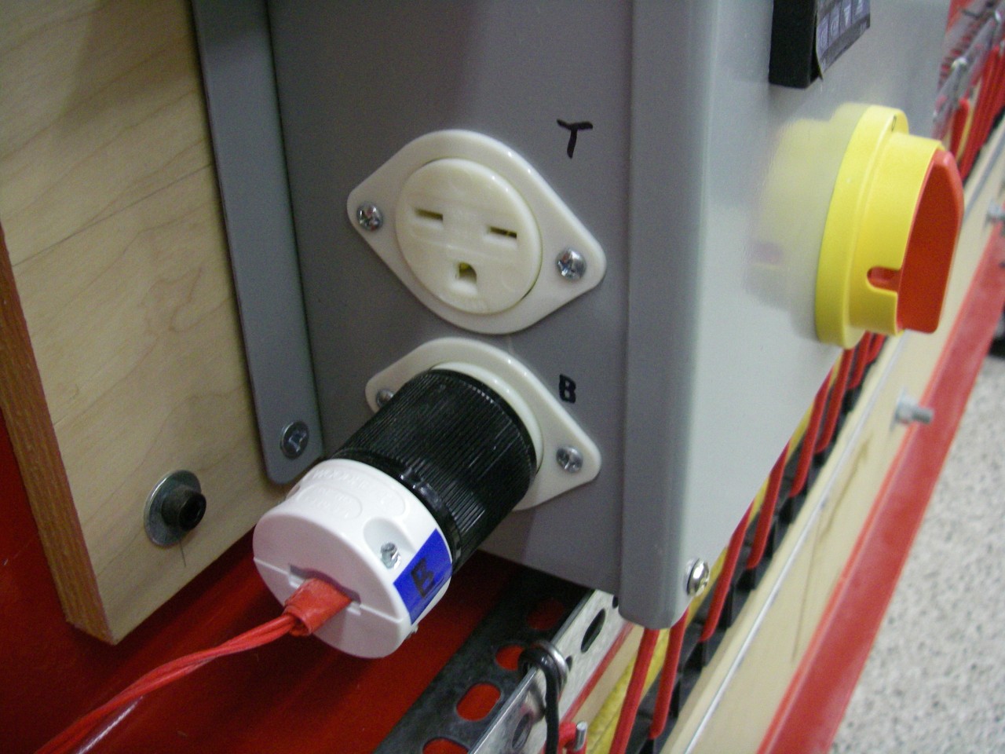
assets/images/Press_BlanketPlugs.JPG
