mikemag/MonkeyWiki/assets/images/Press_Bolts.JPG

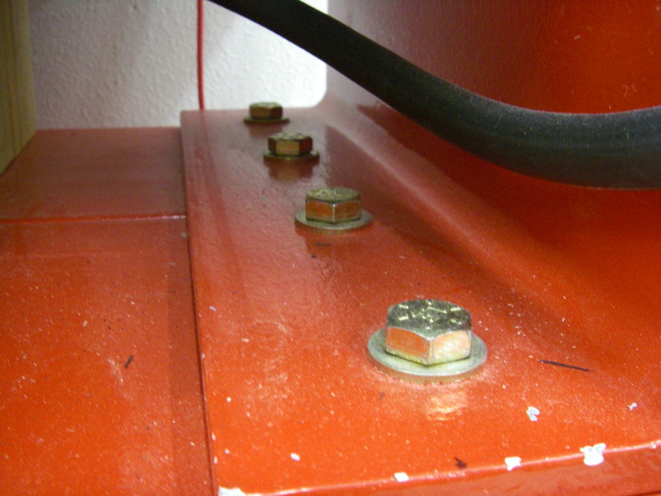
assets/images/Press_Bolts.JPG
