mikemag/MonkeyWiki/assets/images/Press_Controller04.JPG

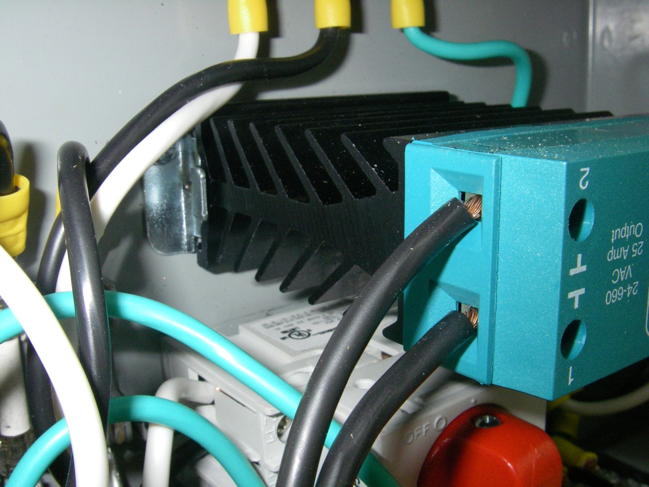
assets/images/Press_Controller04.JPG
