mikemag/MonkeyWiki/assets/images/Press_Controller46.JPG

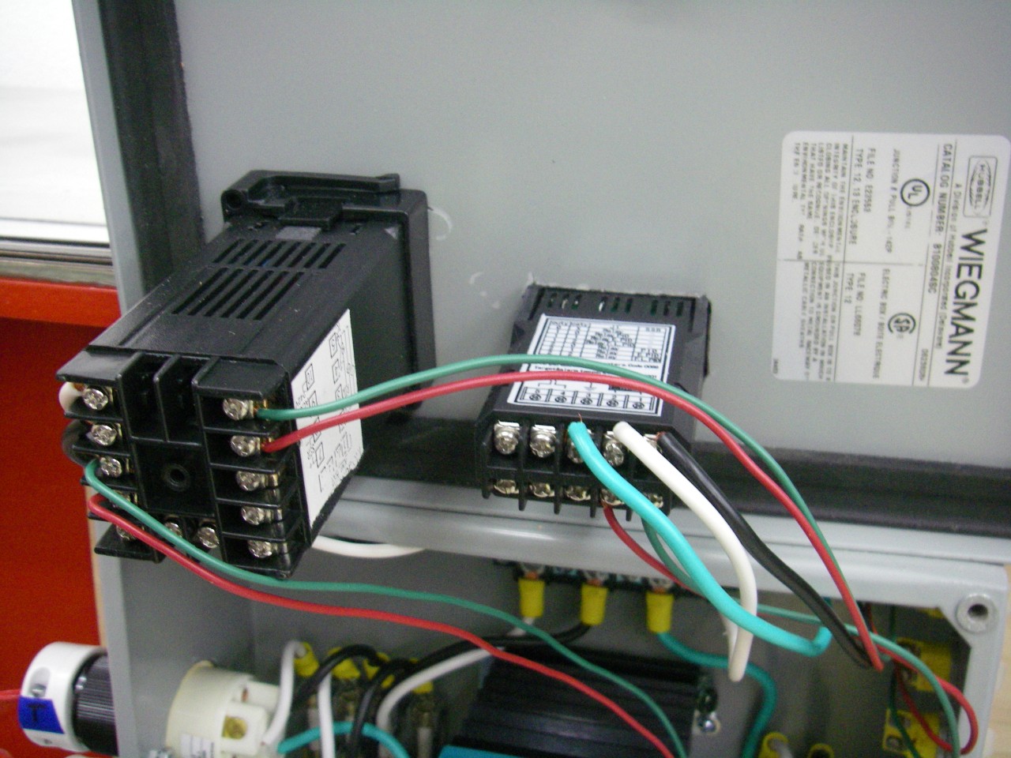
assets/images/Press_Controller46.JPG
