mikemag/MonkeyWiki/assets/images/Press_Controller60.JPG

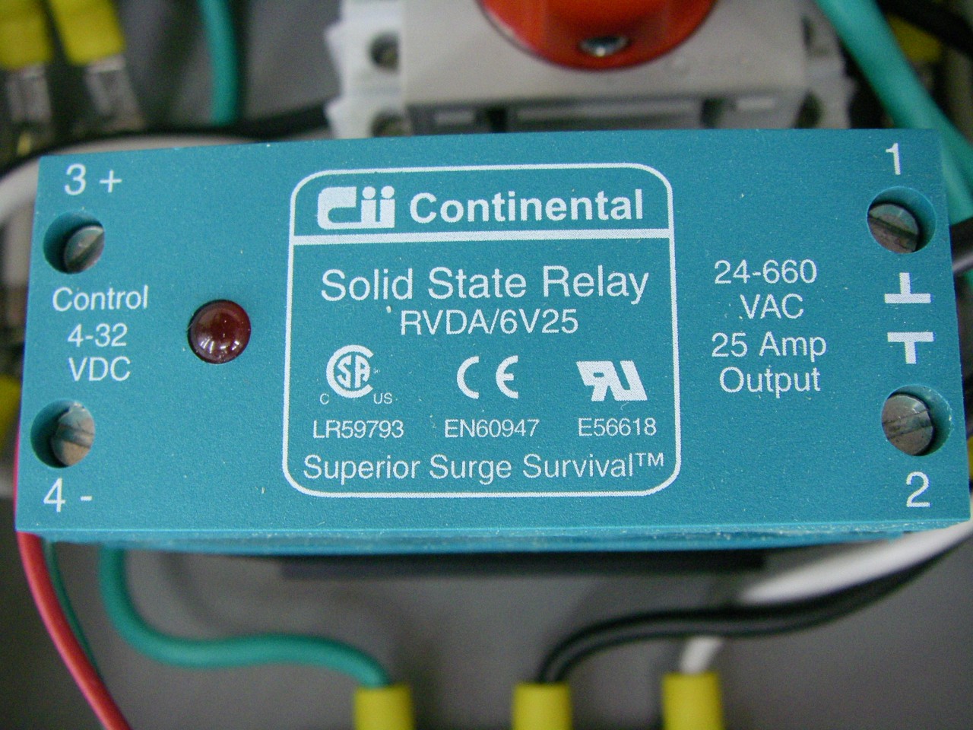
assets/images/Press_Controller60.JPG
