mikemag/MonkeyWiki/assets/images/Press_Controller62.JPG

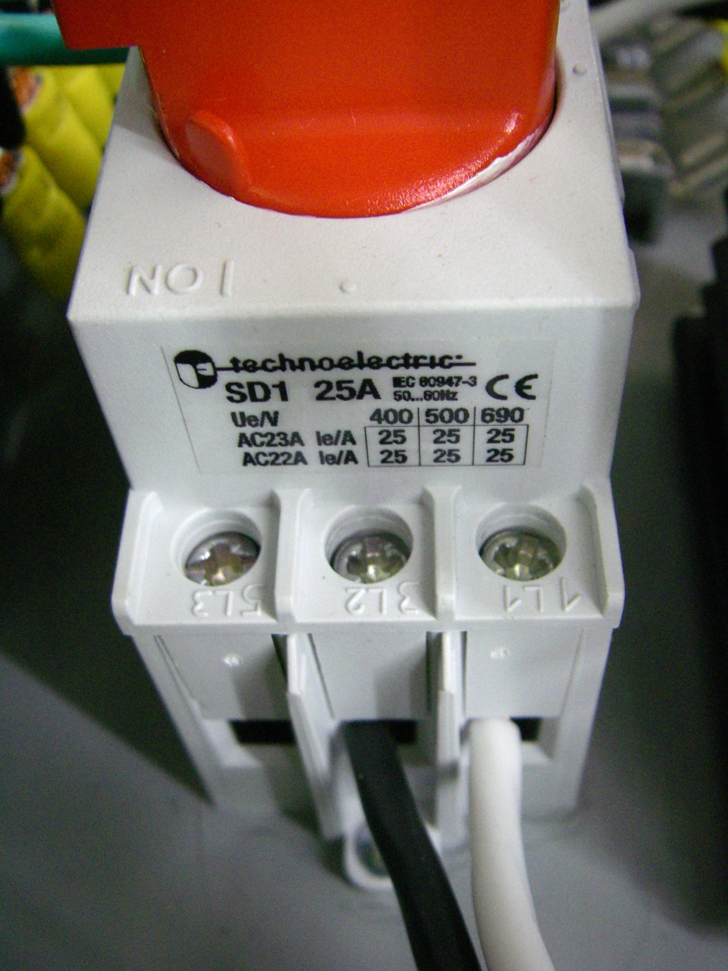
assets/images/Press_Controller62.JPG
