mikemag/MonkeyWiki/assets/images/Press_Controller65.JPG

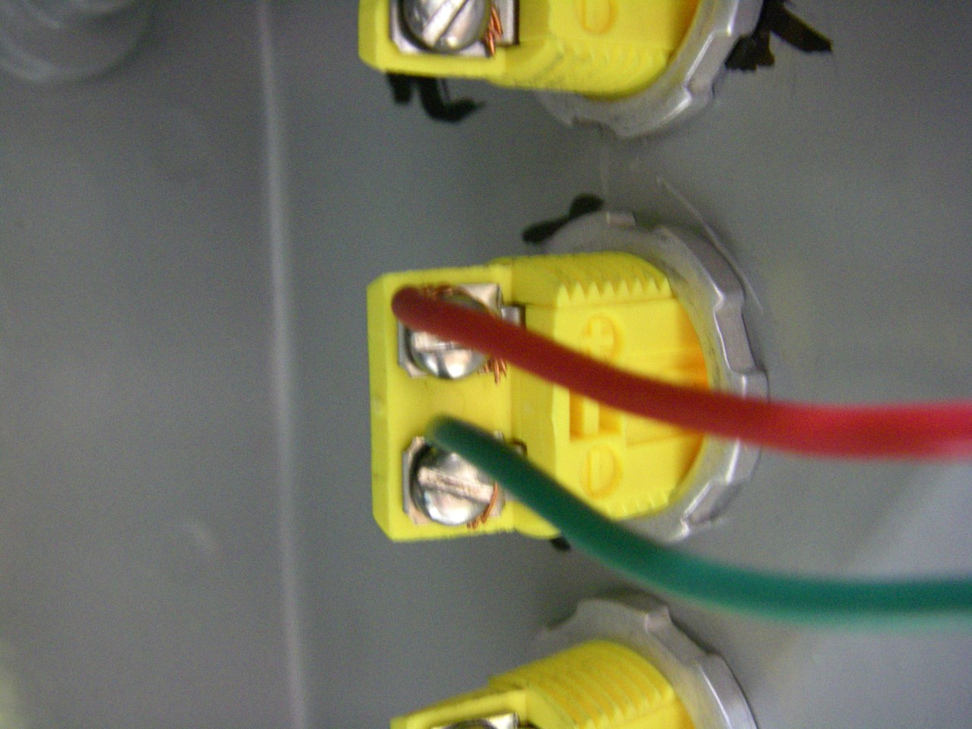
assets/images/Press_Controller65.JPG
