mikemag/MonkeyWiki/assets/images/Press_Controller68.JPG

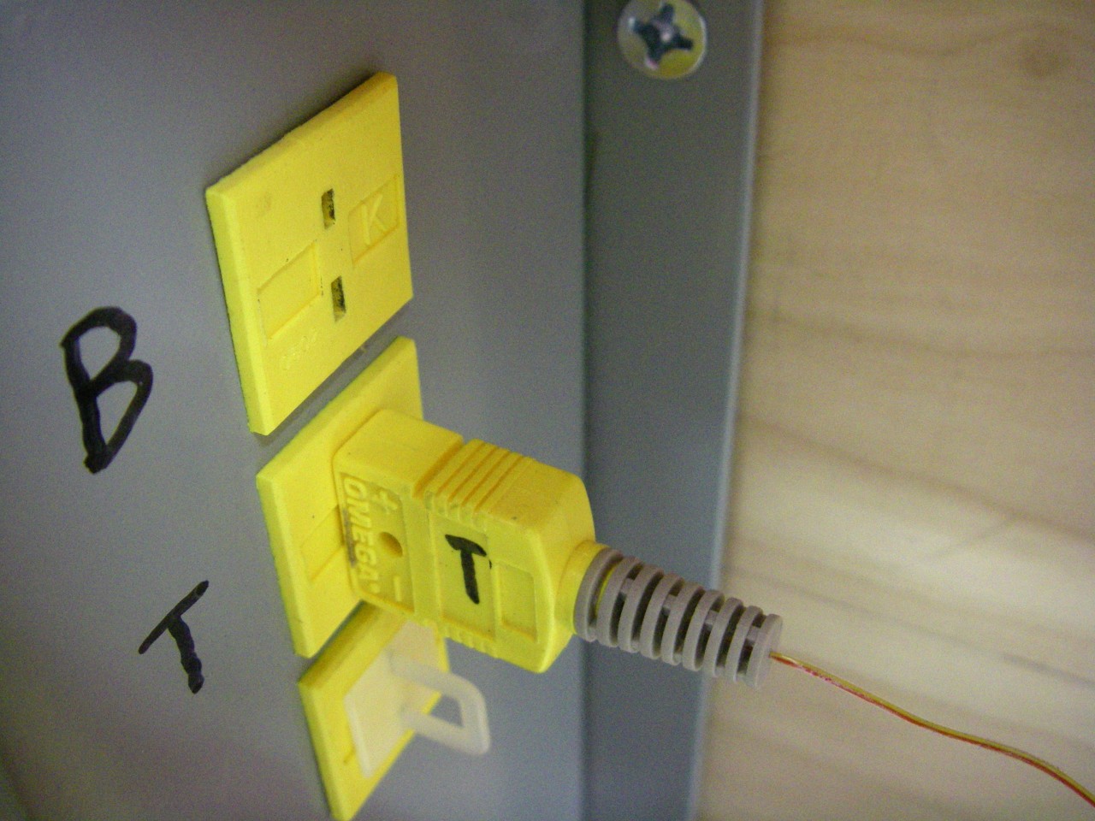
assets/images/Press_Controller68.JPG
