mikemag/MonkeyWiki/assets/images/Press_Controller91.JPG

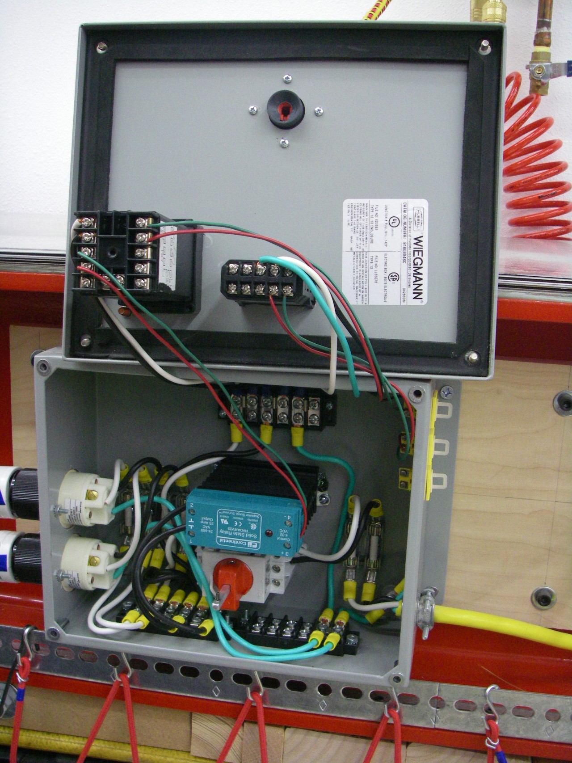
assets/images/Press_Controller91.JPG
