mikemag/MonkeyWiki/assets/images/Press_Controller96.JPG

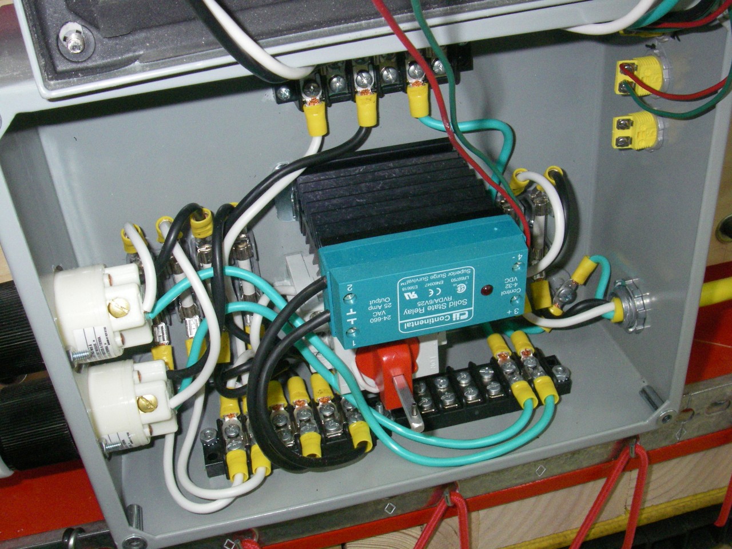
assets/images/Press_Controller96.JPG
