mikemag/MonkeyWiki/assets/images/Press_Controller98.JPG

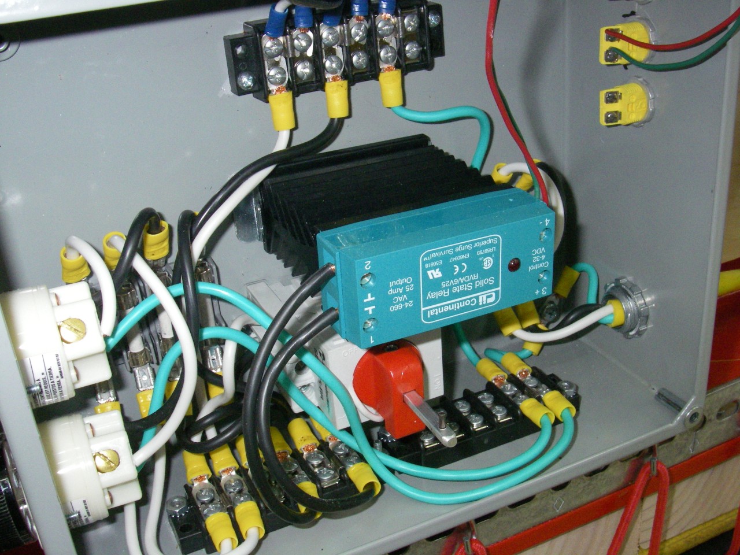
assets/images/Press_Controller98.JPG
