mikemag/MonkeyWiki/assets/images/Press_Controller99.JPG

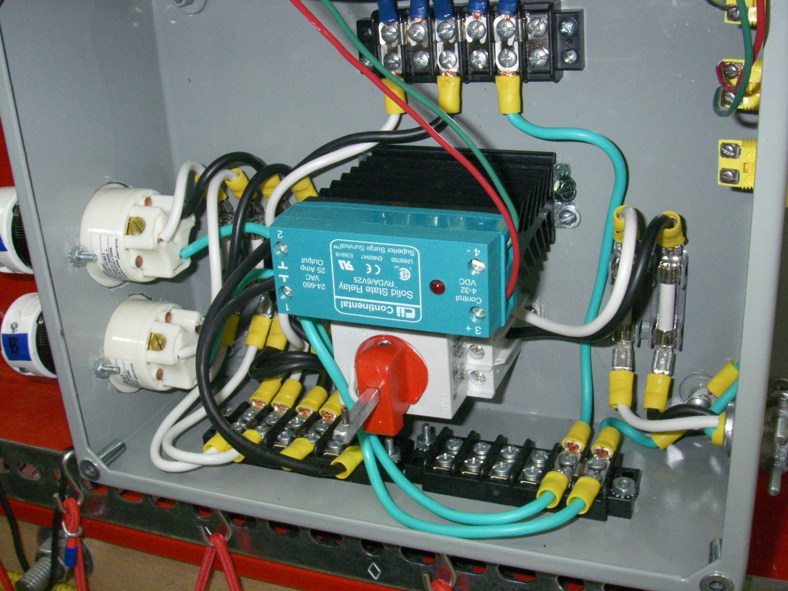
assets/images/Press_Controller99.JPG
