mikemag/MonkeyWiki/assets/images/Press_Full.JPG

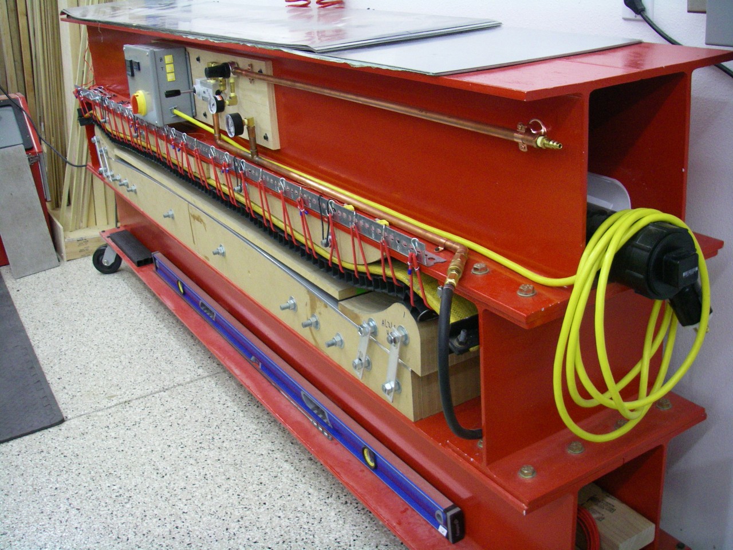
assets/images/Press_Full.JPG
