mikemag/MonkeyWiki/assets/images/Press_HeatControllerOutside.JPG

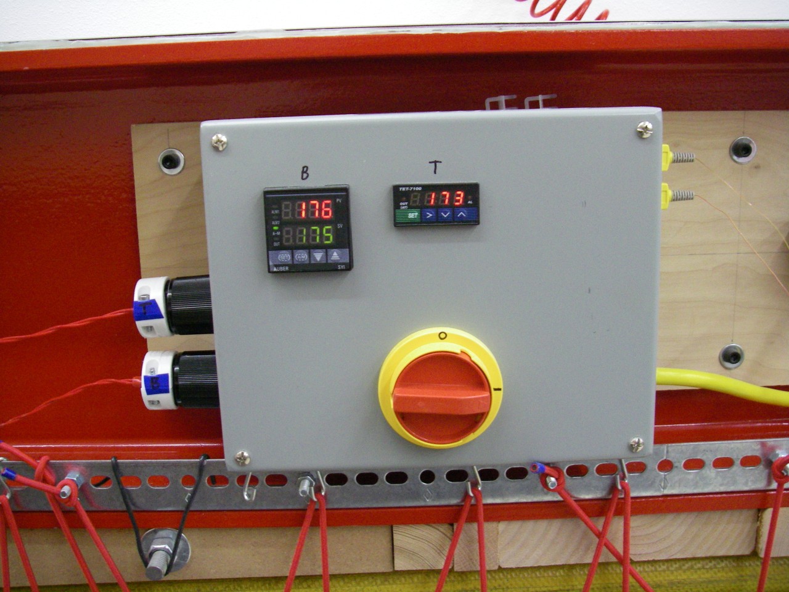
assets/images/Press_HeatControllerOutside.JPG
