mikemag/MonkeyWiki/assets/images/Press_Thermo70.JPG

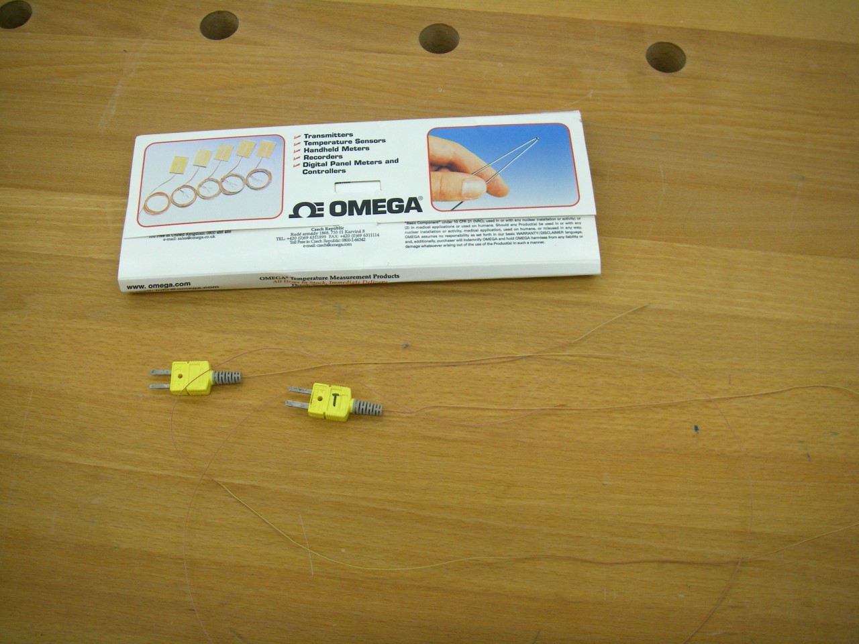
assets/images/Press_Thermo70.JPG
