mikemag/MonkeyWiki/assets/images/Press_Thermo74.JPG

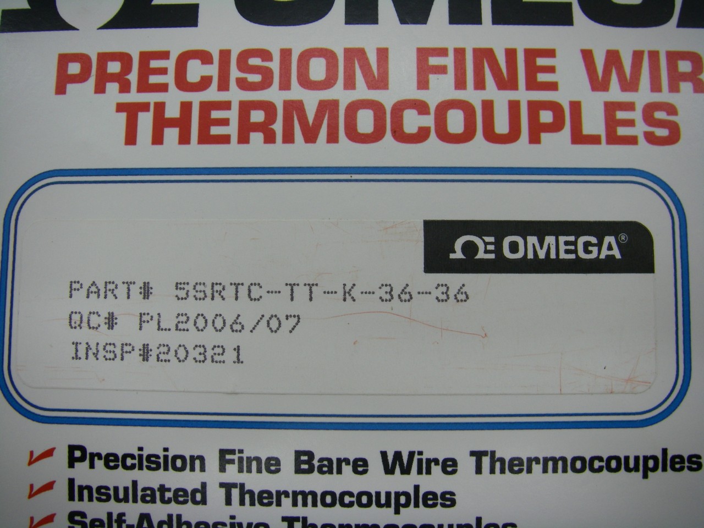
assets/images/Press_Thermo74.JPG
