mikemag/MonkeyWiki/assets/images/Press_Thermo76.JPG

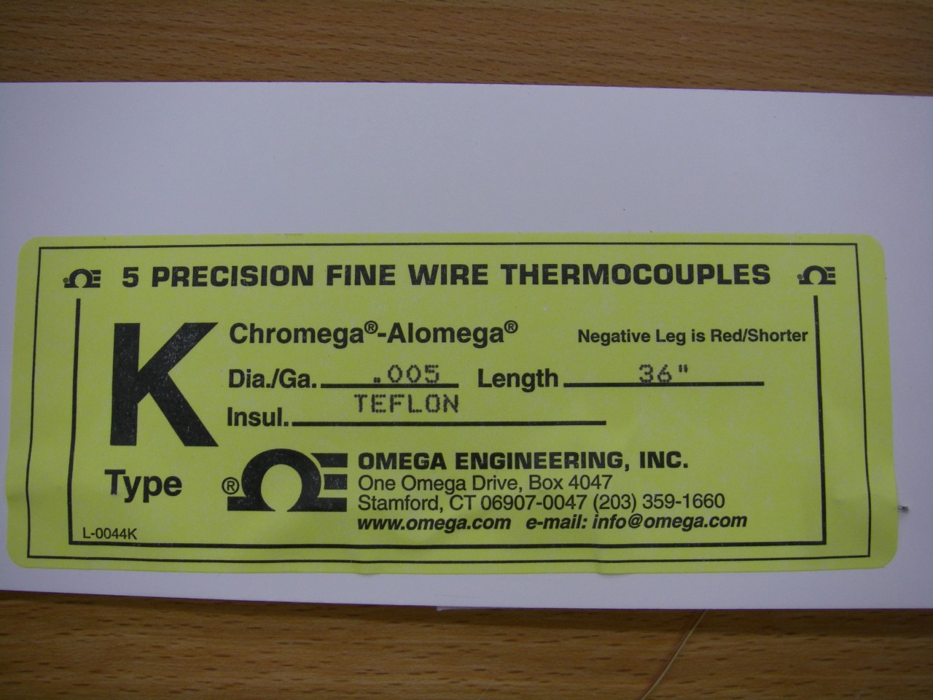
assets/images/Press_Thermo76.JPG
