mikemag/MonkeyWiki/assets/images/Press_Thermo84.JPG

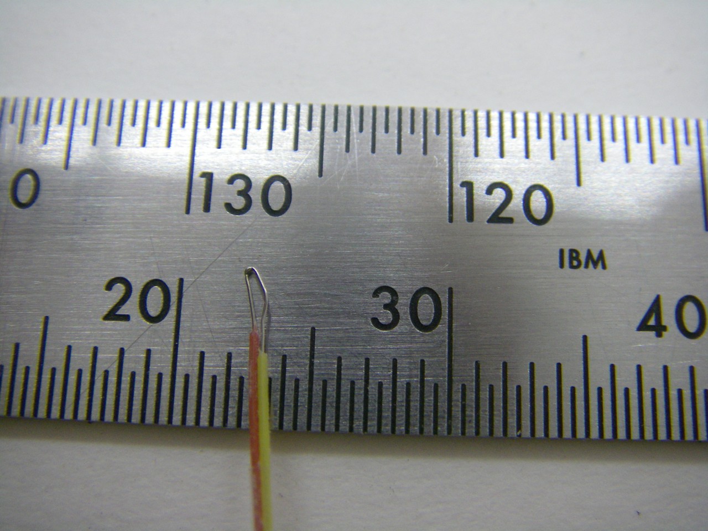
assets/images/Press_Thermo84.JPG
