mikemag/MonkeyWiki/assets/images/Press_TrackSuspension.JPG

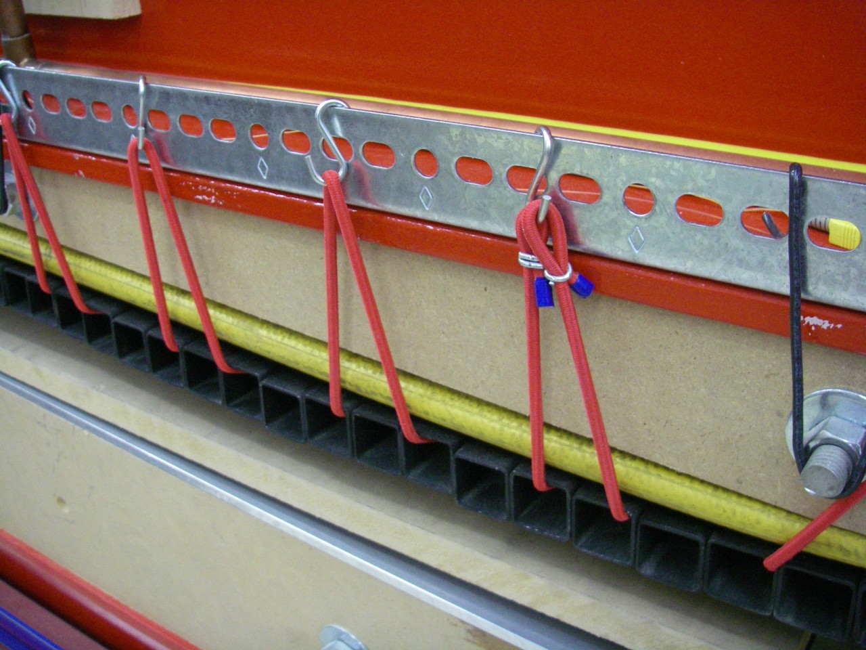
assets/images/Press_TrackSuspension.JPG
