mikemag/MonkeyWiki/assets/images/Press_UpperAirConnector.JPG

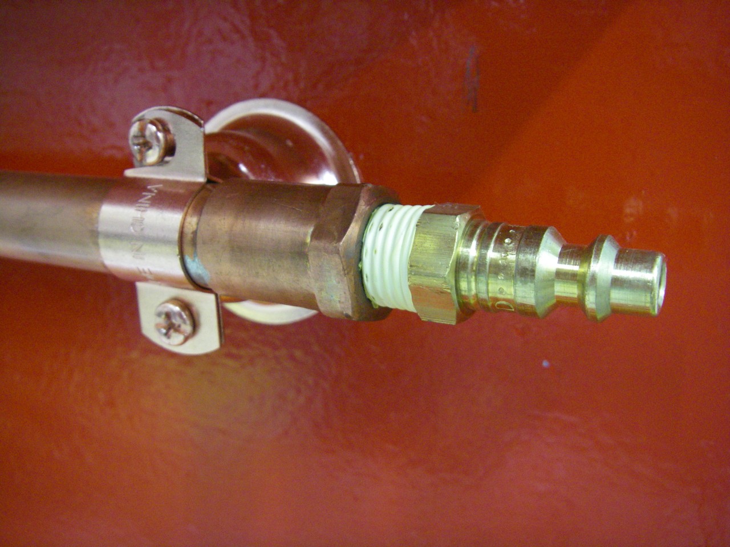
assets/images/Press_UpperAirConnector.JPG
