mikemag/MonkeyWiki/assets/images/PXL_20230831_224125744.jpg

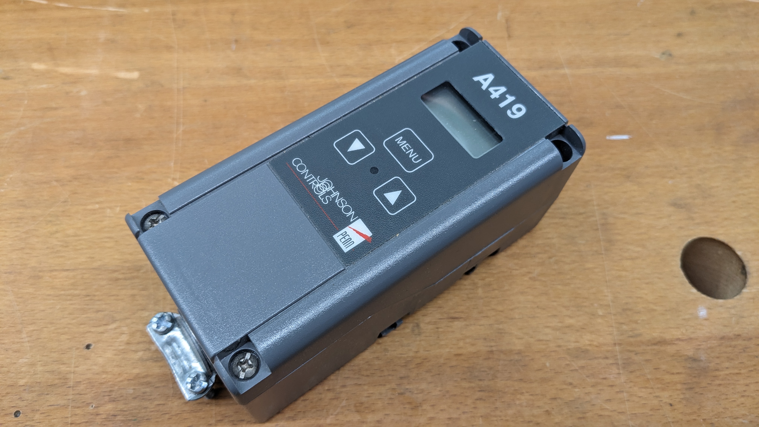
assets/images/PXL_20230831_224125744.jpg
