mikemag/MonkeyWiki/assets/images/PXL_20230831_224223823.jpg

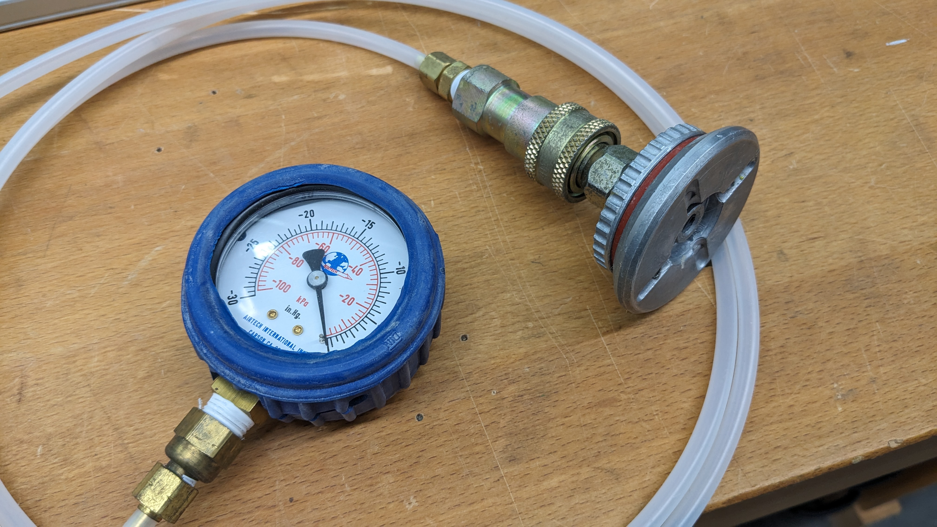
assets/images/PXL_20230831_224223823.jpg
