mikemag/MonkeyWiki/assets/images/PXL_20230831_224349720.jpg

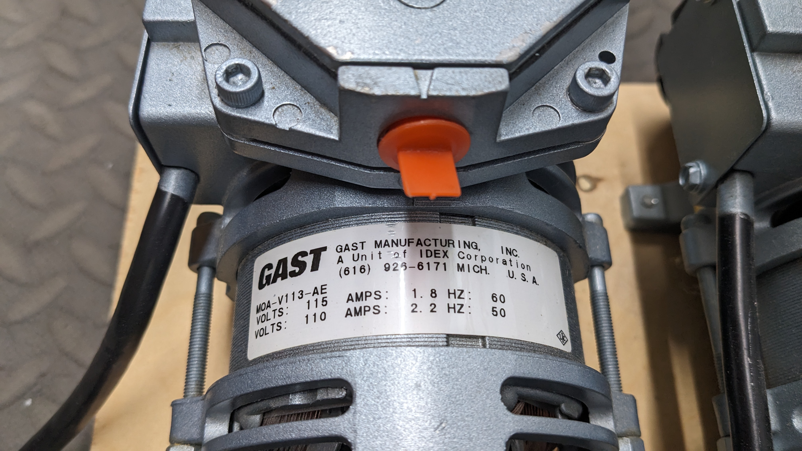
assets/images/PXL_20230831_224349720.jpg
