mikemag/MonkeyWiki/assets/images/PXL_20230831_224411776.jpg

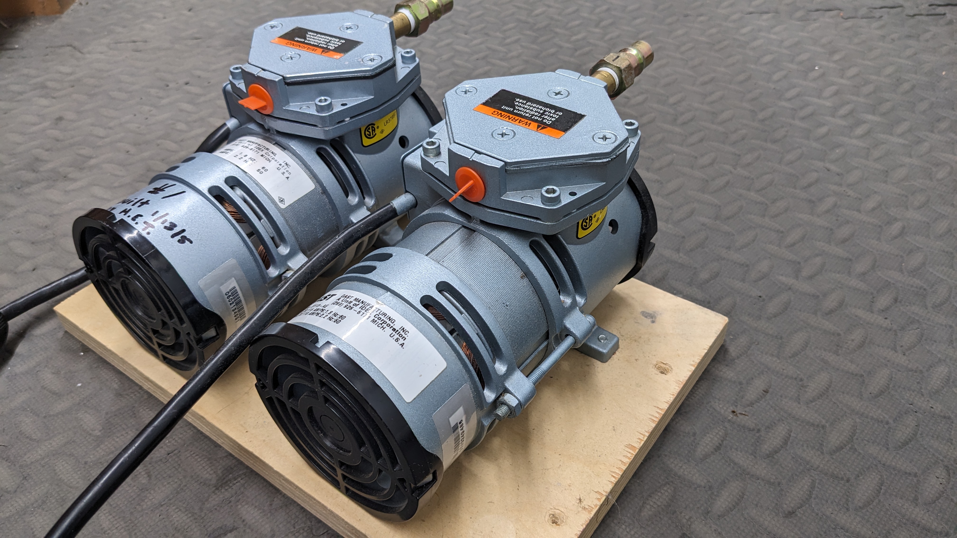
assets/images/PXL_20230831_224411776.jpg
