mikemag/MonkeyWiki/assets/images/RingRoller1.JPG

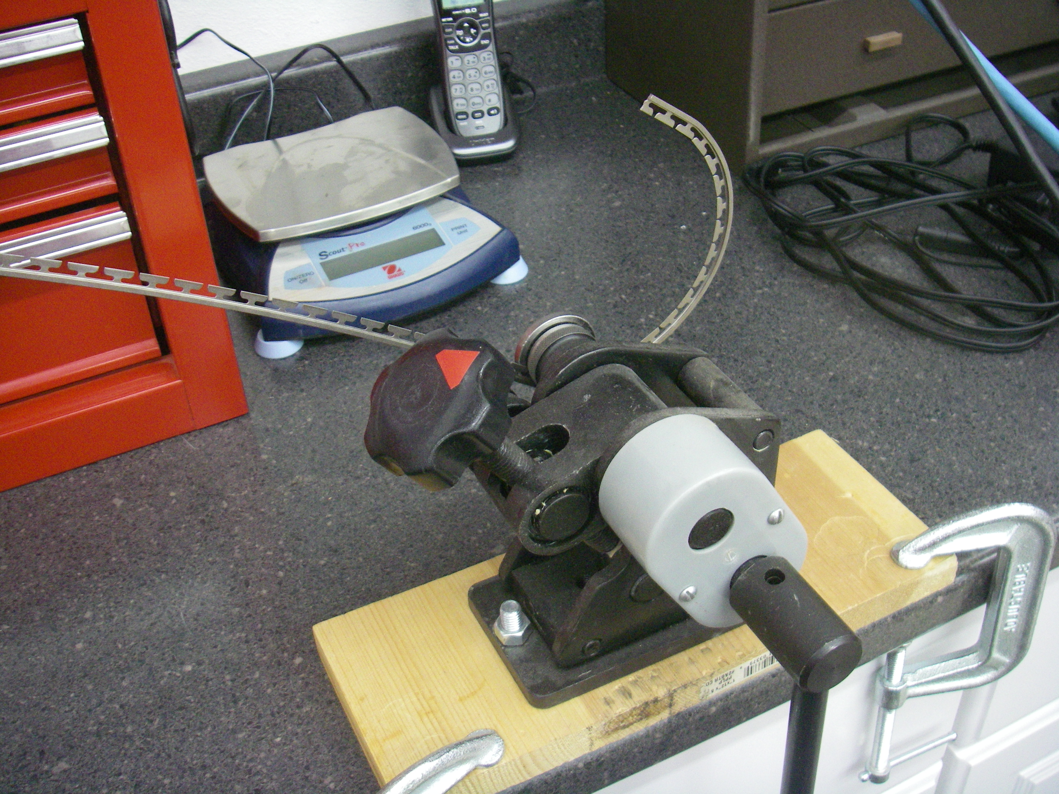
assets/images/RingRoller1.JPG
