mikemag/MonkeyWiki/assets/images/RingRoller3.JPG

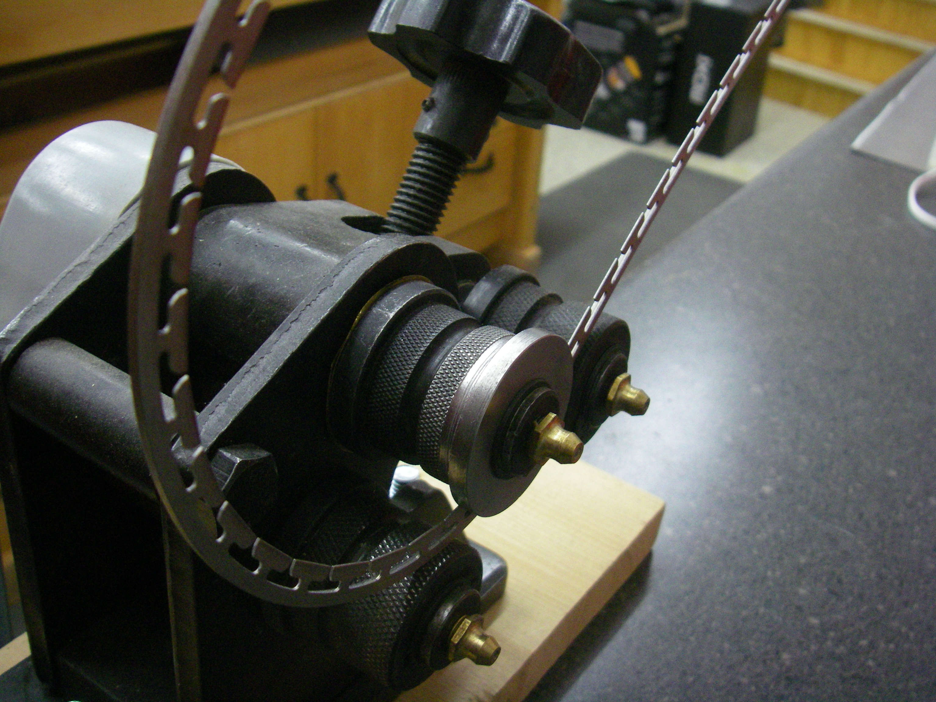
assets/images/RingRoller3.JPG
