mikemag/MonkeyWiki/assets/images/RingRoller4.JPG

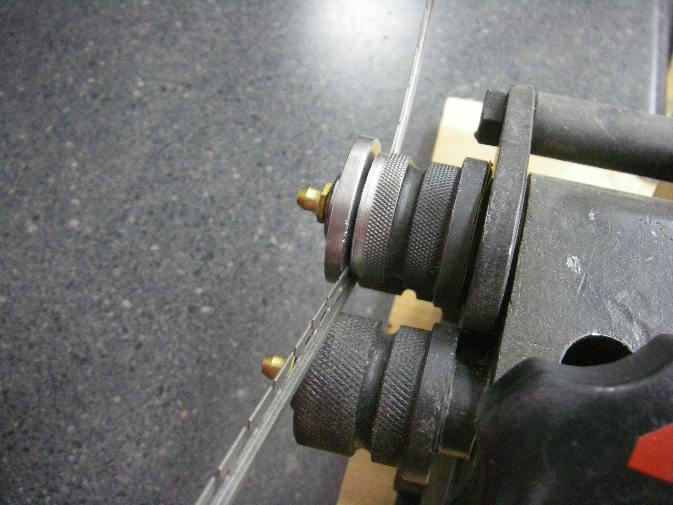
assets/images/RingRoller4.JPG
