mikemag/MonkeyWiki/assets/images/RingRoller5.JPG

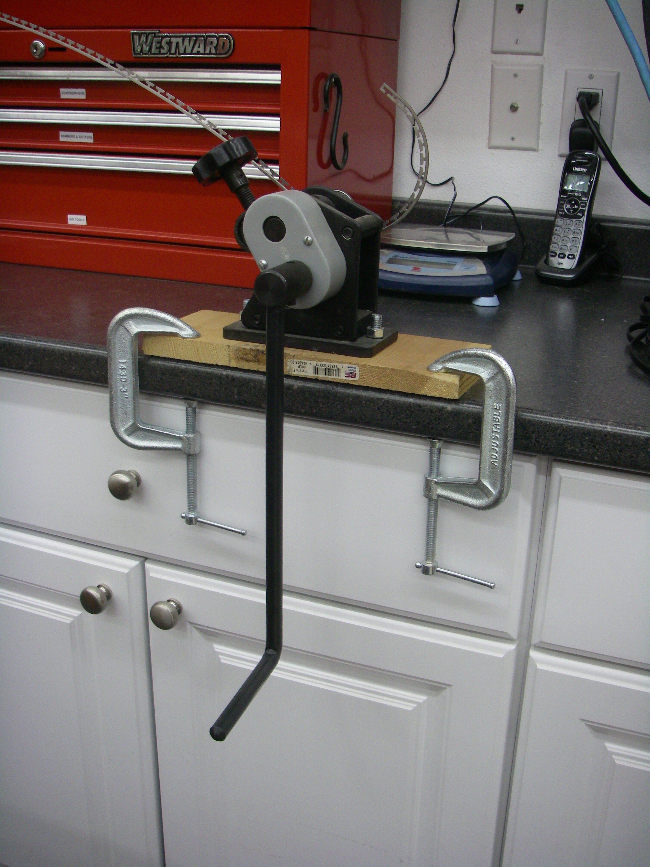
assets/images/RingRoller5.JPG
