mikemag/MonkeyWiki/assets/images/RouterBits1.JPG

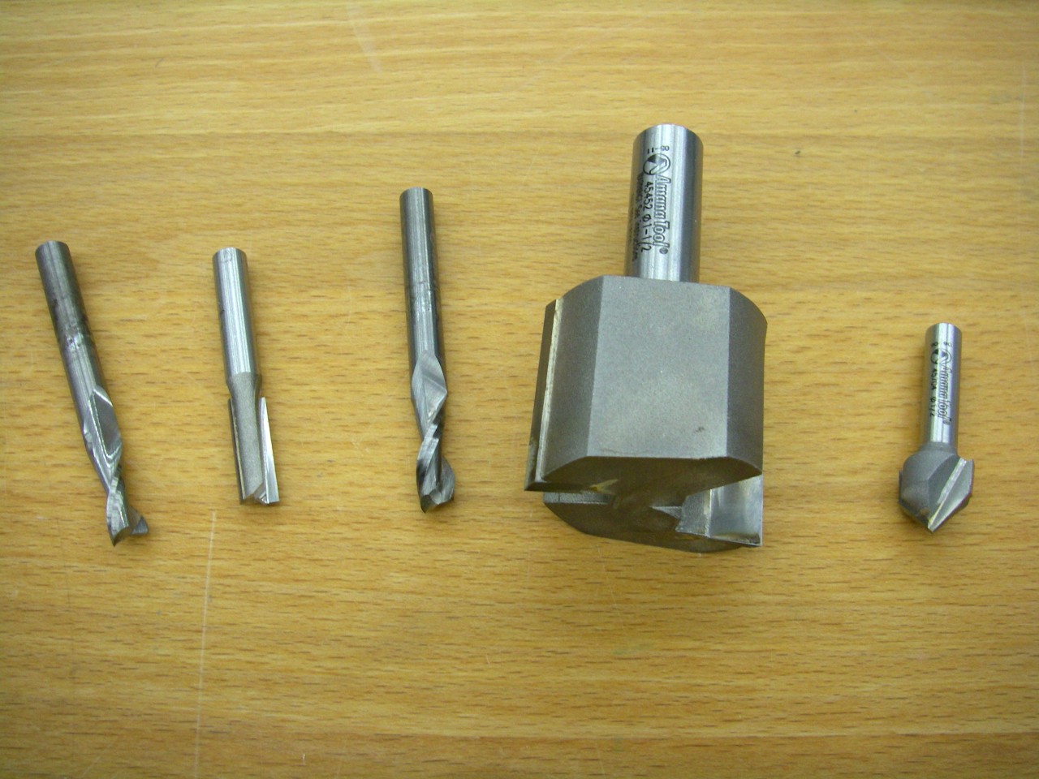
assets/images/RouterBits1.JPG
