mikemag/MonkeyWiki/assets/images/RouterBits2.JPG

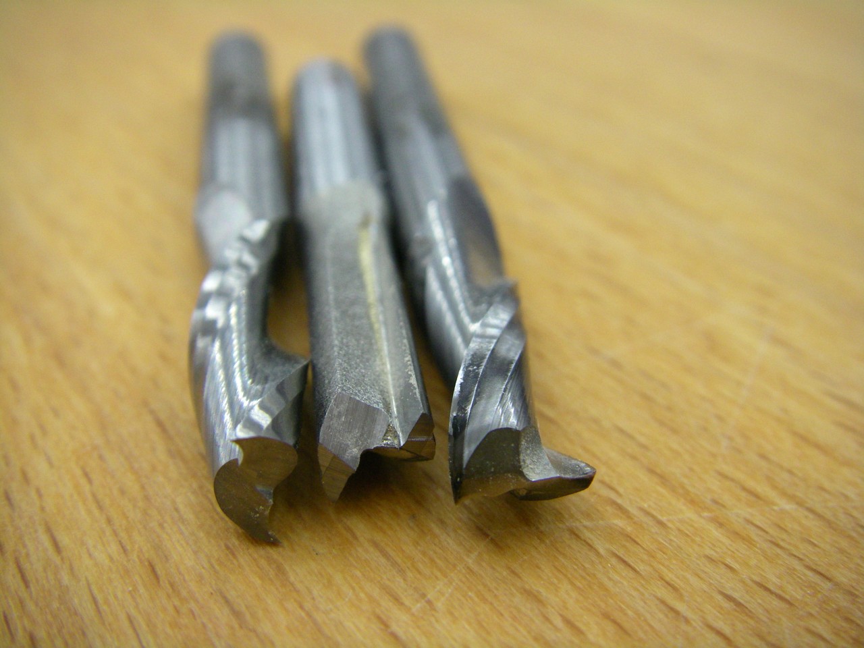
assets/images/RouterBits2.JPG
