mikemag/MonkeyWiki/assets/images/Stack_Clean_Blemish1.JPG

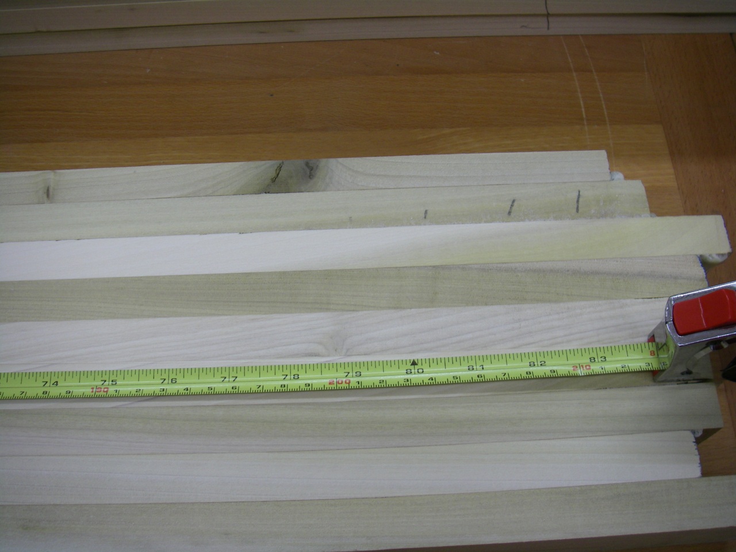
assets/images/Stack_Clean_Blemish1.JPG
