mikemag/MonkeyWiki/assets/images/Stack_Clean_Blemish2.JPG

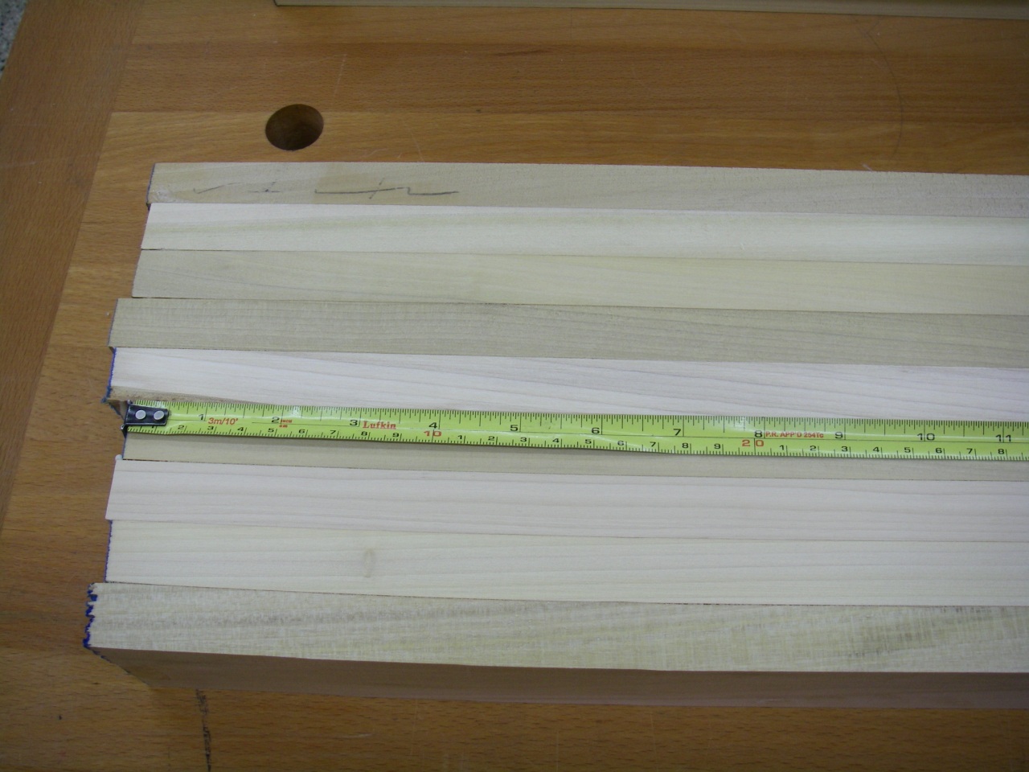
assets/images/Stack_Clean_Blemish2.JPG
