mikemag/MonkeyWiki/assets/images/Stack_Clean_Complete1.JPG

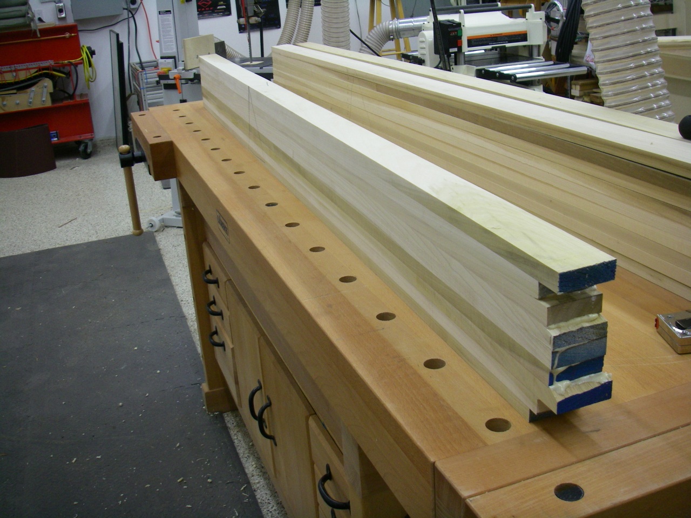
assets/images/Stack_Clean_Complete1.JPG
