mikemag/MonkeyWiki/assets/images/Stack_Clean_Complete2.JPG

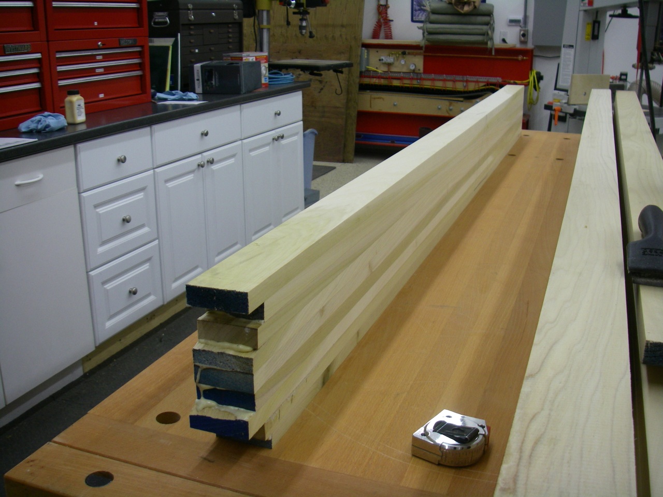
assets/images/Stack_Clean_Complete2.JPG
