mikemag/MonkeyWiki/assets/images/Stack_Clean_First_Side_Jointed2.JPG

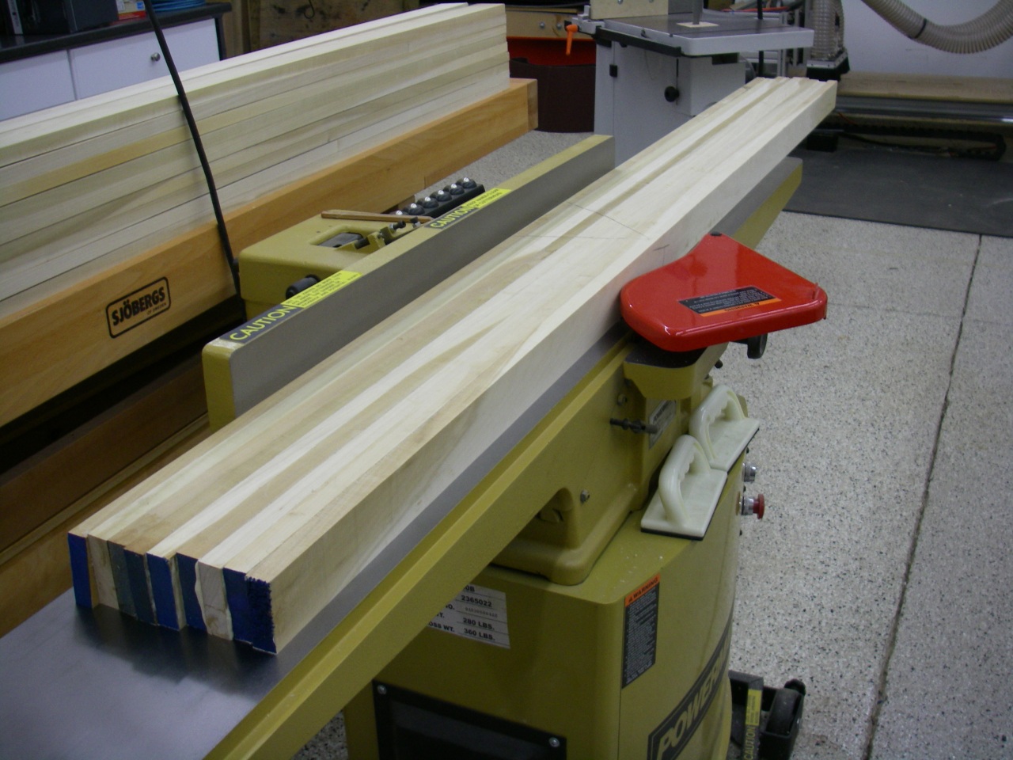
assets/images/Stack_Clean_First_Side_Jointed2.JPG
