mikemag/MonkeyWiki/assets/images/Stack_Clean_First_Side_Jointed3.JPG

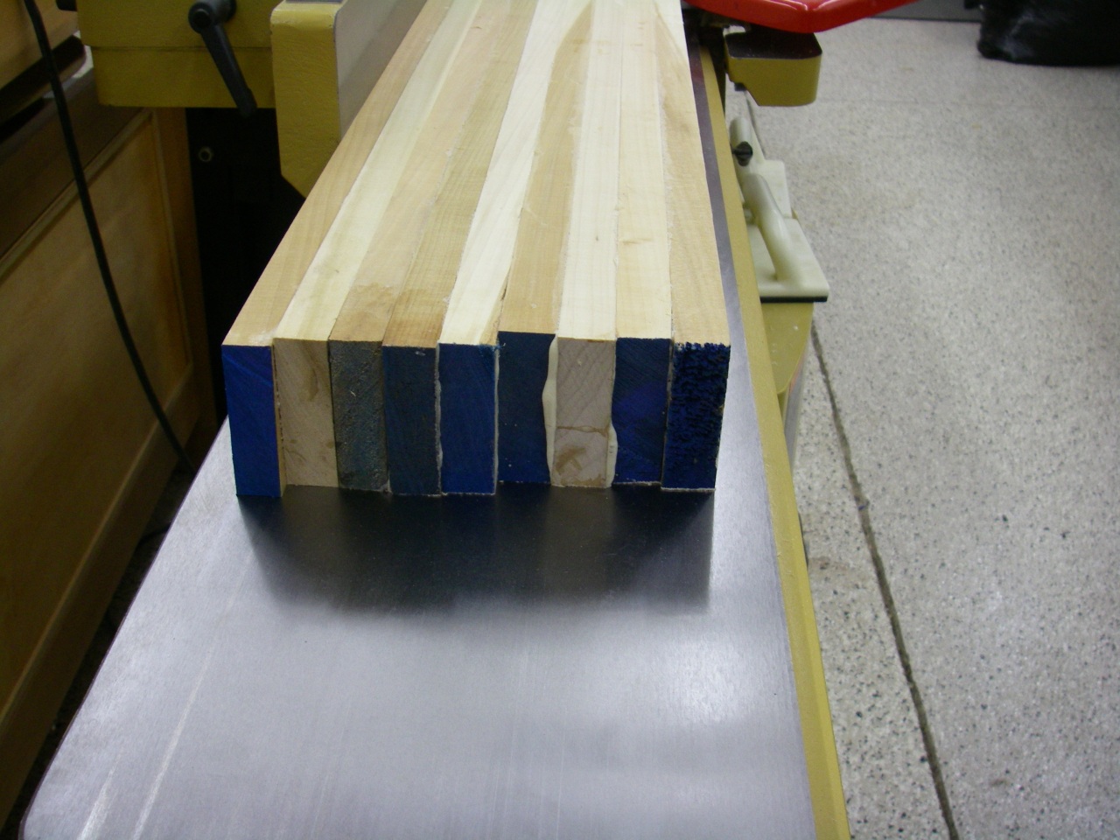
assets/images/Stack_Clean_First_Side_Jointed3.JPG
