mikemag/MonkeyWiki/assets/images/Stack_Clean_Post_Scrape.JPG

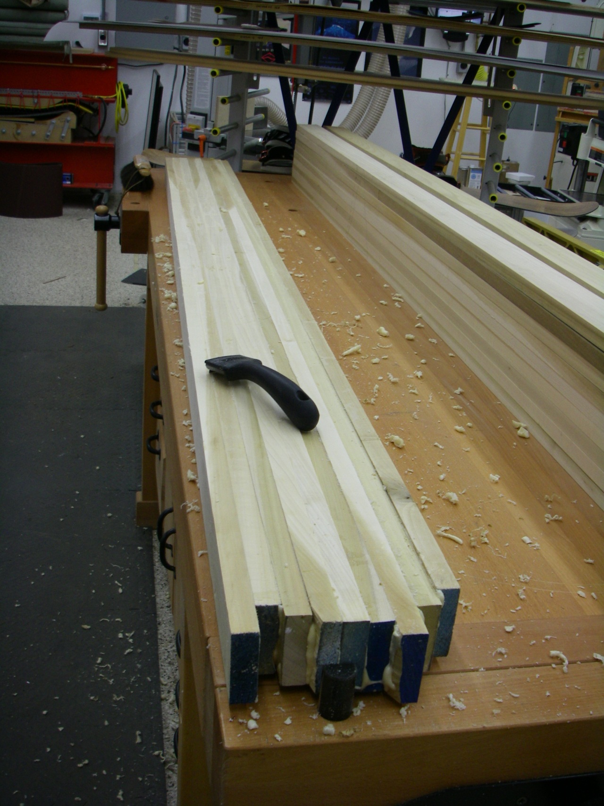
assets/images/Stack_Clean_Post_Scrape.JPG
