mikemag/MonkeyWiki/assets/images/Stack_Clean_Second_Side_Jointed1.JPG

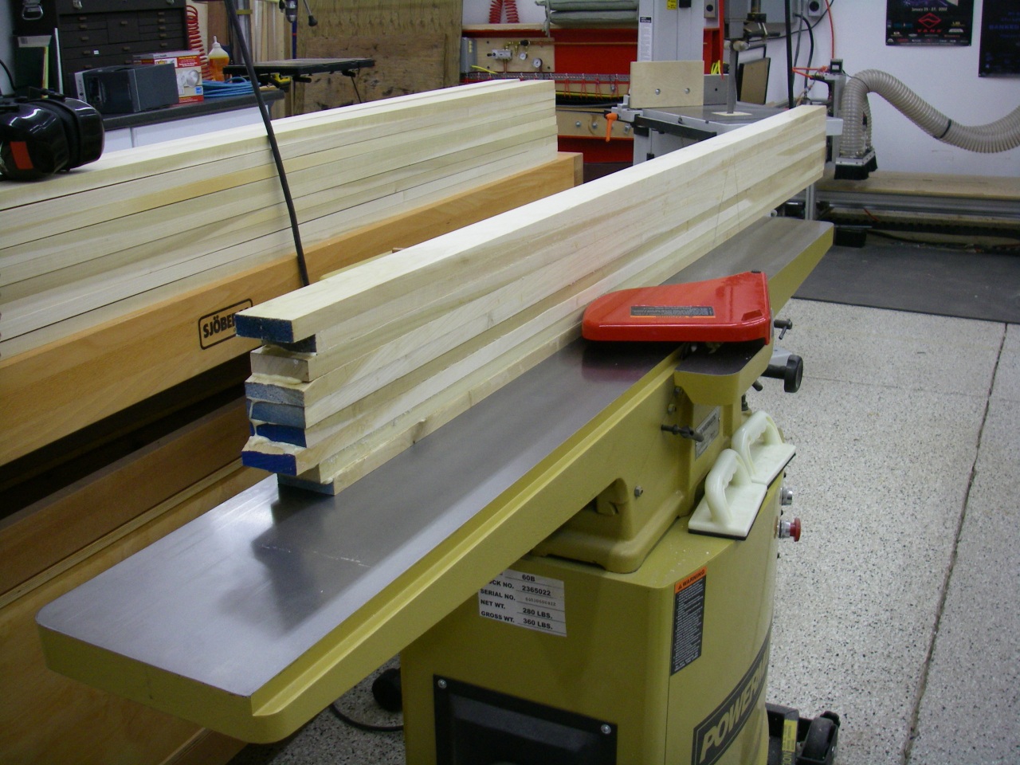
assets/images/Stack_Clean_Second_Side_Jointed1.JPG
