mikemag/MonkeyWiki/assets/images/Stack_Clean_Start.JPG

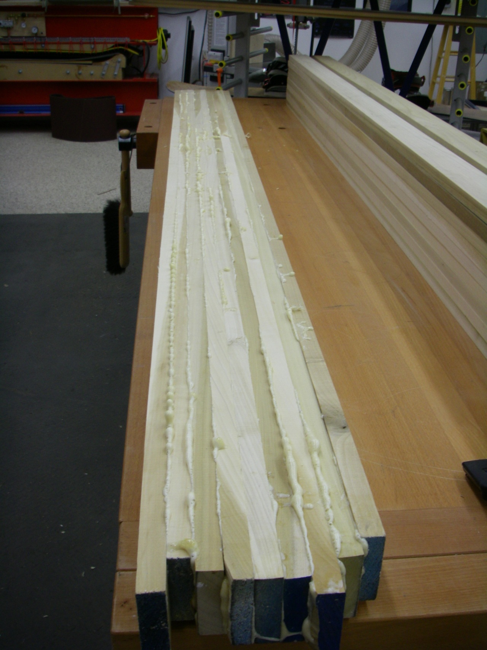
assets/images/Stack_Clean_Start.JPG
