mikemag/MonkeyWiki/assets/images/Stack_Clean_Third_Side1.JPG

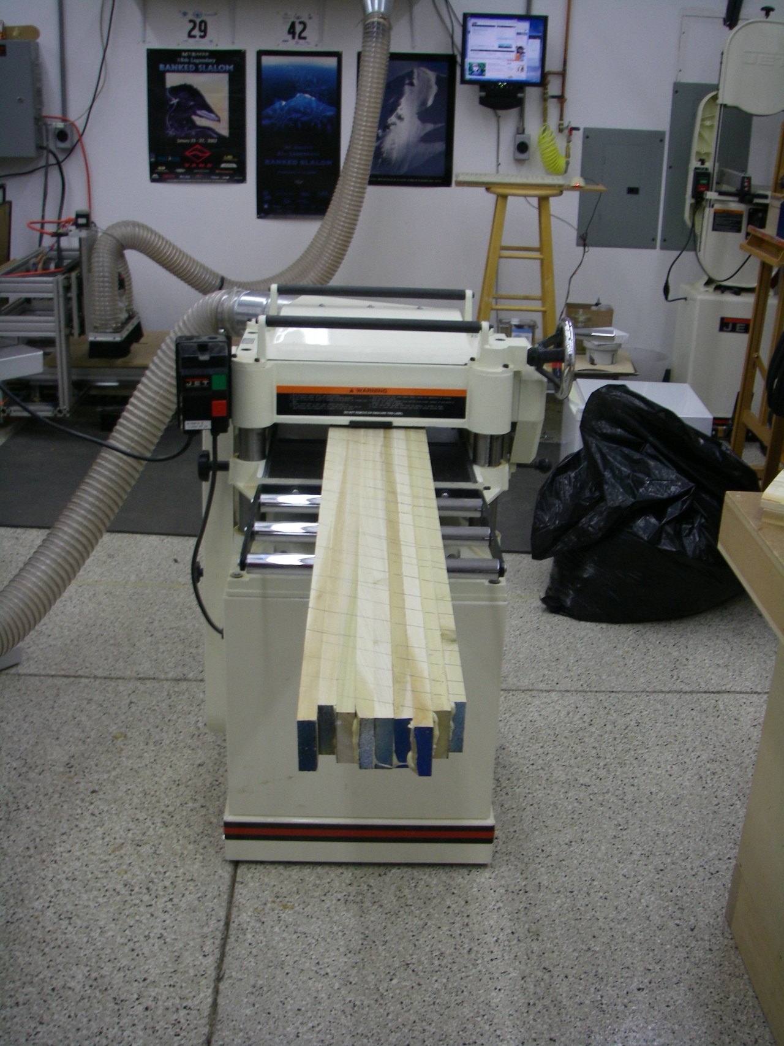
assets/images/Stack_Clean_Third_Side1.JPG
