mikemag/MonkeyWiki/assets/images/Stack_Clean_Third_Side2.JPG

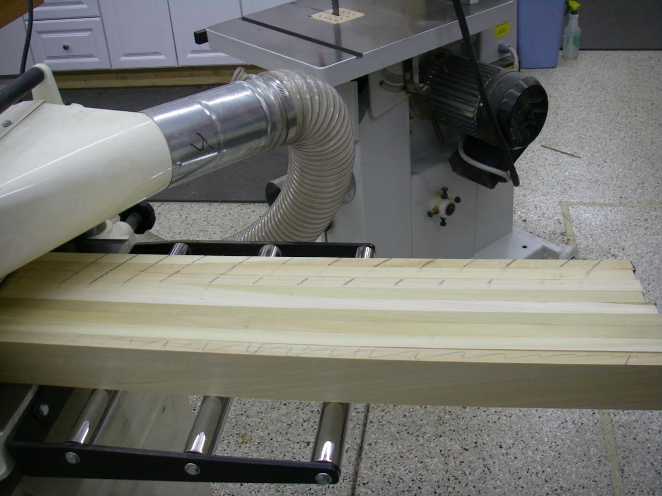
assets/images/Stack_Clean_Third_Side2.JPG
