mikemag/MonkeyWiki/assets/images/Stack_Clean_Third_Side3.JPG

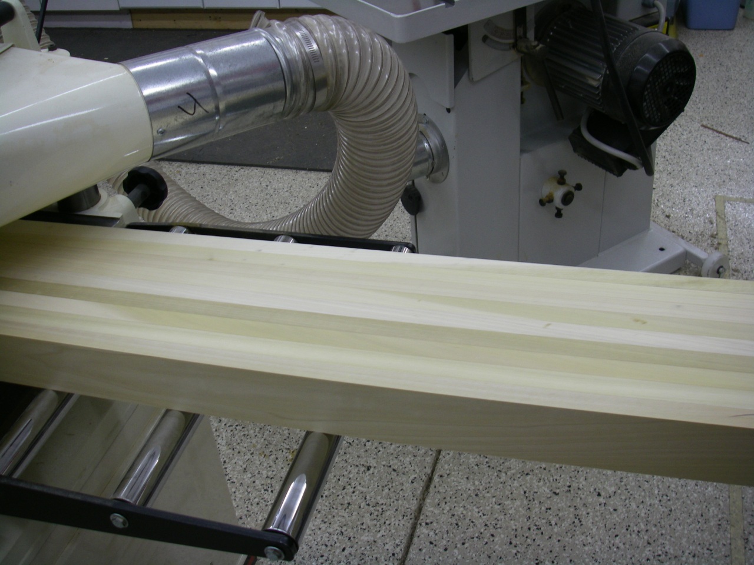
assets/images/Stack_Clean_Third_Side3.JPG
