mikemag/MonkeyWiki/assets/images/Stack_Clean_Third_Side_Ready1.JPG

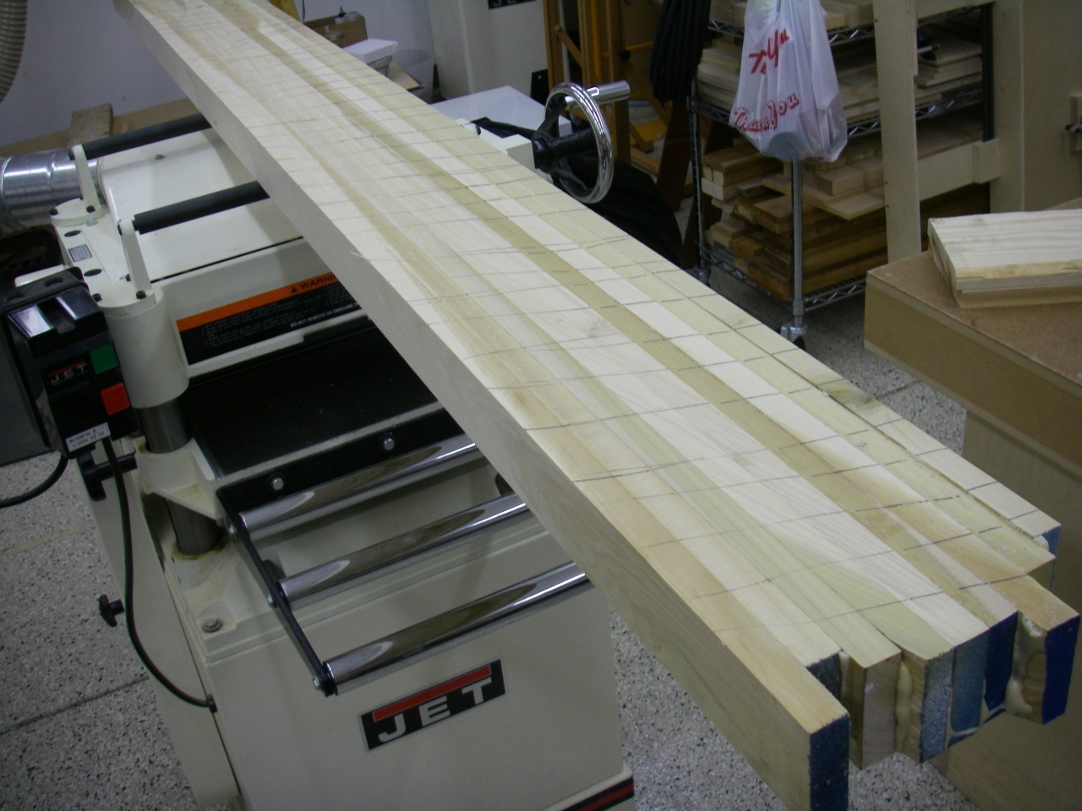
assets/images/Stack_Clean_Third_Side_Ready1.JPG
