mikemag/MonkeyWiki/assets/images/Stack_Clean_Third_Side_Ready2.JPG

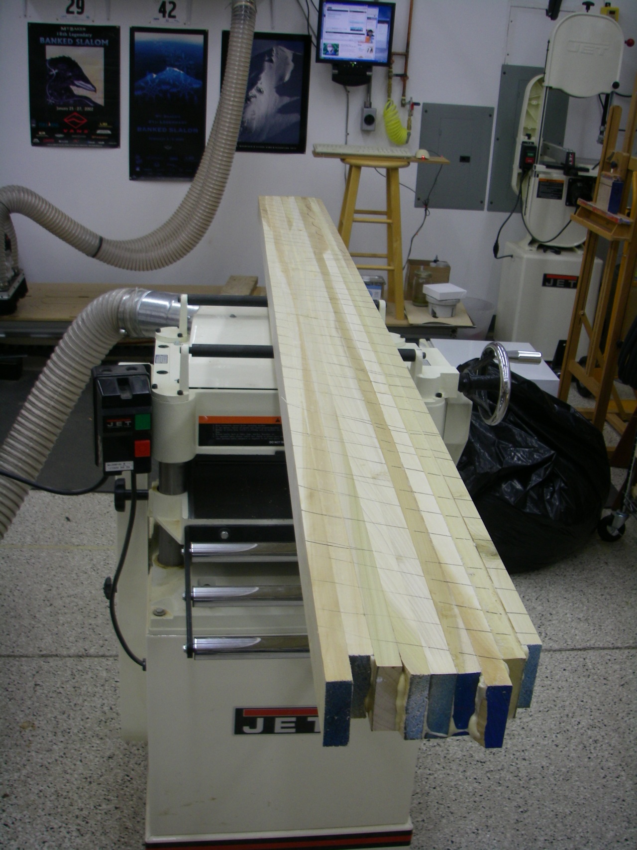
assets/images/Stack_Clean_Third_Side_Ready2.JPG
