mikemag/MonkeyWiki/assets/images/Stack_Layup_Clamping.JPG

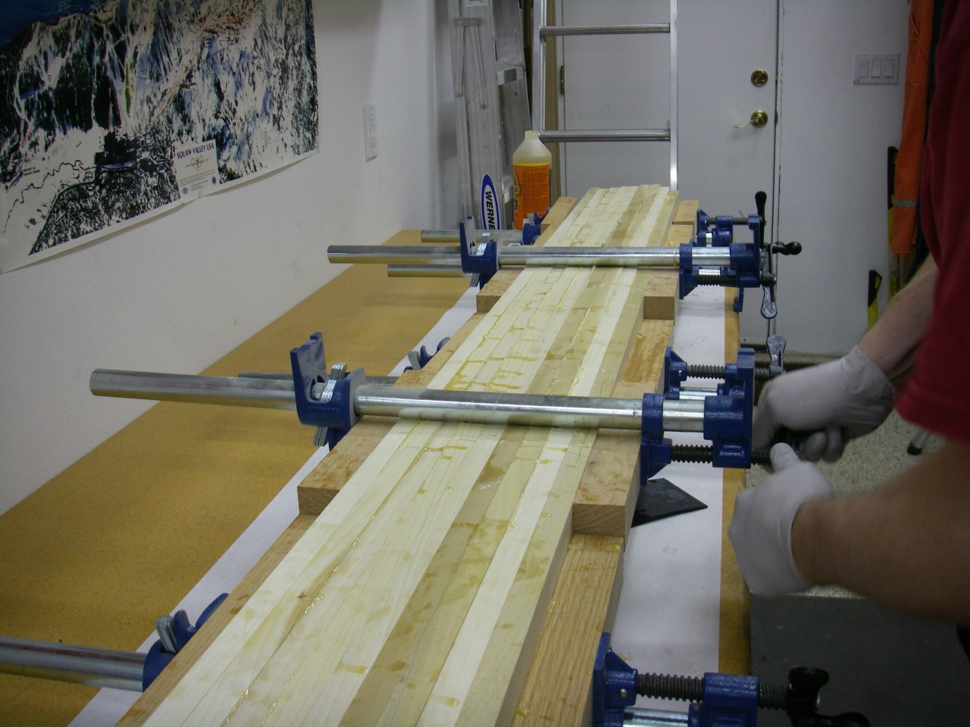
assets/images/Stack_Layup_Clamping.JPG
