mikemag/MonkeyWiki/assets/images/Stack_Layup_Done.JPG

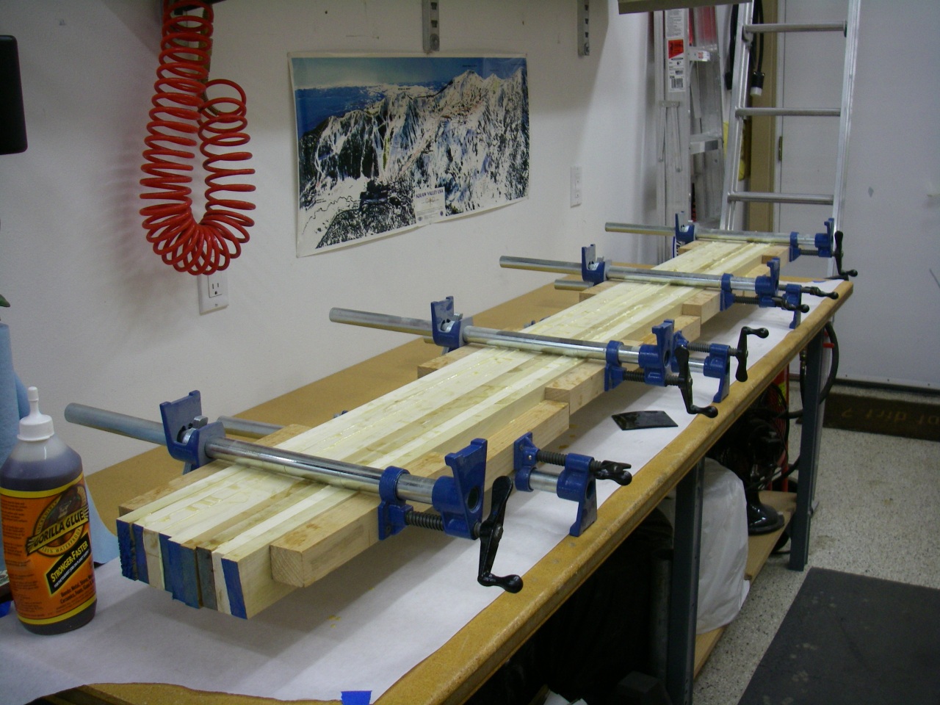
assets/images/Stack_Layup_Done.JPG
