mikemag/MonkeyWiki/assets/images/Stack_Layup_Final_Board.JPG

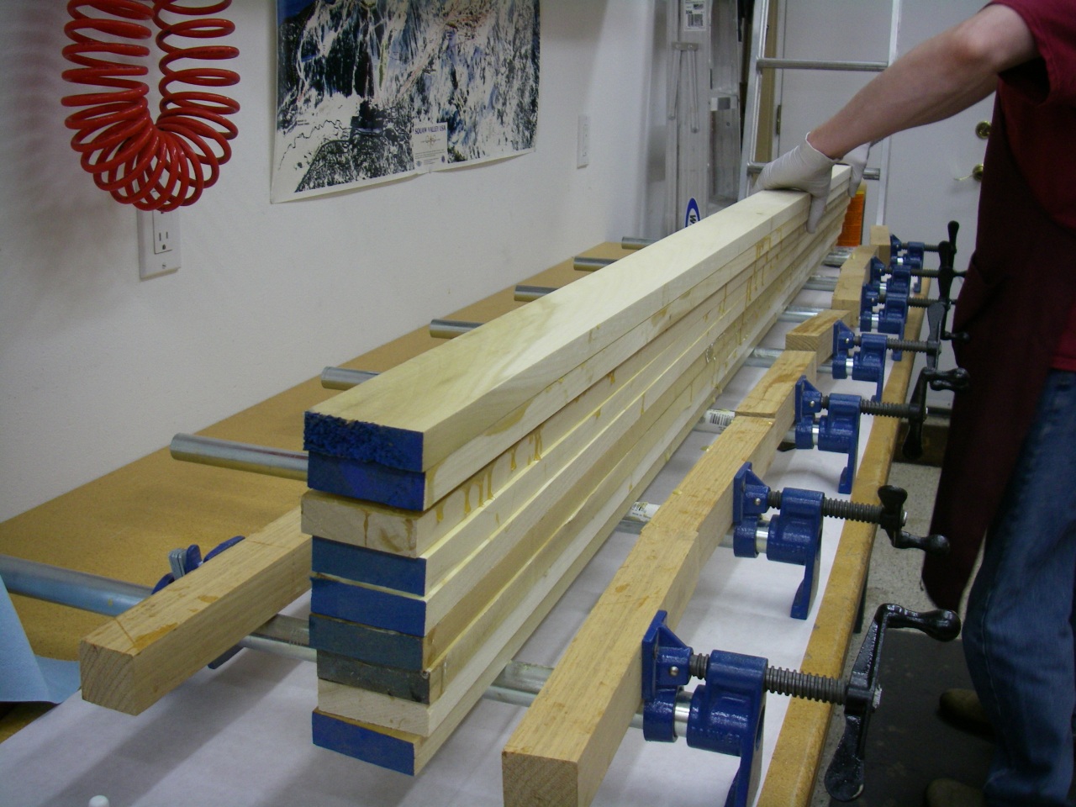
assets/images/Stack_Layup_Final_Board.JPG
