mikemag/MonkeyWiki/assets/images/Stack_Layup_Glue_Pour.JPG

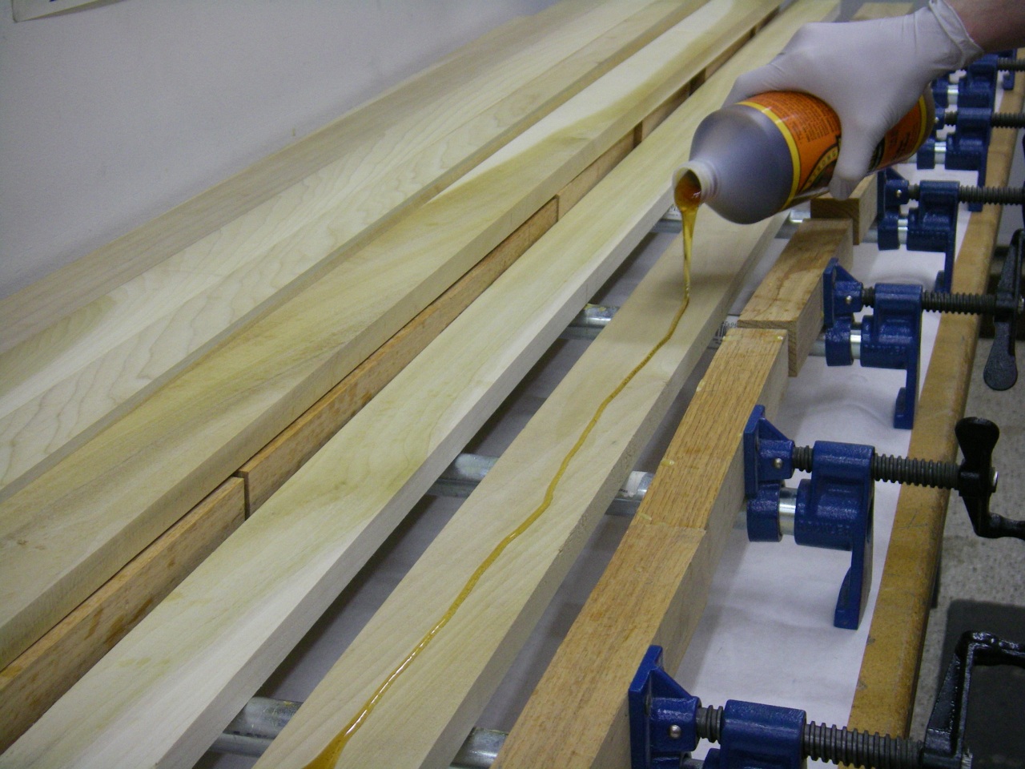
assets/images/Stack_Layup_Glue_Pour.JPG
