mikemag/MonkeyWiki/assets/images/Stack_Layup_Laydown1.JPG

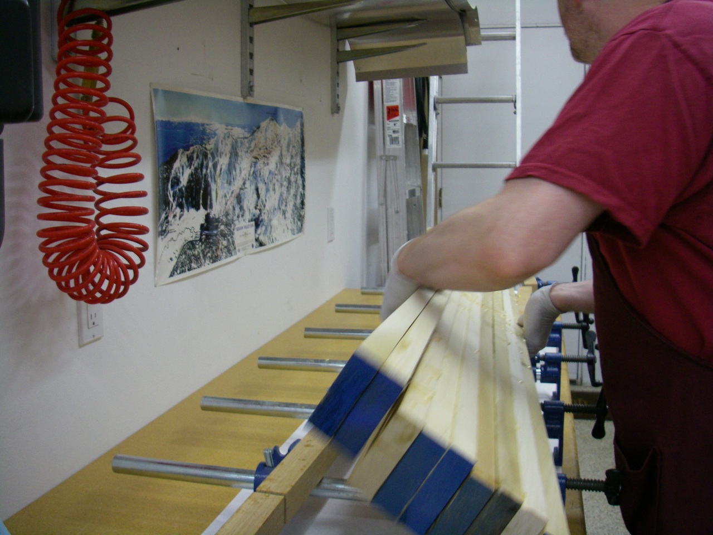
assets/images/Stack_Layup_Laydown1.JPG
