mikemag/MonkeyWiki/assets/images/Stack_Layup_Laydown2.JPG

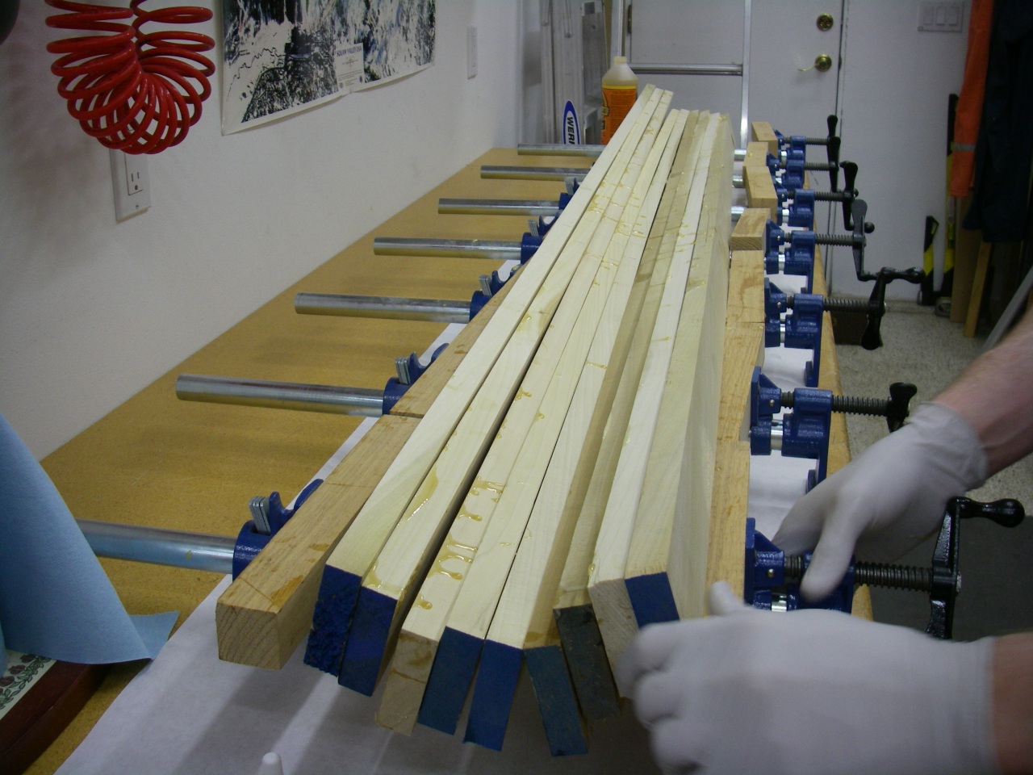
assets/images/Stack_Layup_Laydown2.JPG
