mikemag/MonkeyWiki/assets/images/Stack_Layup_Laydown3.JPG

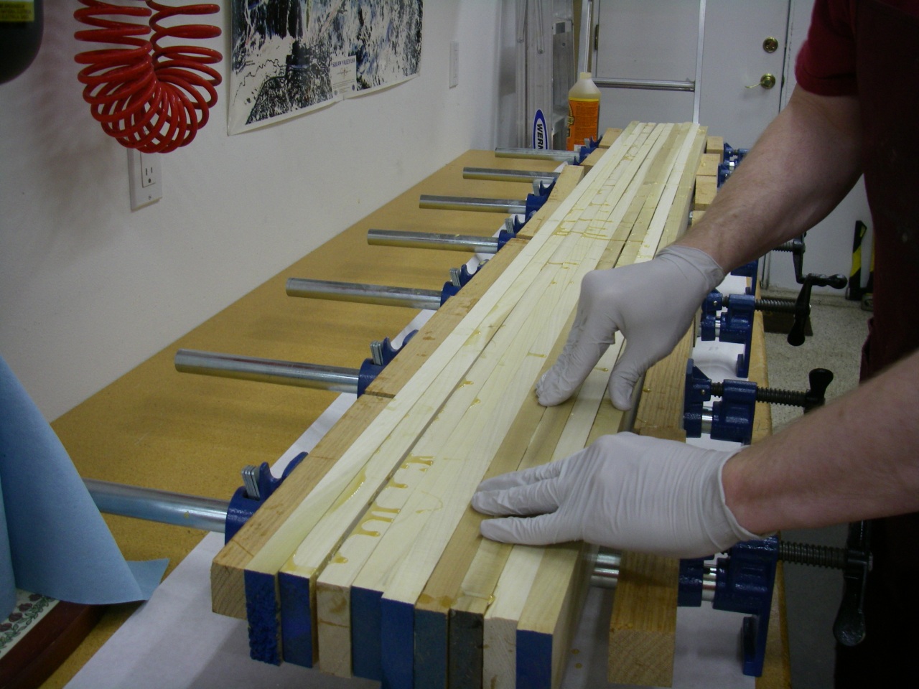
assets/images/Stack_Layup_Laydown3.JPG
