mikemag/MonkeyWiki/assets/images/Stack_Layup_Ready.JPG

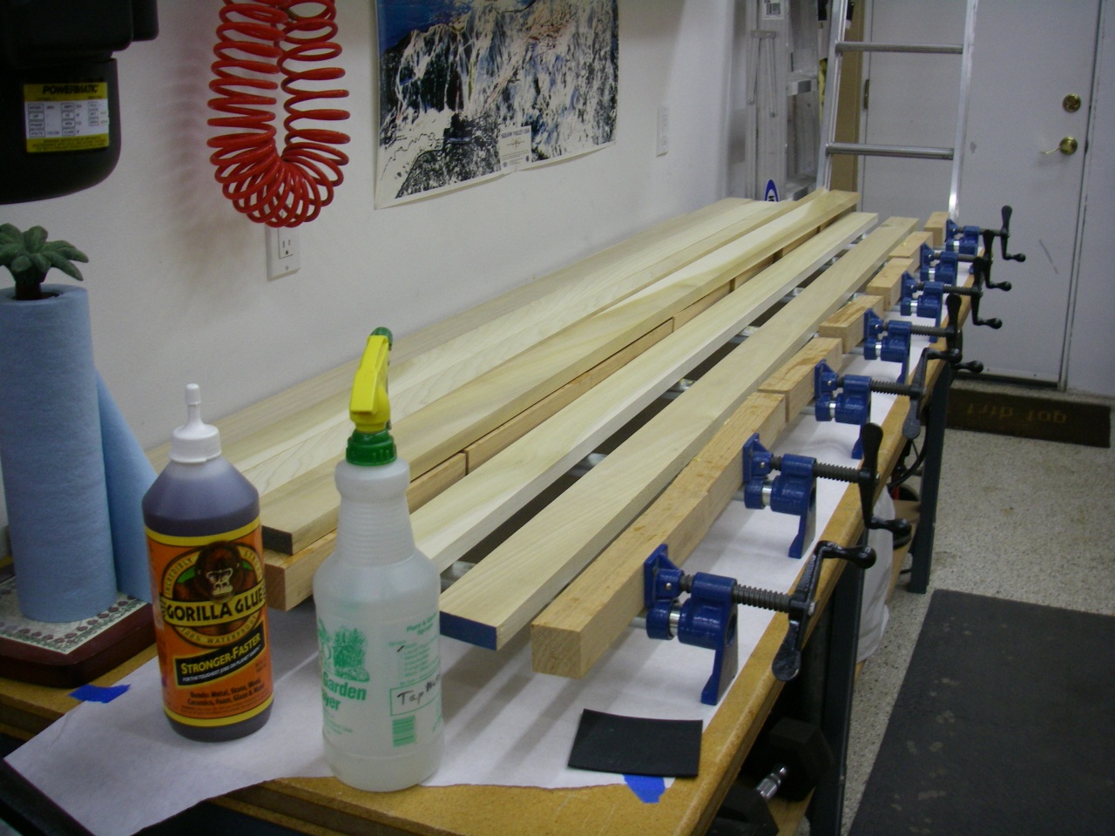
assets/images/Stack_Layup_Ready.JPG
