mikemag/MonkeyWiki/assets/images/Stack_Layup_Second_Board.JPG

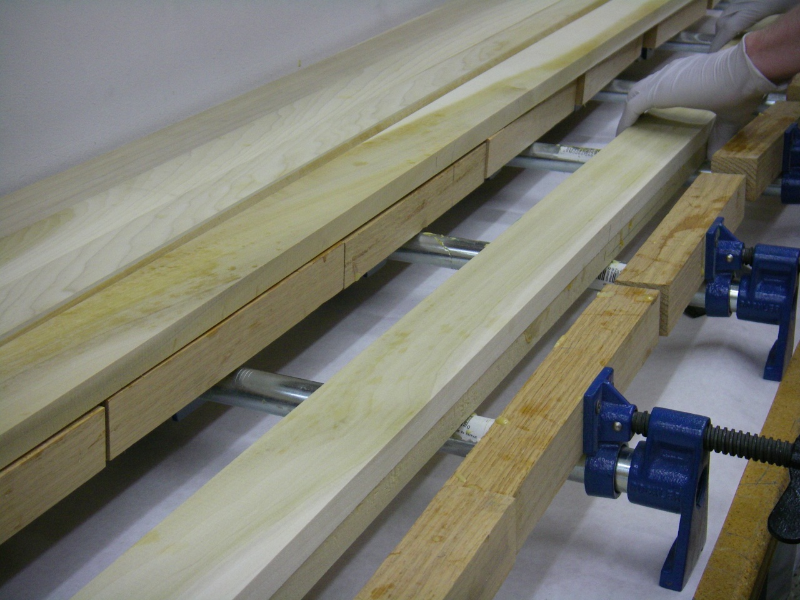
assets/images/Stack_Layup_Second_Board.JPG
