mikemag/MonkeyWiki/assets/images/Stack_Layup_Spreding.JPG

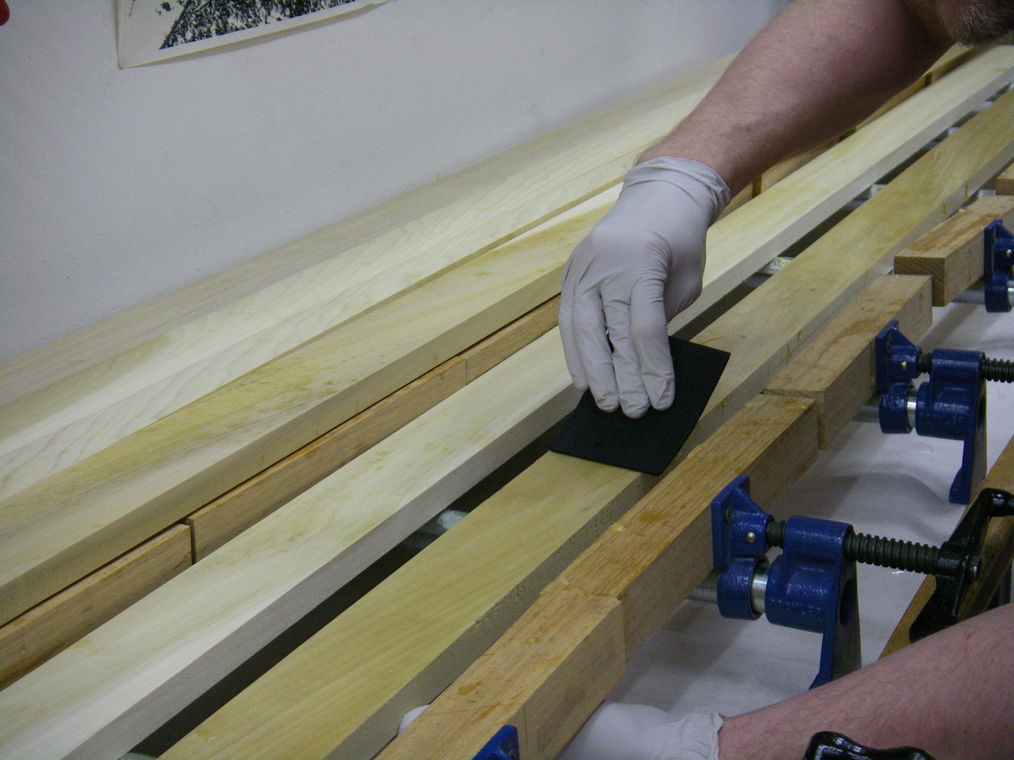
assets/images/Stack_Layup_Spreding.JPG
