mikemag/MonkeyWiki/assets/images/Stack_Layup_Third_Board.JPG

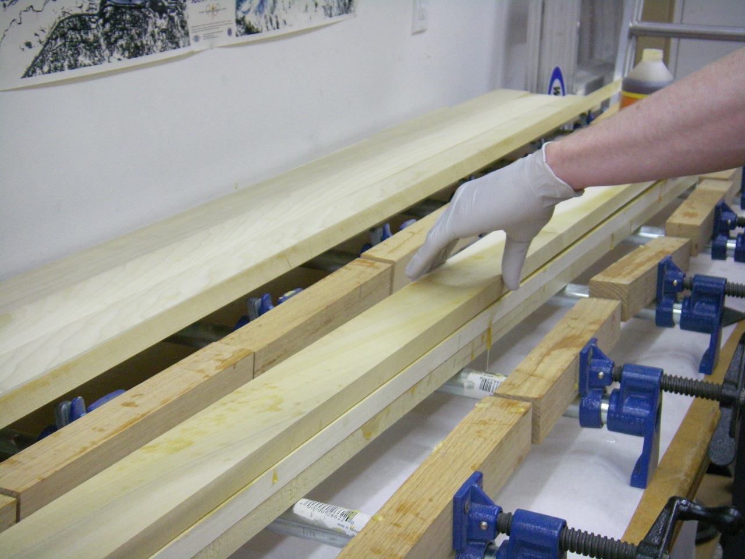
assets/images/Stack_Layup_Third_Board.JPG
