mikemag/MonkeyWiki/assets/images/Stack_Layup_Water.JPG

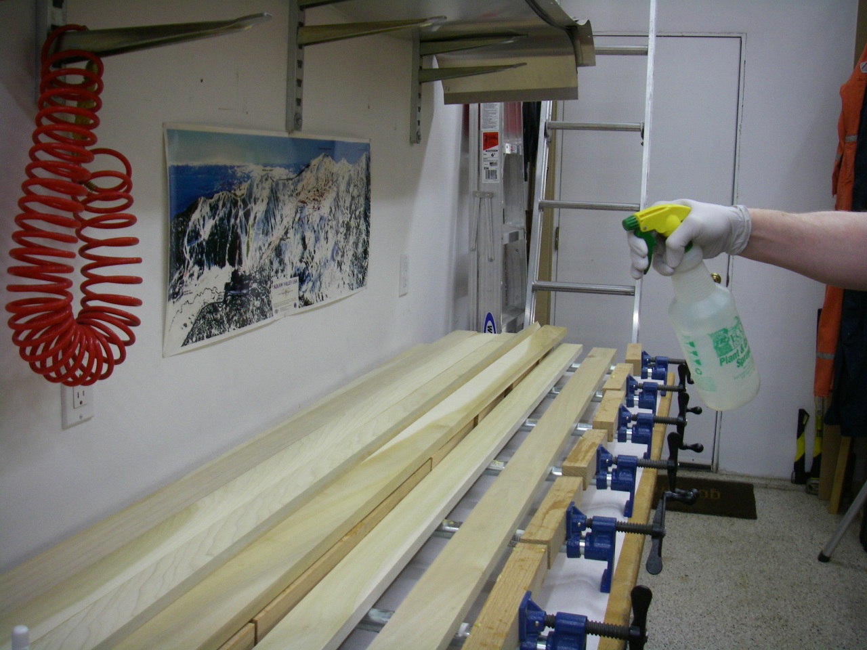
assets/images/Stack_Layup_Water.JPG
