mikemag/MonkeyWiki/assets/images/Stack_Matching_In_Progress.JPG

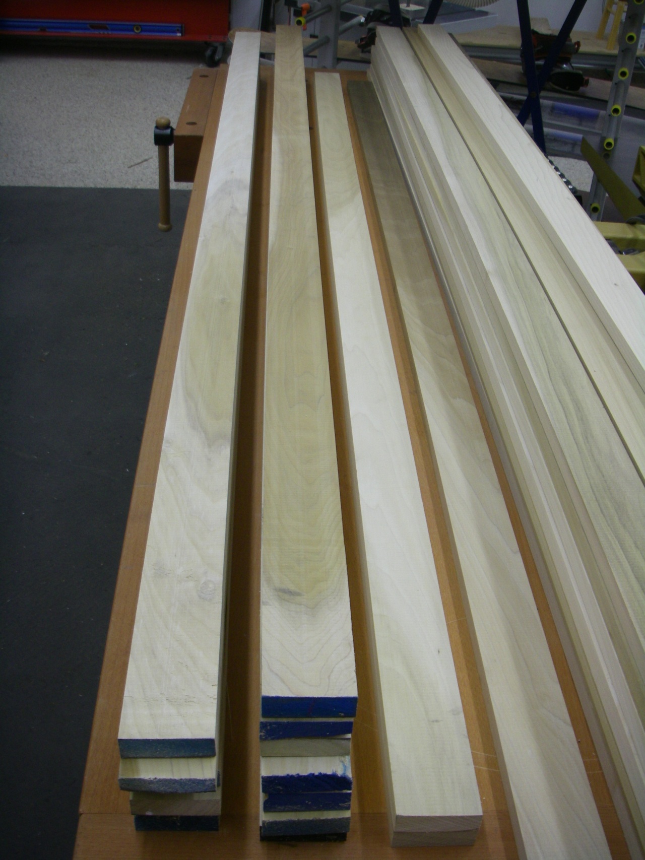
assets/images/Stack_Matching_In_Progress.JPG
