mikemag/MonkeyWiki/assets/images/Stack_Matching_One_Done.JPG

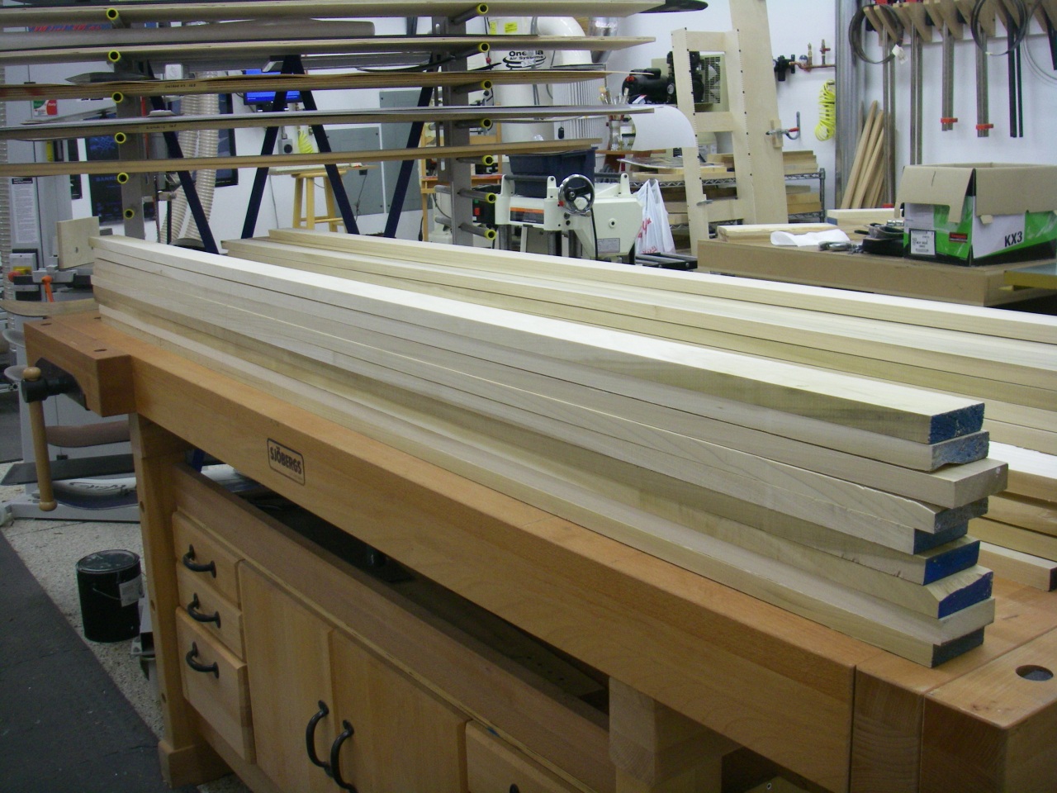
assets/images/Stack_Matching_One_Done.JPG
