mikemag/MonkeyWiki/assets/images/Stack_Matching_Raw.JPG

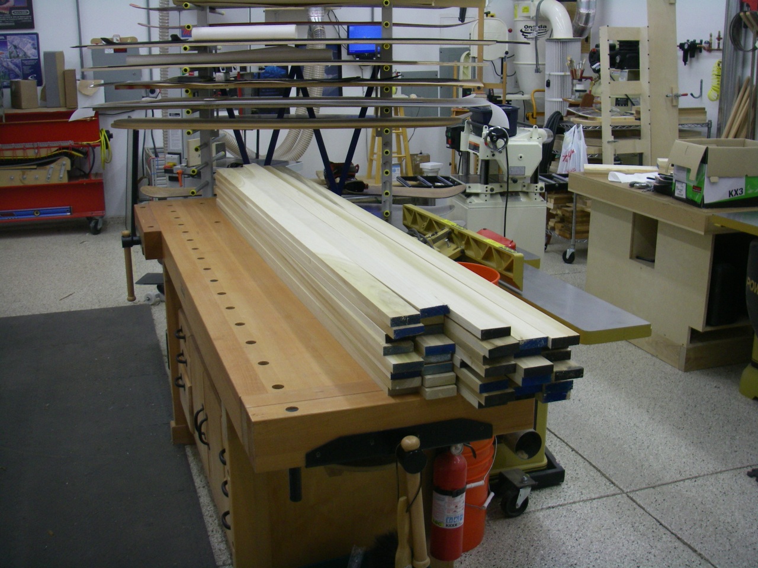
assets/images/Stack_Matching_Raw.JPG
