mikemag/MonkeyWiki/assets/images/Stack_Slicing_Cleanup_After_First.JPG

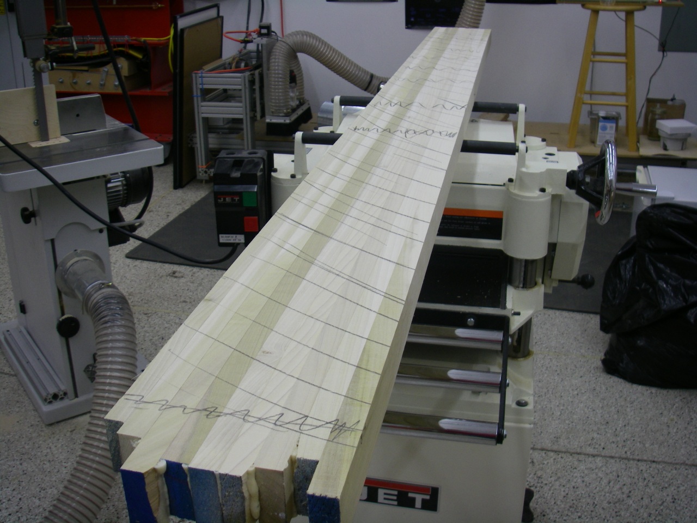
assets/images/Stack_Slicing_Cleanup_After_First.JPG
