mikemag/MonkeyWiki/assets/images/Stack_Slicing_Cleanup_After_Second.JPG

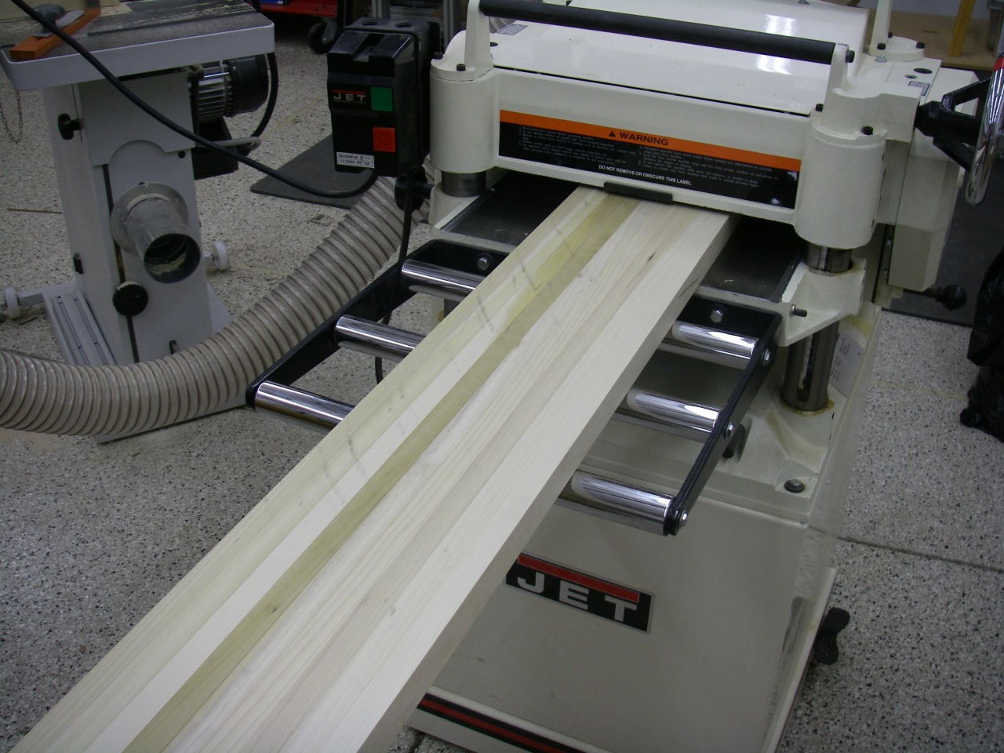
assets/images/Stack_Slicing_Cleanup_After_Second.JPG
