mikemag/MonkeyWiki/assets/images/Stack_Slicing_Done.JPG

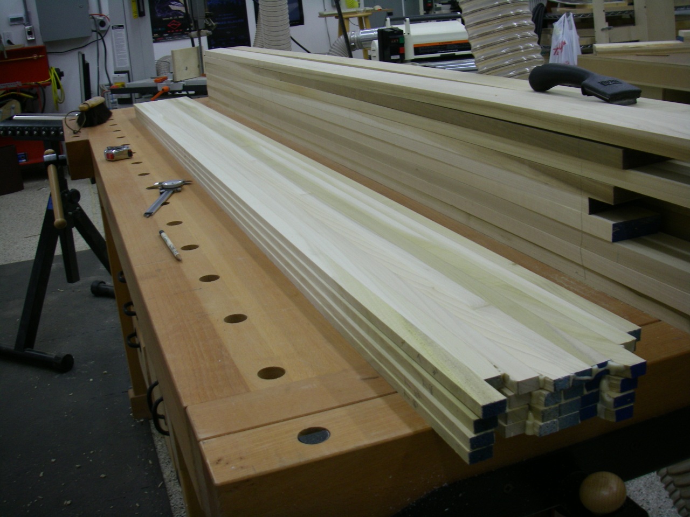
assets/images/Stack_Slicing_Done.JPG
