mikemag/MonkeyWiki/assets/images/Stack_Slicing_First_Slice.JPG

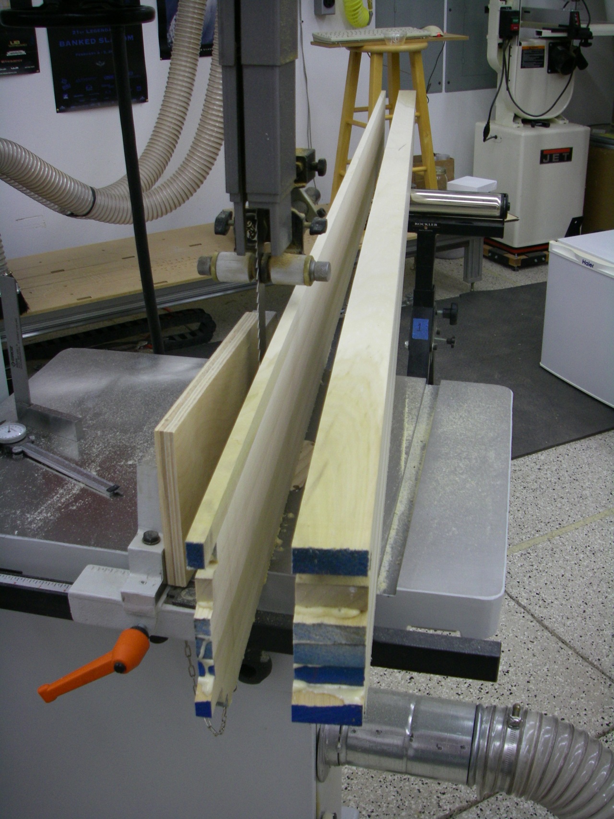
assets/images/Stack_Slicing_First_Slice.JPG
