mikemag/MonkeyWiki/assets/images/Stack_Slicing_Labeling.JPG

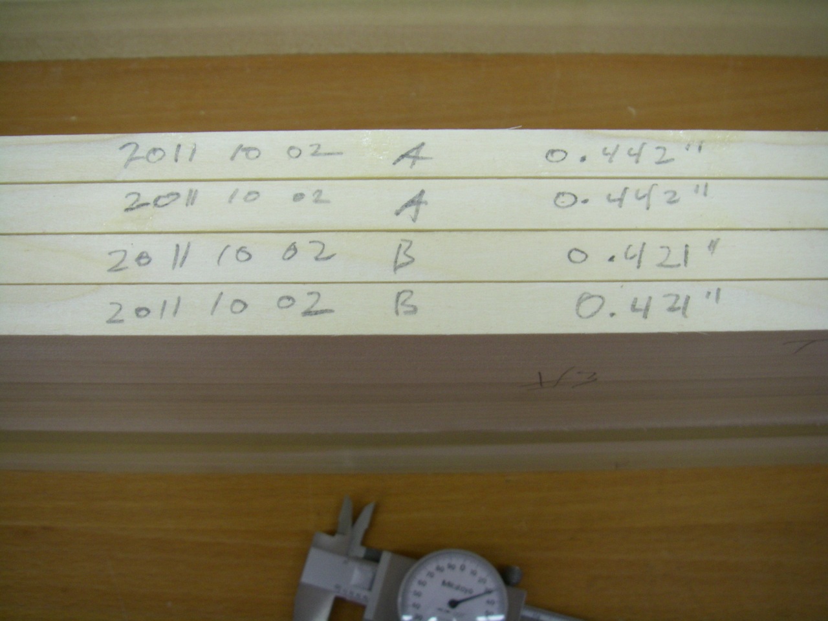
assets/images/Stack_Slicing_Labeling.JPG
