mikemag/MonkeyWiki/assets/images/Stack_Slicing_Pair_Cleanup1.JPG

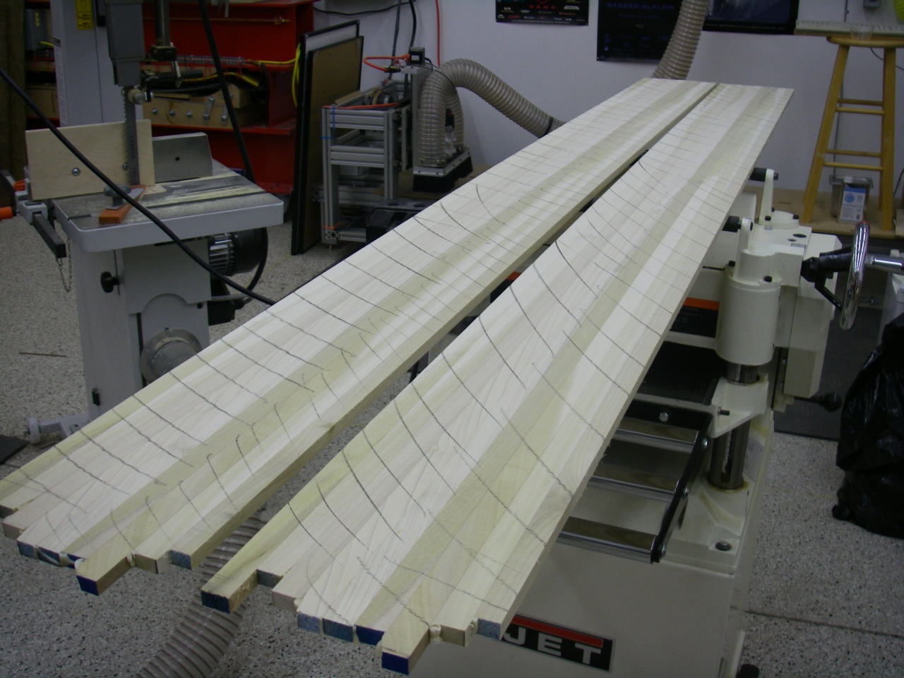
assets/images/Stack_Slicing_Pair_Cleanup1.JPG
