mikemag/MonkeyWiki/assets/images/Stack_Slicing_Pair_Cleanup2.JPG

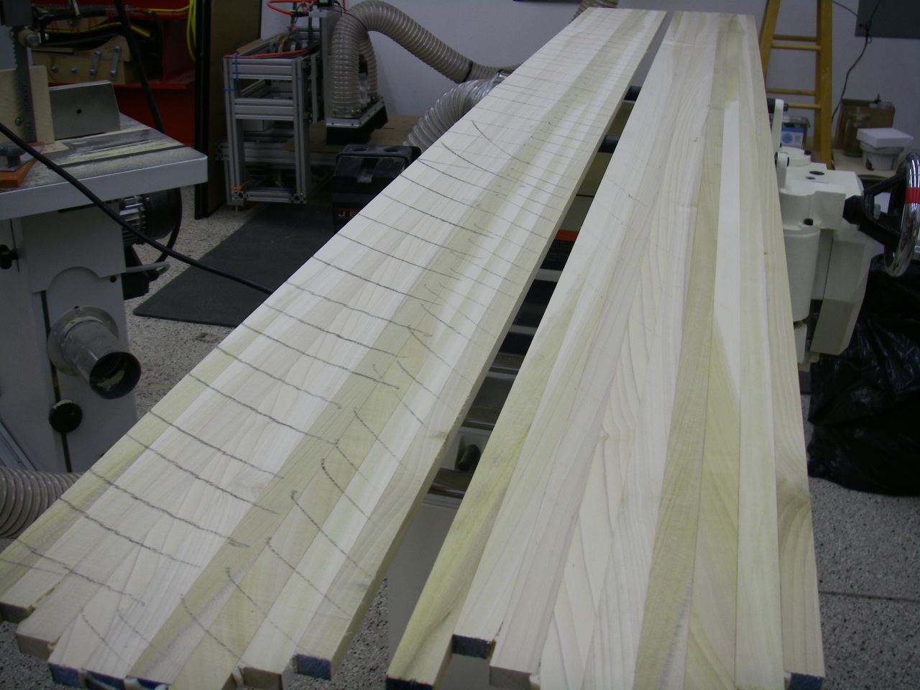
assets/images/Stack_Slicing_Pair_Cleanup2.JPG
