mikemag/MonkeyWiki/assets/images/Stack_Slicing_Pair_Cleanup3.JPG

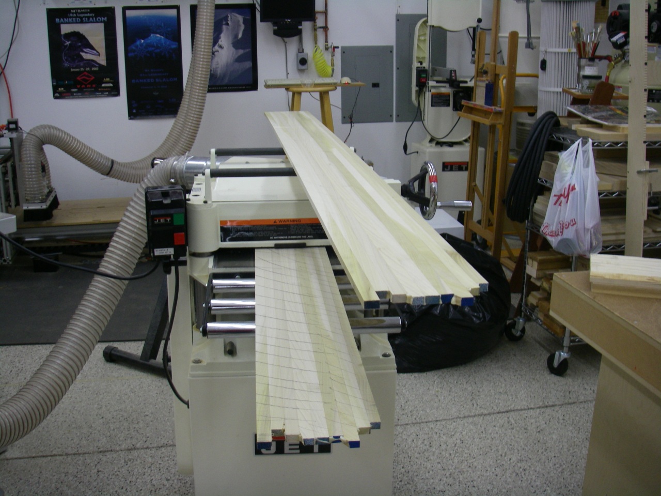
assets/images/Stack_Slicing_Pair_Cleanup3.JPG
