mikemag/MonkeyWiki/assets/images/Stack_Slicing_Pair_Done1.JPG

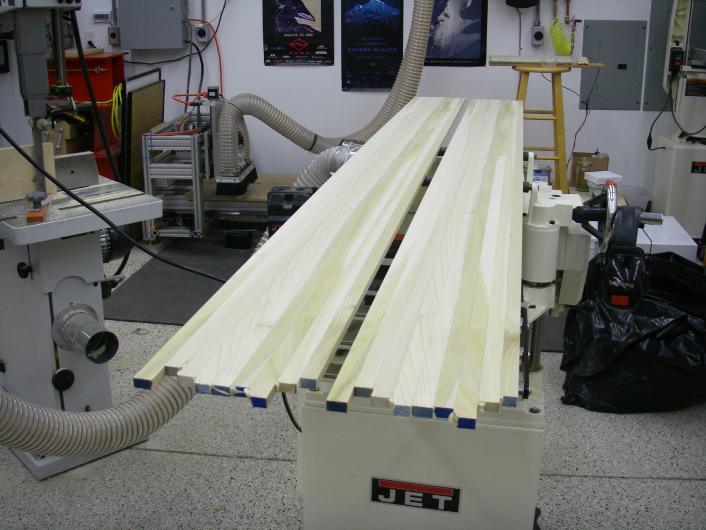
assets/images/Stack_Slicing_Pair_Done1.JPG
