mikemag/MonkeyWiki/assets/images/Stack_Slicing_Pair_Done2.JPG

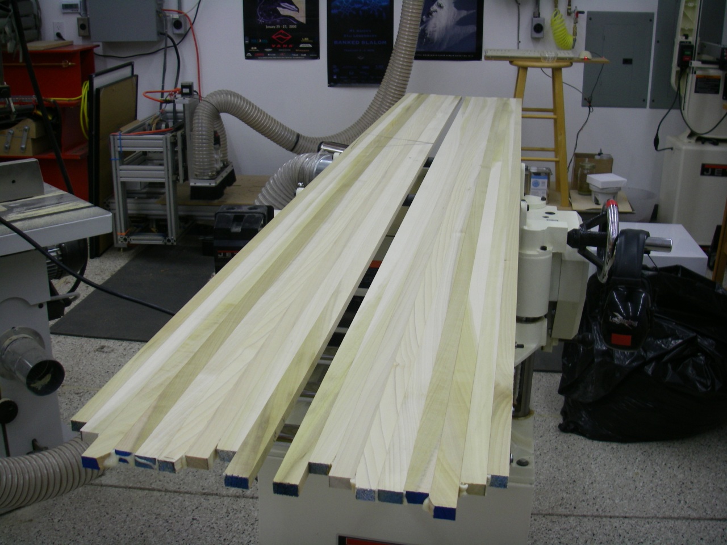
assets/images/Stack_Slicing_Pair_Done2.JPG
