mikemag/MonkeyWiki/assets/images/Stack_Slicing_Ready1.JPG

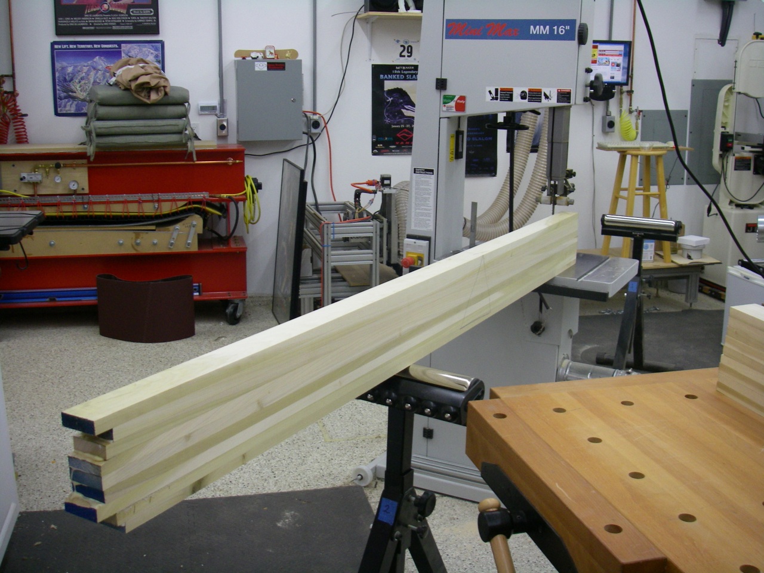
assets/images/Stack_Slicing_Ready1.JPG
