mikemag/MonkeyWiki/assets/images/Stack_Slicing_Ready2.JPG

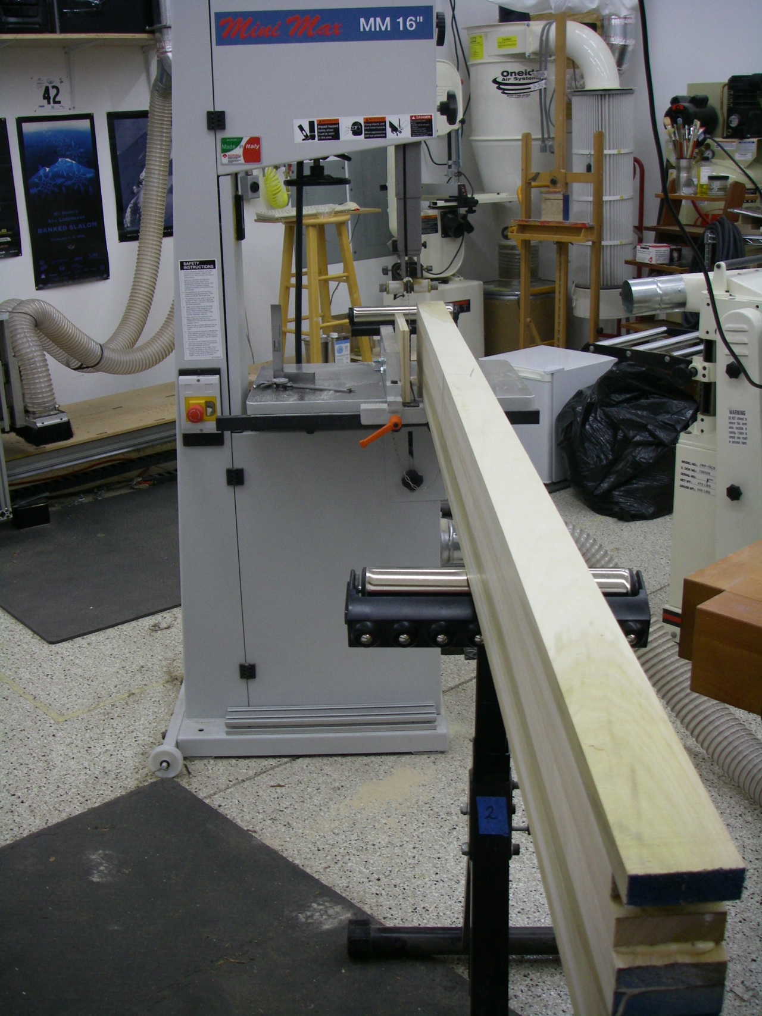
assets/images/Stack_Slicing_Ready2.JPG
