mikemag/MonkeyWiki/assets/images/Stack_Slicing_Ready3.JPG

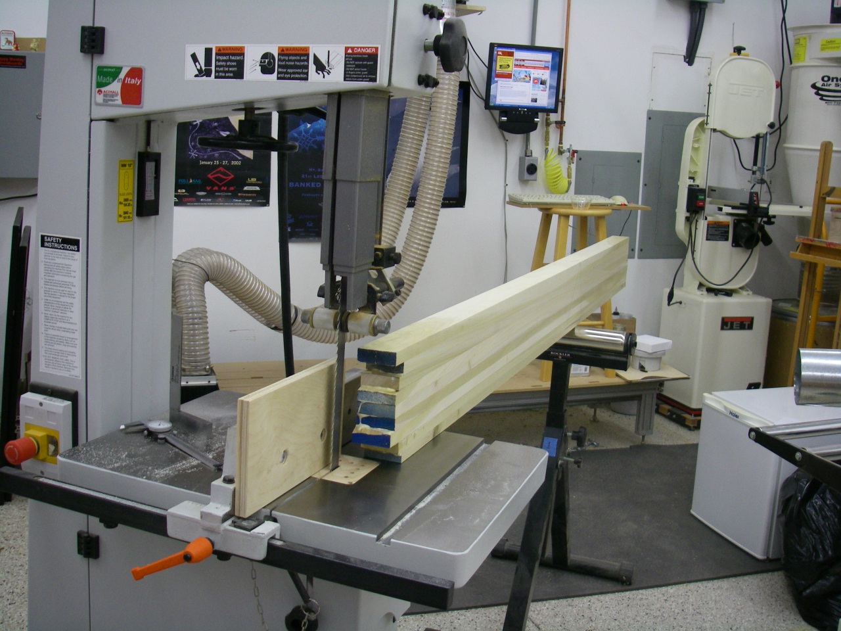
assets/images/Stack_Slicing_Ready3.JPG
