mikemag/MonkeyWiki/assets/images/Stack_Slicing_Second_Slice.JPG

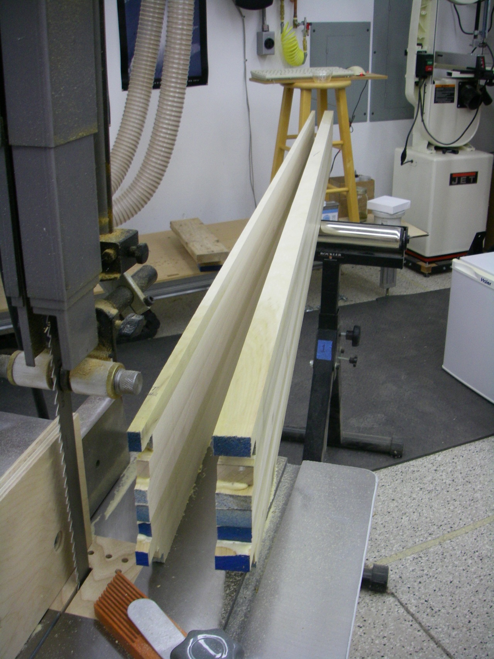
assets/images/Stack_Slicing_Second_Slice.JPG
