mikemag/MonkeyWiki/assets/images/Stack_Slicing_Slices.JPG

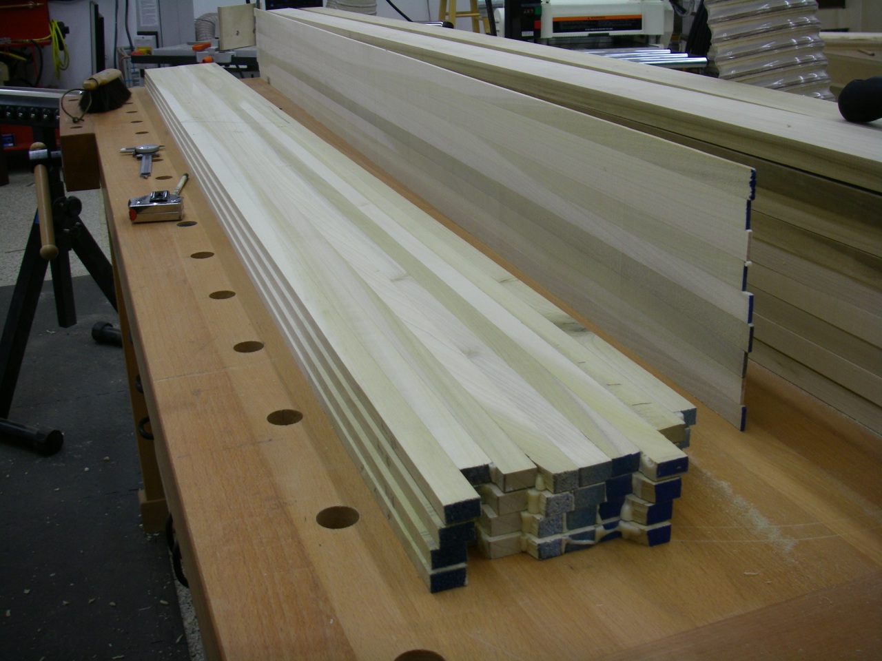
assets/images/Stack_Slicing_Slices.JPG
