mikemag/MonkeyWiki/assets/images/Stack_Slicing_Third_and_Fourth.JPG

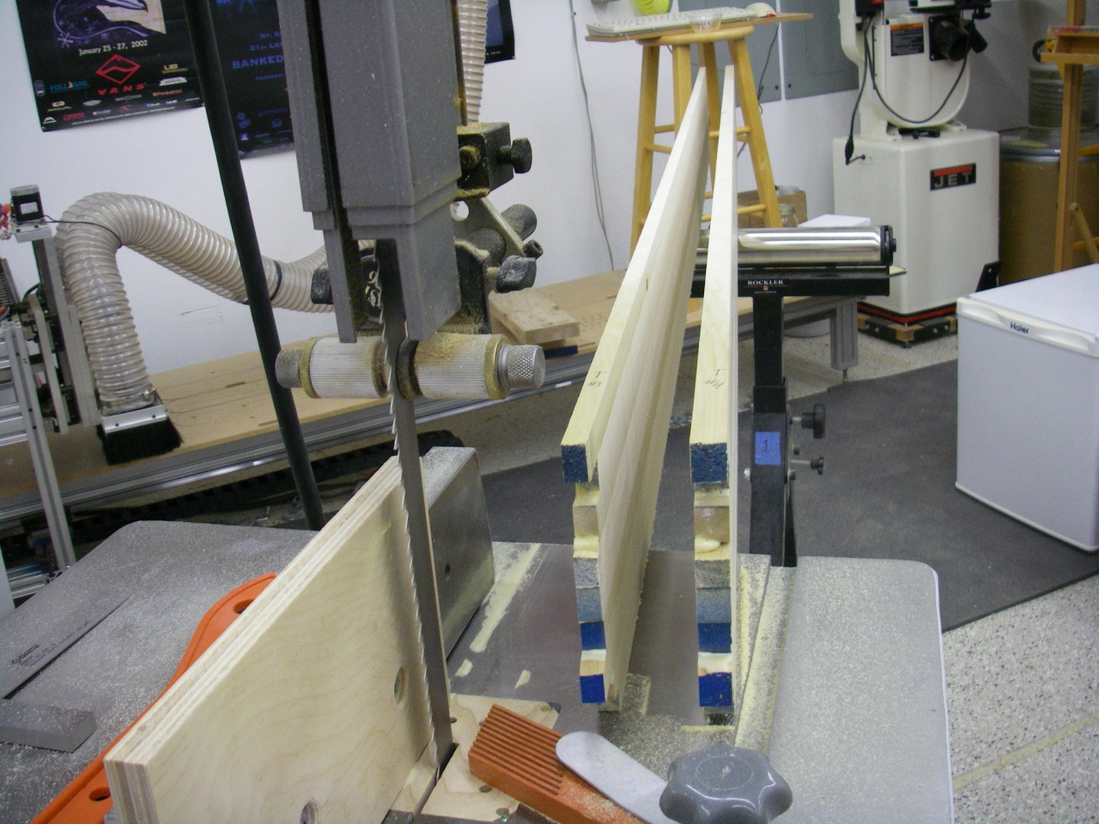
assets/images/Stack_Slicing_Third_and_Fourth.JPG
