mikemag/MonkeyWiki/assets/images/Trimmer1.jpg

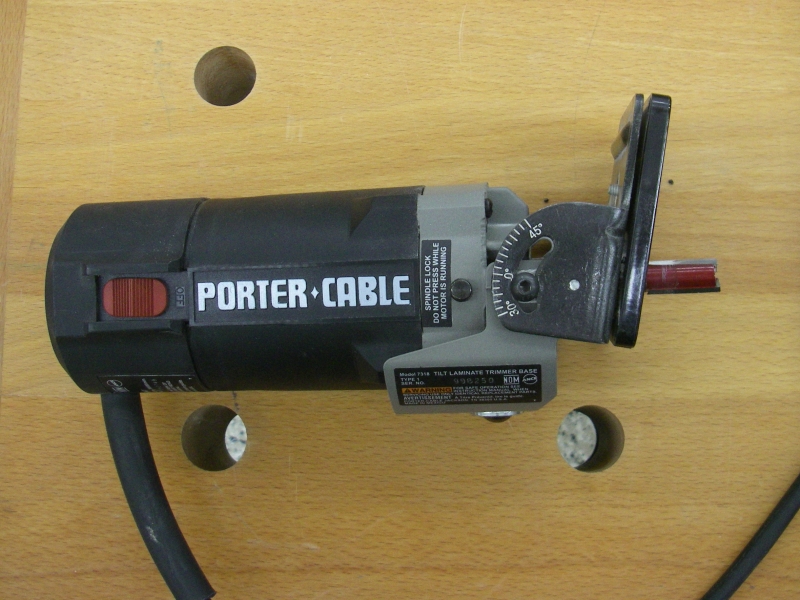
assets/images/Trimmer1.jpg
