mikemag/MonkeyWiki/assets/images/Trimmer2.jpg

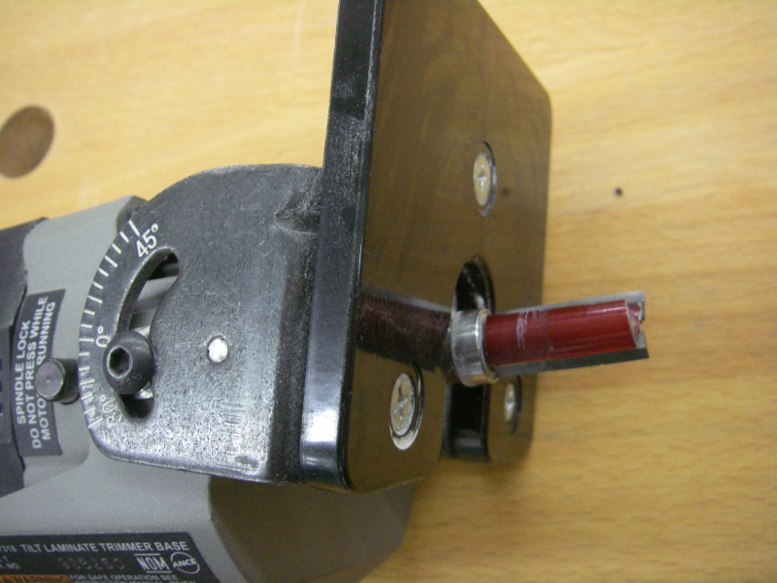
assets/images/Trimmer2.jpg
