mikemag/MonkeyWiki/assets/images/Trimmer3.jpg

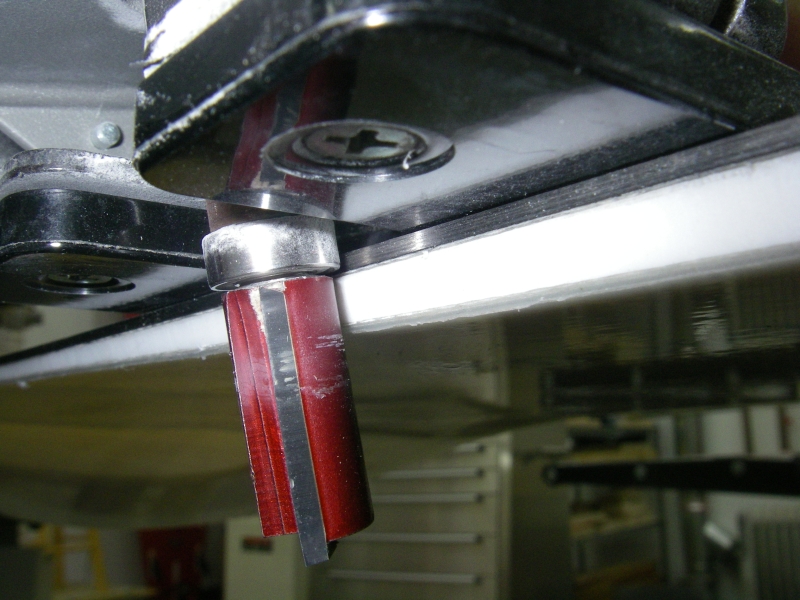
assets/images/Trimmer3.jpg
