mikemag/MonkeyWiki/assets/images/Vacuum_boards.JPG

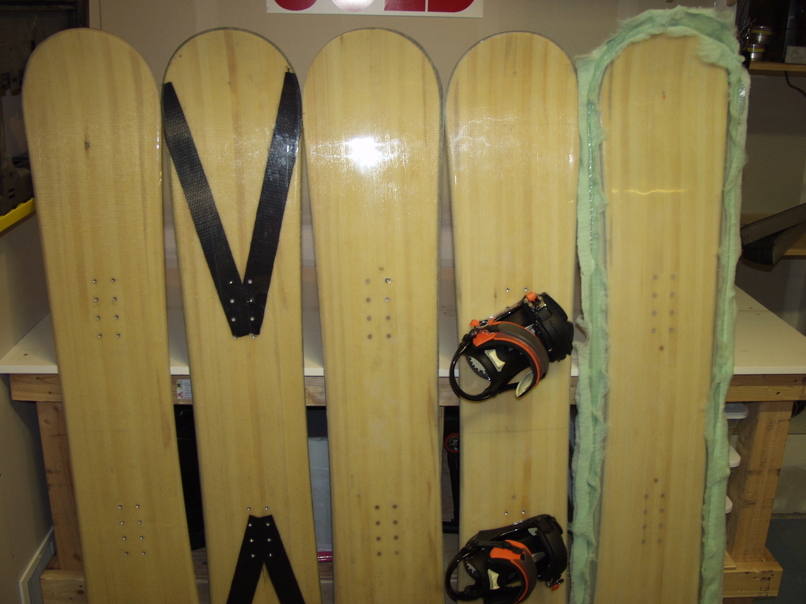
assets/images/Vacuum_boards.JPG
