mikemag/MonkeyWiki/assets/images/Vacuum_mold_1.jpg

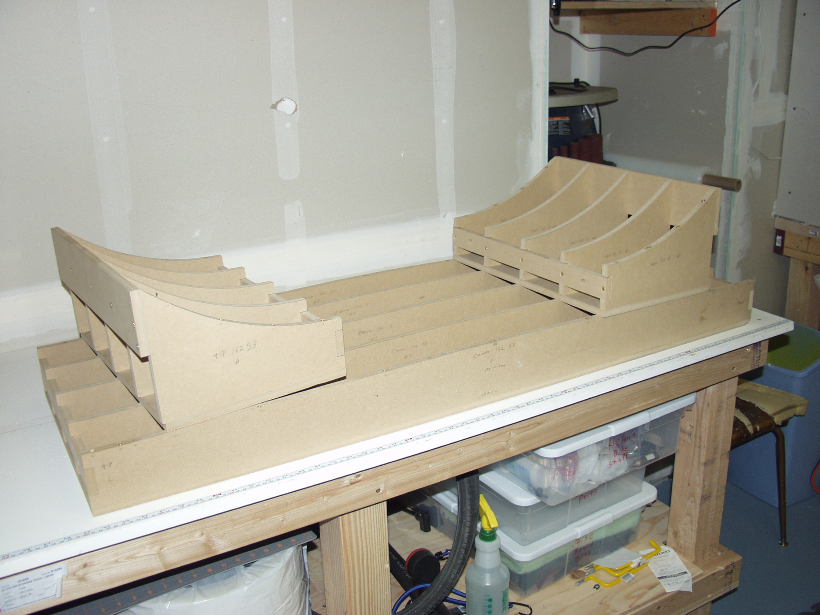
assets/images/Vacuum_mold_1.jpg
