mikemag/MonkeyWiki/assets/images/Vacuum_mold_2.jpg

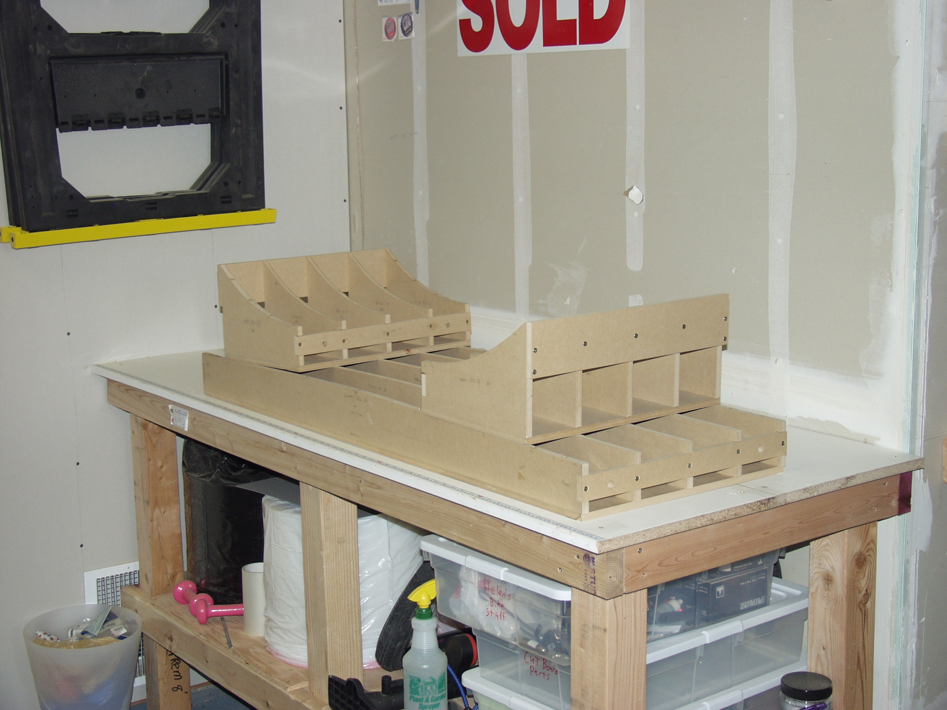
assets/images/Vacuum_mold_2.jpg
