mikemag/MonkeyWiki/assets/images/Vacuum_mold_3.jpg

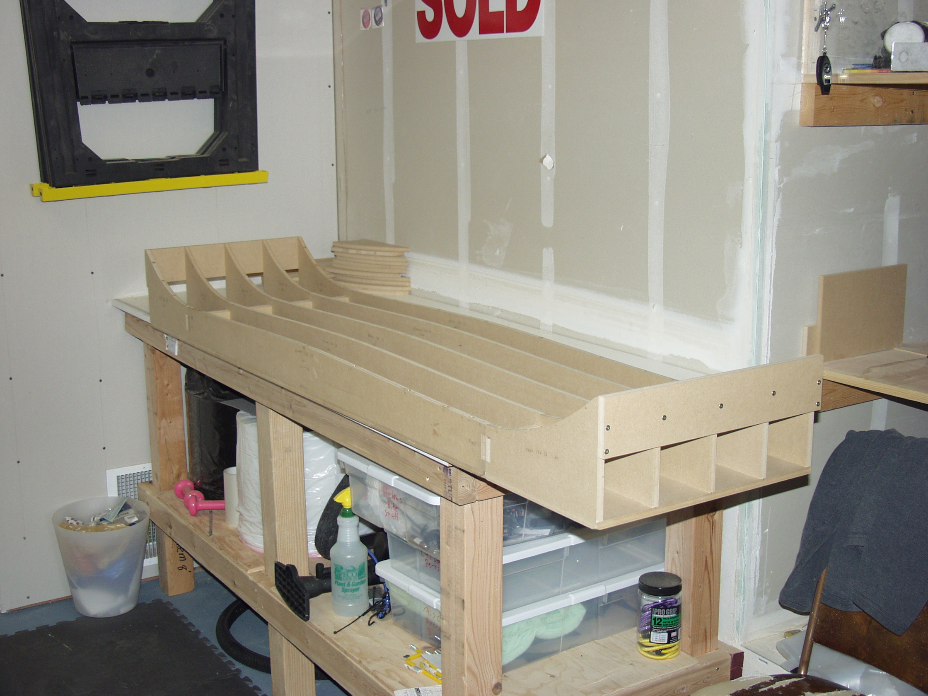
assets/images/Vacuum_mold_3.jpg
