mikemag/MonkeyWiki/assets/images/Vacuum_mold_4.jpg

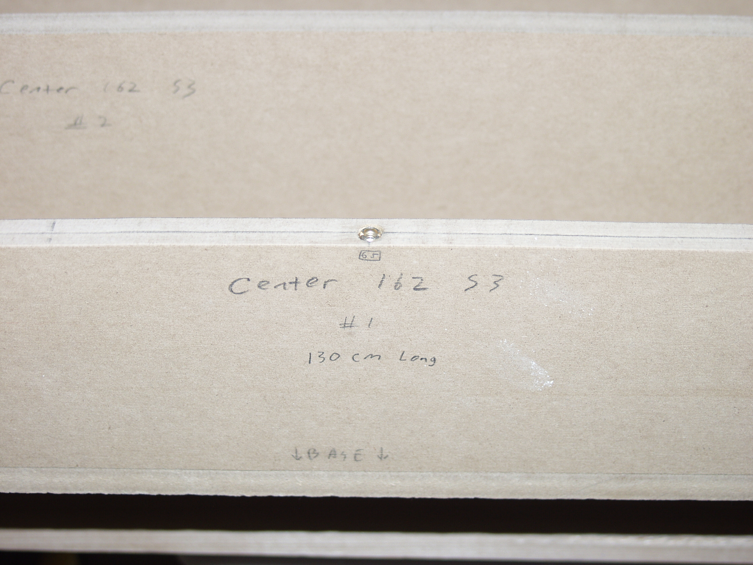
assets/images/Vacuum_mold_4.jpg
