mikemag/MonkeyWiki/assets/images/Vacuum_mold_5.jpg

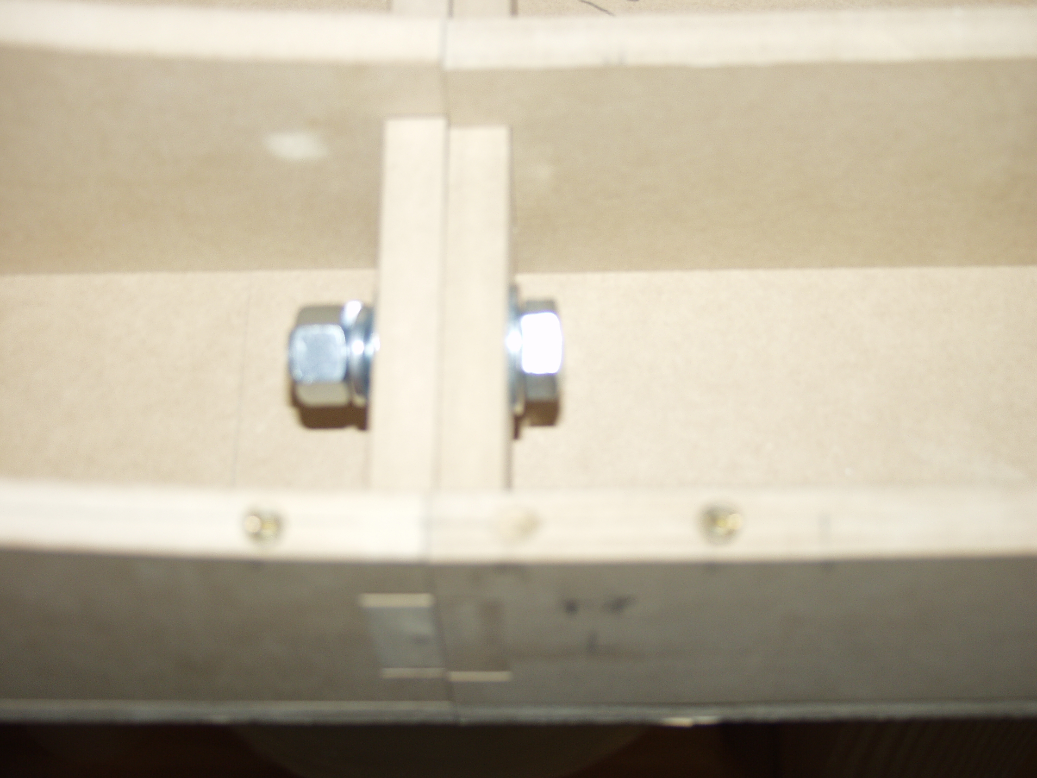
assets/images/Vacuum_mold_5.jpg
