mikemag/MonkeyWiki/assets/images/Vacuum_mold_6.jpg

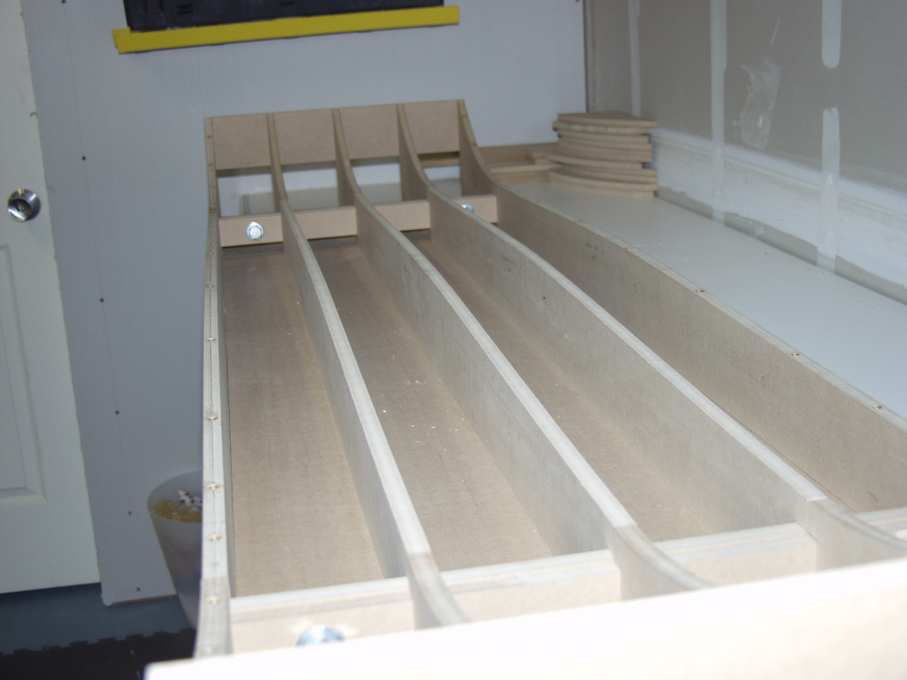
assets/images/Vacuum_mold_6.jpg
