mikemag/MonkeyWiki/assets/images/Veneer_Cards_1.jpg

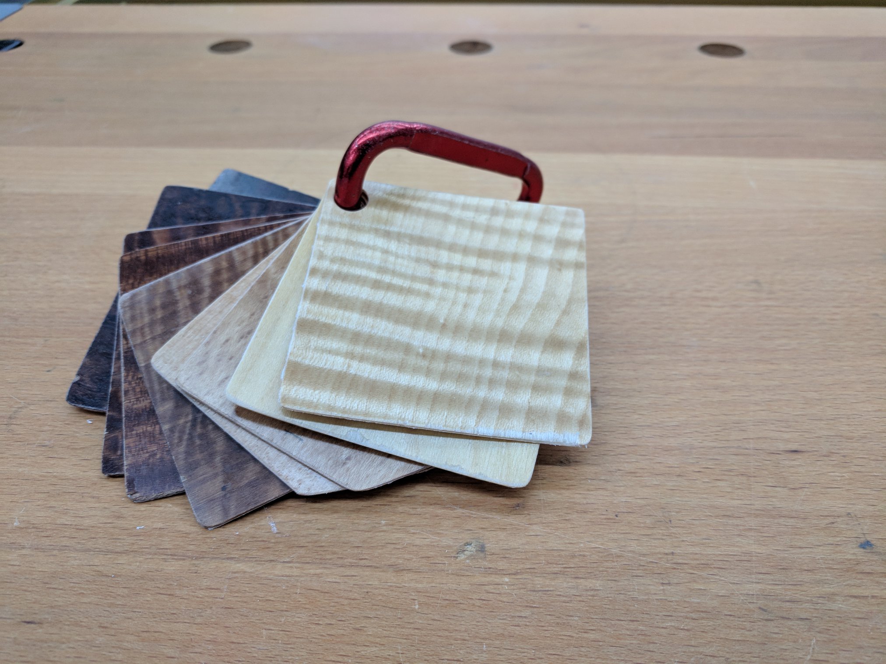
assets/images/Veneer_Cards_1.jpg
