mikemag/MonkeyWiki/assets/images/Veneer_Cards_2.jpg

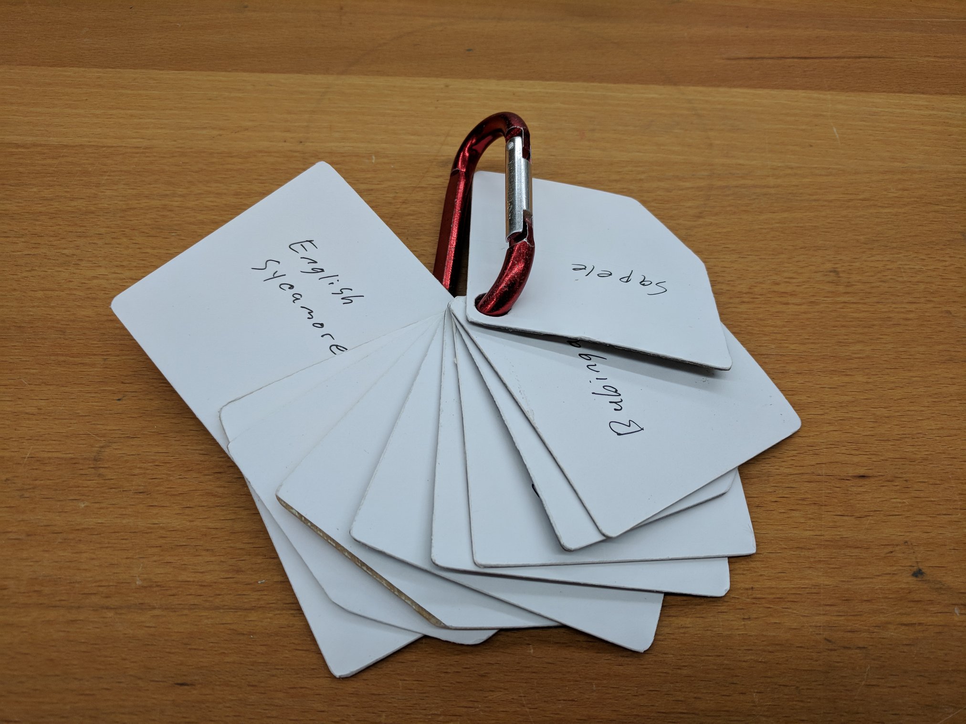
assets/images/Veneer_Cards_2.jpg
