mikemag/MonkeyWiki/assets/images/Veneer_Cards_3.jpg

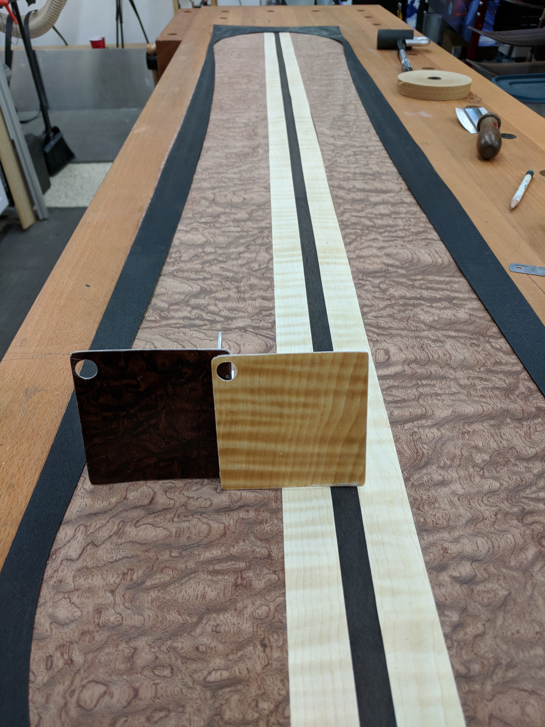
assets/images/Veneer_Cards_3.jpg
