mikemag/MonkeyWiki/assets/images/Veneer_Finishing1.JPG

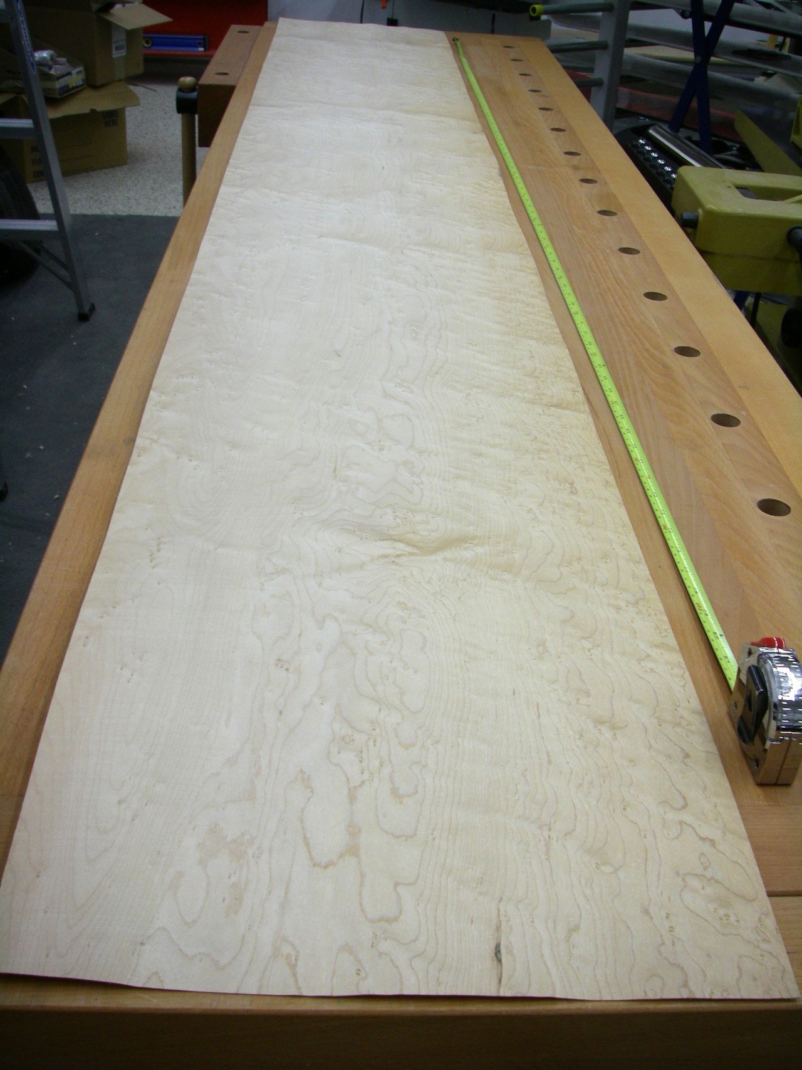
assets/images/Veneer_Finishing1.JPG
