mikemag/MonkeyWiki/assets/images/Veneer_Finishing2.JPG

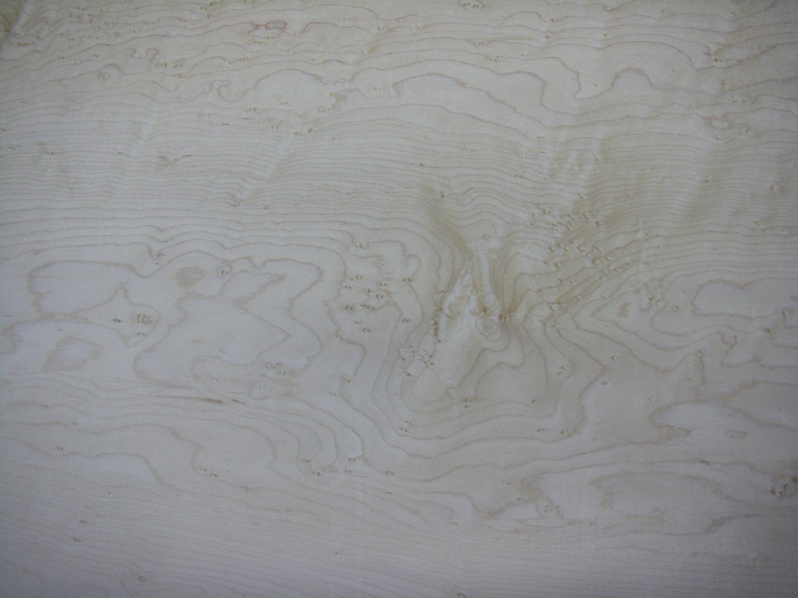
assets/images/Veneer_Finishing2.JPG
