mikemag/MonkeyWiki/assets/images/Veneer_Finishing3.JPG

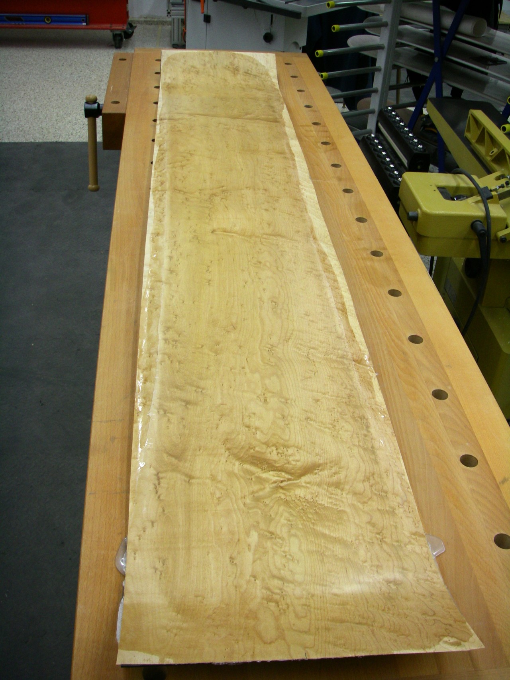
assets/images/Veneer_Finishing3.JPG
