mikemag/MonkeyWiki/assets/images/Veneer_Finishing4.JPG

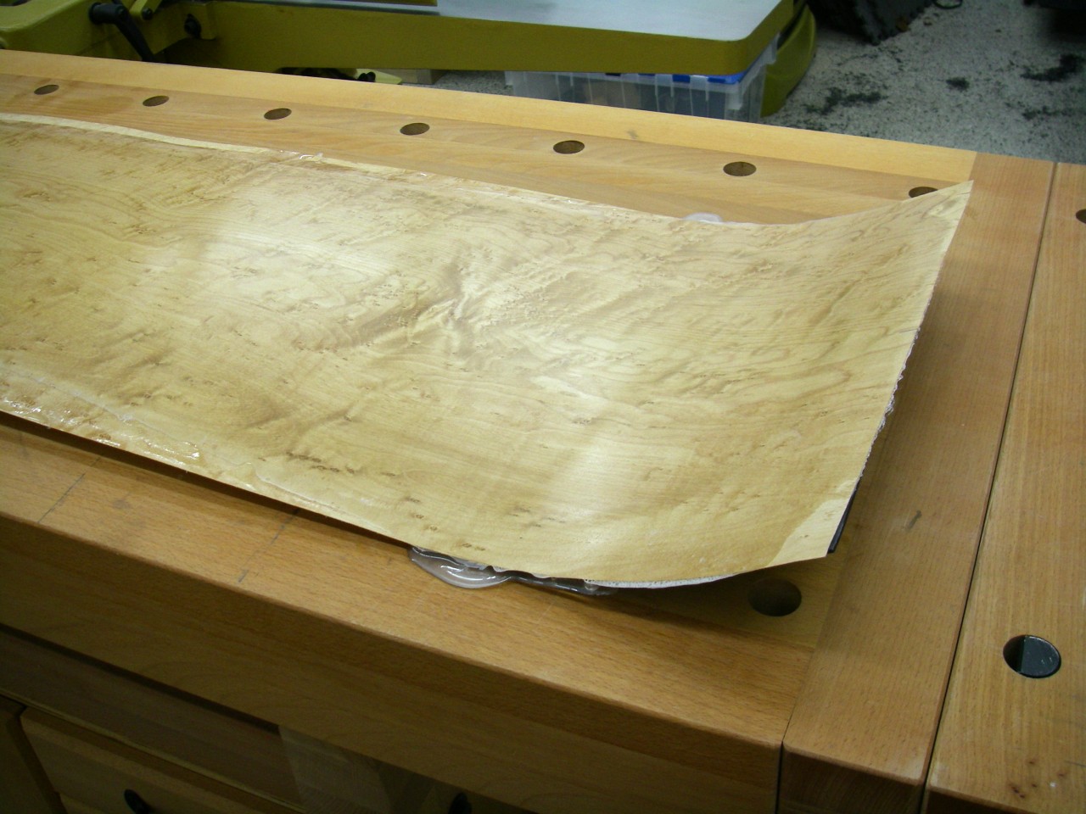
assets/images/Veneer_Finishing4.JPG
