mikemag/MonkeyWiki/assets/images/Veneer_Finishing5.JPG

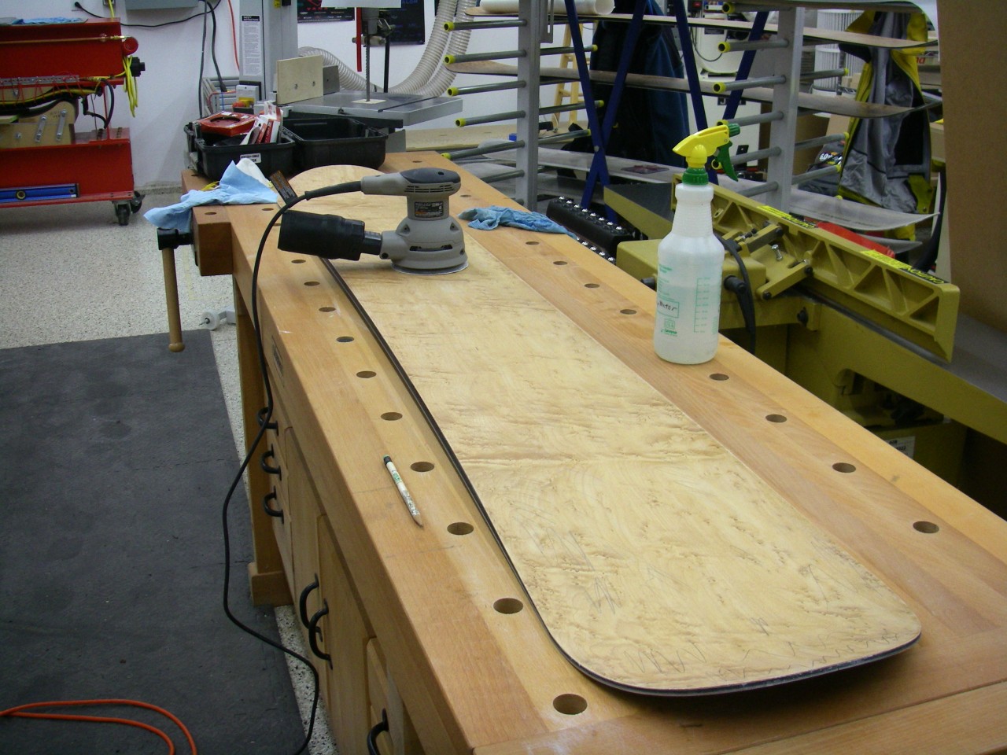
assets/images/Veneer_Finishing5.JPG
