mikemag/MonkeyWiki/assets/images/Veneer_Finishing6.JPG

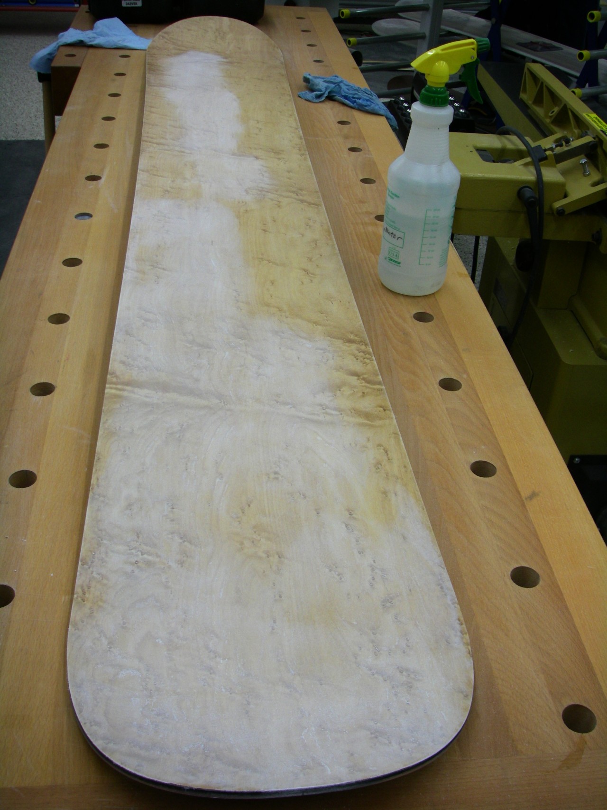
assets/images/Veneer_Finishing6.JPG
