mikemag/MonkeyWiki/assets/images/Veneer_Finishing7.JPG

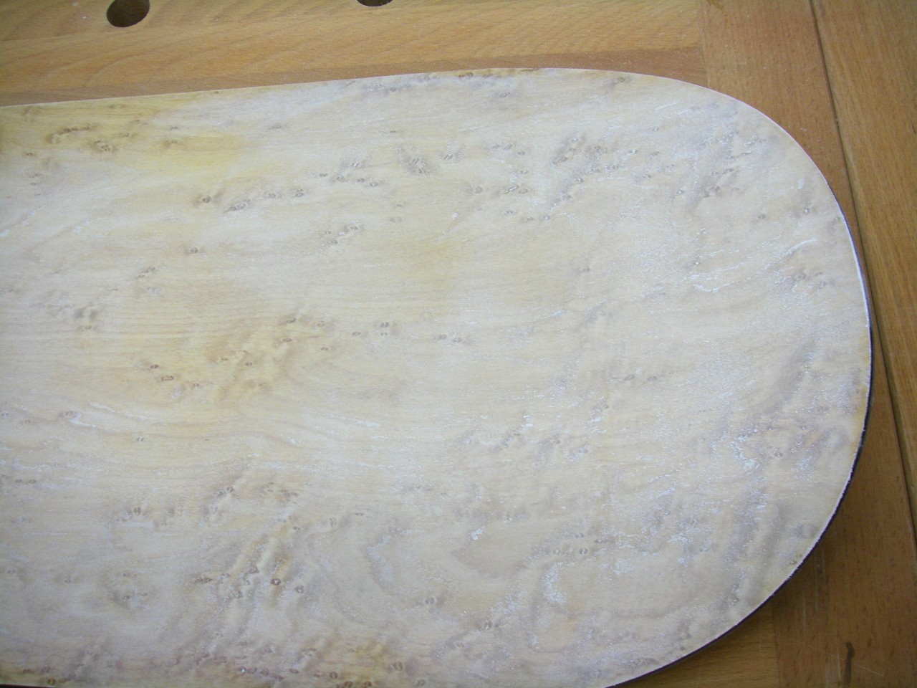
assets/images/Veneer_Finishing7.JPG
