mikemag/MonkeyWiki/assets/images/Veneer_Finishing8.JPG

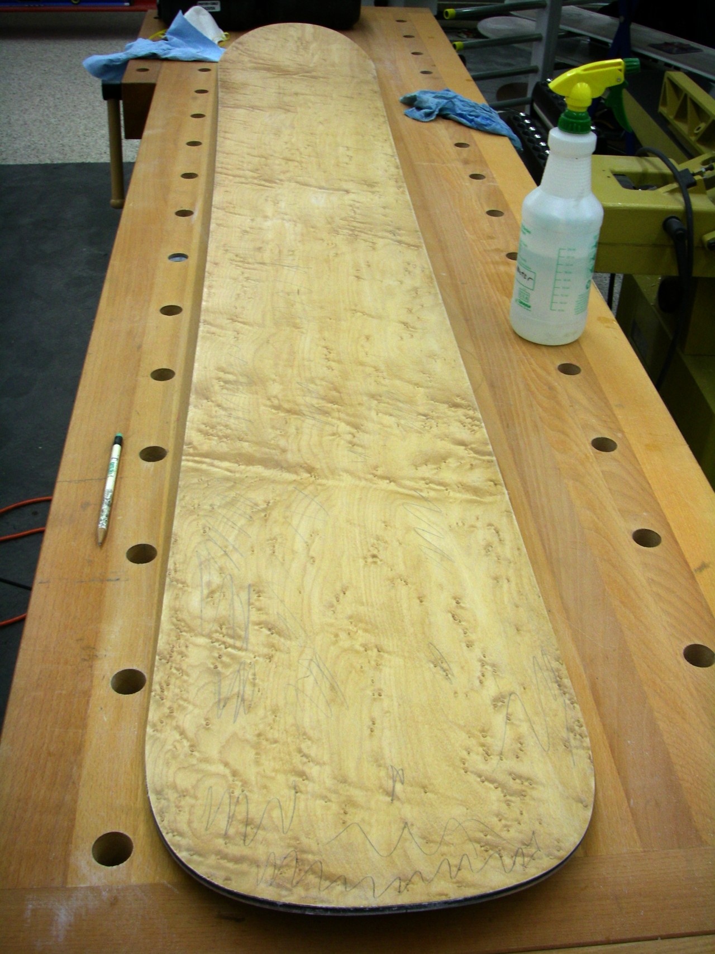
assets/images/Veneer_Finishing8.JPG
