mikemag/MonkeyWiki/assets/images/Veneer_Finishing9.JPG

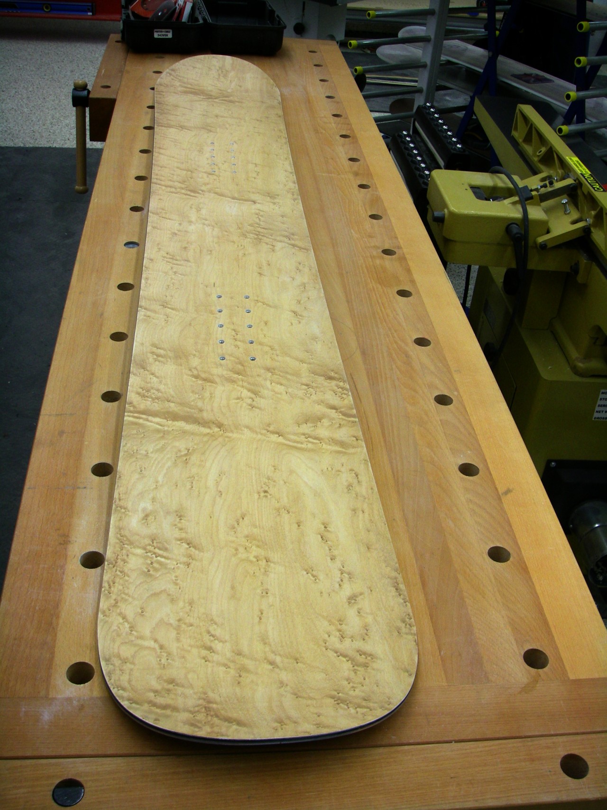
assets/images/Veneer_Finishing9.JPG
