mikemag/MonkeyWiki/assets/images/Veneer_Finishing10.JPG

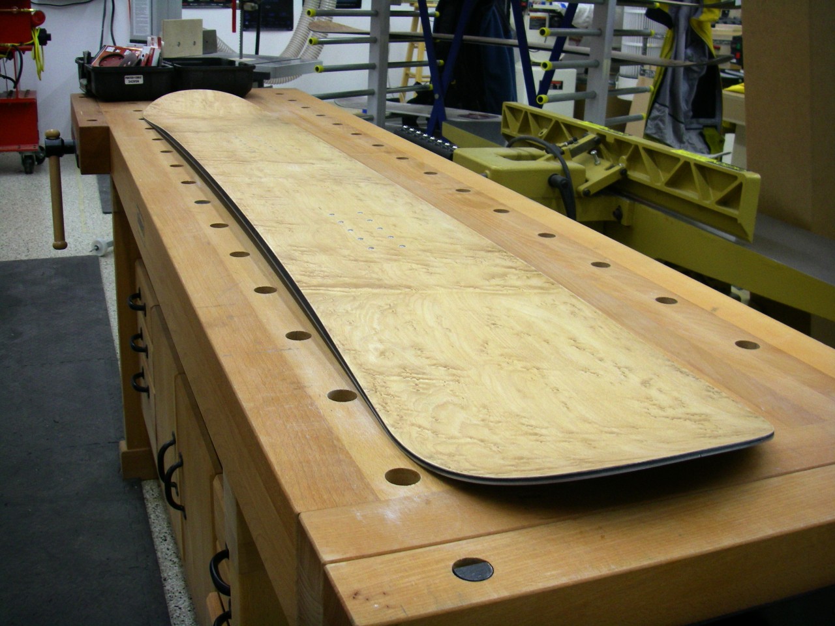
assets/images/Veneer_Finishing10.JPG
