mikemag/MonkeyWiki/assets/images/Veneer_Finishing11.JPG

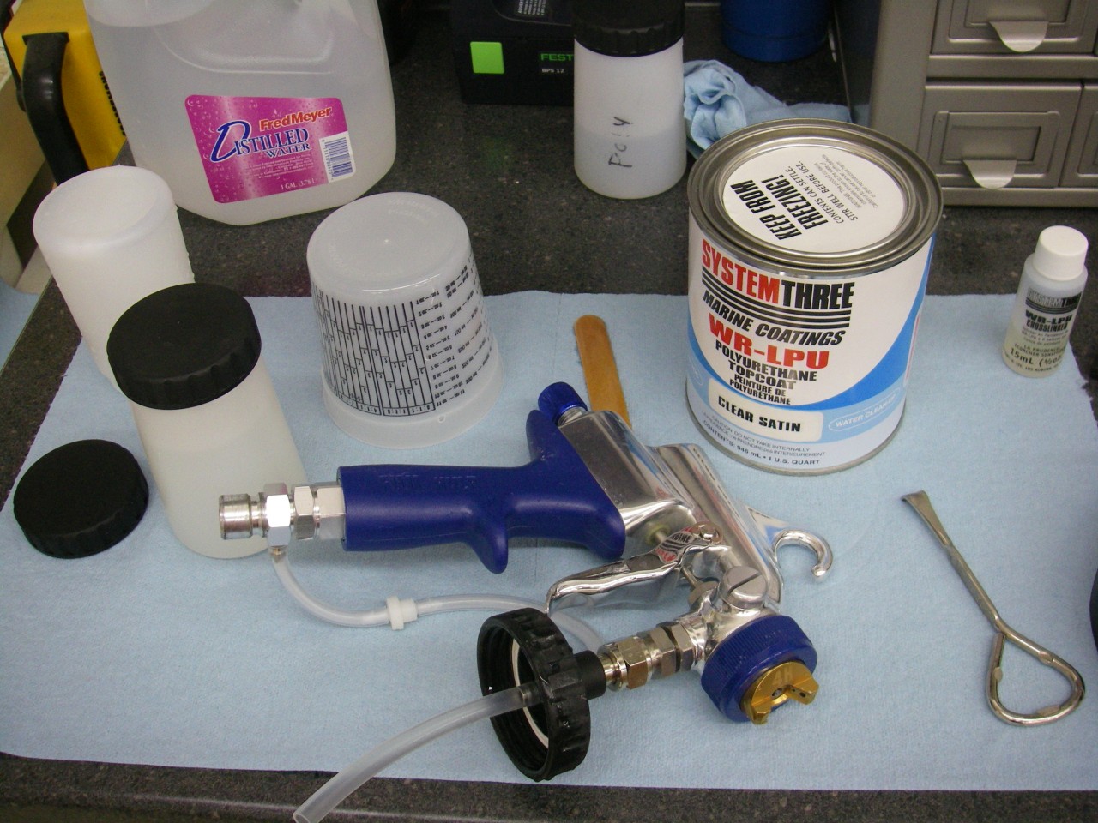
assets/images/Veneer_Finishing11.JPG
