mikemag/MonkeyWiki/assets/images/Veneer_Finishing12.JPG

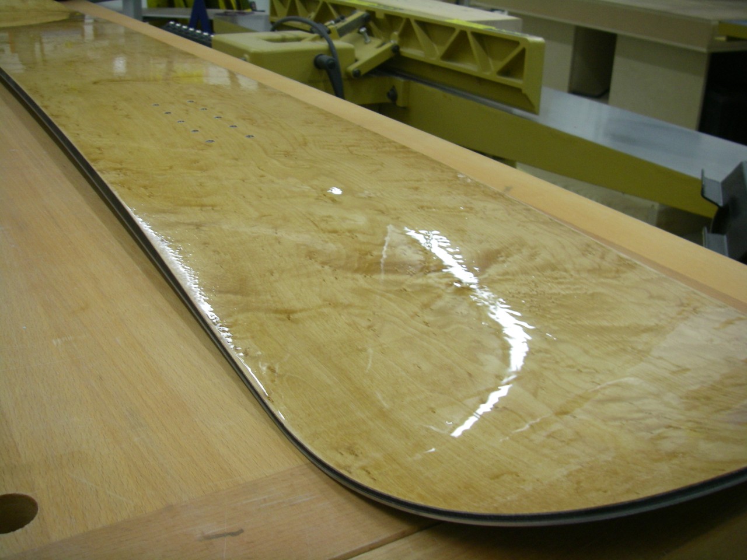
assets/images/Veneer_Finishing12.JPG
