mikemag/MonkeyWiki/assets/images/Veneer_Finishing13.JPG

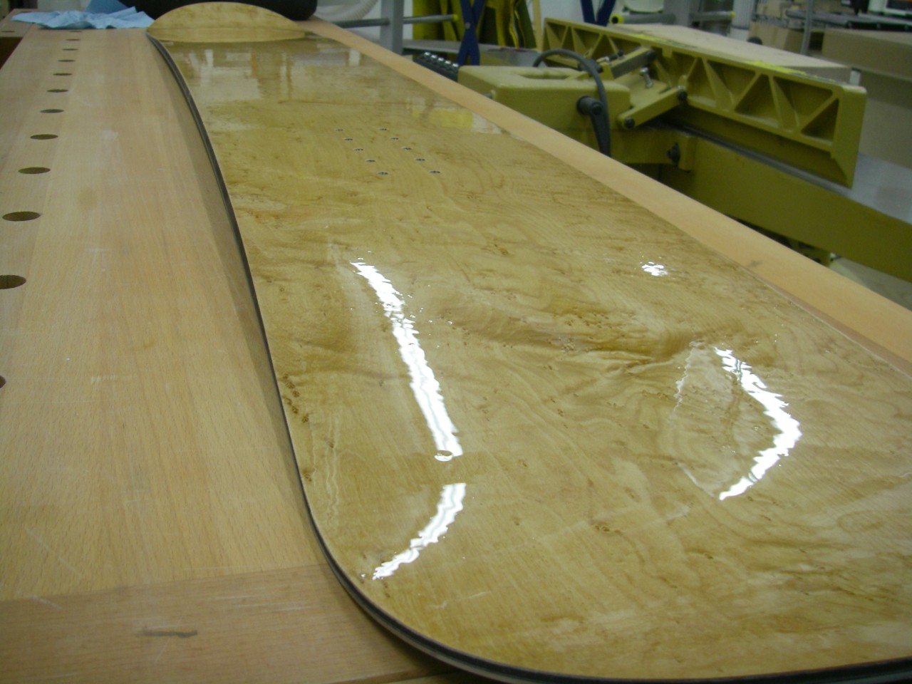
assets/images/Veneer_Finishing13.JPG
