mikemag/MonkeyWiki/assets/images/Veneer_Finishing14.JPG

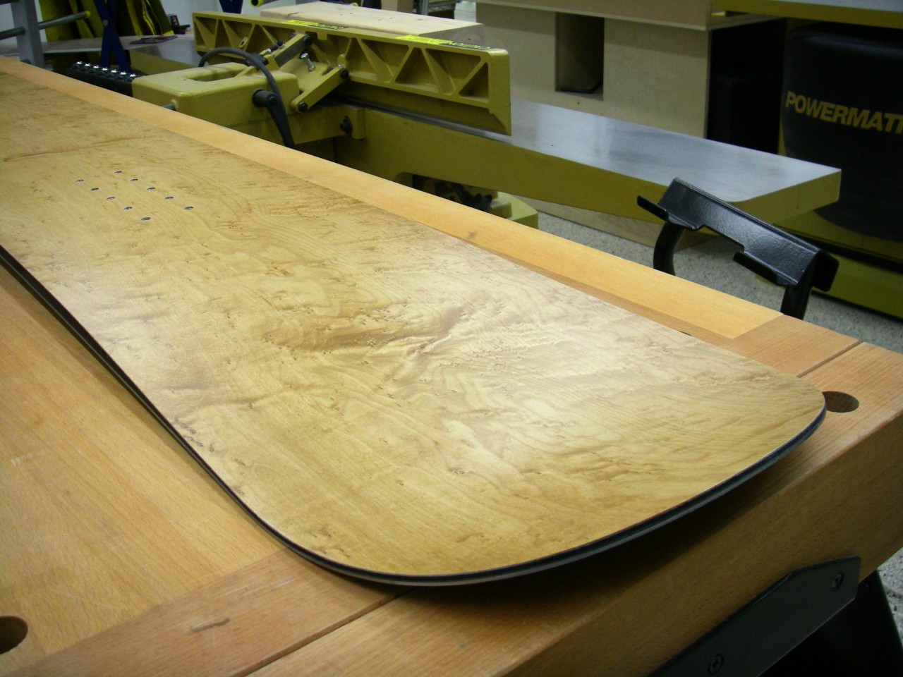
assets/images/Veneer_Finishing14.JPG
