mikemag/MonkeyWiki/assets/images/Veneer_Finishing15.JPG

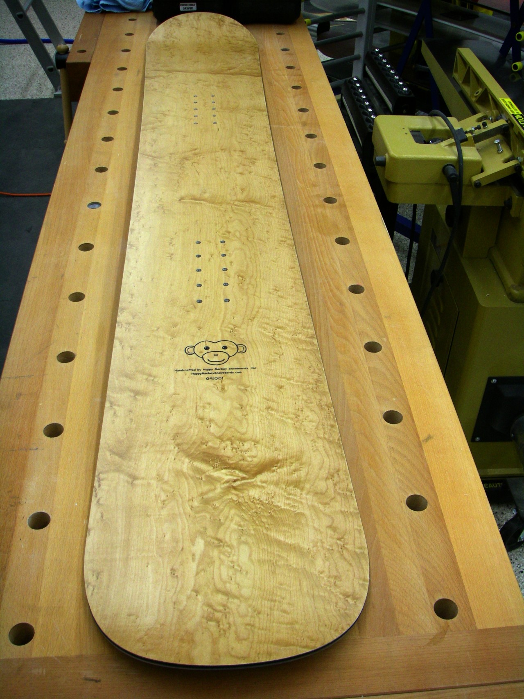
assets/images/Veneer_Finishing15.JPG
