mikemag/MonkeyWiki/assets/images/Veneer_Finishing16.JPG

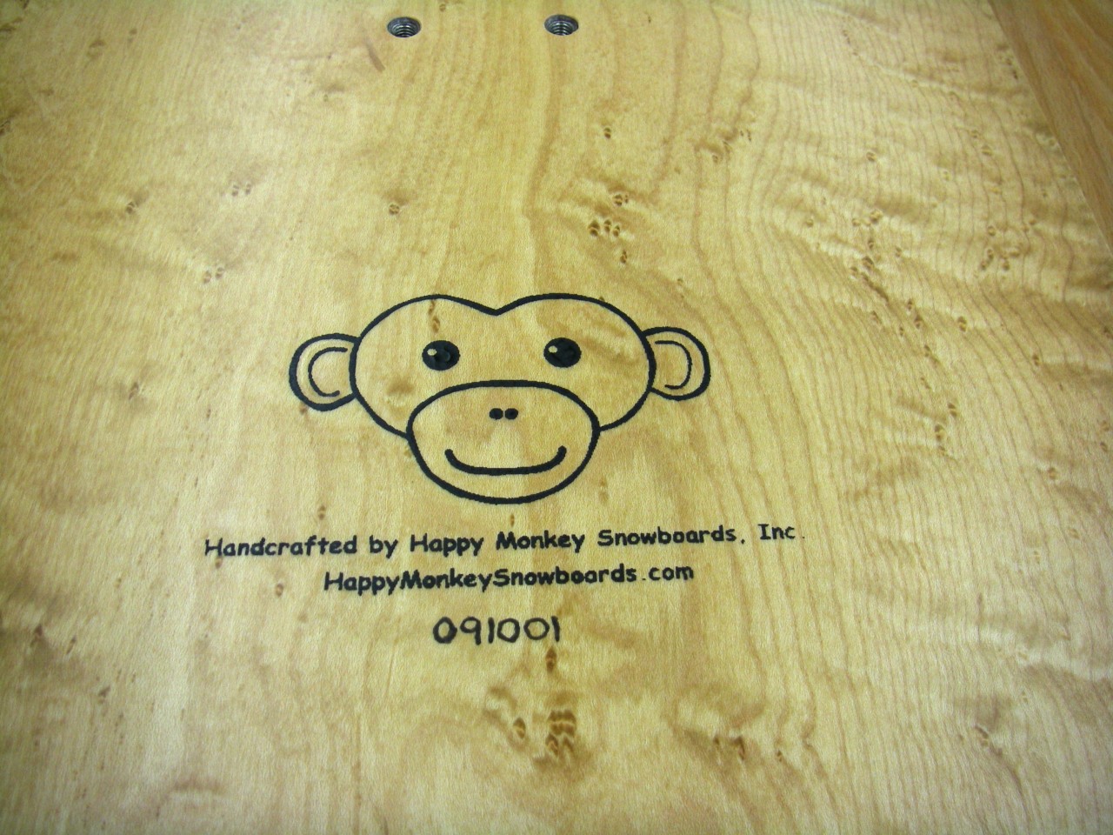
assets/images/Veneer_Finishing16.JPG
