mikemag/MonkeyWiki/assets/images/Veneer_Finishing_2_1.jpg

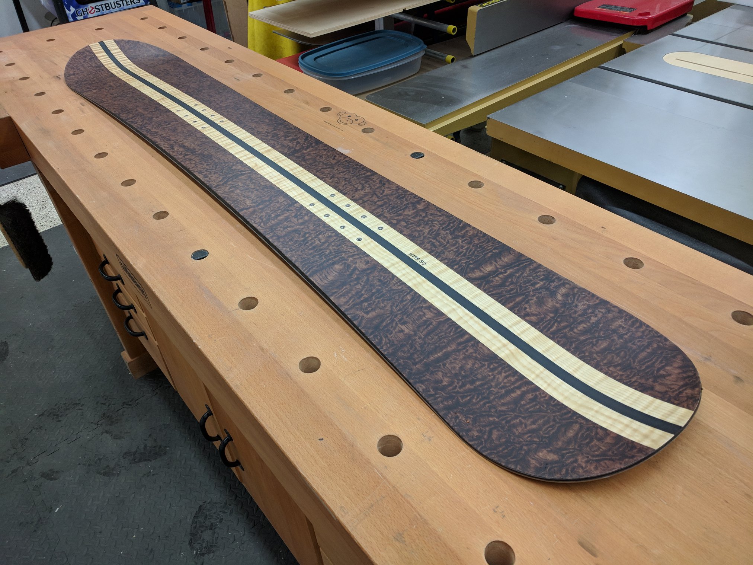
assets/images/Veneer_Finishing_2_1.jpg
