mikemag/MonkeyWiki/assets/images/Veneer_Finishing_2_2.jpg

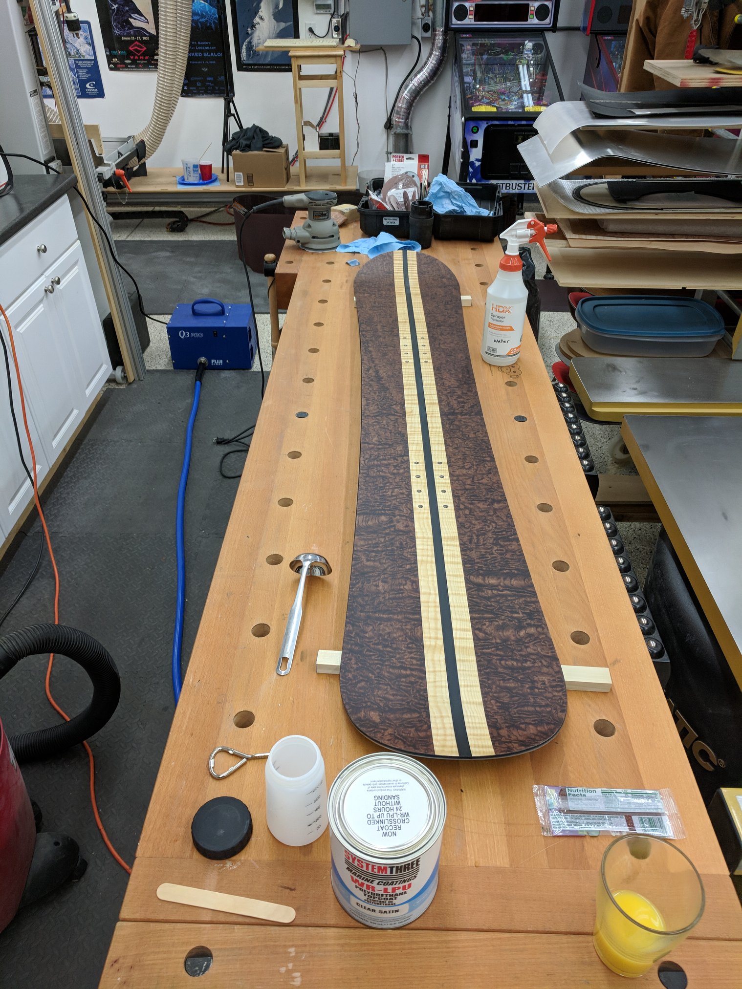
assets/images/Veneer_Finishing_2_2.jpg
