mikemag/MonkeyWiki/assets/images/Veneer_Finishing_2_3.jpg

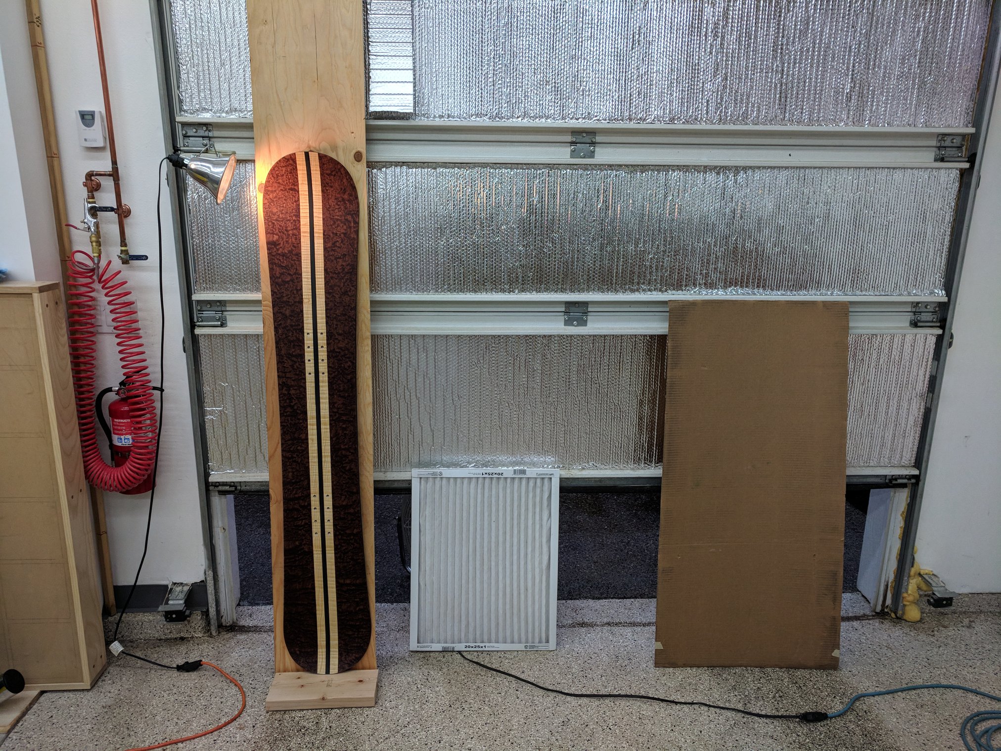
assets/images/Veneer_Finishing_2_3.jpg
