mikemag/MonkeyWiki/assets/images/Veneer_Finishing_2_4.jpg

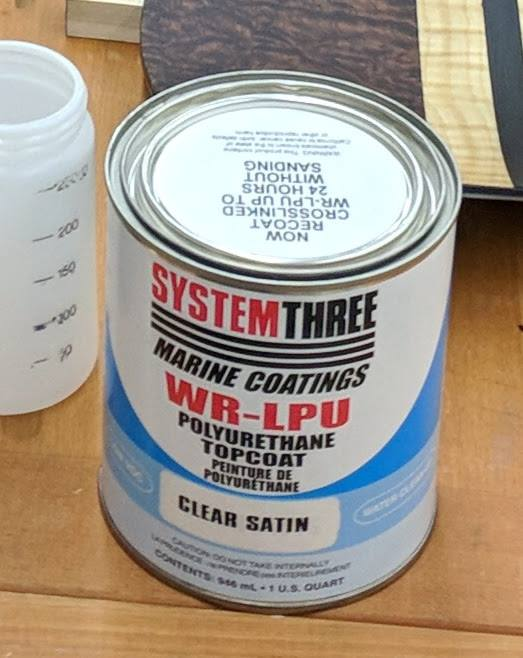
assets/images/Veneer_Finishing_2_4.jpg
