mikemag/MonkeyWiki/assets/images/Veneer_Finishing_2_5.jpg

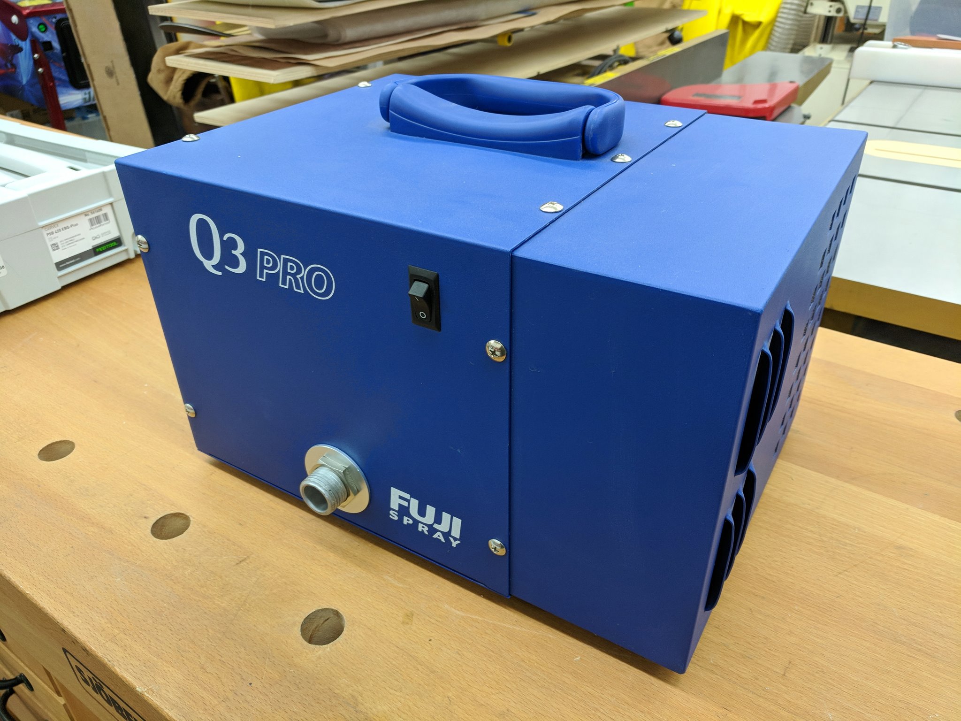
assets/images/Veneer_Finishing_2_5.jpg
