mikemag/MonkeyWiki/assets/images/Veneer_Finishing_2_6.jpg

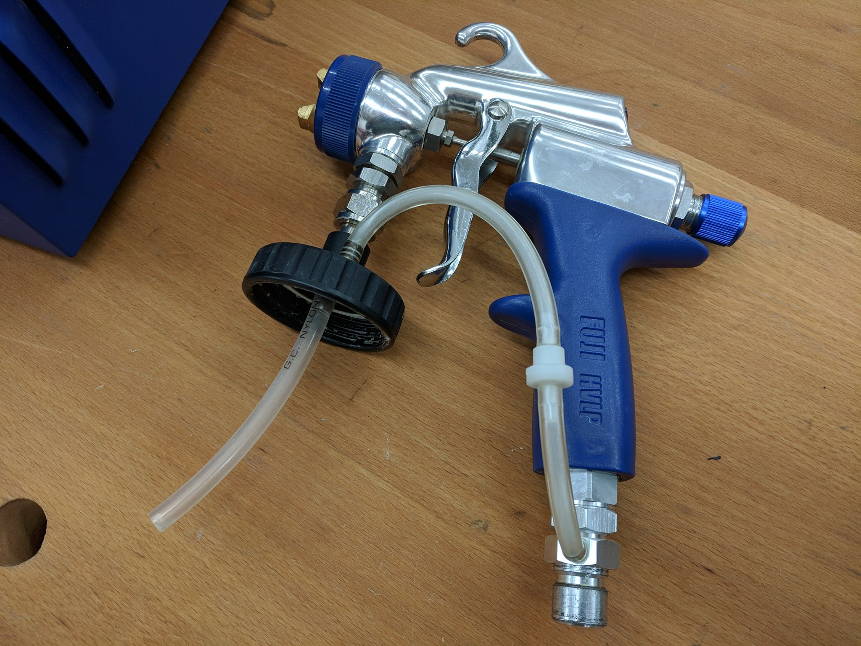
assets/images/Veneer_Finishing_2_6.jpg
