mikemag/MonkeyWiki/assets/images/Veneer_Finishing_2_7.jpg

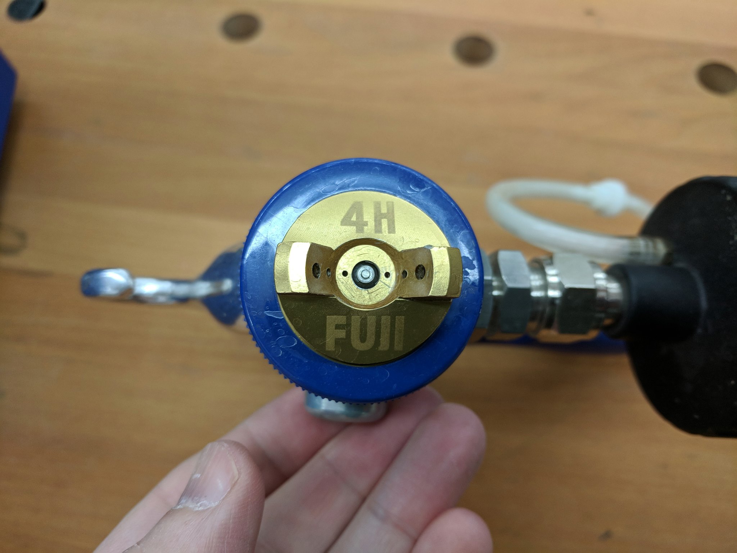
assets/images/Veneer_Finishing_2_7.jpg
