mikemag/MonkeyWiki/assets/images/Veneer_top_1.jpg

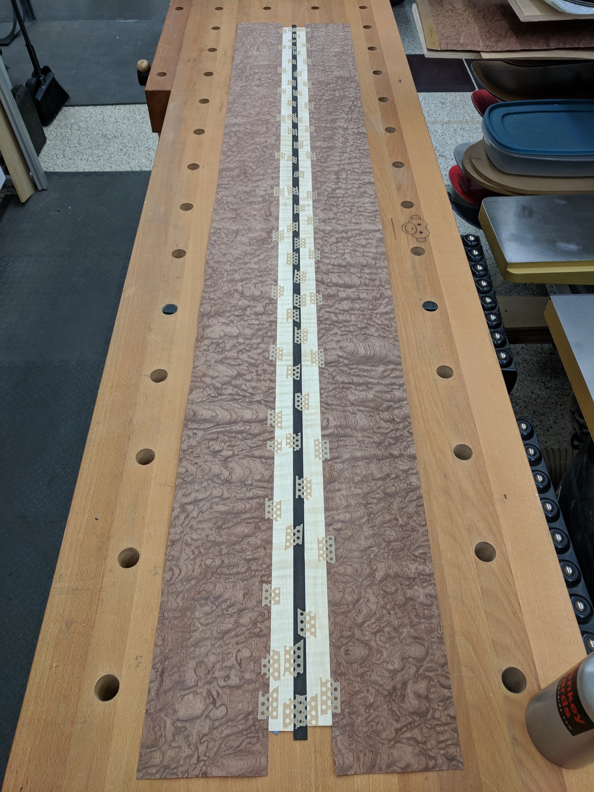
assets/images/Veneer_top_1.jpg
