mikemag/MonkeyWiki/assets/images/Veneer_Top_2.jpg

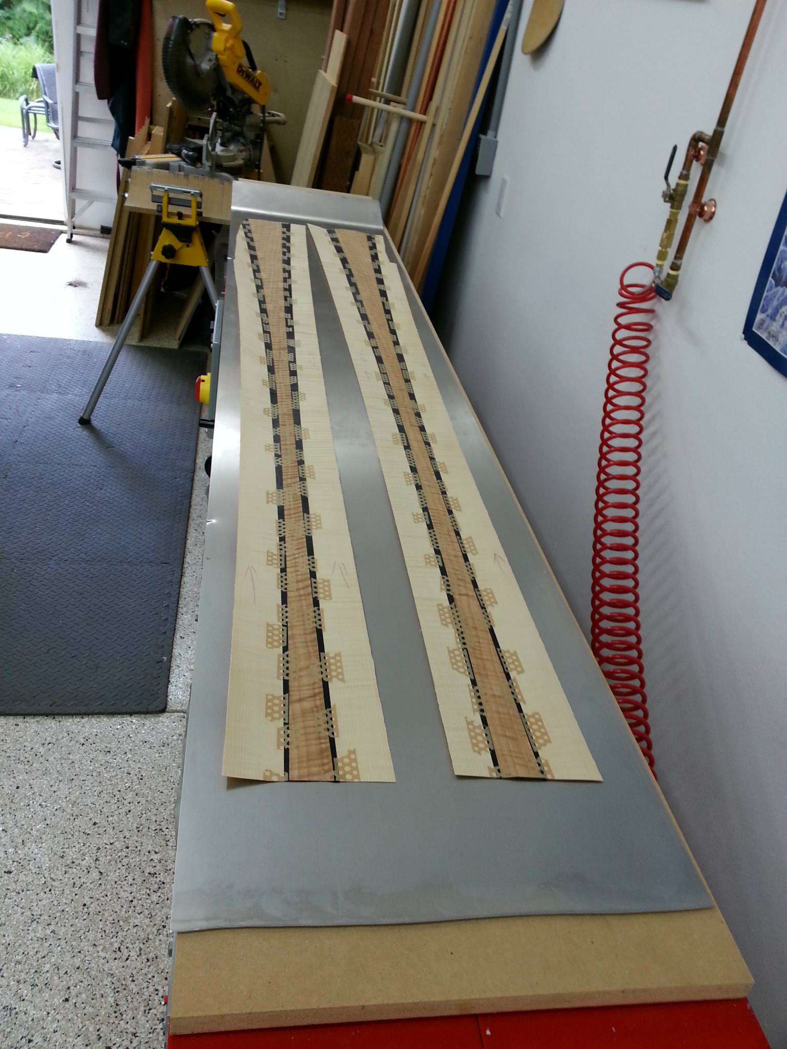
assets/images/Veneer_Top_2.jpg
