mikemag/MonkeyWiki/assets/images/Veneer_Top_3.jpg

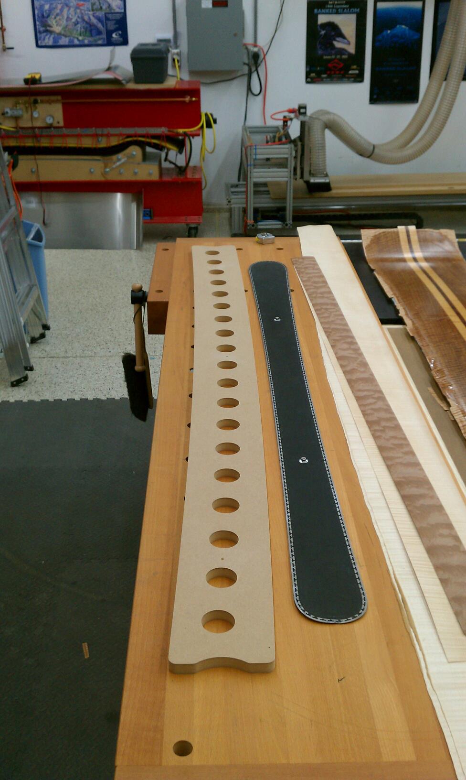
assets/images/Veneer_Top_3.jpg
