mikemag/MonkeyWiki/assets/images/Veneer_Top_4.jpg

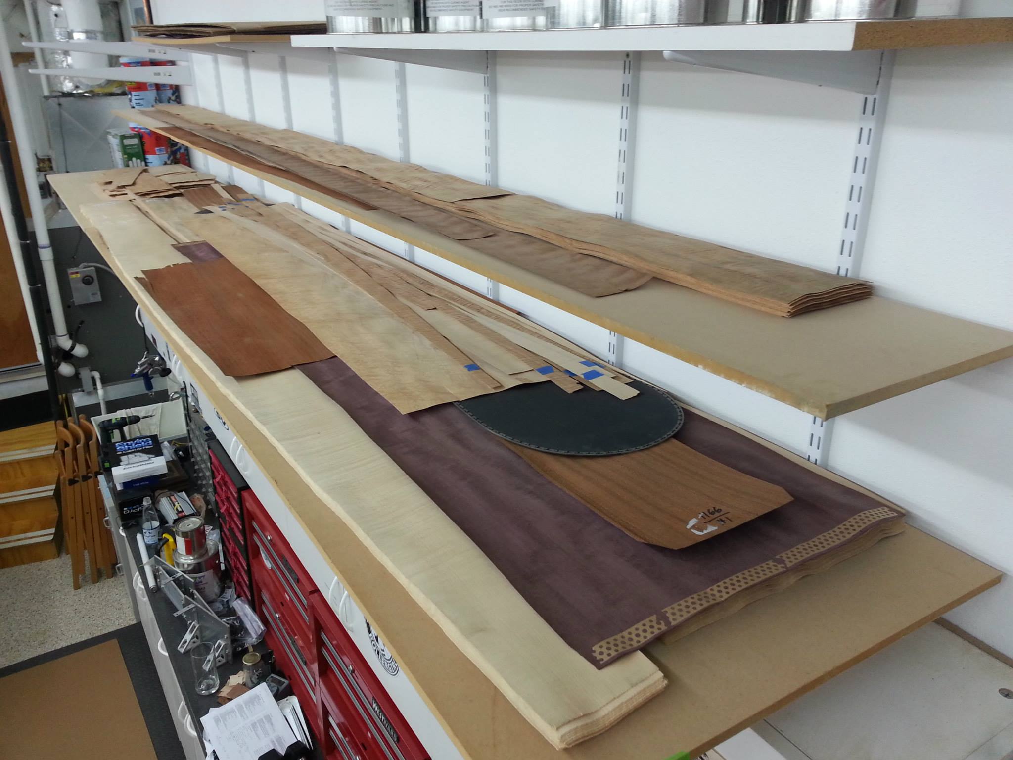
assets/images/Veneer_Top_4.jpg
