mikemag/MonkeyWiki/assets/images/Veneer_Top_5.jpg

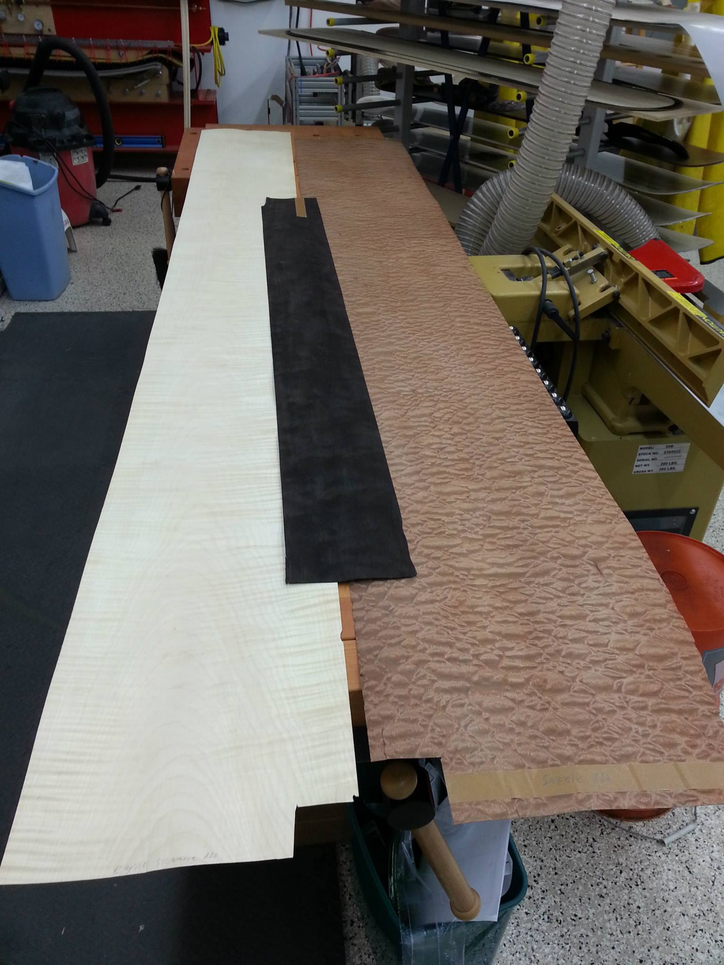
assets/images/Veneer_Top_5.jpg
