mikemag/MonkeyWiki/assets/images/Veneer_Top_6.jpg

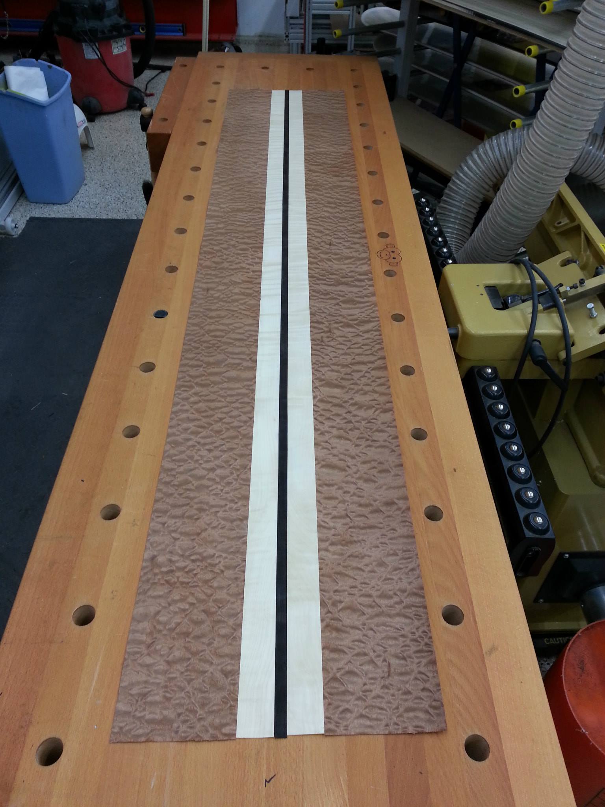
assets/images/Veneer_Top_6.jpg
