mikemag/MonkeyWiki/assets/images/Veneer_Top_7.jpg

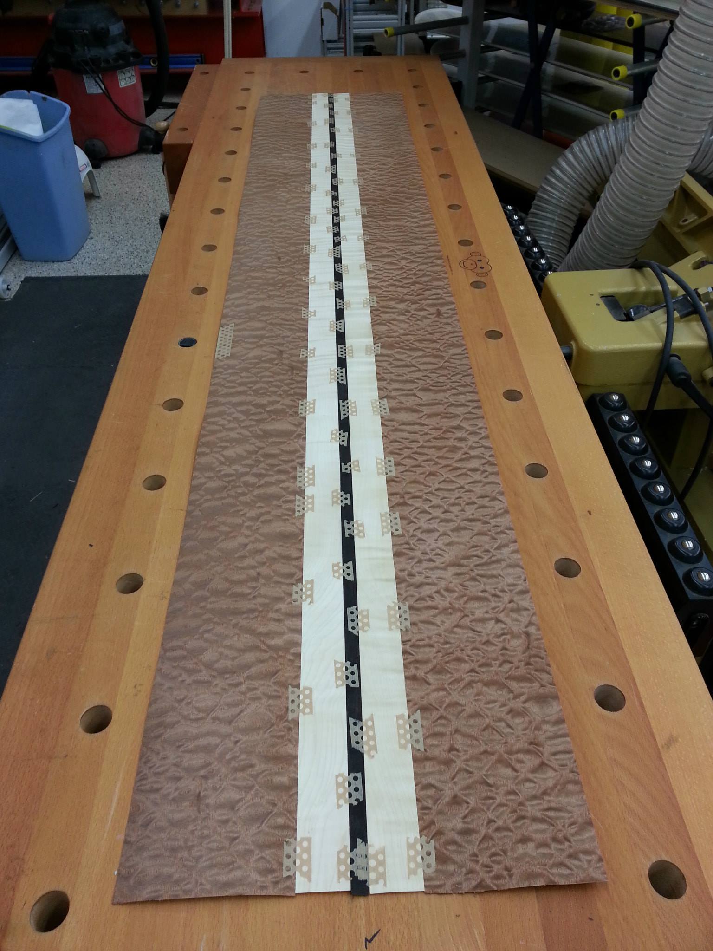
assets/images/Veneer_Top_7.jpg
