mikemag/MonkeyWiki/assets/images/Veneer_Top_8.jpg

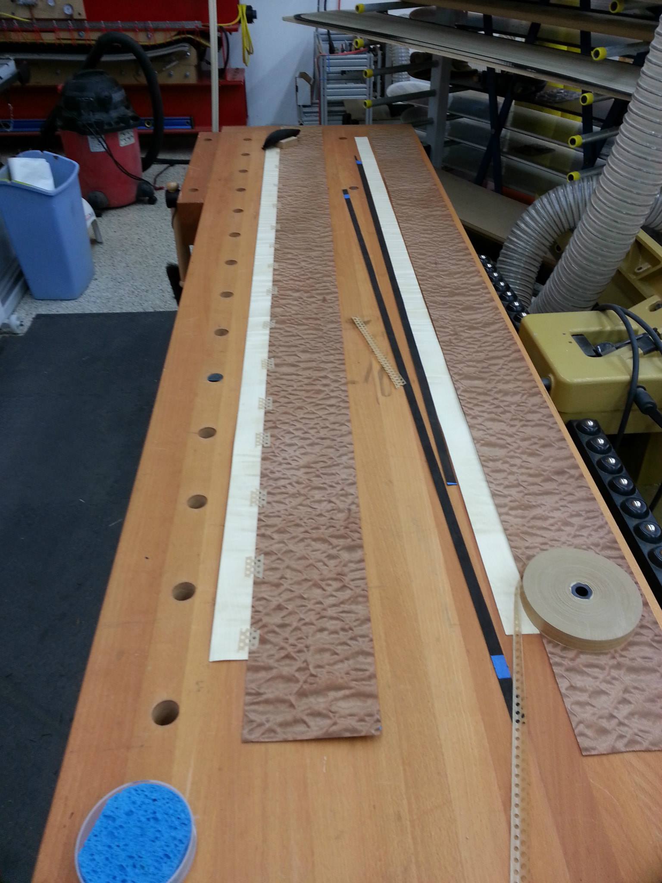
assets/images/Veneer_Top_8.jpg
