mikemag/MonkeyWiki/assets/images/Veneer_Top_9.jpg

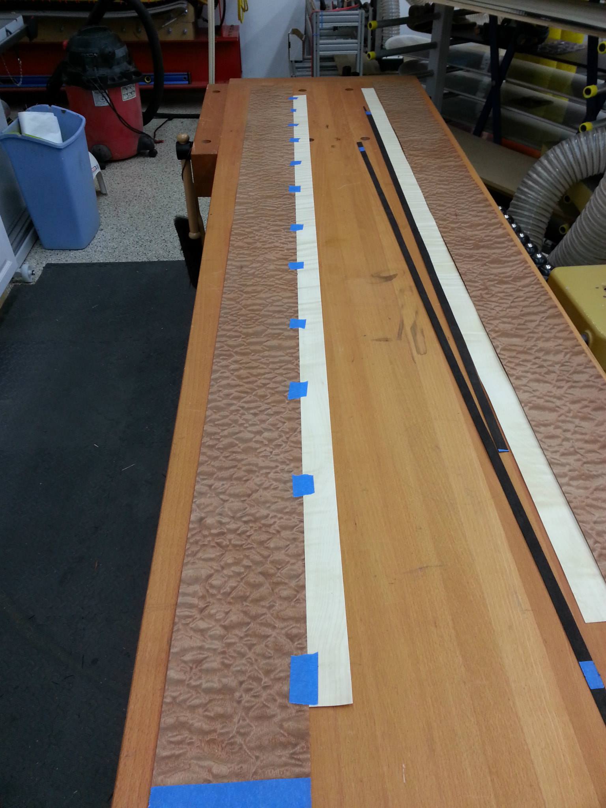
assets/images/Veneer_Top_9.jpg
