mikemag/MonkeyWiki/assets/images/Veneer_Top_10.jpg

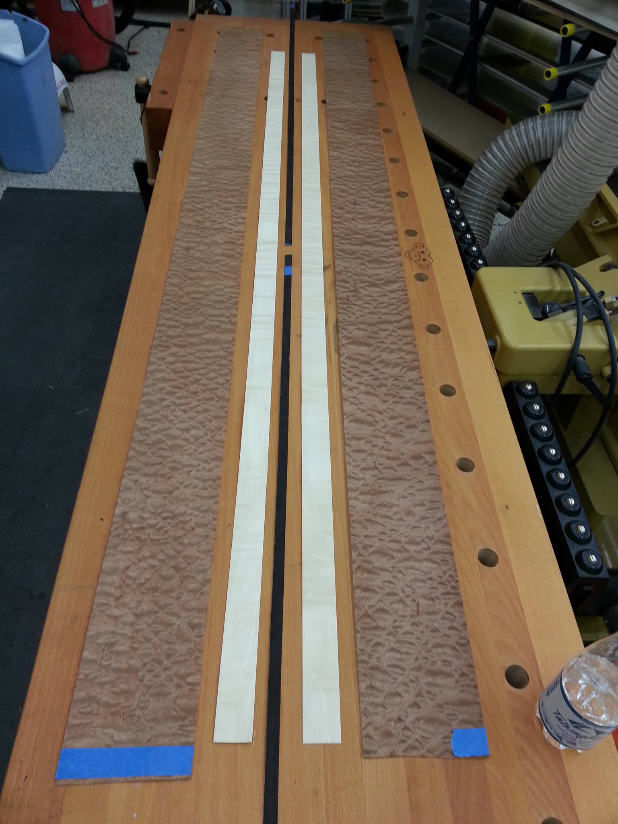
assets/images/Veneer_Top_10.jpg
