mikemag/MonkeyWiki/assets/images/Veneer_Top_11.jpg

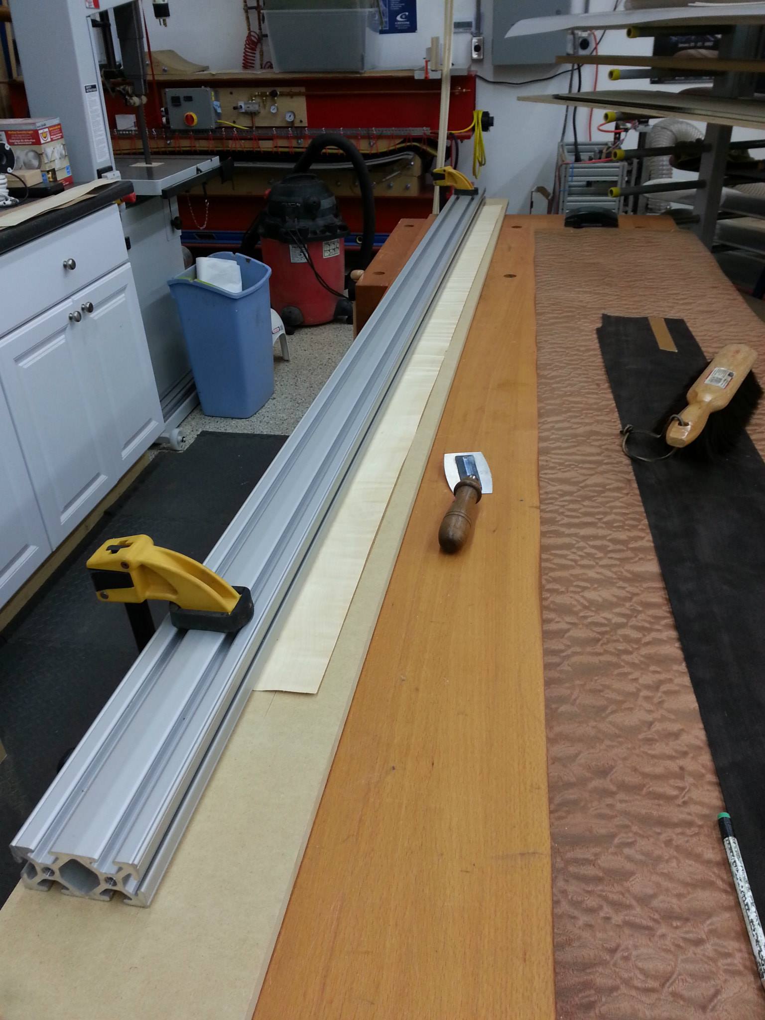
assets/images/Veneer_Top_11.jpg
