mikemag/MonkeyWiki/content/zh-cn/MonkeyWiki/Construction/Core_blank_construction/Joining_the_halves_of_a_core_blank.md

---
dateFromWiki: "2019-04-10T02:51:16Z"
title: "拼接另外一半空白板芯"
gallery: true
aliases:
- /MonkeyWiki/Joining_the_halves_of_a_core_blank/zh-cn
translatedDate: "2019-04-10T02:51:16Z"
translator: "X z"
translatorPage: "/zh-cn/MonkeyWiki/X_z"
weight: 4
---
创建空白板的最后阶段是从 [切割芯坯]({{< ref "MonkeyWiki/Construction/Core_blank_construction/Slicing_a_stack.md" >}})中拼接一对匹配的切片，以形成大约14英寸(35.56cm)宽的空白板。（当然，如果你正在构建滑雪双板，那么你不需要执行此步骤，因为一个切片足够宽，足以用于单个滑雪双板！）空白板将与芯坯一样长，这将至少容纳一块180厘米长的板子。我每季都会制作一块芯坯，这样可以生产长达200厘米的木板，但这些木板的使用频率较低。坯料的厚度由切片的厚度决定，目标是至少0.400英寸(1.016cm)厚，以允许通过在形成最终板芯时所需的压刨的额外通过。

切片沿中心用一点聚氨酯胶连接，并用六或七个“4路”夹具夹紧。这些切片保持切片从上到下完美对齐，同时在切片之间提供出色的压力。你可能会注意到板芯和夹子之间的图片中有一些垫片。这些是为了弥补大多数芯坯比夹具设计的更薄的事实。这是一个容易解决的问题，用几条1/4英寸(0.635cm)的硬纸板打蜡或用胶带粘一点，以防止胶水粘连。

我发现有时切片的边缘并不是完全笔直的，因为毕竟很难让这么重的长芯坯的顶部和底部完全平坦。我通常通过将我的切片夹在一起并在几个光通道中运行连接穿过平刨来解决这个问题。你也可以用台剧和一个夹具直接撕开它们。

当毛坯从夹子中出来时，它的两侧都有一层漂亮的干胶，还有一些从夹子上涂抹。这只是用手动刮刀刮掉的。发泡的聚合胶不是很坚固，很容易脱落，留下一个板芯坯料，最终成为板芯。
{{< gallery  caption="拼接另外一半空白板芯" >}}
{{< gallery-item src="images/CoreBlank_SliceJoin1.JPG" caption="Halves of a core blank coming together." >}}
{{< gallery-item src="images/CoreBlank_SliceJoin2.JPG" caption="Joining halves of a core blank. You can clearly see the glue squeezeout and the spacers for the clamps." >}}
{{< gallery-item src="images/CoreBlank_SliceJoin3.JPG" caption="A core blank fresh out of the clamps. The excess glue needs to be scraped off using the hand-held scraper visible in the distance." >}}
{{< /gallery >}}

## 参阅

- [芯坯概述]({{< ref "MonkeyWiki/Construction/Core_blank_construction/Core_blank_overview.md" >}})
- [木材选择，干燥和准备]({{< ref "MonkeyWiki/Materials/Wood_selection__drying__and_prep.md" >}})
- [制作芯坯]({{< ref "MonkeyWiki/Construction/Core_blank_construction/Building_a_stack.md" >}})
- [切割芯坯]({{< ref "MonkeyWiki/Construction/Core_blank_construction/Slicing_a_stack.md" >}})
- [四向夹具]({{< ref "MonkeyWiki/Equipment/Small_tools/Four-way_Clamps.md" >}})
