mikemag/MonkeyWiki/content/zh-cn/MonkeyWiki/Equipment/Snowboard_press/Monkey_Press_Construction.md

---
dateFromWiki: "2019-04-17T09:26:41Z"
title: "Monkey 压力机制造"
gallery: true
aliases:
- /MonkeyWiki/Monkey_Press_Construction/zh-cn
translatedDate: "2019-04-17T09:26:41Z"
translator: "X z"
translatorPage: "/zh-cn/MonkeyWiki/X_z"
---
这是我的气动压力机的详细概述，如果适用，还有部件号。 

{{< img src="images/Press_Full.JPG" caption="_气动压力机 at Happy Monkey Snowboards, Inc._" >}}压力腔为92英寸长×16英寸宽×12英寸高(约233.64长*40.64宽*30.48cm高)。总压重约为2,000磅(907kg)，包括模具。根据滑雪板表面积，有两个5英寸(约12.7cm)消防软管，工作在50-80psi(压力单位)之间。有两个硅热毯，一个在顶部，一个在底部，总共3.5W/in^2。硅热毯尺寸为14英寸x85英寸(35.56*215.9cm)，240V，总拉伸为17.35A。将板从70华氏(21℃)加热到175华氏(79.4℃)需要大约10分钟。

模具可根据不同的有效边刃长度和不同的板头/板尾长度和上升进行调节。我倾向于坚持使用单个camber块，在各种形状和长度范围内为我们带来了良好的效果。我有越来越多的板头/板尾选择。如果特定构造需要新的块形状，那么我将设计一个新的块形状并在CNC机器上切割它。

## 钢架

该压力机设计用于轻松处理长达200厘米的滑雪板。它由钢制W12x40工字钢制成，高12英寸(30.48cm)，宽8英寸(20.32cm)，长9英尺(2.7432m)，重40磅/英尺。有两个横梁 - 顶梁由两个16英寸长的横梁支撑，侧面为12英寸。这使得压力机中的工字梁材料的总重量为1,547磅。

===偏转===

{{< img src="images/IMG_20190322_185635.jpg" caption="_测量偏差_" >}}我使用了一种非常普通的压力机设计，这种设计经常受到关注，它在压力下会有多大的偏差。 

简短的回答: 1.1938mm (0.047") in the center @ 50psi. 

这基本上是由于该压力机的偏斜导致你在滑雪板上的弯度损失多少。我认为这对于设计的简单性来说是一个可接受的权衡，无论是在结构还是操作方面，如果你关心它，很容易将其纳入你的模具设计中。我真的怀疑任何人实际上都在关心，因为在滑雪板的最终弯度与实际模具之间总是存在一些差异。

使用设置在底板和顶部凸缘之间的底梁中心的刻度盘指示器测量挠度。偏转0.047“@ 50psi，0.0405”@ 40psi和0.033“@ 30psi。在测量之前用法兰检查卡尺的方形，并且所有测量都是可重复的。

我还从顶部进行了测量，带有一个安装座，用于旋入压力机后面墙壁的百分表。测量中心和端部导致中心偏差在距底部测量值的0.003“范围内。端部的测量结果使我能够看到整个上部的升力，这是在订单上0.45毫米（0.0179寸）。

## 框架组装

{{< img src="images/Press_Bolts.JPG" caption="_螺栓将框架固定在一起_" >}}压力机装配有1/2"8级螺母和螺栓。对于任何人来说，这是一种简单，经济的方式，可以将这样的压力机放在一起并获得可靠的连接。焊接是另一种选择，但是需要非常熟练的焊工来生产适当的接头以承受软管产生的压力。如果你是一个好的焊工，或者知道一个，那么这是一个合理的方法，而且钻孔要少得多。但是如果你不是，那么一个周末的磁力钻（不到100美元，包括你将要咀嚼的钻头）和35美元的螺母，螺栓和垫圈的租赁是可靠的方法。你最终会得到一台分开的压力机，根据你的工作空间以及是否需要移动压力机，这可能很有用。 

零件号：[91257A748](http://www.mcmaster.com/#91257A748), [94895A825](http://www.mcmaster.com/#94895A825), 和 [98023A033](http://www.mcmaster.com/#98023A033).
 
我把压力机放在脚轮上，虽然最后的重量一直在2000磅左右，但它很容易移动。部件号[22955T42](http://www.mcmaster.com/#22955T42)和[22955T36](http://www.mcmaster.com/#22955T36)。

我将框架螺栓拧到40英尺磅，以确保在压力机加压后所有螺栓都处于相当大的张力下。没有什么科学的扭矩选择，只是使用普通的月牙扳手感觉相当紧张。唯一的目标是他们都是一样的。

## 气动

{{< img src="images/Press_AirControl.JPG" caption="_Monkey Press上的空气控制_" >}}从长远来看，在空气系统上花费的一点时间在简单性和可靠性方面都有所回报。系统中有一些焊接的铜管道，但这实际上只适用于长距离运行，而且它是完全可选的。其余部分由标准黄铜配件和一小块Teflon带组成。（提示：获得专为天然气应用而设计的黄色材料。它更厚一些，更容易密封。）
 
通过手动操作杆空气控制阀，4向，3位，闭合中心控制气囊到气囊的气流。部件号[3368K26](http://www.mcmaster.com/#3368K26)。它被连接起来，当杠杆位于中心时，没有空气流动。当杠杆位于右侧时，空气流入气囊，当杠杆流向气囊时，空气从气囊流出排气口。
 
排气装置采用简单的烧结青铜排气消声器进行消声，部件号为[4450K2](http://www.mcmaster.com/#4450K2)。这大约是2美元，完全值得保护你的听力。
 
使用简单的黄铜弹簧安全阀，系统的总压力限制在90psi，部件号[48435K72](http://www.mcmaster.com/#48435K72)。
 
输入侧有压力表和压力调节器，气囊侧有压力表，用于监控阀门关闭时的实际气囊压力。
 
{{< img src="images/Press_BladderInputConnector.JPG" caption="_press-to-bladder disconnect。_" >}} {{< img src="images/Press_UpperAirConnector.JPG" caption="_ Shop air-to-press disconnect。_" >}}输入端的快速连接与商店里的其他空气工具，所以标准的商店空气供应连接到压力机。从压力机框架到用于气囊的柔性软管也有类似的快速连接，以便在必要时移除气囊。这也直接挂在店内空气中，以防万一。

我发现如何焊接铜管的最佳指南是[焊接和钎焊铜管和配件](http://www.copper.org/publications/pub_list/pdf/soldering_brazing_ads.pdf)，直接来自the Copper Development Association, Inc.

## 气囊连接

人们在制造无泄漏气囊时通常会遇到很多麻烦。他们通常似乎最终会涉及许多“goop”，以阻止端部和直通接头处的泄漏。我的压力机中的气囊基本上只有Teflon胶带可以无泄漏到90psi。
 
使用7个3/8" 8级螺栓，使用Home Depot的标准1"角铁将两端固定在一起：两个在外端，一个在软管之间，两个穿过每个软管。他们非常舒服地扭转着，但我们并没有自杀它们。没有硅密封胶，水管工的粘液等，也没有泄漏。
 
直通联轴器更具挑战性。我们在完成您在下面看到的内容之前经历了一些测试。如果你仔细观察全尺寸图像，你会看到大部分周围都有一点肥皂水。这张照片拍摄的是90psi的气囊。再一次，没有goop。这里的秘密是三种垫圈的组合，以及面板安装联接器的螺母位于气囊外侧的简单事实。在内部重复垫圈配置。1/8"厚的橡胶垫圈抵靠气囊，然后是钢，然后是钢和黄铜螺母之间的芳纶/丁腈橡胶。结果是与气囊的密封很好，并且对螺母有很好的密封。这不是超紧密的...只是舒适，在组装过程中橡胶垫圈有一点变形。
 
家用电器仓库的标准3/4"垫圈是钢垫圈。以下是其他部件和McMaster-Carr部件号：

- Med-Pressure Extruded Brass Thrd Pipe Fitting 1/4″ Pipe Size, Panel Mount Coupling, [50785K273](http://www.mcmaster.com/#50785K273)
- 3/4″ Screw Size, 2″ Od, 1/8″ Thick Large-Od Extra-Thick Reinforced Rubber Washer (10), [90131A106](http://www.mcmaster.com/#90131A106)
- Aramid/Buna-N Washer 3/4″ Id, 1-1/2″ Od, .0625″ Thick (5), [93303A317](http://www.mcmaster.com/#93303A317)
 
这些部件并不是非常便宜，但它们完全值得。

{{< gallery  caption="气囊连接" >}}
{{< gallery-item src="images/Press_BladderConnections.JPG" caption="A view of the air connections to the two fire hoses on the Monkey Press." >}}
{{< gallery-item src="images/Press_BladderConnectionDetail.JPG" caption="A close up view of the way I supply air to my fire hose bladders on the Monkey Press." >}}
{{< /gallery >}}

## 层叠

用于模具表皮的所有铝都是0.032"(0.8128mm)5052-H32铝，我从西雅图的[Alaskan Copper & Brass Company](http://www.alaskancopper.com/)得到。从上到下我有以下内容： 

*顶部MDF模具和2×4填料。
*气囊
*1”x16”钢制悬置履带
*顶部加热组件
**一块铝皮
**顶部加热毯
**一块铝皮
*板组装
**铝制顶模皮
**滑雪板
**铝基模具皮
*底部加热组件
**一块铝皮
**底部加热毯
**一块铝皮
- MDF模具
 
这允许在湿法铺设之后将板容易地插入压力机中。
 
每个组件都用一个非常简单的系统固定在一起：在铝皮边缘附近钻两个孔，每边两个，两个铝板加热毯或层压板用小长度12awg(American wire gauge 直径2.05mm)铜线或拉链固定在一起。你可以看到这些在一些图片中戳出两侧。

## 履带悬架

{{< img src="images/Press_TrackSuspension.JPG" caption="_Monkey压力机上的履带悬架_" >}}履带悬架悬挂着简单的松紧绳，从McMaster-Carr散装购买。 [8858T21](http://www.mcmaster.com/#8858T21)，100英尺，红色。

## 设计缺陷

在这种设计中，工字梁的法兰用螺栓固定在一起，并置于张力下。这意味着梁的凸缘用于支撑由它们之间的气囊产生的载荷，这不是I梁的设计使用方式。在足够的压力下，凸缘可能会与腹板分离。然而，对于大型工字梁，这种设计已经证明在我和其他人的许多年，压力循环中都能很好地工作。 

然而，这是对设计的公平批评，我鼓励任何想要建立自己的压力机的人考虑这一点，并咨询工程师以验证你自己的压力机的设计。

有一些替代设计不会受到这个缺陷的影响，并且更适当地从外部支撑上梁和下梁，而不是从内部将它们保持在一起。 

## 参阅

- [压机温控箱和加热设备]({{< ref "MonkeyWiki/Equipment/Snowboard_press/Press_heat_control_and_thermocouples.md" >}})
