mikemag/MonkeyWiki/content/en/MonkeyWiki/Construction/Finishing/Finishing_a_wood_veneer_top_sheet.md

---
dateFromWiki: "2019-03-31T17:43:42Z"
title: "Finishing a wood veneer top sheet"
gallery: true
aliases:
- /MonkeyWiki/Finishing_a_wood_veneer_top_sheet
- /MonkeyWiki/Finishing_a_wood_veneer_top_sheet/en
---
One of the top sheet options we had available at Happy Monkey was a bird’s eye maple veneer. It looks beautiful, it’s reasonably durable (though less durable than an ABS top sheet), and it can be refinished over time if necessary. It is, however, a time consuming process to actually finish the top sheet nicely.
 
{{< img src="images/Veneer_Finishing1.JPG" caption="_Raw birds-eye maple veneer._" >}}The veneer we use is about 14” wide, 0.020” thick, and the full length of the board. As you can see in the pictures here, the raw wood is very light in color, and the grain is mostly subtle. The final result is quite a bit different, though, even though we don’t stain the wood at all. It turns out the combination of the epoxy, which is pretty clear, and the heat of the press (175F) cause the wood to darken substantially.
 
The veneer is coated lightly with epoxy on the top during lamination. Epoxy also permeates the wood during pressing, creating a durable top sheet. The first time I used veneer I found that epoxy seeps through it no matter what, and adding a bit of epoxy to the top ensures that there is even coverage.
 
Right out of the press you can see the wood looks very different where the epoxy is. The top sheet looks quite nice, and is pretty smooth with a satin finish. However, there are always minor imperfections in the surface of the epoxy out of the press, and the epoxy needs protection from UV light or it will break down eventually out in the sun.
 
So I coat these veneer top sheets with anywhere from 6 to 8 coats of Clear Satin System Three WR-LPU Polyurethane Topcoat. This is an extremely durable polyurethane that bring out the beauty of the wood while remaining flexible at extremely cold temperatures once cured. It also protects the wood and epoxy from UV light. I use the satin version of this finish rather than the glossy because I frankly just like the satin finish better. The gloss distracts from the wood. Another nice property of this finish is that its water-born, so cleanup is extremely easy and pretty non-toxic.
 
Before I can apply the first coat I have to sand the epoxy down to clean and roughen the surface. The top skin of the mold was waxed to ensure that the board would release from the mold, so I have to make sure to remove any wax residue as well. I sand with a random orbit sander using a 220 grit pad, stopping before I hit the wood. After a few light passes I stop and wash down the surface, then look carefully for any spots that could use a little more sanding love and scribble them with pencil. Then I sand those spots carefully just until the pencil marks disappear, then rinse and repeat until the top sheet is smooth and even.
 
{{< img src="images/Veneer_Finishing11.JPG" caption="_Finish and sprayer._" >}}Next the board is carefully cleaned to ensure there is no residual dust or grit from the sanding process, then it’s sprayed with the finish using a Fuji Q3 Pro HVLP sprayer. The finish is water based, and I cut the full-strength finish with about 20% distilled water. The shop is kept fairly dry for the benefit of the raw core wood, so I liberally spray the workbench with water and then set the freshly sprayed board on top of the damp surface to dry. The extra humidity slows the drying process by about 10 min or so and helps give the finish a chance to self-level a little better as it dries.
 
Even after the first coat the wood takes on a different character. It is still substantially the same color as it was fresh out of the press, but it has a smoothness and sheen to it that just can’t be beat. By the time the last coat is applied the wood has a bit of added “depth” that really brings out the character of the wood, especially on a cold sunny day up on the hill.
 
After the 3rd or 4th coat the top is sanded lightly with the random orbit sander again, this time with 320 grit. Any imperfections that the finish has picked up at this point, like a speck of dust or a bit of cat hair, are sanded out carefully by hand with 320 grit and water. I then screen on our logo and carefully hand paint on the serial number, and optionally the customer’s name if it’s a custom job. Then two or three more coats of finish, another light sanding with 320 grit, and one more final coat. The last coat is buffed lightly with fine bronze wool which maintains the satin finish while allowing me to remove any slight specs of dust that may have accidentally gotten on the last coat as it dried.
 
At this point the top sheet is finally finished. Polyurethane has coated the PTEX sidewalls, though it won’t actually stick to them for very long. I scrape that off carefully, and run a M6 tap down the inserts to remove any poly that has made it into the inserts, and the board is ready to go.

{{< gallery  caption="Veneer finishing" >}}
{{< gallery-item src="images/Veneer_Finishing1.JPG" caption="The raw bird’s eye maple veneer, unfinished. This is ~14” x 90” x 0.020”." >}}
{{< gallery-item src="images/Veneer_Finishing2.JPG" caption="Detail of the raw veneer. The grain is evident but not very pronounced at this stage." >}}
{{< gallery-item src="images/Veneer_Finishing3.JPG" caption="The veneer top sheet as it looks fresh out of the press." >}}
{{< gallery-item src="images/Veneer_Finishing4.JPG" caption="The top sheet as it looks fresh out of the press." >}}
{{< gallery-item src="images/Veneer_Finishing5.JPG" caption="Sanding the top sheet for the first time with 220 grit." >}}
{{< gallery-item src="images/Veneer_Finishing6.JPG" caption="Sanding the top sheet for the first time with 220 grit." >}}
{{< gallery-item src="images/Veneer_Finishing7.JPG" caption="Detail view of the first sanding. Here you can see variations in the surface finish due to the wood grain." >}}
{{< gallery-item src="images/Veneer_Finishing8.JPG" caption="Washed and marked for more sanding." >}}
{{< gallery-item src="images/Veneer_Finishing9.JPG" caption="Initial sanding complete and ready for the first coat of finish." >}}
{{< gallery-item src="images/Veneer_Finishing10.JPG" caption="Initial sanding complete and ready for the first coat of finish." >}}
{{< gallery-item src="images/Veneer_Finishing11.JPG" caption="The finish and spray gun." >}}
{{< gallery-item src="images/Veneer_Finishing12.JPG" caption="The first coat of finish drying on the board. Already the color is back." >}}
{{< gallery-item src="images/Veneer_Finishing13.JPG" caption="The first coat of finish drying on the board. Already the color is back." >}}
{{< gallery-item src="images/Veneer_Finishing14.JPG" caption="The first coat of finish dried. You can see the smoothness and the sheen of the satin finish already." >}}
{{< gallery-item src="images/Veneer_Finishing15.JPG" caption="The board has just been sanded very, very lightly with 320 grit for the last time, and is awaiting the final coat." >}}
{{< gallery-item src="images/Veneer_Finishing16.JPG" caption="The board has just been sanded very, very lightly with 320 grit for the last time, and is awaiting the final coat." >}}
{{< gallery-item src="images/Veneer_Finishing_2_1.jpg" caption="Veneer topsheet finished with satin poly." >}}
{{< gallery-item src="images/Veneer_Finishing_2_2.jpg" caption="Veneer topsheet in-progress, with finish and HVLP unit visible." >}}
{{< gallery-item src="images/Veneer_Finishing_2_3.jpg" caption="Veneer topsheet ready to be sprayed." >}}
{{< gallery-item src="images/Veneer_Finishing_2_4.jpg" caption="" >}}
{{< gallery-item src="images/Veneer_Finishing_2_5.jpg" caption="HVLP unit" >}}
{{< gallery-item src="images/Veneer_Finishing_2_6.jpg" caption="HVLP spray gun" >}}
{{< gallery-item src="images/Veneer_Finishing_2_7.jpg" caption="HVLP spray gun tip" >}}
{{< gallery-item src="images/Board_2018.jpg" caption="Completed board from Winter 2018. Wood veneer topsheet with highly figured Bubinga, English Sycamore, and Ebony. 164cm." >}}
{{< /gallery >}}

## Spraying Process 
{{< img src="images/Veneer_Finishing_2_3.jpg" caption="_Spray setup in my garage._" >}}I spray in my garage using the Fuji Q3 Pro HVLP sprayer mentioned above. The garage door is open a bit, and there's a beefy shop fan just outside the door behind a white furnace filter, sucking air to the outside. I'll hold the lamp in my left and and spray the board with my right hand, using the light to get a glare along the way to be sure I'm getting good coverage. The fan sucks out the overspray, and the scrap cardboard on the right is for testing the gun before each coat. I carefully pick up the board after a coat and lay it flat on my workbench. I dampen the workbench to slow the drying around the edges.
