mikemag/MonkeyWiki/content/en/MonkeyWiki/Construction/Preparation/Construction_Checklist.md

---
dateFromWiki: "2019-03-24T20:21:03Z"
title: "Construction Checklist"
gallery: true
aliases:
- /MonkeyWiki/Construction_Checklist
- /MonkeyWiki/Construction_Checklist/en
---
{{< img src="images/Checklist.jpg" caption="_Actual use of my checklist_" >}}
There are a lot of steps to building a snowboard, and it’s easy to forget some now and then especially when building multiple boards at once. There’s lots of things to do to prepare the materials, and lots of stuff to get ready for lamination. I keep track of exactly where I am in a build via a simple one-page spreadsheet. I print one of these for each build, and keep it with the board from core blank thru to finished product.

This includes things to be sure to do for core construction, wet layup, mold preparation, cleanup and finishing, etc.
 
[Snowboard Construction Checklist](https://docs.google.com/spreadsheets/d/1HrZ4bqN8kTH0_hd0w7_rP1COKkyS8-cpMqDffb0U5Pw/edit?usp=sharing)

To print: select "Fit to Page" for Scale, and under Formatting uncheck "Show gridlines".
