mikemag/MonkeyWiki/content/zh-cn/MonkeyWiki/Construction/Core_construction/_index.md

---
title: "板芯制造"
weight: 3
bookCollapseSection: true
---
