mikemag/MonkeyWiki/content/zh-cn/MonkeyWiki/Construction/Finishing/_index.md

---
title: "收尾"
weight: 6
bookCollapseSection: true
---
