mikemag/MonkeyWiki/content/zh-cn/MonkeyWiki/Construction/Laminate_preparation/_index.md

---
title: "层压板准备"
weight: 4
bookCollapseSection: true
---
