mikemag/MonkeyWiki/content/zh-cn/MonkeyWiki/Construction/Preparation/_index.md

---
title: "准备"
weight: 1
bookCollapseSection: true
---
