mikemag/MonkeyWiki/content/zh-cn/MonkeyWiki/Construction/Finishing/Finishing_a_wood_veneer_top_sheet.md

---
dateFromWiki: "2019-04-12T07:48:25Z"
title: "精加工木饰面板"
gallery: true
aliases:
- /MonkeyWiki/Finishing_a_wood_veneer_top_sheet/zh-cn
translatedDate: "2019-04-12T07:48:25Z"
translator: "X z"
translatorPage: "/zh-cn/MonkeyWiki/X_z"
---
我们在Happy Monkey提供的顶片选项之一是鸟眼枫木木皮。它看起来很漂亮，也相当耐用（虽然不如ABS顶片耐用），如果需要，它可以随着时间的推移进行修补。然而，实际完成顶片工作是一个耗时的过程。

{{< img src="images/Veneer_Finishing1.JPG" caption="_原始鸟眼枫木木皮_" >}}我们使用的木皮大约14英寸(35.56cm)宽，0.020英寸(0.508mm)厚，板的全长。正如你在这里的图片中看到的那样，原木的颜色非常浅，而且纹理基本上是细微的。尽管我们根本没有弄脏木头，但最终的结果还是有点不同。事实证明，环氧树脂的组合非常干净，而压力机的热量（175F）会使木材显着变暗。

在层压过程中，木皮在顶部涂有轻微的环氧树脂。在压制过程中，环氧树脂也会渗透到木材中，形成耐用的顶片。我第一次使用木皮时发现环氧树脂无论如何都会渗透它，并且在顶部添加一点环氧树脂可确保均匀覆盖。

在压力机外，你可以看到木材在环氧树脂的位置看起来非常不同。顶片看起来非常漂亮，并且非常光滑，带有缎面饰面。然而在压力机的环氧树脂表面总是存在微小的缺陷，并且环氧树脂需要防紫外线或者它最终会在阳光下分解。

所以我在这些木皮顶片上涂上6到8层Clear Satin System Three WR-LPU聚氨酯面漆。这是一种非常耐用的聚氨酯，可以带来木材的美感，同时在极冷的温度下保持柔韧性。它还可以保护木材和环氧树脂免受紫外线照射。我使用这种饰面的缎面版本而不是光面，因为我坦率地说就像缎面更好。光泽会分散木材的注意力。这种饰面的另一个不错的特性是它的水分，所以清理非常容易且非常无毒。
 
在我可以涂上第一层涂料之前，我必须将环氧树脂打磨下来以清洁和粗糙表面。将模具的顶部表皮打蜡以确保板从模具中脱出，因此我必须确保除去任何蜡残留物。我用一个盘式轨道砂光机使用220目砂纸打磨，在我撞到木头之前停下来。经过几道光线后，我停下来冲洗表面，然后仔细查看任何可以使用更多打磨爱的斑点并用铅笔涂抹它们。然后我仔细地打磨那些斑点直到铅笔痕迹消失，然后冲洗并重复直到顶片光滑均匀。

{{< img src="images/Veneer_Finishing11.JPG" caption="_Finish and sprayer._" >}}接下来仔细清洁滑雪板，确保打磨过程中没有残留的灰尘或砂砾，然后使用Fuji Q3 Pro HVLP喷涂机对其进行喷涂。表面处理是水基，我用约20％的蒸馏水切割全强度表面。为了生核心木材的利益，工厂保持相当干燥，因此我不得不用水喷洒工作台，然后将新喷涂的板放在潮湿的表面上进行干燥。额外的湿度使干燥过程减慢约10分钟左右，并且有助于使涂层在干燥时有更好的自我调整水平。
 
即使在第一次涂层之后，木材也呈现出不同的特征。它仍然与压力机中的新鲜颜色基本相同，但它具有光滑度和光泽，无法击败。当最后一层涂层被施加时，木材有一点额外的“深度”，真正展现了木材的特性，特别是在山上寒冷的阳光灿烂的日子。

在第3或第4层涂层后，顶部用盘式轨道砂光机轻轻打磨，这次使用320目砂纸。此时饰面所沾染的任何瑕疵，如一团灰尘或一点点猫毛，都要用320目砂砾和水仔细打磨。然后，我在我们的徽标上进行筛选，并仔细地在序列号上进行手工绘制，如果是自定义作业，还可以选择客户名称。然后再涂两三层，另外还有320目砂光，还有一层最终涂层。最后一层涂层用精细的青铜色羊毛轻轻打磨，保持了缎面光洁度，同时允许我去除任何可能在最后一层涂层干燥时偶然得到的轻微灰尘。
 
此时，顶片最终完成。聚氨酯涂有PTEX边墙，但它实际上不会长时间粘在它们上面。我小心翼翼地刮掉它，然后沿着插件向下移动M6，以移除任何堵住螺孔的聚合物，并且滑雪板已准备就绪。

{{< gallery  caption="木皮精加工" >}}
{{< gallery-item src="images/Veneer_Finishing1.JPG" caption="The raw bird’s eye maple veneer, unfinished. This is ~14” x 90” x 0.020”." >}}
{{< gallery-item src="images/Veneer_Finishing2.JPG" caption="Detail of the raw veneer. The grain is evident but not very pronounced at this stage." >}}
{{< gallery-item src="images/Veneer_Finishing3.JPG" caption="The veneer top sheet as it looks fresh out of the press." >}}
{{< gallery-item src="images/Veneer_Finishing4.JPG" caption="The top sheet as it looks fresh out of the press." >}}
{{< gallery-item src="images/Veneer_Finishing5.JPG" caption="Sanding the top sheet for the first time with 220 grit." >}}
{{< gallery-item src="images/Veneer_Finishing6.JPG" caption="Sanding the top sheet for the first time with 220 grit." >}}
{{< gallery-item src="images/Veneer_Finishing7.JPG" caption="Detail view of the first sanding. Here you can see variations in the surface finish due to the wood grain." >}}
{{< gallery-item src="images/Veneer_Finishing8.JPG" caption="Washed and marked for more sanding." >}}
{{< gallery-item src="images/Veneer_Finishing9.JPG" caption="Initial sanding complete and ready for the first coat of finish." >}}
{{< gallery-item src="images/Veneer_Finishing10.JPG" caption="Initial sanding complete and ready for the first coat of finish." >}}
{{< gallery-item src="images/Veneer_Finishing11.JPG" caption="The finish and spray gun." >}}
{{< gallery-item src="images/Veneer_Finishing12.JPG" caption="The first coat of finish drying on the board. Already the color is back." >}}
{{< gallery-item src="images/Veneer_Finishing13.JPG" caption="The first coat of finish drying on the board. Already the color is back." >}}
{{< gallery-item src="images/Veneer_Finishing14.JPG" caption="The first coat of finish dried. You can see the smoothness and the sheen of the satin finish already." >}}
{{< gallery-item src="images/Veneer_Finishing15.JPG" caption="The board has just been sanded very, very lightly with 320 grit for the last time, and is awaiting the final coat." >}}
{{< gallery-item src="images/Veneer_Finishing16.JPG" caption="The board has just been sanded very, very lightly with 320 grit for the last time, and is awaiting the final coat." >}}
{{< gallery-item src="images/Veneer_Finishing_2_1.jpg" caption="Veneer topsheet finished with satin poly." >}}
{{< gallery-item src="images/Veneer_Finishing_2_2.jpg" caption="Veneer topsheet in-progress, with finish and HVLP unit visible." >}}
{{< gallery-item src="images/Veneer_Finishing_2_3.jpg" caption="Veneer topsheet ready to be sprayed." >}}
{{< gallery-item src="images/Veneer_Finishing_2_4.jpg" caption="" >}}
{{< gallery-item src="images/Veneer_Finishing_2_5.jpg" caption="HVLP unit" >}}
{{< gallery-item src="images/Veneer_Finishing_2_6.jpg" caption="HVLP spray gun" >}}
{{< gallery-item src="images/Veneer_Finishing_2_7.jpg" caption="HVLP spray gun tip" >}}
{{< gallery-item src="images/Board_2018.jpg" caption="Completed board from Winter 2018. Wood veneer topsheet with highly figured Bubinga, English Sycamore, and Ebony. 164cm." >}}
{{< /gallery >}}

## 喷涂工艺

{{< img src="images/Veneer_Finishing_2_3.jpg" caption="_Spray setup in my garage._" >}}我使用上面提到的Fuji Q3 Pro HVLP喷雾器在车库里喷水。车库门开了一点，在白色炉子后面的门外面有一个坚固的商店风扇，吸入空气到外面。我会把灯放在左边，然后用右手喷开滑雪板，用灯照亮一路，以确保我得到很好的覆盖。风扇吸出过量喷涂，右边的废纸板用于在每个涂层之前测试喷枪。我穿上大衣后小心地拿起板子，把它平放在我的工作台上。我弄湿工作台以减缓边缘周围的干燥。
