mikemag/MonkeyWiki/content/zh-cn/MonkeyWiki/Construction/Preparation/Construction_Checklist.md

---
dateFromWiki: "2019-04-17T08:53:54Z"
title: "施工清单"
gallery: true
aliases:
- /MonkeyWiki/Construction_Checklist/zh-cn
translatedDate: "2019-04-17T08:53:54Z"
translator: "X z"
translatorPage: "/zh-cn/MonkeyWiki/X_z"
---
{{< img src="images/Checklist.jpg" caption="_实际我使用的清单_" >}}
建造滑雪板有很多步骤，偶尔会忘记一些步骤，特别是在一次建造多块滑雪板时候。准备材料有很多事情要做，还有很多东西要做好层压准备。我通过一个简单的电子表格跟踪在制造过程中的确切位置。我为每次建造打印其中一份，并将其与从木芯坯料到成品滑雪板一起保存。

这包括板芯制造，湿法铺层，模具准备，清理和精加工等方面必须要做的事情。

[滑雪板建造检查表](https://docs.qq.com/sheet/DYkxFZ2lqQWd6d1h0)

要打印：选择“适合页面”进行缩放，在格式化下取消选中“显示网格线”。
