mikemag/MonkeyWiki/assets/images/Bandsaw_Setup2.JPG

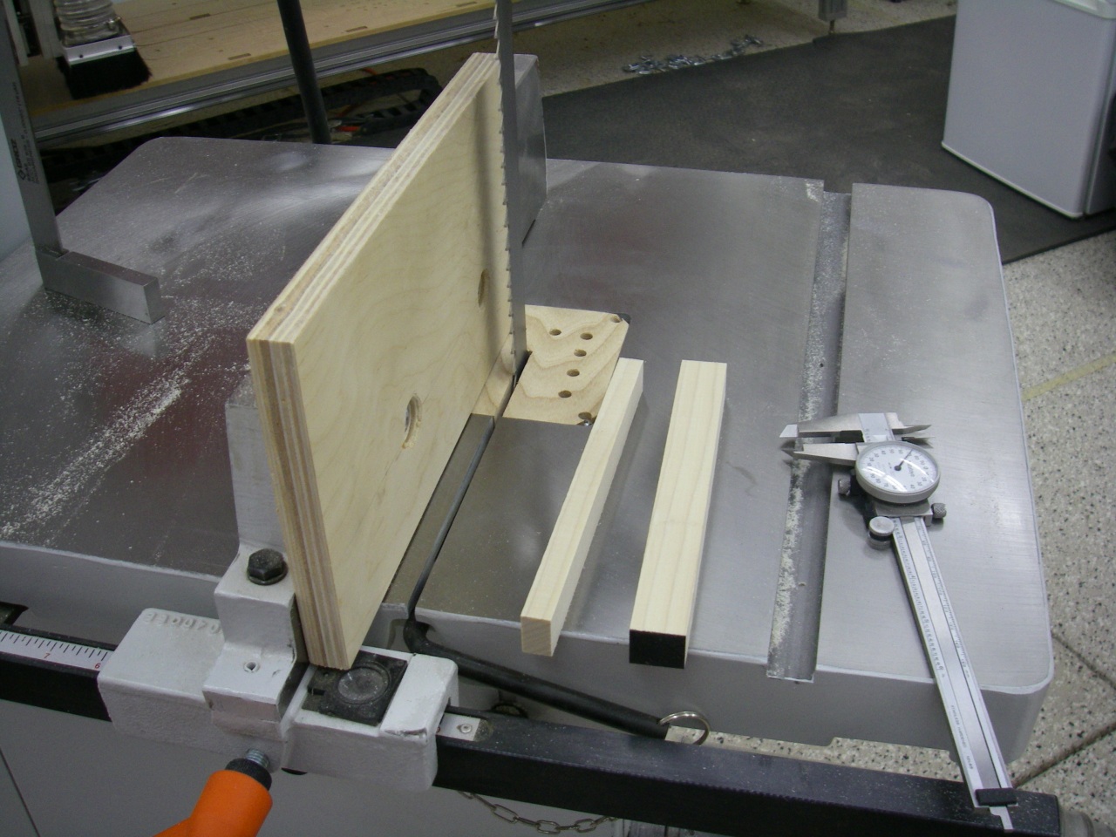
assets/images/Bandsaw_Setup2.JPG
