mikemag/MonkeyWiki/content/en/MonkeyWiki/Equipment/Snowboard-specific_tools/Deflection_Testing_Jig.md

---
dateFromWiki: "2019-03-24T20:35:30Z"
title: "Deflection Testing Jig"
gallery: true
aliases:
- /MonkeyWiki/Deflection_Testing_Jig
- /MonkeyWiki/Deflection_Testing_Jig/en
---
One of the things I like to measure (aside from 
the [various weights]({{< ref "MonkeyWiki/Construction/Measurement_and_testing/Weights_and_fiber_fraction.md" >}}))
is how much each board deflects given a fixed weight at the center. I've made a simple jig for doing that, with bars I can 
place to support the board at the ends of the effective edge. I use a 25lb weight (because that's what I had lying around when 
I first did this), and a dial indicator suspended over the center of the effective edge. It's been interesting to see how well 
(or not) this correlates to core thickness, length, width, different weights of glass, and how it changes (or not) with days on the hill.

Note that this is a static deflection test with a single weight. It is not by any stretch a comprehensive measurement of the 
boards flexural properties. Consider this a small start.

{{< gallery  caption="Static Deflection Test Jig" >}}
{{< gallery-item src="images/Deflection_Jig_1.jpg" caption="Board on deflection test jig w/ 25lb weight." >}}
{{< gallery-item src="images/Deflection_Jig_2.jpg" caption="Board on deflection test jig w/ 25lb weight, showing deflection in inches." >}}
{{< gallery-item src="images/Deflection_Jig_3.jpg" caption="Deflection jig showing options for placing support bar based on effective edge length." >}}
{{< gallery-item src="images/Deflection_Jig_4.jpg" caption="Deflection jig showing attachment of dial indicator." >}}
{{< gallery-item src="images/Deflection_Jig_5.jpg" caption="Deflection jig showing mounting of dial indicator." >}}
{{< gallery-item src="images/Deflection_Jig_6.jpg" caption="Deflection jig packed away for storage." >}}
{{< /gallery >}}
