mikemag/MonkeyWiki/content/zh-cn/MonkeyWiki/Equipment/Snowboard-specific_tools/Deflection_Testing_Jig.md

---
dateFromWiki: "2019-04-03T13:30:27Z"
title: "挠度测试夹具"
gallery: true
aliases:
- /MonkeyWiki/Deflection_Testing_Jig/zh-cn
translatedDate: "2019-04-03T13:30:27Z"
translator: "X z"
translatorPage: "/zh-cn/MonkeyWiki/X_z"
---
我喜欢测量的一件事（除了[各种重量]({{< ref "MonkeyWiki/Construction/Measurement_and_testing/Weights_and_fiber_fraction.md" >}}))
是每个板在中心固定重量时偏转了多少。我做了一个简单的夹具，我可以放置条形以支撑有效边缘末端的板。我使用25磅的重量（因为这是我第一次做的时候我躺在那里），并且一个表盘悬挂在有效边缘的中心上方。有趣的是，这与（或不是）这与板芯厚度，长度，宽度，不同玻璃重量以及它在山上的天数如何变化（或不变化）有关。

请注意，这是一个单一重量的静态挠度测试。它无论如何都不能全面测量板材的弯曲性能。考虑这是一个小小的开始。

{{< gallery  caption="静态挠度测试夹具" >}}
{{< gallery-item src="images/Deflection_Jig_1.jpg" caption="Board on deflection test jig w/ 25lb weight." >}}
{{< gallery-item src="images/Deflection_Jig_2.jpg" caption="Board on deflection test jig w/ 25lb weight, showing deflection in inches." >}}
{{< gallery-item src="images/Deflection_Jig_3.jpg" caption="Deflection jig showing options for placing support bar based on effective edge length." >}}
{{< gallery-item src="images/Deflection_Jig_4.jpg" caption="Deflection jig showing attachment of dial indicator." >}}
{{< gallery-item src="images/Deflection_Jig_5.jpg" caption="Deflection jig showing mounting of dial indicator." >}}
{{< gallery-item src="images/Deflection_Jig_6.jpg" caption="Deflection jig packed away for storage." >}}
{{< /gallery >}}
