mikemag/MonkeyWiki/content/zh-cn/MonkeyWiki/Construction/Measurement_and_testing/_index.md

---
title: "测量和测试"
weight: 7
bookCollapseSection: true
---
