mikemag/MonkeyWiki/assets/images/Shaper_Test_2.jpg

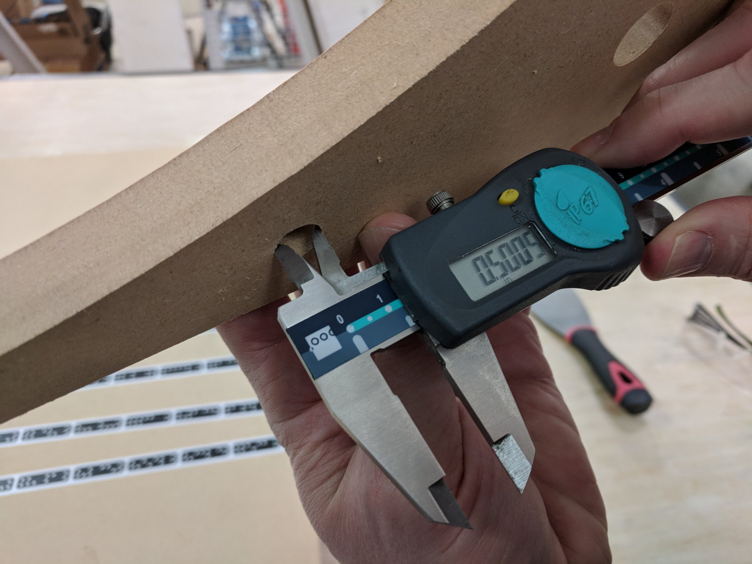
assets/images/Shaper_Test_2.jpg
